akkoyun/B100/[AA]/Design Review/Telit/README.md

# B100<sup>AA</sup> Design Review

B100 is an open source (open hardware) GSM IoT module. B100 use Telit GE910 GSM modem in communication layer. All hardware is reviewed by manufacturer such as Telit. In this folder all review version files and design review reports are published.

## Review Time Line

**Telit**

| Review Date | Review Version | Review Link |
|---|---|---|
| 11.01.2021  | Schematic R1 | [Telit DR33285 R1](https://github.com/akkoyun/B100/blob/01.00.00/%5BAA%5D/Design%20Review/Telit/Review%201/Design%20Review/DR33285%20v1.pdf) |
| 18.01.2021  | Schematic R2 | [Telit DR33285 R2](https://github.com/akkoyun/B100/blob/01.00.00/%5BAA%5D/Design%20Review/Telit/Review%202/Design%20Review/DR33285%20v2.pdf) |
| 21.01.2021  | Schematic R3 | [Telit DR33285 R3](https://github.com/akkoyun/B100/blob/01.00.00/%5BAA%5D/Design%20Review/Telit/Review%203/Design%20Review/DR33285%20v3.pdf) |
| 28.01.2021  | Schematic R4 | [Telit DR33285 R4](https://github.com/akkoyun/B100/blob/01.00.00/%5BAA%5D/Design%20Review/Telit/Review%204/Design%20Review/DR33285%20v4.pdf) |
| 01.02.2021  | PCB R1 | [Telit DR33285 R5](https://github.com/akkoyun/B100/blob/01.00.00/%5BAA%5D/Design%20Review/Telit/Review%205/Design%20Review/DR33285%20v5.pdf) |
| 11.02.2021  | PCB R2 | [Telit DR33285 R6](https://github.com/akkoyun/B100/blob/01.00.00/%5BAA%5D/Design%20Review/Telit/Review%206/Design%20Review/DR33285%20v6.pdf) |
| | PCB R3 | Telit DR33285 R7 |
