akkoyun/B100/[AA]/Documentation/MCU Pin Map/README.md

# B100<sup>AA</sup> Socket Pin Map

## Power

### VCC

Pin number : A1, A60, B1, B60

Pin description : VCC power line is a main feed for B100AA
