akkoyun/B100/[AA]/Production/Mechanical/2D/README.md

# B100<sup>AA</sup>

* Çift yönlü komponent yerleşimi olacaktır.
* Low profile çift satır headerlar ile pin aktarımı yapılacaktır.
* köşelerde delikleri olacaktır.
*
