akkoyun/B100/[AA]/Design Review/Telit/Review 3/Design Review/DR33285 v3.pdf

Application Engineering

Design review report

Code: | AE-33285
Rev: | 3
Date: | 2021-01-21
Page: | 1/ 8

The electronic version of this document is the latest version. It is the responsibility of the individual to ensure that any paper material is the current version. Printed material is uncontrolled documentation

Documentazione riservata. Questo documento non può essere riprodotto, anche

parzialmente, né reso noto a terzi senza preventiva autorizzazione scritta diTelit Communications S.p.A.

Tutti i diritti sono tutelati a norma di legge.

Mod. 0313 08/2015 Rev.4

Approval: | Global Application Engineering Manager Massimiliano Lonzar
Approval: | Design Services Manager Fabio Deperini, Prashanth Reddy
Author: | Technical Support Engineer Alessandro Littarru, Chandra Shekar N, Harinadha Reddy C

DISCLAIMER

The contents are confidential and any disclosure to persons other than the officers, employees, agents or subcontractors of the owner or licensee of this document, without the prior written consent of Telit, is strictly prohibited. Telit makes every effort to ensure the quality of the information it makes available. Notwithstanding the foregoing, Telit does not make any warranty as to the information contained herein, and does not accept any liability for any injury, loss or damage of any kind incurred by use of or reliance upon the information. Telit disclaims any and all responsibility for the application of the devices characterized in this document, and notes that the application of the device must comply with the safety standards of the applicable country, and where applicable, with the relevant wiring rules.

All rights reserved.
© 2006-2021 Telit Communications S.p.A.

Restricted document. No part of this document can be reproduced or copied in any format, in part or totally,

nor its contents revealed in any manner to others without the express written permission of Telit Communications S.p.A.

All rights reserved.

Design review report

Date: | 2021-01-21
Page: | 2/ 8

Documentazione riservata. Questo documento non può essere riprodotto, anche

parzialmente, né reso noto a terzi senza preventiva autorizzazione scritta diTelit Communications S.p.A.

Tutti i diritti sono tutelati a norma di legge.

Contents

Design review report

Date: | 2021-01-21
Page: | 3/ 8

Documentazione riservata. Questo documento non può essere riprodotto, anche

parzialmente, né reso noto a terzi senza preventiva autorizzazione scritta diTelit Communications S.p.A.

Tutti i diritti sono tutelati a norma di legge.

### 1. Scope

Aim of this document is to describe suggestions and corrections that Telit advises to improve Ovoo Electronics B100AA application that integrates Telit GE910-QUAD V3 and BlueMod S50 modules.

### 2. Design review

Design review is based on the following received documentation:
- Schematic files: B151BA-R2.PDF, B100AA-R3.PDF
- Gerber file: none.
- Other: Telit Design Review R03 (Schematic).PDF Summary Tables:
Schematic Review | P F I MI N/A
Power Supply | Ѵ
SIM Pins | Ѵ
Digital Pins | | Ѵ
Audio | | | | Ѵ
RF | | | Ѵ
PCB Layout Review | P F I MI N/A
General Placement | | Ѵ
Antenna Waveguide | | Ѵ
RF Aspects | | Ѵ
Audio Aspects | | Ѵ

P: Pass; F: Fail; I: Improvements possible; MI: Missing Information; N/A: Not Applicable

The following symbols will be used throughout the Design Review to indicate:

✓ OK: No design changes are required.

Tip: information or possible improvement, not mandatory but recommended.

Warning: if you don’t follow the recommendation there’s a risk of malfunctioning or issues during the homologation phase, strongly recommended.

Error: it’s mandatory to follow the recommendation otherwise the module could be damaged or could not work properly or there’s high probability of facing issues during the homologation phase.

? Missing Information: some relevant information is missing therefore the DR cannot be accurate on this item.

Design review report

Date: | 2021-01-21
Page: | 4/ 8

Documentazione riservata. Questo documento non può essere riprodotto, anche

parzialmente, né reso noto a terzi senza preventiva autorizzazione scritta diTelit Communications S.p.A.

Tutti i diritti sono tutelati a norma di legge.

### 2.1. Schematic review

2.1.1. Power supply

Ѵ Ok.

2.1.2. SIM pins

Ѵ Ok.

2.1.3. Digital pins

We strongly suggest replacing Q3 NPN transistor with a PNP transistor and tying its emitter to VMCU. Furthermore, resistors R25, R26, R27 must be properly sized considering current rating for D1 LEDs. Suitable values are 65Ohm for R25-R26 and 22 Ohm for R27. Add proper series resistor (5-10KOhm) on Q4, Q5 and Q6 bases.

Kindly make sure the BlueMod+S50 UART lines are connected to HOST MCU as shown below,

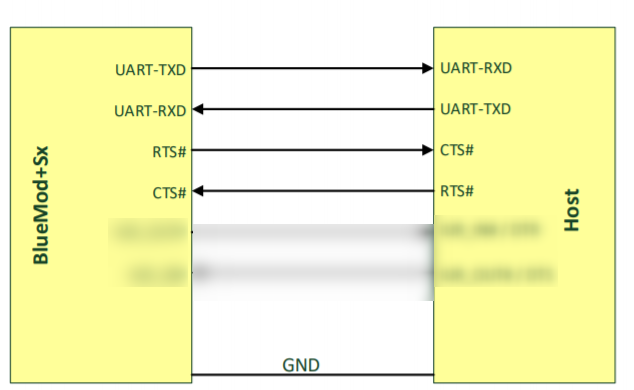
[picture p13: figure]

We recommend placing test points for BOOT0 pin, UART-RXD, UART-TXD, UART-RTS# and UART-CTS#. This will be useful for Regulatory approval purpose.

Test mode# Pin | BOOT0 Pin | Mode
LOW | LOW | Test mode (38400, 8N1)
LOW | HIGH | DTM (19200, 8N1)
HIGH | LOW | Firmware (115200, 8N1)
HIGH | HIGH | Bootloader

For more details on Test Mode, refer BlueMod+S50 HUG section 4.8.

Design review report

Date: | 2021-01-21
Page: | 5/ 8

Documentazione riservata. Questo documento non può essere riprodotto, anche

parzialmente, né reso noto a terzi senza preventiva autorizzazione scritta diTelit Communications S.p.A.

Tutti i diritti sono tutelati a norma di legge.

2.1.4. Audio pins
✓ N.A.
2.1.5. RF aspects

? Looks the current design is using BlueMod+S50_AP variant. Antenna part number is missing in the schematics.

### 2.2. PCB Layout review

We don’t have the PCB gerbers yet, but we will give you anyhow some useful general suggestions.

2.2.1. General placement

As a general rule we suggest predisposing your PCB to optionally mount a metallic shield on top of noisy components (fast digital components, MCU, memories). This is a must in case of switching components, rectifiers and power amplifiers. For this purpose, components must be packet into well-defined areas surrounded with ground pads where you can eventually solder the shield. The shield options can be used, when needed, to suppress EMI fields that may interfere with the cellular reception/emission.

Be aware that all PCBs placed close to GSM antenna must be RF proof and not only the PCB mounting the module; this means that all the PCB placed less than 30cm from the antenna must have shields over the noisiest components (switching, MCU, RAM, Ethernet PHY, etc..) and with the top and bottom layers mostly ground planes.

2.2.2. RF aspects

The position of the external antenna with respect to other boards is of maximum importance, since conductive planes close to antenna modify the impedance sees by the antenna and any board of the system must be RF proof, not only the modem board.

Move components, tracks, vias and connectors away from antenna area to reduce their coupling with RF signal; you can also bury tracks in the inner layers of a multi-layer PCB.

We strongly suggest complying the following build-up and routing general rules for best RF performances (high RF receiver sensitivity, low spurious emissions) and also for best thermal behavior:

o We advise using at least 4 layers PCB.

Design review report

Date: | 2021-01-21
Page: | 6/ 8

Documentazione riservata. Questo documento non può essere riprodotto, anche

parzialmente, né reso noto a terzi senza preventiva autorizzazione scritta diTelit Communications S.p.A.

Tutti i diritti sono tutelati a norma di legge.

o Top and Bottom layers should be mainly a ground plane interrupted just by component’s pads, VIAs and RF antenna waveguide; just the minimum possible portion of tracks should be routed in these layers.
o Inner layers should be used for interconnections and power planes; all empty spaces should be filled with GND.
o All grounds, either planes or areas, in an all layers, must be well connected with each other, using large tracks and many conductive VIAs, in order to guarantee a strong equipotential node.
o PCB borders should be GND in all layers, wherever is possible. We suggest adding a series of conductive VIAs evenly distributed (e.g. every 2mm) all along the board edges, inside the border GND area.
o Noisy components should be shielded into a metallic shield if required.

The Bypass capacitors must be placed close to the Telit modem’s power input pads or at least on the same path. In case of switching power supply another Bypass low ESR capacitor must be placed close to the inductor output to cut the ripple.

It is not advisable to route analog or digital audio lines, memory address and data bus, fast digital signals, clocks, quartz, serial, USB and long signal tracks on an outer layer. It’ll be better to bury it on an inner layer with a ground plane under and above it to shield the signal from RF and crosstalk, see figure below. USB data lines should be Differential Offset Coplanar Waveguide with 90 Ohms characteristic impedance.

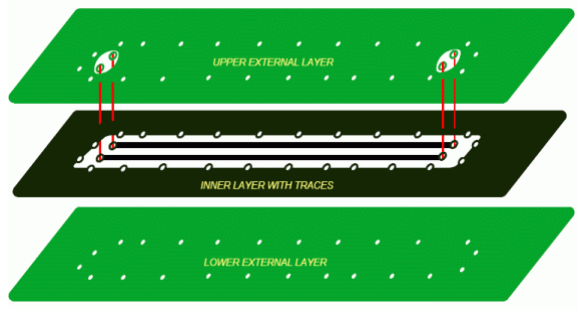
[picture p14: figure]

The RF antenna track, and eventually any via connected to it, must be a homogeneous waveguide with 50 Ohm characteristic impedance; we suggest using the coplanar waveguide with ground model where the RF track has a uniform ground plane underneath and surrounding it as in figure below. Do not place signal lines and signal-VIAs crossing or close to RF lines in no one of waveguide’s layers involved.

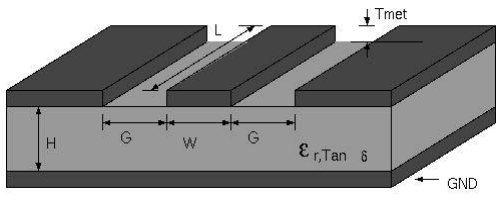
[picture p15: figure]

Design review report

Date: | 2021-01-21
Page: | 7/ 8

Documentazione riservata. Questo documento non può essere riprodotto, anche

parzialmente, né reso noto a terzi senza preventiva autorizzazione scritta diTelit Communications S.p.A.

Tutti i diritti sono tutelati a norma di legge.

When dielectric between 2 consecutive layers has not the desired height then for right impedance realization, you should remove the copper under RF line or pad, in one or more layers, to wider dielectric between antenna track and its reference ground plane, as example in figure below. The clearance in the internal layers must be wider than the W+2G. This is to avoid electric filed to close in internal layers instead of in the desired reference ground layer.

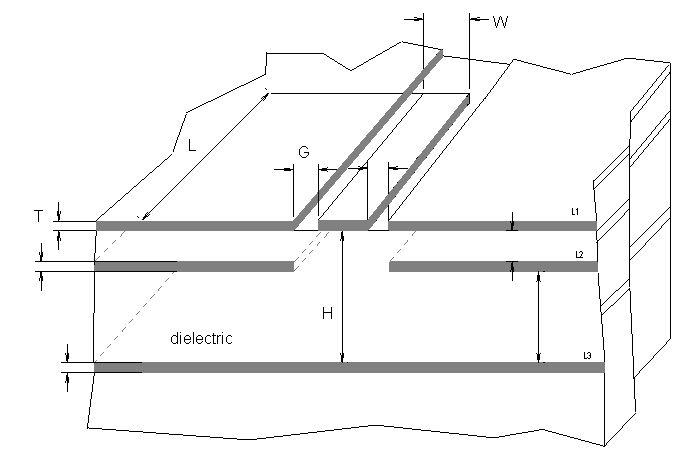
[picture p16: figure]

We suggest shielding the waveguide by adding a series of conductive VIAs evenly distributed (e.g. every 2mm) all along the edges of the GND plane facing the coplanar waveguide (about 1mm from the edge), both sides. (see figure below). This improve line grounding and reduce signal coupling inside the PCB from adjacent tracks.

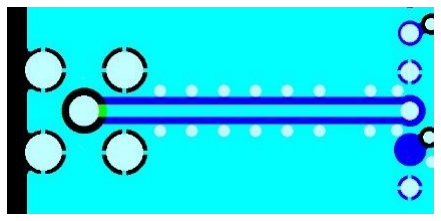
[picture p17: figure]

If applicable, route RF matching network using as short as possible tracks and avoiding stubs, sharp bends and meanders.
Figure below represents a layout example of the RF line matching network circuitry.

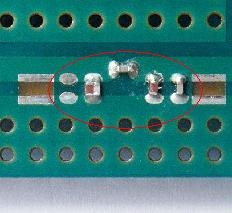
[picture p18: figure]

### 2.3. General comments

Please check and follow Telit Modem Integration Design Guide.
Review is related to received application information and the supposed use of it.

Design review report

Date: | 2021-01-21
Page: | 8/ 8

Documentazione riservata. Questo documento non può essere riprodotto, anche

parzialmente, né reso noto a terzi senza preventiva autorizzazione scritta diTelit Communications S.p.A.

Tutti i diritti sono tutelati a norma di legge.

### 3. Quality record

This design review is registered internally in Bugzilla with ID #33285.
The customer request is registered internally in Salesforce with ID # 00201737.
