akkoyun/B100/[AA]/Documentation/Block Diagram/PDF/FOTA.pdf

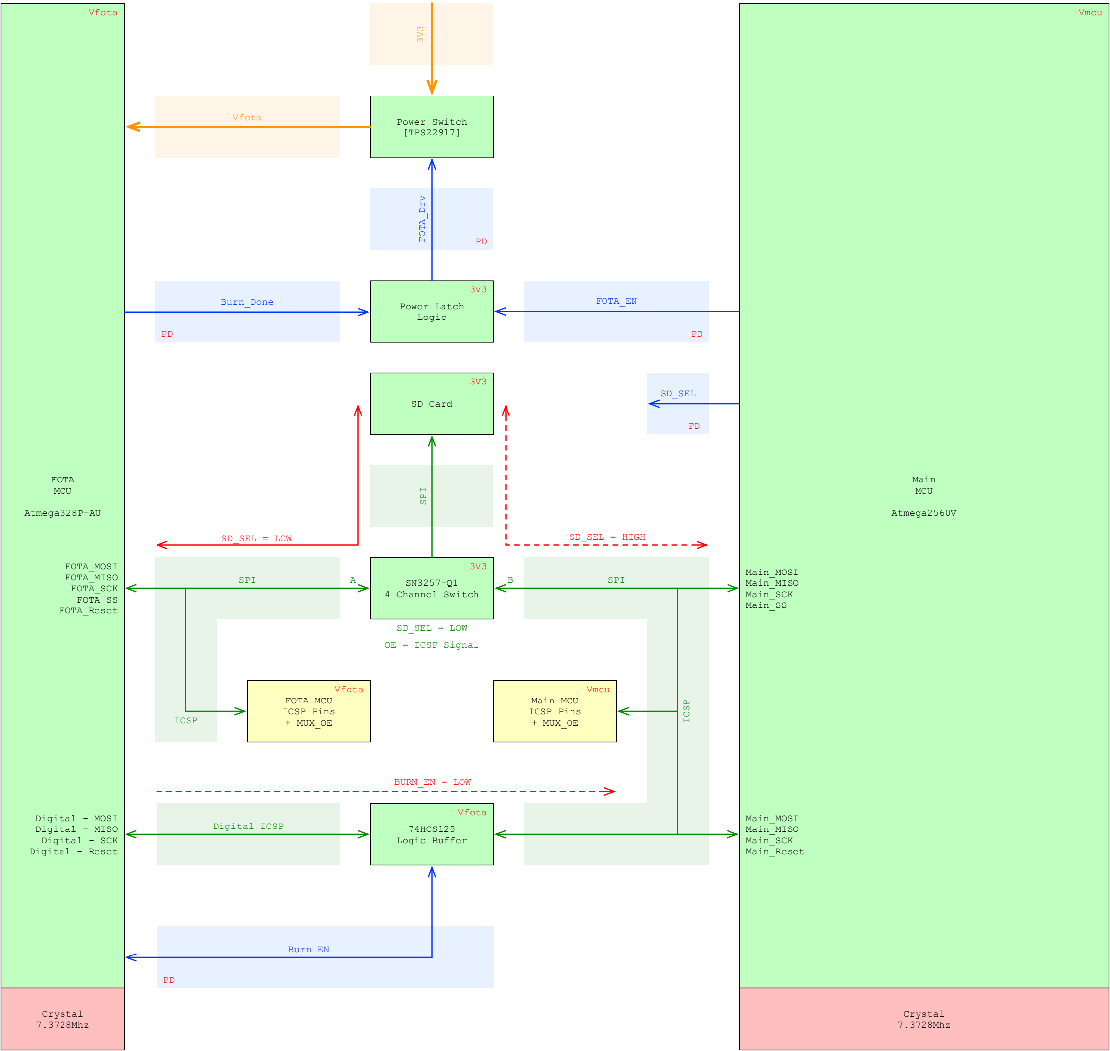
[picture p19: figure]
FOTA MCU; Atmega328P-AU; Crystal 7.3728Mhz; FOTA_EN Power Latch; Logic FOTA_Drv; SD Card; SPI; Main MCU ICSP Pins + MUX_OE; ICSP; FOTA MCU ICSP Pins; + MUX_OE; 74HCS125 Logic Buffer; Digital ICSP; Burn EN; Burn_Done; Power Switch [TPS22917]; Vfota; Main MCU; Atmega2560V; 4 Channel Switch SPI; SD_SEL = LOW; OE = ICSP Signal; SD_SEL; SD_SEL = HIGH; BURN_EN = LOW; Main_MOSI Main_MISO Main_SCK Main_SS; Main_MOSI Main_MISO Main_SCK Main_Reset; Digital - MOSI Digital - MISO Digital - SCK Digital - Reset; FOTA_MOSI FOTA_MISO FOTA_SCK FOTA_SS FOTA_Reset; Vmcu
