akkoyun/B100/[AA]/Documentation/Block Diagram/PDF/GSM.pdf

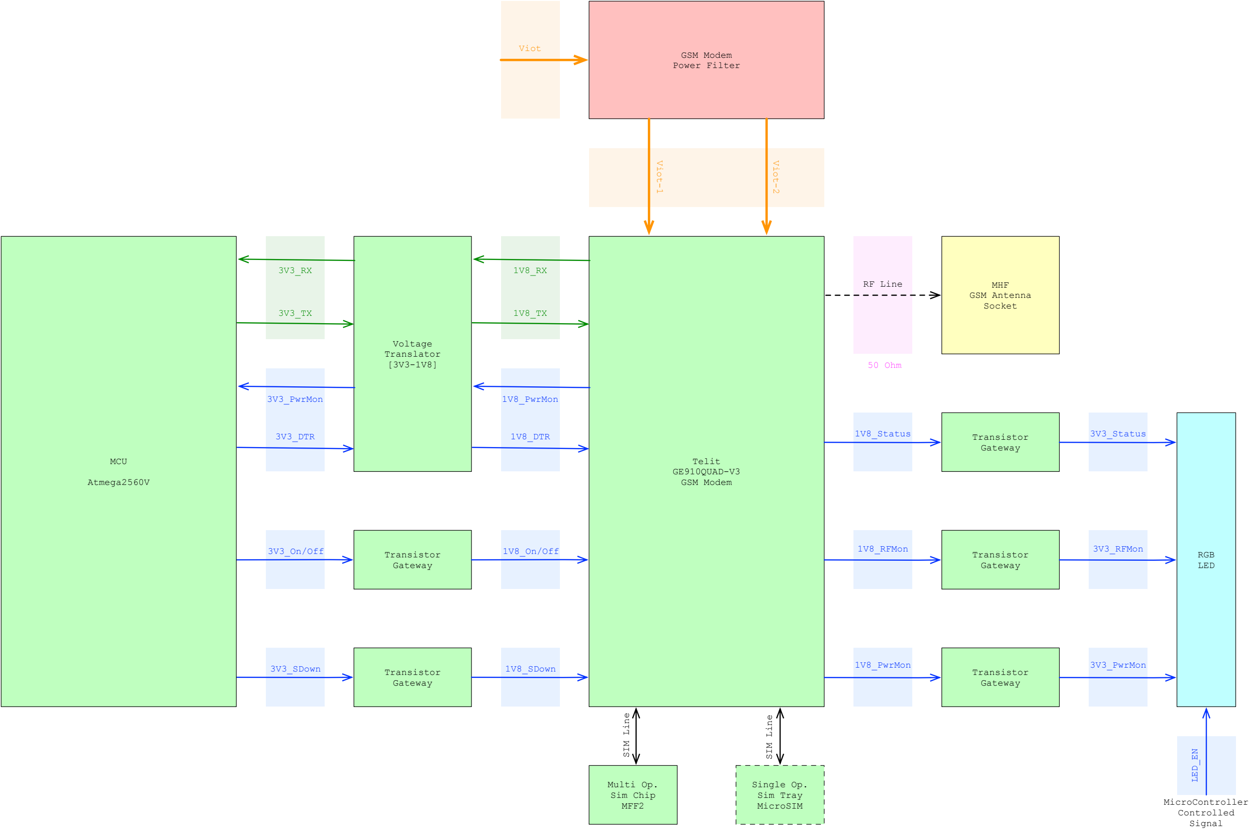
[picture p20: figure]
Telit GE910QUAD-V3 GSM Modem; MHF GSM Antenna Socket; RF Line; 50 Ohm; Multi Op. Sim Chip MFF2; Transistor Gateway; Voltage Translator [3V3-1V8]; Single Op. Sim Tray MicroSIM; SIM Line; 3V3_SDown; 3V3_On/Off; 3V3_DTR; 3V3_PwrMon; 1V8_SDown; 1V8_On/Off; 1V8_DTR; 1V8_PwrMon; GSM Modem Power Filter; Viot-1; Viot-2; MCU; Atmega2560V; 1V8_Status; 1V8_RFMon; RGB; LED; 3V3_Status; 3V3_RFMon; LED_EN; Viot; MicroController Controlled Signal
