akkoyun/B100/[AA]/Documentation/Block Diagram/PDF/I2C.pdf

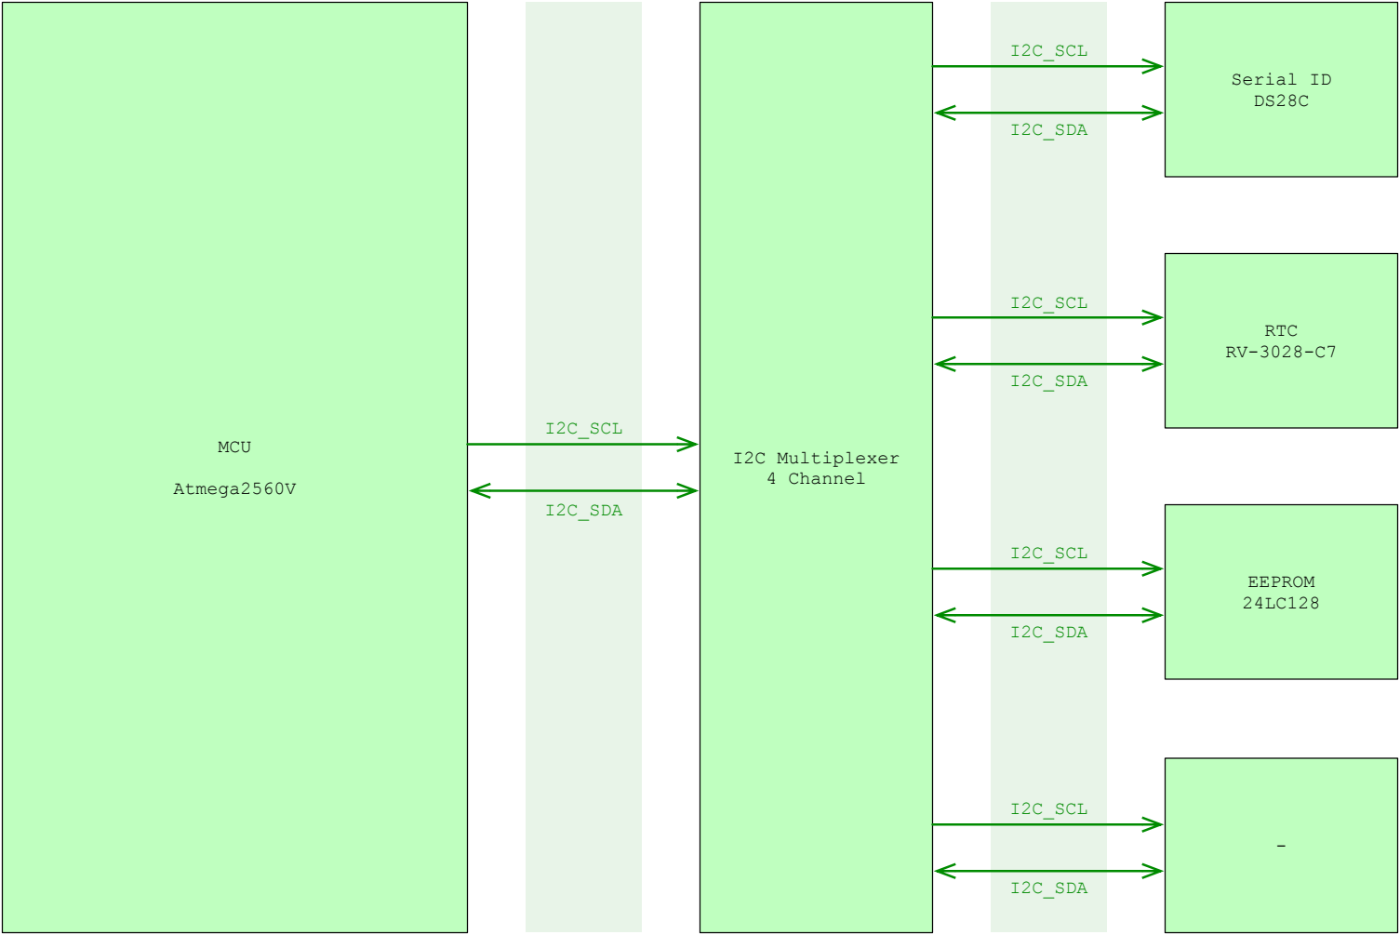
[picture p21: figure]
MCU; Atmega2560V; I2C Multiplexer 4 Channel; I2C_SCL; I2C_SDA; Serial ID DS28C; EEPROM 24LC128; RTC RV-3028-C7
