akkoyun/B100/[AA]/Documentation/Block Diagram/PDF/Power Architechture.pdf

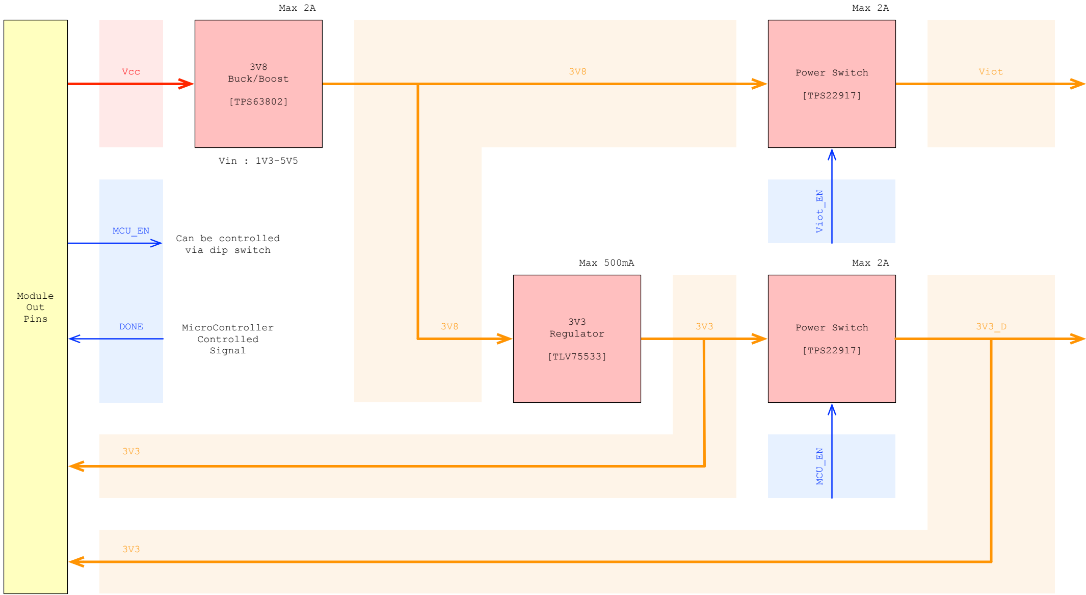
[picture p22: figure]
Viot; Viot_EN; Power Switch; [TPS22917]; Max 2A; MCU_EN; DONE; MicroController; Controlled Signal; Can be controlled; via dip switch; 3V3 Regulator; [TLV75533]; Max 500mA; Vcc; Buck/Boost; [TPS63802]; Vin : 1V3-5V5; Module Out Pins

Main Feed

Non Sleep
3V3

Sleep

Sleep
3V3

Awake
