akkoyun/B100/[AA]/Design Files/B100AA/PDNAnalyzer_Output/B100AA PCB R1/B100AA R4/Results-1/pins.csv

refdes | pin | voltage | current
J2 | 60 | 4.99608 | 1.96035
J2 | 1 | 4.99608 | 1.96035
J2 | 30 | 0.0 | -0.980174
J2 | 58 | 0.0 | -0.980174
J2 | 4 | 0.0 | -0.980174
J2 | 31 | 0.0 | -0.980174
J3 | 60 | 5.00105 | 0.0498376
J3 | 1 | 5.00105 | 0.0498376
J3 | 30 | 0.00114728 | -0.0249188
J3 | 58 | 0.00114728 | -0.0249188
J3 | 4 | 0.00114728 | -0.0249188
J3 | 31 | 0.00114728 | -0.0249188
U3 | 5 | 3.30041 | 0.570263
U3 | 2 | 0.000984424 | 0.018311999999999995
U21 | 6 | 3.80631 | 0.838579
U21 | 8 | 0.00533345 | 1.5902399999999999
U21 | 3 | 0.00533345 | 1.5902399999999999
U22 | 6 | 5.00037 | 0.00118532
U22 | 8 | 0.00093399 | 6.681600000000003e-05
U22 | 3 | 0.00093399 | 6.681600000000003e-05
U4 | M01 | 3.68575 | -0.0625243
U4 | M02 | 3.6856 | -0.0624757
U4 | R02 | 0.00120282 | 0.006576820000000001
U4 | R04 | 0.00120904 | 0.00657371
U4 | R03 | 0.00120689 | 0.00657478
U4 | P03 | 0.00120897 | 0.00657374
U4 | P04 | 0.0012106 | 0.0065729199999999995
U4 | N03 | 0.00120922 | 0.0065736200000000005
U4 | R05 | 0.00120848 | 0.00657398
U4 | R06 | 0.00120578 | 0.006575340000000001
U4 | P05 | 0.00120975 | 0.00657335
U4 | R08 | 0.00119816 | 0.0065791700000000005
U4 | N05 | 0.00120839 | 0.00657403
U4 | P06 | 0.00120632 | 0.006575070000000001
U4 | N04 | 0.00121003 | 0.0065732099999999995
U4 | N06 | 0.00120453 | 0.00657597
U4 | L01 | 0.00119847 | 0.006579
U4 | L02 | 0.00120268 | 0.0065769
U4 | J01 | 0.00119821 | 0.006579140000000001
U4 | K02 | 0.00120285 | 0.006576810000000001
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
R70 | 1 | 0.00105438 | 4.65955e-06
U1 | 1 | 3.72176 | -0.25
U1 | 6 | 3.69676 | 0.25
FB1 | 1 | 3.69548 | -0.125
FB1 | 2 | 3.68986 | 0.125
FB2 | 1 | 3.69559 | -0.125
FB2 | 2 | 3.68997 | 0.125
U2 | 1 | 3.28963 | -0.570163
U2 | 6 | 3.20981 | 0.570163
U10 | 1 | 3.16295 | -0.0790108
U10 | 6 | 3.15188 | 0.0790108
