akkoyun/B100/[AA]/Design Files/B100AA Development Kit/Output/BOM/B100DEV BOM.numbers/Data/Bottom-small-36.png

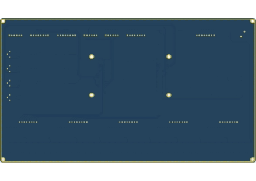
[AA]/Design Files/B100AA Development Kit/Output/BOM/B100DEV BOM.numbers/Data/Bottom-small-36.png
