akkoyun/B100/[AA]/Design Files/B100AA Development Kit/Output/BOM/B100DEV BOM.numbers/Data/Ekran Resmi 2021-02-23 10.48.27-31.png

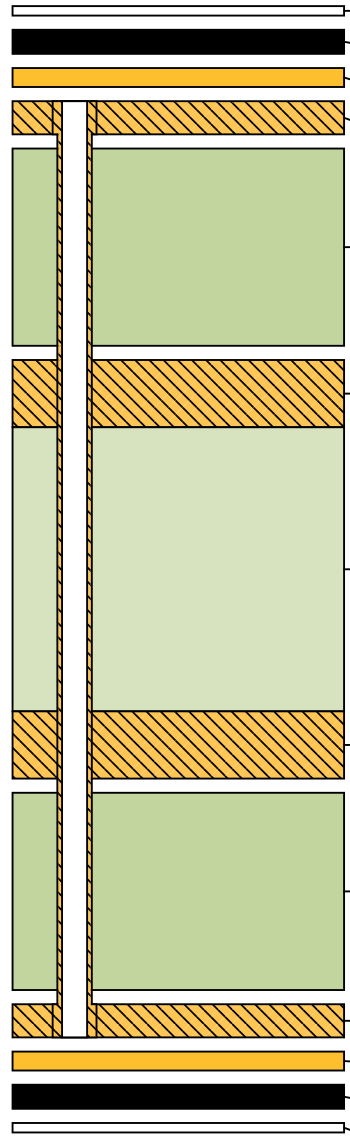
[AA]/Design Files/B100AA Development Kit/Output/BOM/B100DEV BOM.numbers/Data/Ekran Resmi 2021-02-23 10.48.27-31.png
