akkoyun/B100/[AA]/Design Files/B100AA Development Kit/Output/BOM/B100DEV BOM.numbers/Data/Top-small-34.png

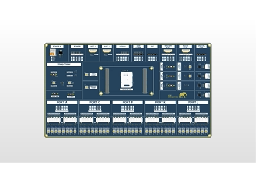
[AA]/Design Files/B100AA Development Kit/Output/BOM/B100DEV BOM.numbers/Data/Top-small-34.png
