akkoyun/B100/[AA]/Design Files/B100AA Development Kit/Output/BOM/B100DEV BOM.numbers/Data/Twitter_Profile-15.jpg

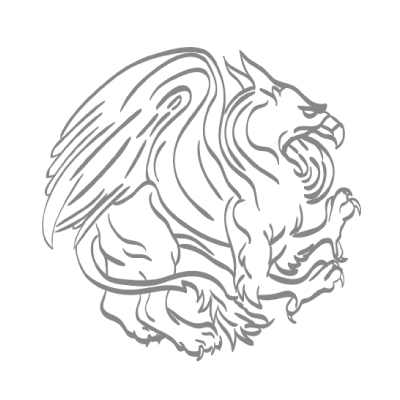
[AA]/Design Files/B100AA Development Kit/Output/BOM/B100DEV BOM.numbers/Data/Twitter_Profile-15.jpg
