akkoyun/B100/[AA]/Design Files/B100AA Development Kit/Output/BOM/B100DEV BOM.numbers/preview-web.jpg

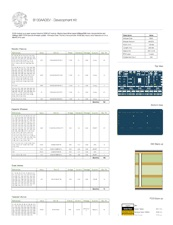
[AA]/Design Files/B100AA Development Kit/Output/BOM/B100DEV BOM.numbers/preview-web.jpg
