akkoyun/B100/[AA]/Production/BOM/B100 BOM.numbers/Data/B100AAR1-2-21.png

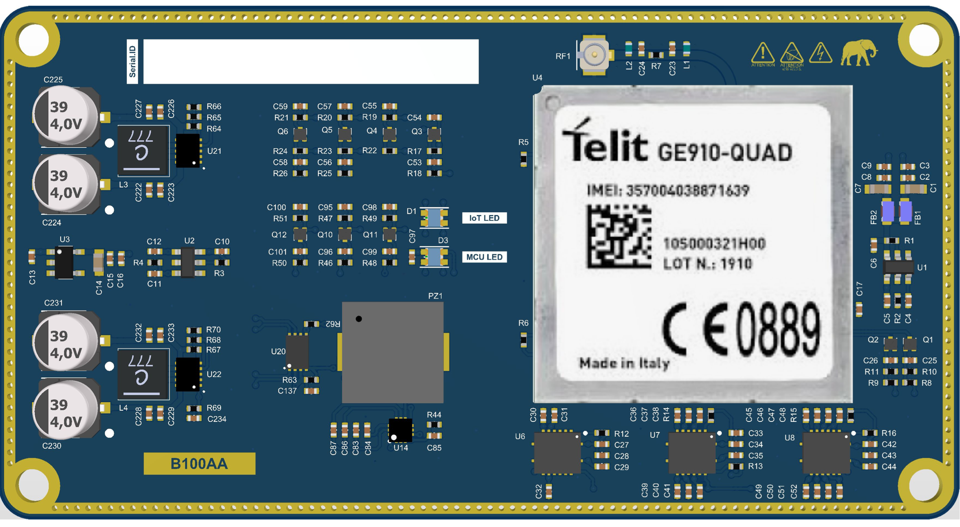
[AA]/Production/BOM/B100 BOM.numbers/Data/B100AAR1-2-21.png
