akkoyun/B100/[AA]/Production/BOM/B100 BOM.numbers/Data/B100AAR1-3-small-24.png

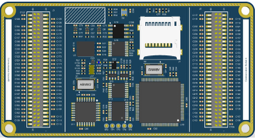
[AA]/Production/BOM/B100 BOM.numbers/Data/B100AAR1-3-small-24.png
