akkoyun/B100/[AA]/Production/BOM/B100 BOM.numbers/Data/Ekran Resmi 2021-02-22 10.55-26.png

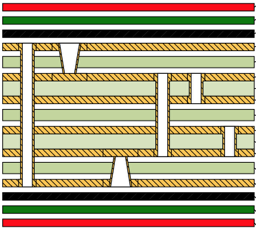
[AA]/Production/BOM/B100 BOM.numbers/Data/Ekran Resmi 2021-02-22 10.55-26.png
