akkoyun/B100/[AA]/Design Files/B100AA/PDNAnalyzer_Output/B100AA PCB R1/B100AA R4/Results-0/vias.csv

x | y | layer1 | layer2 | voltage1 | voltage2 | current
-71.7804 | 71.7804 | TOP_LAYER | MID_LAYER_1 | 9.35697e-05 | 9.35042e-05 | 0.000829525
-71.7804 | 71.7804 | MID_LAYER_1 | MID_LAYER_2 | 9.35042e-05 | 9.29126e-05 | 0.00124602
-71.7804 | 71.7804 | MID_LAYER_2 | MID_LAYER_3 | 9.29126e-05 | 9.27739e-05 | 0.00138319
-71.7804 | 71.7804 | MID_LAYER_3 | MID_LAYER_4 | 9.27739e-05 | 9.20634e-05 | 0.00149662
-71.7804 | 71.7804 | MID_LAYER_4 | BOTTOM_LAYER | 9.20634e-05 | 9.19523e-05 | 0.0014064
-71.7804 | 111.151 | TOP_LAYER | MID_LAYER_1 | 9.36627e-05 | 9.35968e-05 | 0.000833973
-71.7804 | 111.151 | MID_LAYER_1 | MID_LAYER_2 | 9.35968e-05 | 9.30031e-05 | 0.00125071
-71.7804 | 111.151 | MID_LAYER_2 | MID_LAYER_3 | 9.30031e-05 | 9.28624e-05 | 0.00140177
-71.7804 | 111.151 | MID_LAYER_3 | MID_LAYER_4 | 9.28624e-05 | 9.21452e-05 | 0.00151096
-71.7804 | 111.151 | MID_LAYER_4 | BOTTOM_LAYER | 9.21452e-05 | 9.204e-05 | 0.0013308
-71.7804 | 150.521 | TOP_LAYER | MID_LAYER_1 | 9.38054e-05 | 9.37389e-05 | 0.000841629
-71.7804 | 150.521 | MID_LAYER_1 | MID_LAYER_2 | 9.37389e-05 | 9.31395e-05 | 0.00126267
-71.7804 | 150.521 | MID_LAYER_2 | MID_LAYER_3 | 9.31395e-05 | 9.2996e-05 | 0.00143057
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
