akkoyun/B100/[AA]/Design Files/B100AA/PDNAnalyzer_Output/B100AA PCB R1/B100AA R4/Results-0/vpins.csv

refdes | pin | voltage | current | rpin
VCOMP0 | VCOMP0-0 | 4.99955 | 0.223612 | 0
VCOMP0 | VCOMP0-1 | 4.99955 | 0.223612 | 0
VCOMP0 | VCOMP0-2 | 0 | -0.111806 | 0
VCOMP0 | VCOMP0-3 | 0 | -0.111806 | 0
VCOMP0 | VCOMP0-4 | 0 | -0.111806 | 0
VCOMP0 | VCOMP0-5 | 0 | -0.111806 | 0
VCOMP1 | VCOMP1-0 | 5.00024 | 0.00597292 | 0
VCOMP1 | VCOMP1-1 | 5.00024 | 0.00597292 | 0
VCOMP1 | VCOMP1-2 | 0.000247092 | -0.00298646 | 0
VCOMP1 | VCOMP1-3 | 0.000247092 | -0.00298646 | 0
VCOMP1 | VCOMP1-4 | 0.000247092 | -0.00298646 | 0
VCOMP1 | VCOMP1-5 | 0.000247092 | -0.00298646 | 0
VCOMP54 | VCOMP54-0 | 3.29955 | 0.570289 | 0
VCOMP54 | VCOMP54-1 | 0.000117524 | -0.570289 | 0
VCOMP56 | VCOMP56-0 | 3.7997 | 0.835247 | 0
VCOMP56 | VCOMP56-1 | -0.00037459 | -0.417624 | 0
VCOMP56 | VCOMP56-2 | -0.00037459 | -0.417624 | 0
VCOMP59 | VCOMP59-0 | 4.99899 | 0.00118523 | 0
VCOMP59 | VCOMP59-1 | 0.000116946 | -0.000592617 | 0
VCOMP59 | VCOMP59-2 | 0.000116946 | -0.000592617 | 0
VCOMP2 | VCOMP2-0 | 3.67916 | -0.0625225 | 3.04
VCOMP2 | VCOMP2-1 | 3.67902 | -0.0624775 | 3.04
VCOMP2 | VCOMP2-2 | 0.00027662 | 0.00328658 | 3.04
VCOMP2 | VCOMP2-3 | 0.000282598 | 0.00328461 | 3.04
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
