akkoyun/B100/[AA]/Design Review/Telit/Review 5/Request Form/B151BA-R2.PDF

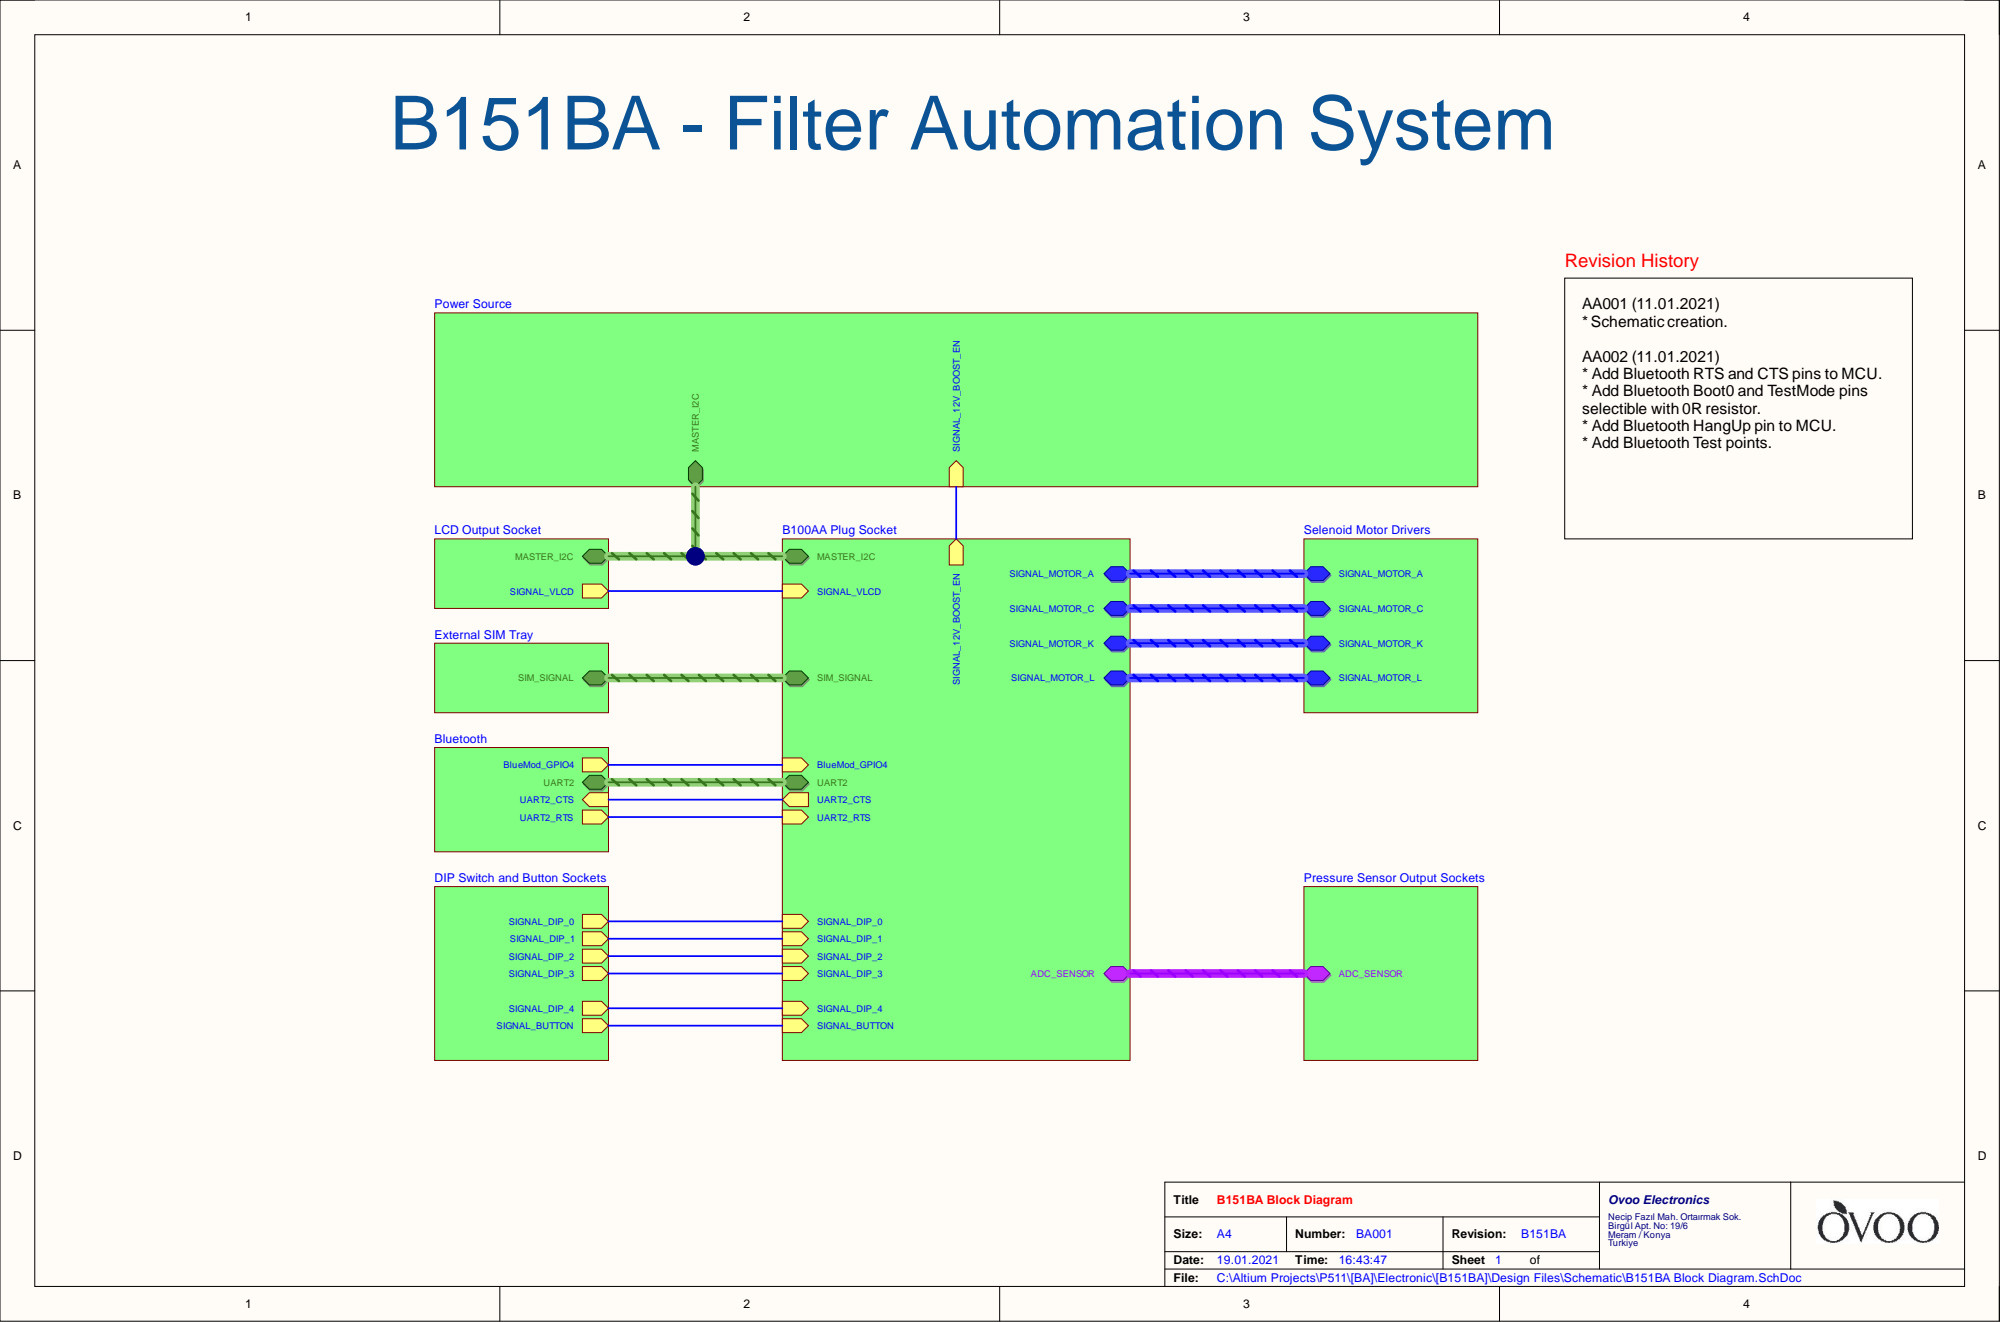
[picture p182: page 1]

* Add Bluetooth RTS and CTS pins to MCU.
* Add Bluetooth Boot0 and TestMode pins
selectible with 0R resistor.
* Add Bluetooth HangUp pin to MCU.
* Add Bluetooth Test points.

DIP Switch and Button Sockets

Pressure Sensor Output Sockets

Necip Fazıl Mah. Ortaırmak Sok. Birgül Apt. No: 19/6 Meram / Konya Turkiye

C:\Altium Projects\P511\[BA]\Electronic\[B151BA]\Design Files\Schematic\B151BA Block Diagram.SchDoc

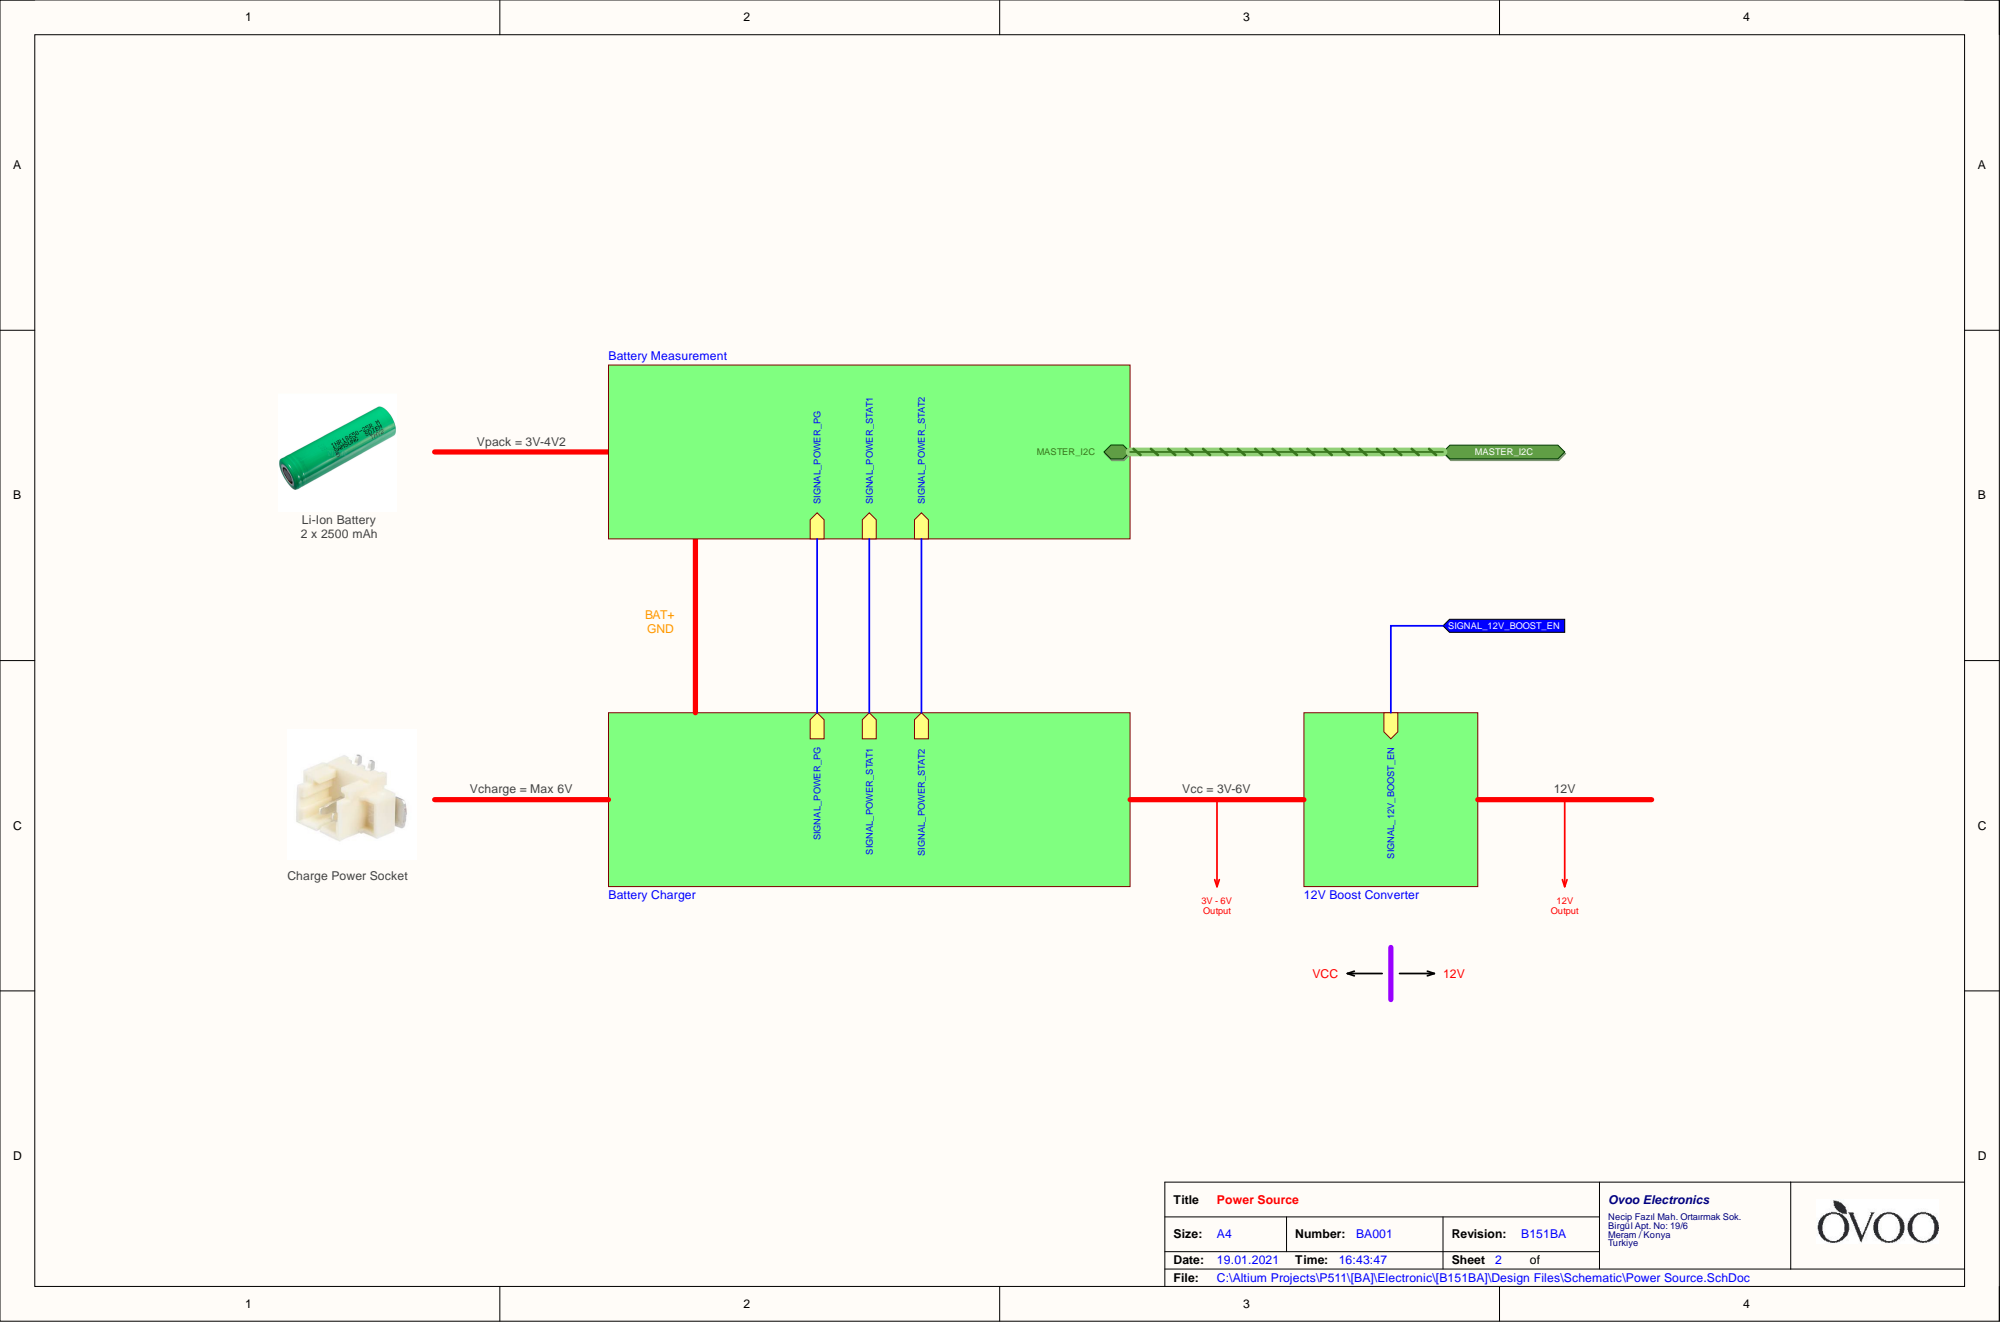
[picture p183: page 2]

C:\Altium Projects\P511\[BA]\Electronic\[B151BA]\Design Files\Schematic\Power Source.SchDoc

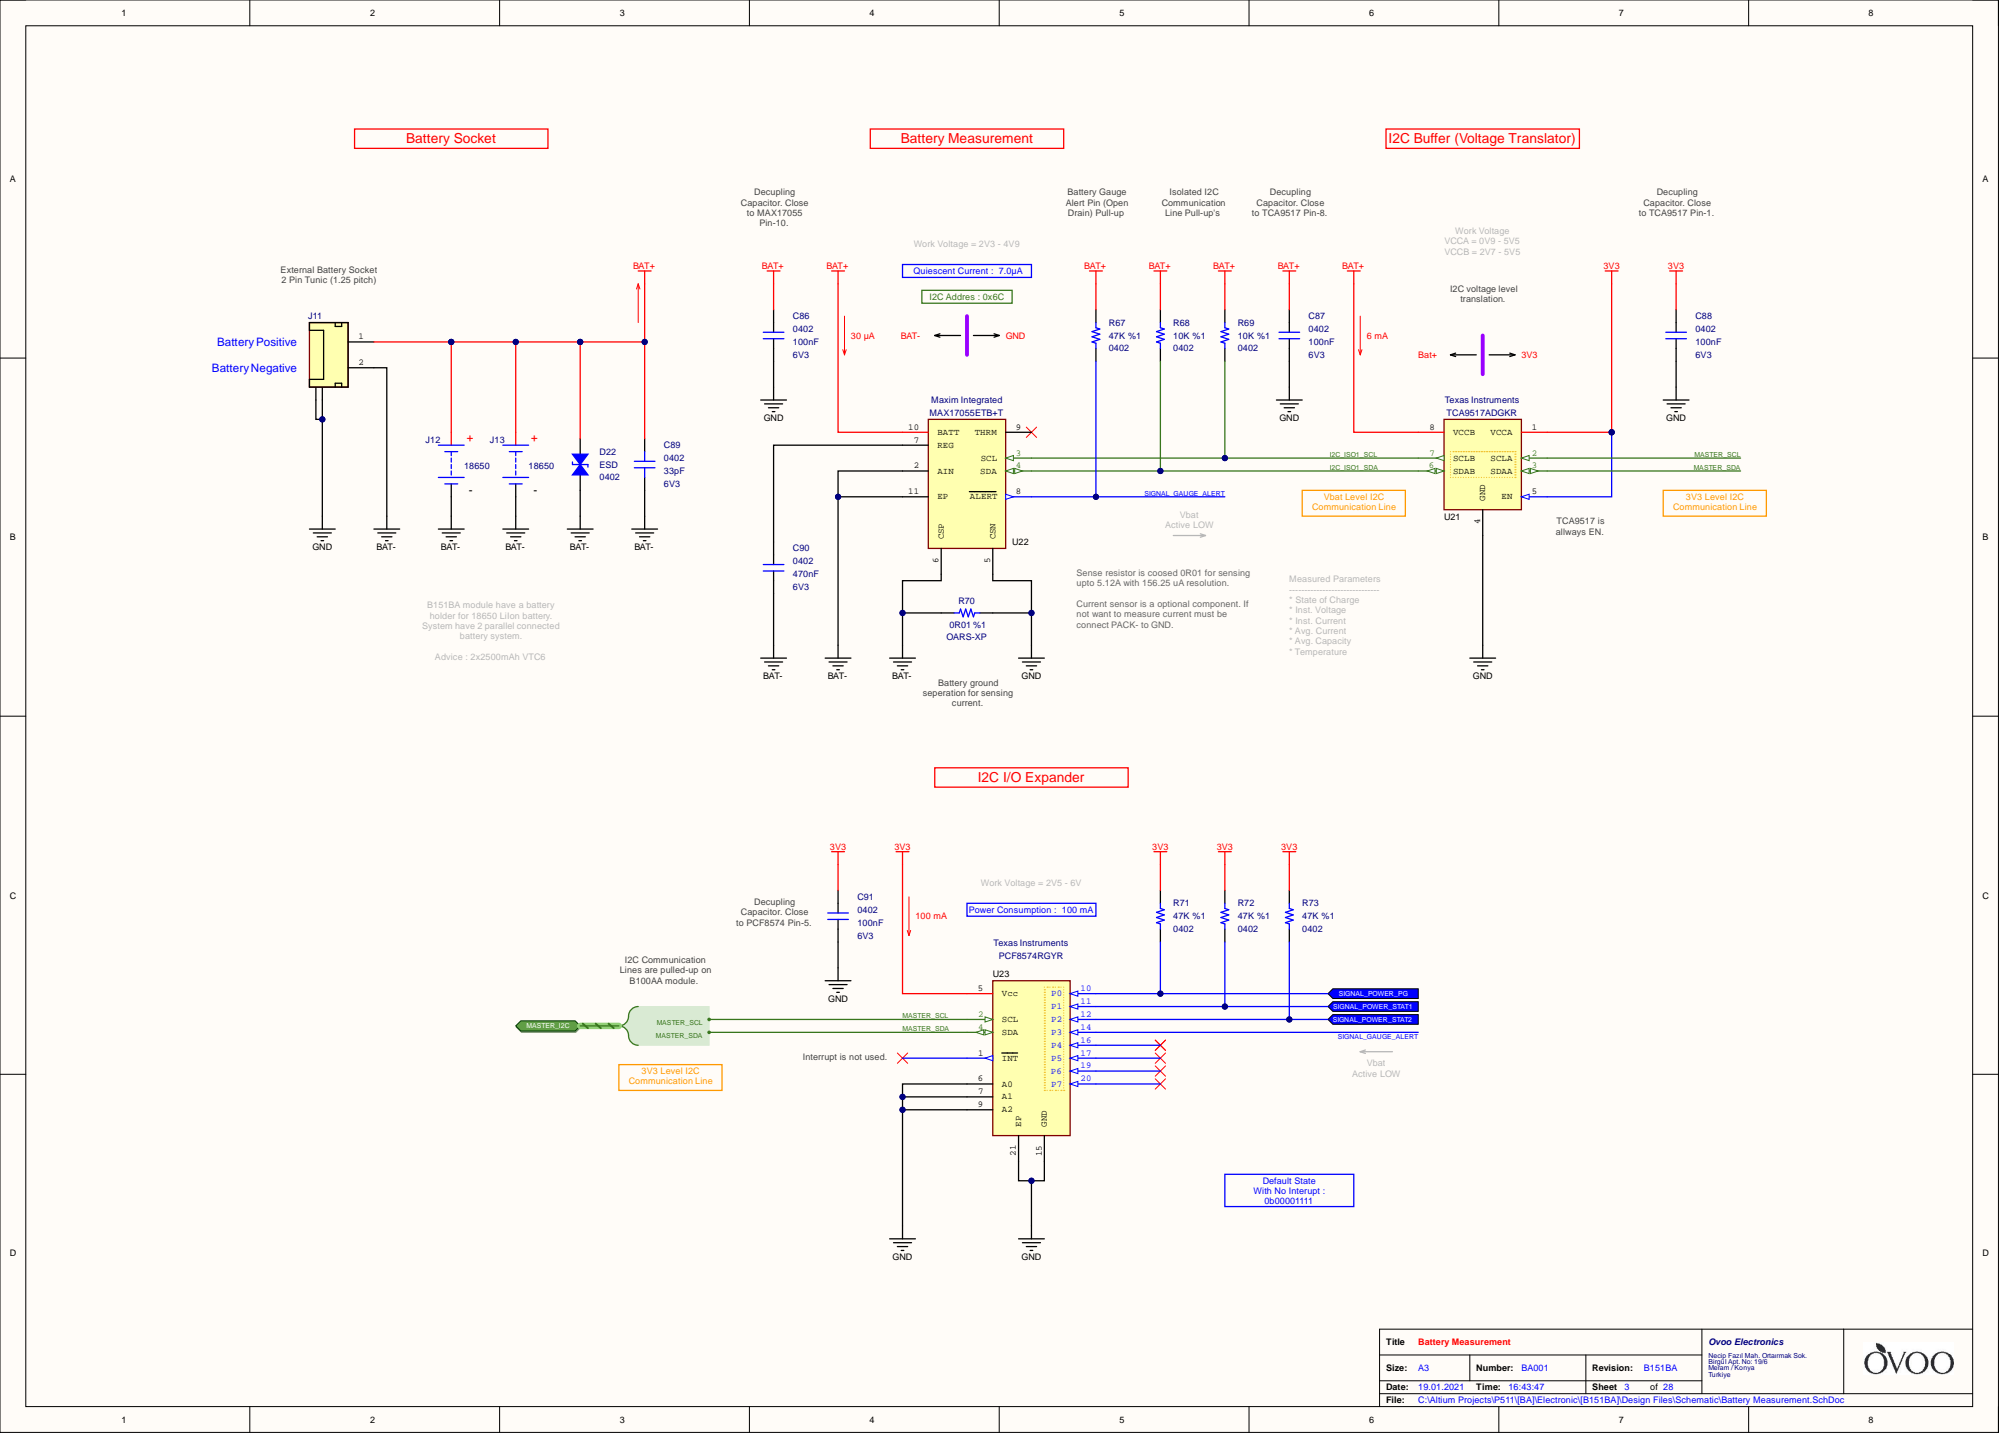
[picture p184: page 3]

Sense resistor is coosed 0R01 for sensing
upto 5.12A with 156.25 uA resolution.

B151BA module have a battery
holder for 18650 LiIon battery.
System have 2 parallel connected

Current sensor is a optional component. If
not want to measure current must be
connect PACK- to GND.

I2C Communication
Lines are pulled-up on
B100AA module.

Interrupt is not used.

C:\Altium Projects\P511\[BA]\Electronic\[B151BA]\Design Files\Schematic\Battery Measurement.SchDoc

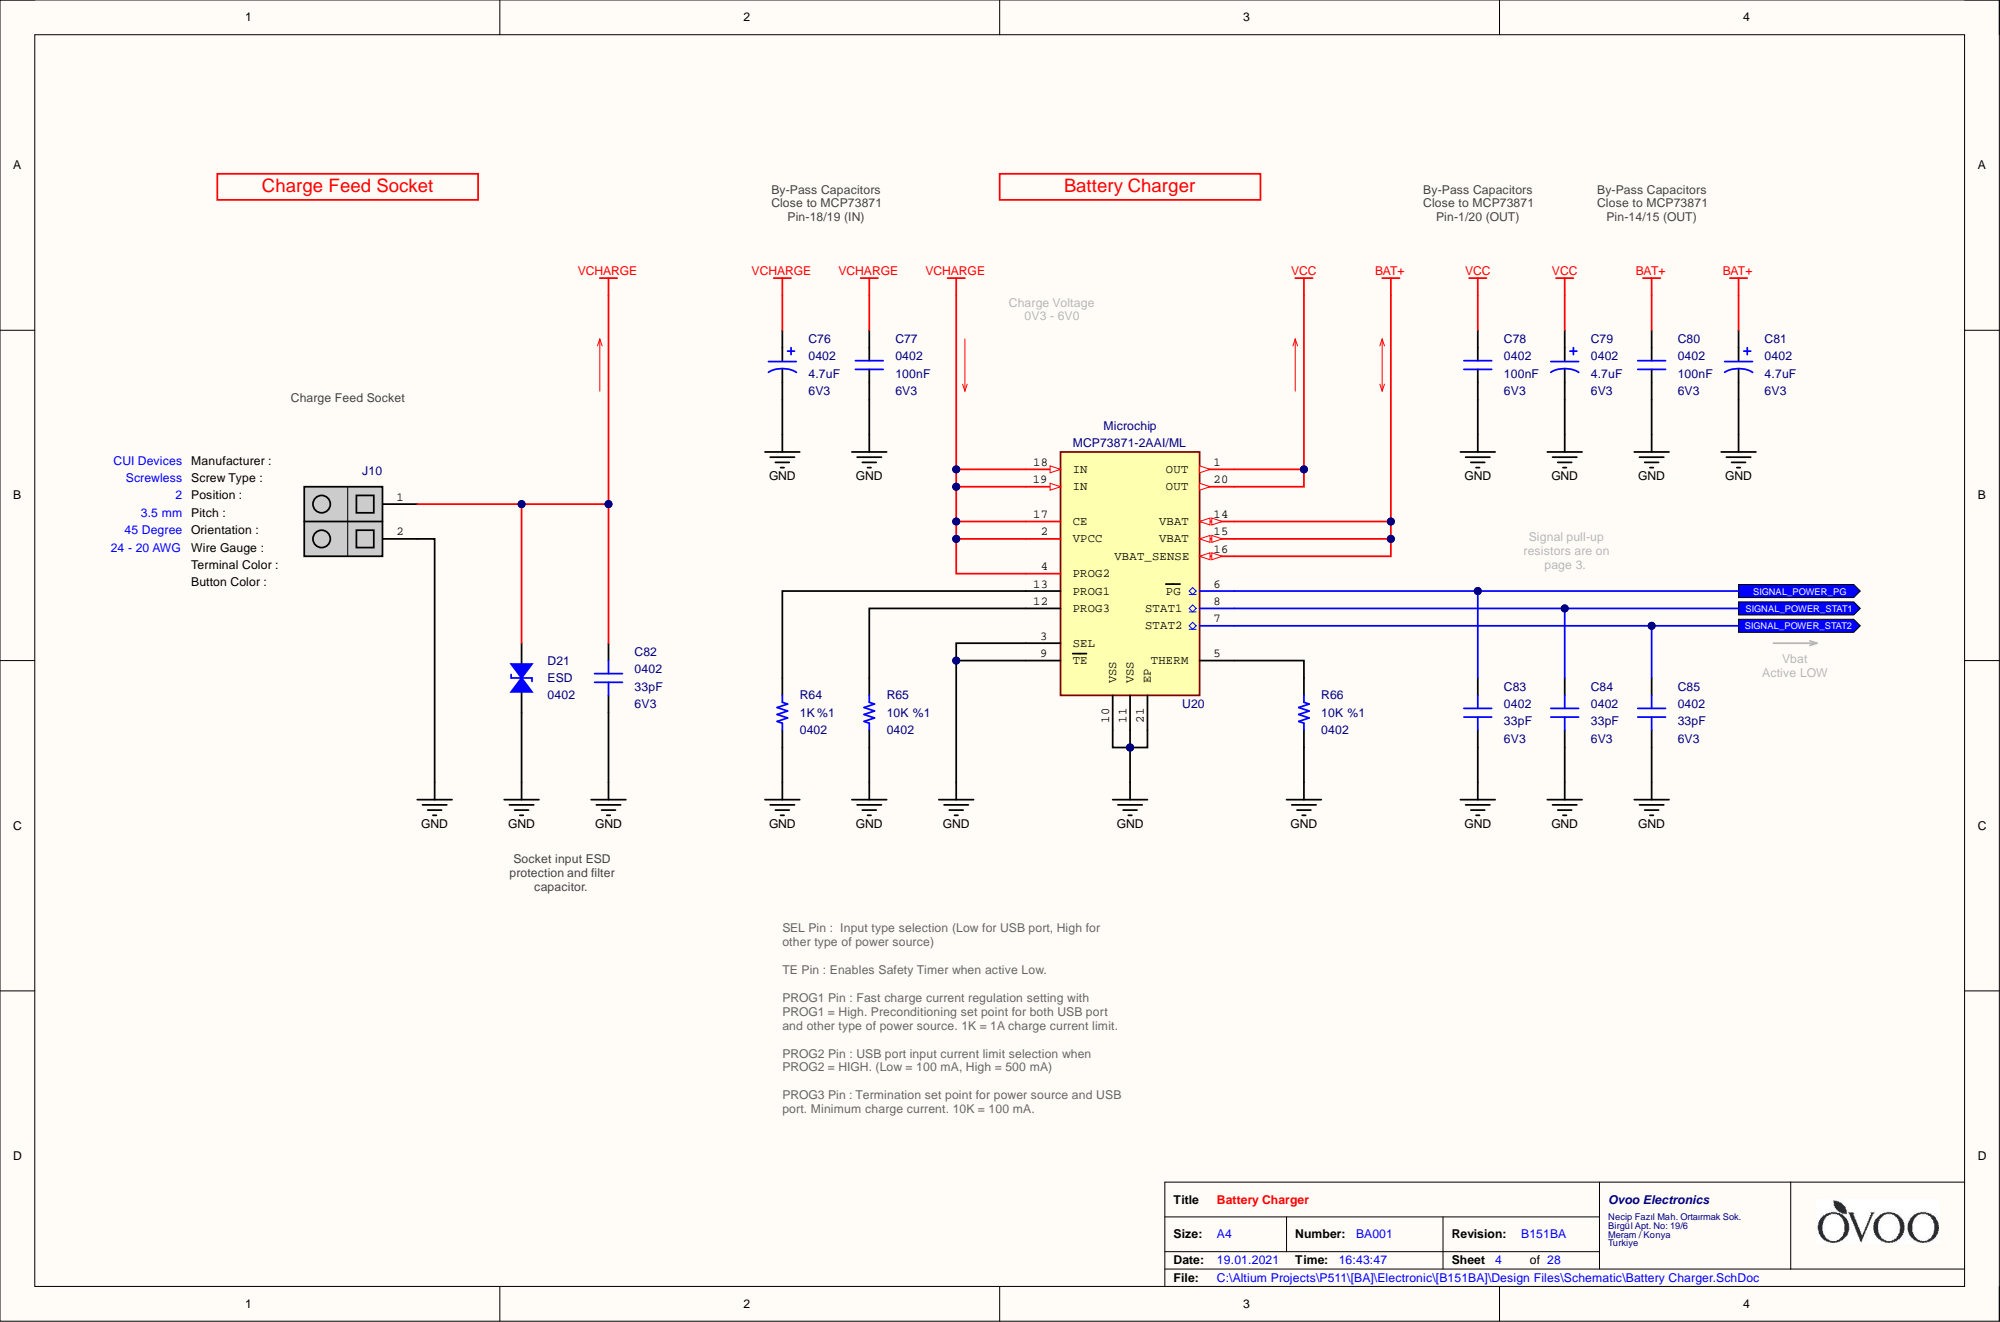
[picture p185: page 4]

1 7 | | 1 4
2 | | 1 5
4 | | 1 6

1 2 | 8

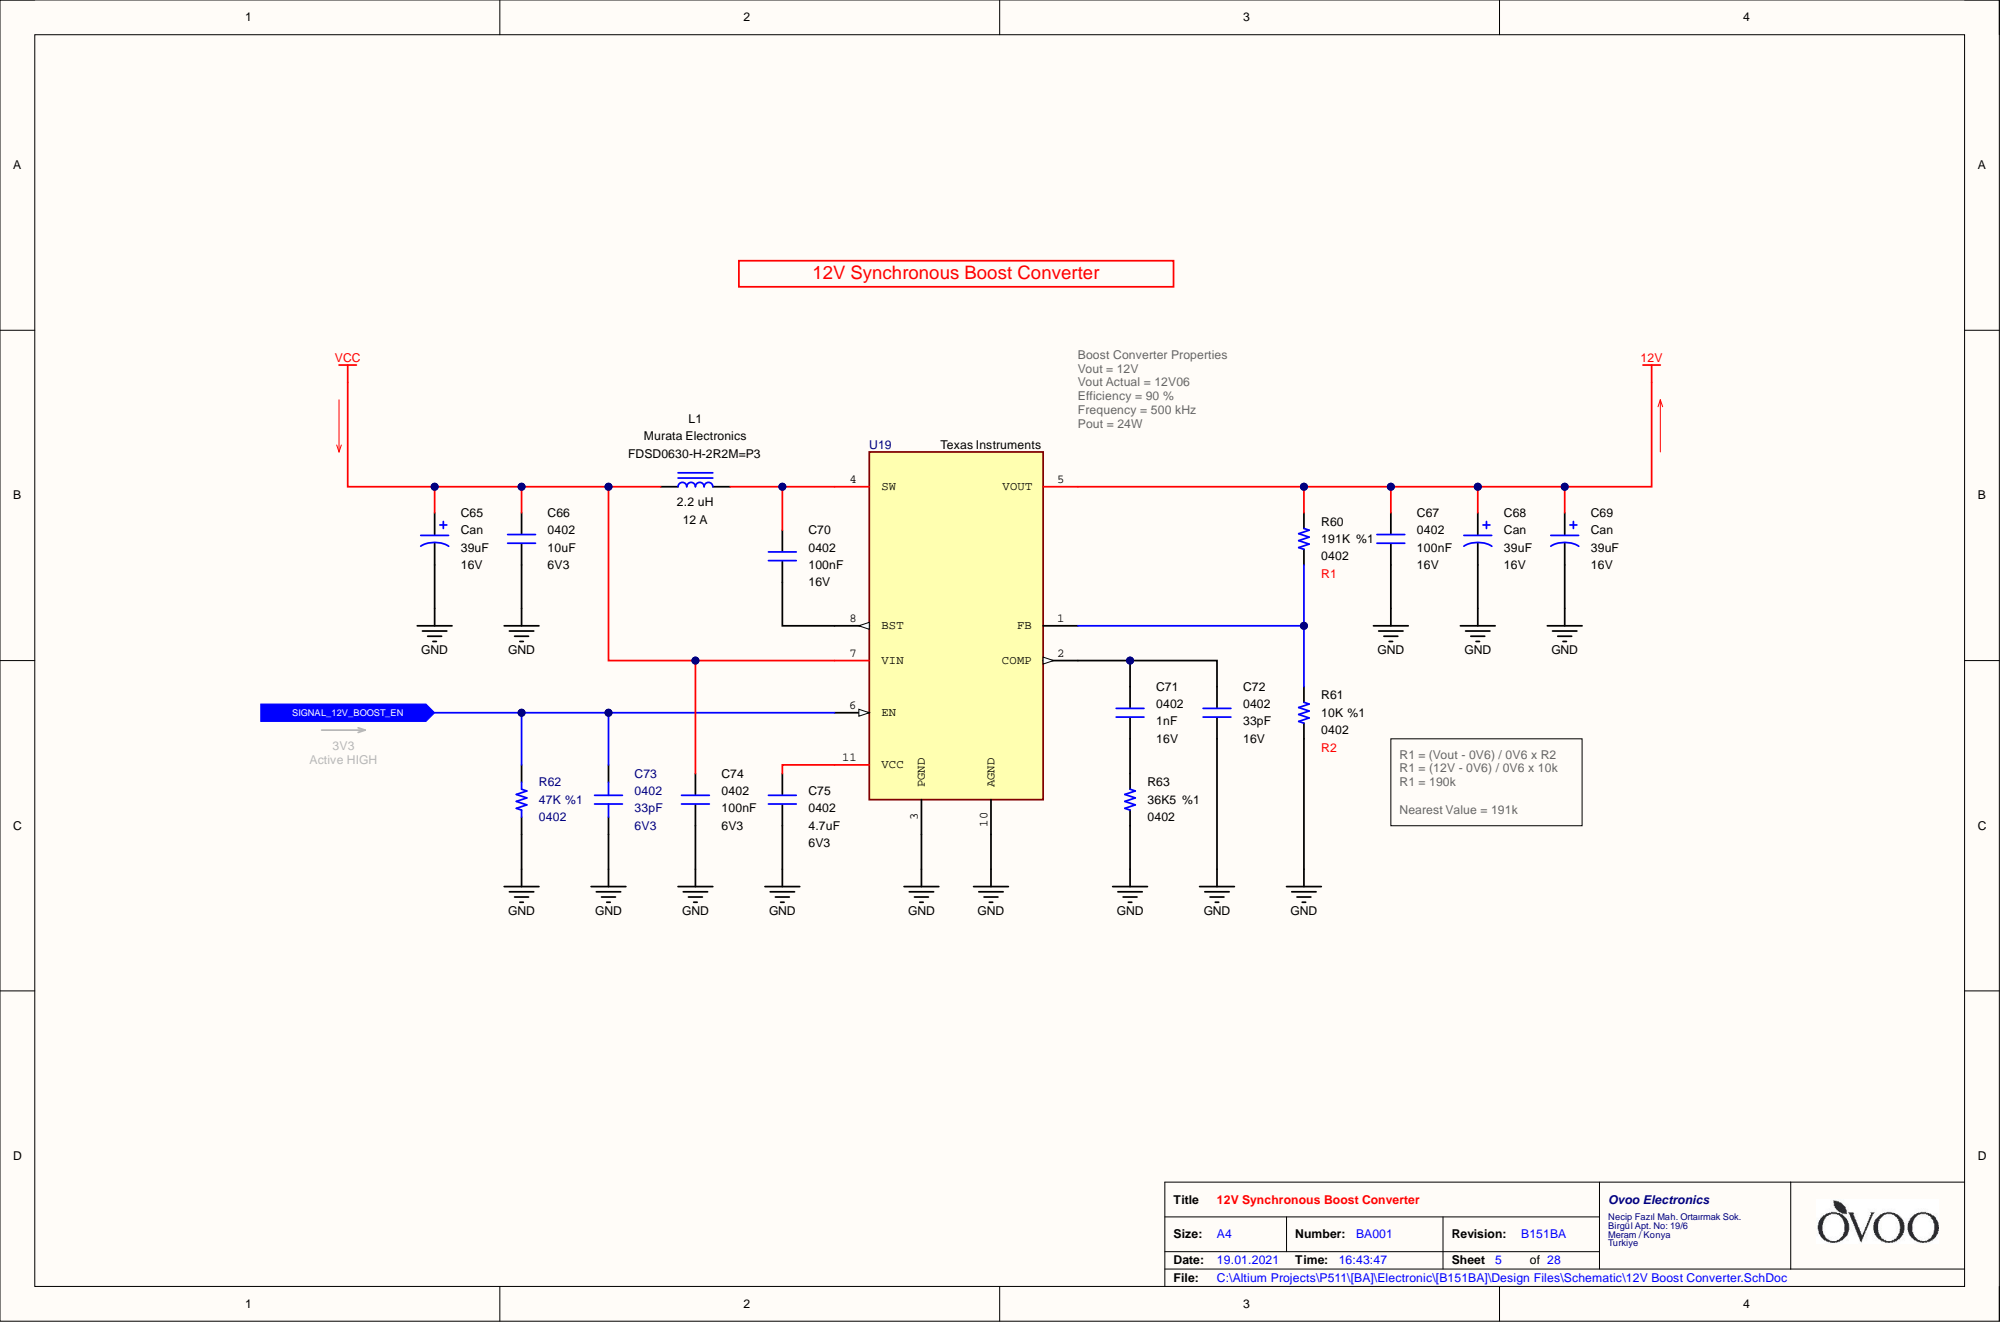
[picture p186: page 5]

C:\Altium Projects\P511\[BA]\Electronic\[B151BA]\Design Files\Schematic\12V Boost Converter.SchDoc

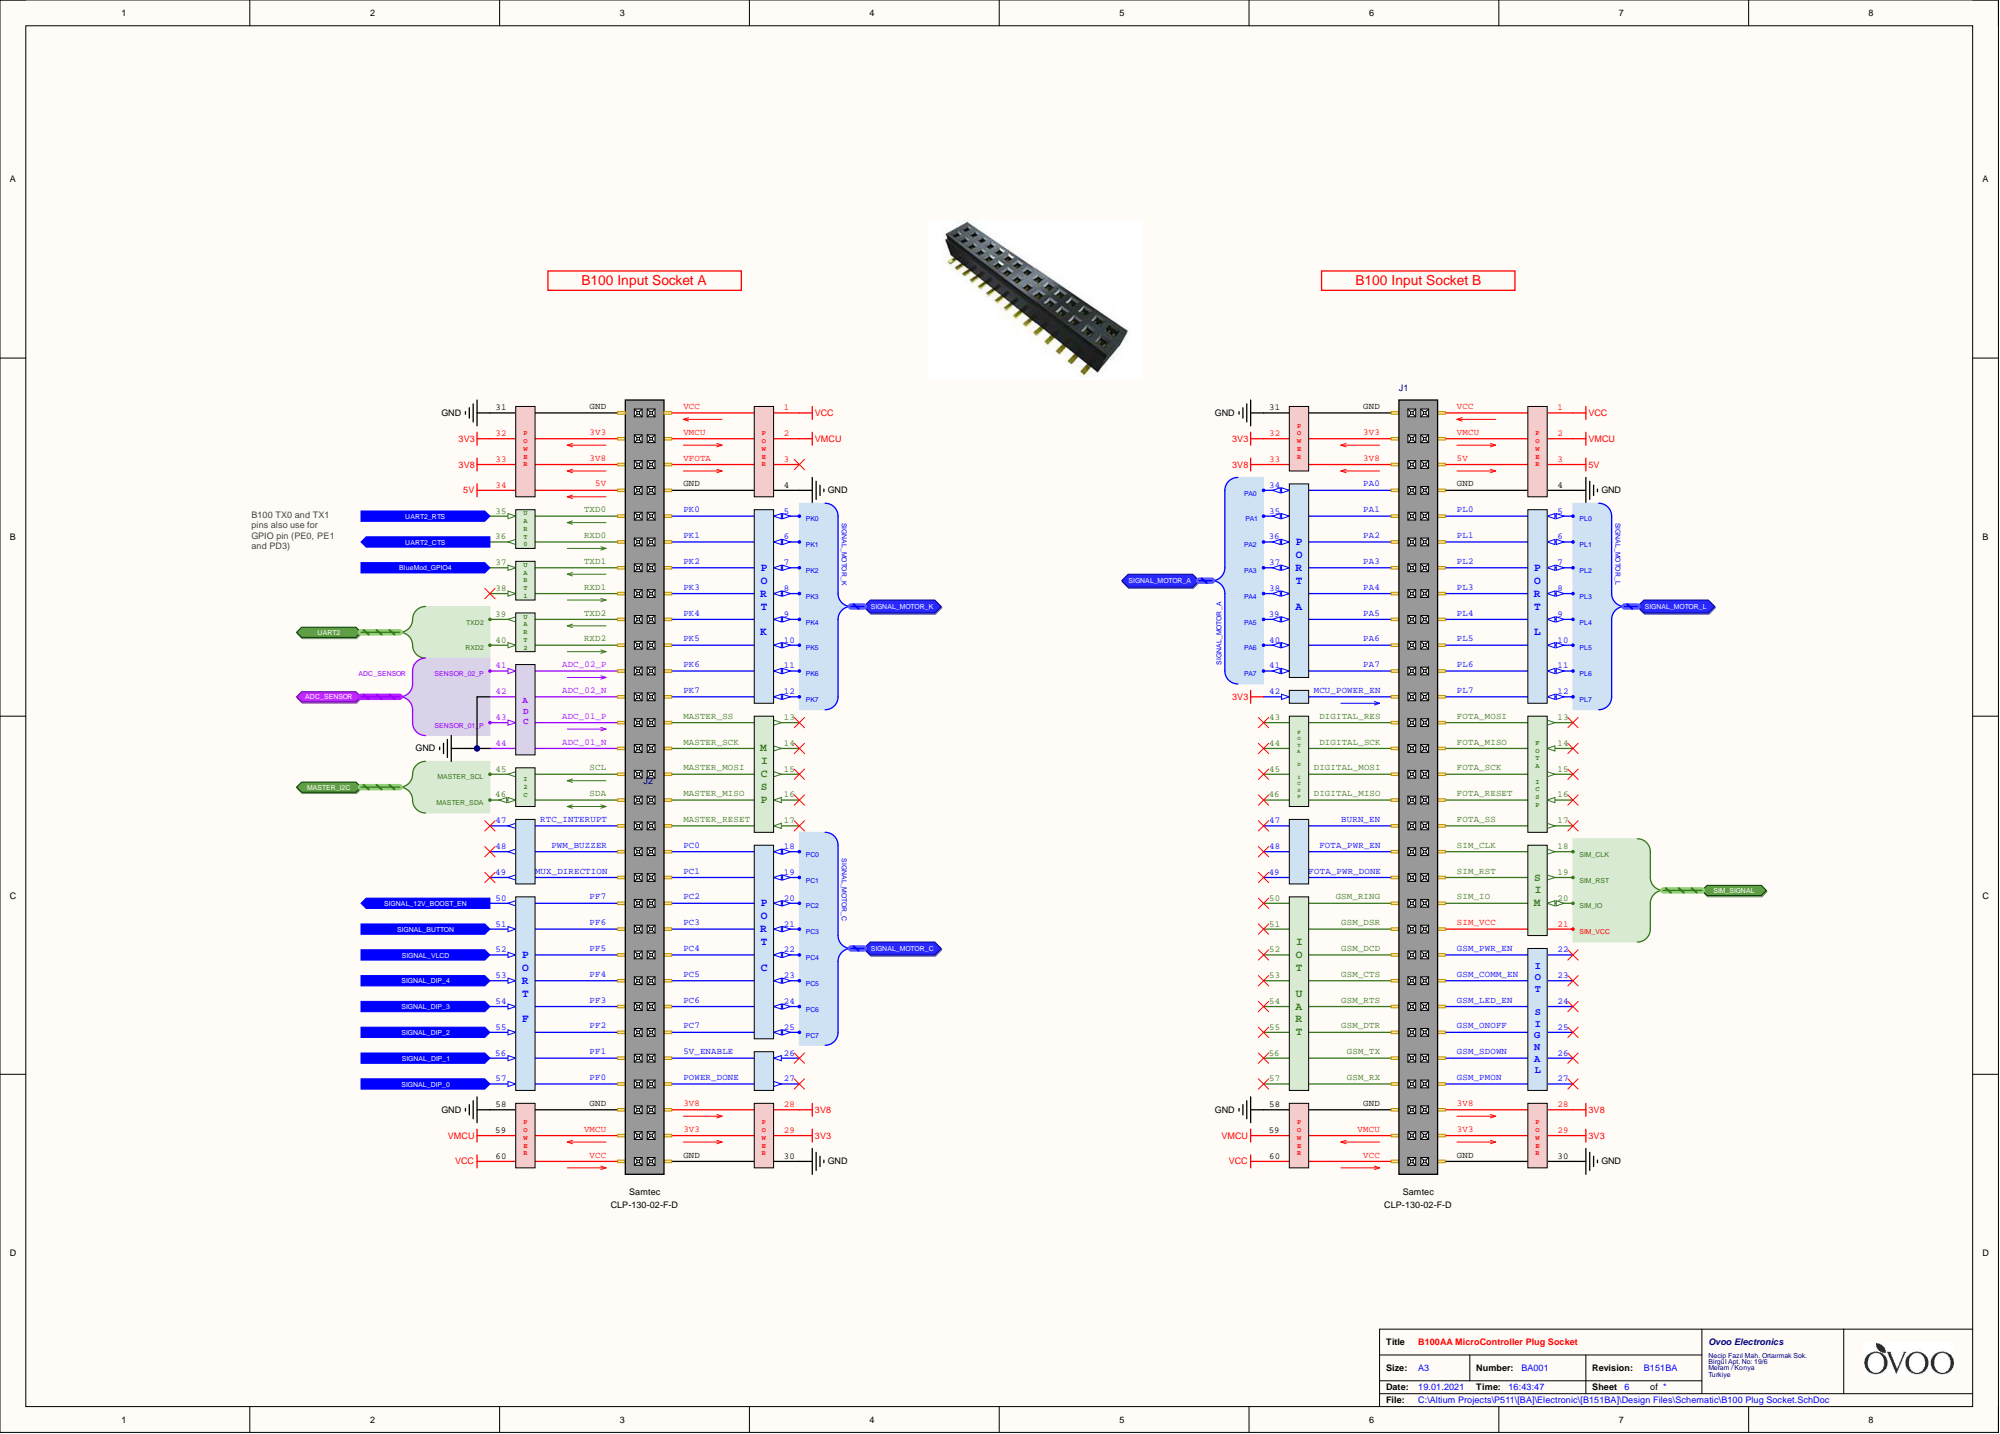
[picture p187: page 6]

B100 TX0 and TX1
pins also use for
GPIO pin (PE0, PE1
and PD3)

A R T | RXD1

C:\Altium Projects\P511\[BA]\Electronic\[B151BA]\Design Files\Schematic\B100 Plug Socket.SchDoc

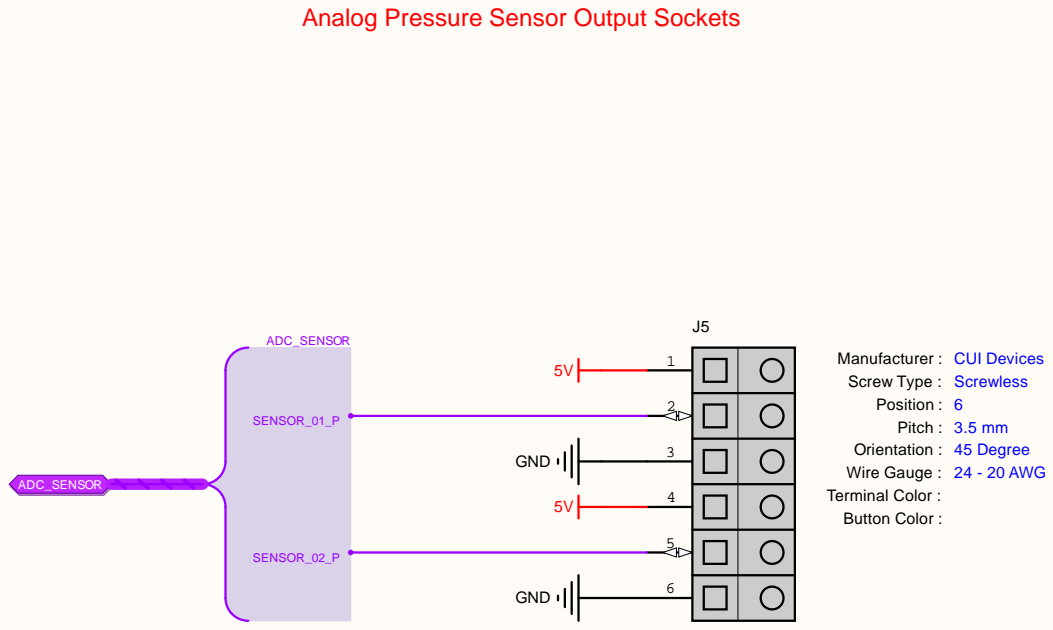
[picture p188: page 7]

Analog Pressure Sensor Output Sockets

Pressure Sensor Output Sockets

C:\Altium Projects\P511\[BA]\Electronic\[B151BA]\Design Files\Schematic\Pressure Sensor Output Sockets.SchDoc

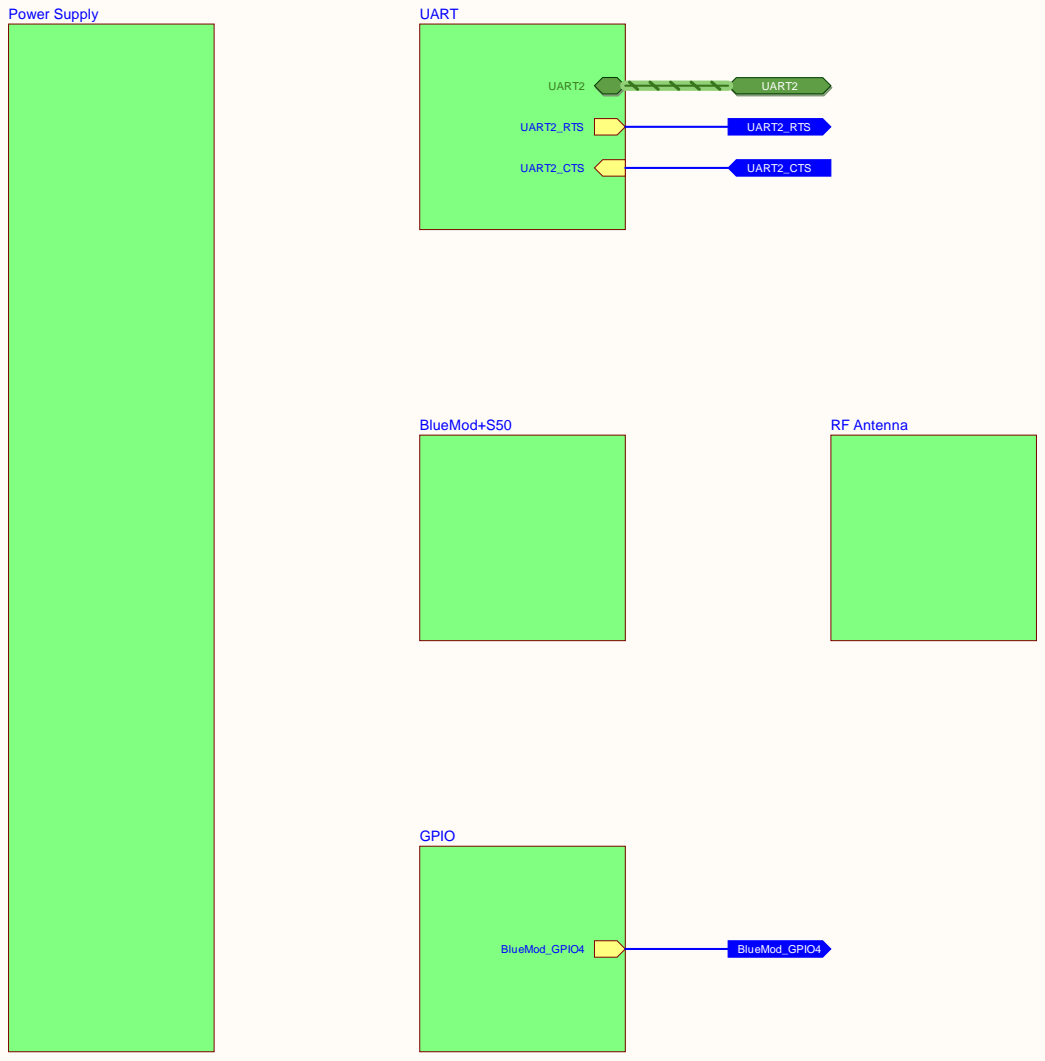
[picture p189: page 8]

C:\Altium Projects\P511\[BA]\Electronic\[B151BA]\Design Files\Schematic\BlueTooth Module.SchDoc

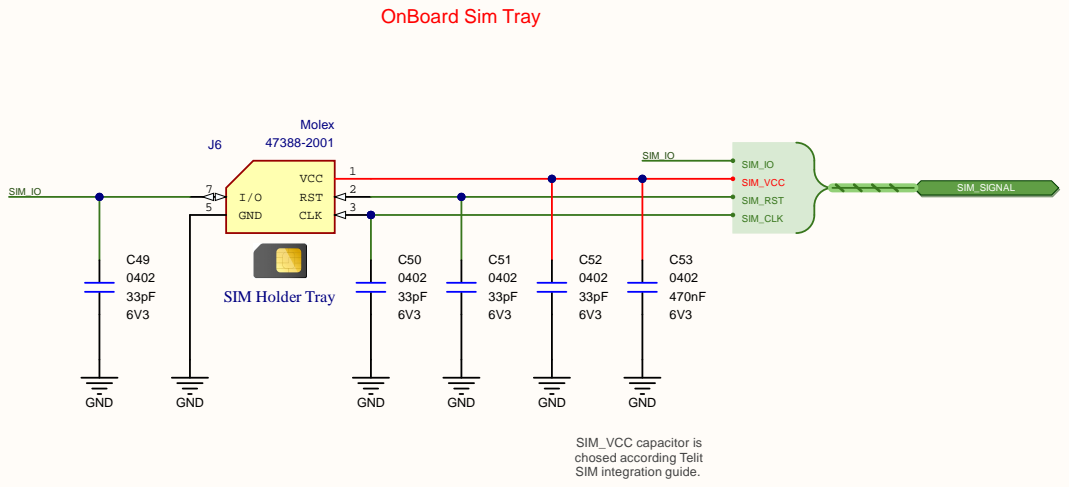
[picture p190: page 9]

C:\Altium Projects\P511\[BA]\Electronic\[B151BA]\Design Files\Schematic\External SIM Tray.SchDoc

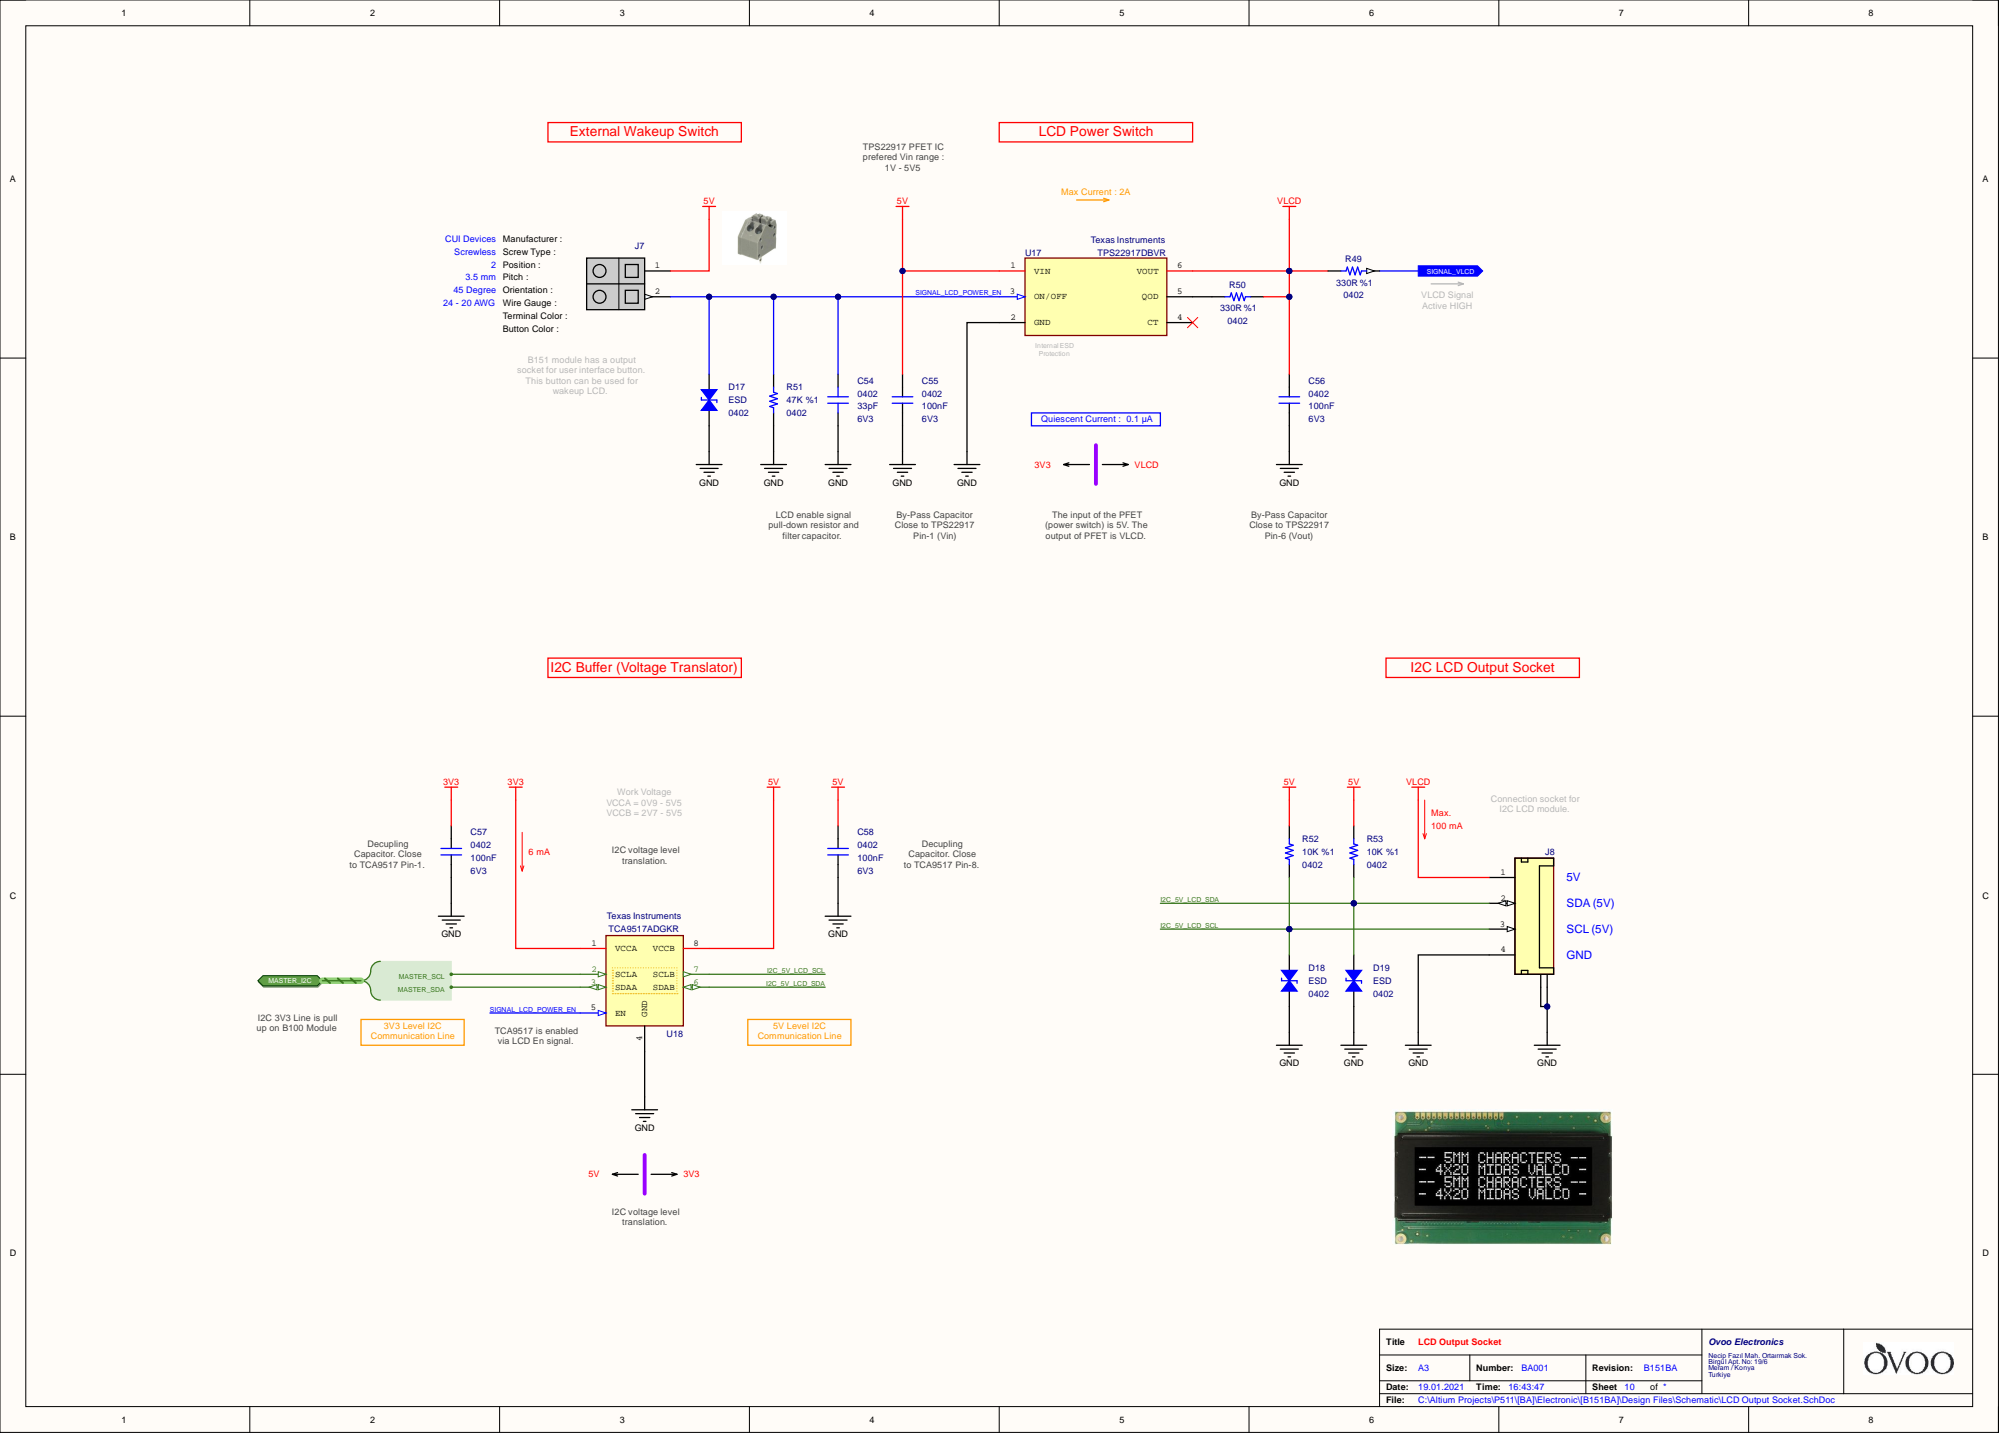
[picture p191: page 10]

B151 module has a output
socket for user interface button.
This button can be used for

LCD enable signal
pull-down resistor and
filter capacitor.

The input of the PFET
(power switch) is 5V. The
output of PFET is VLCD.

TCA9517 is enabled
via LCD En signal.

C:\Altium Projects\P511\[BA]\Electronic\[B151BA]\Design Files\Schematic\LCD Output Socket.SchDoc

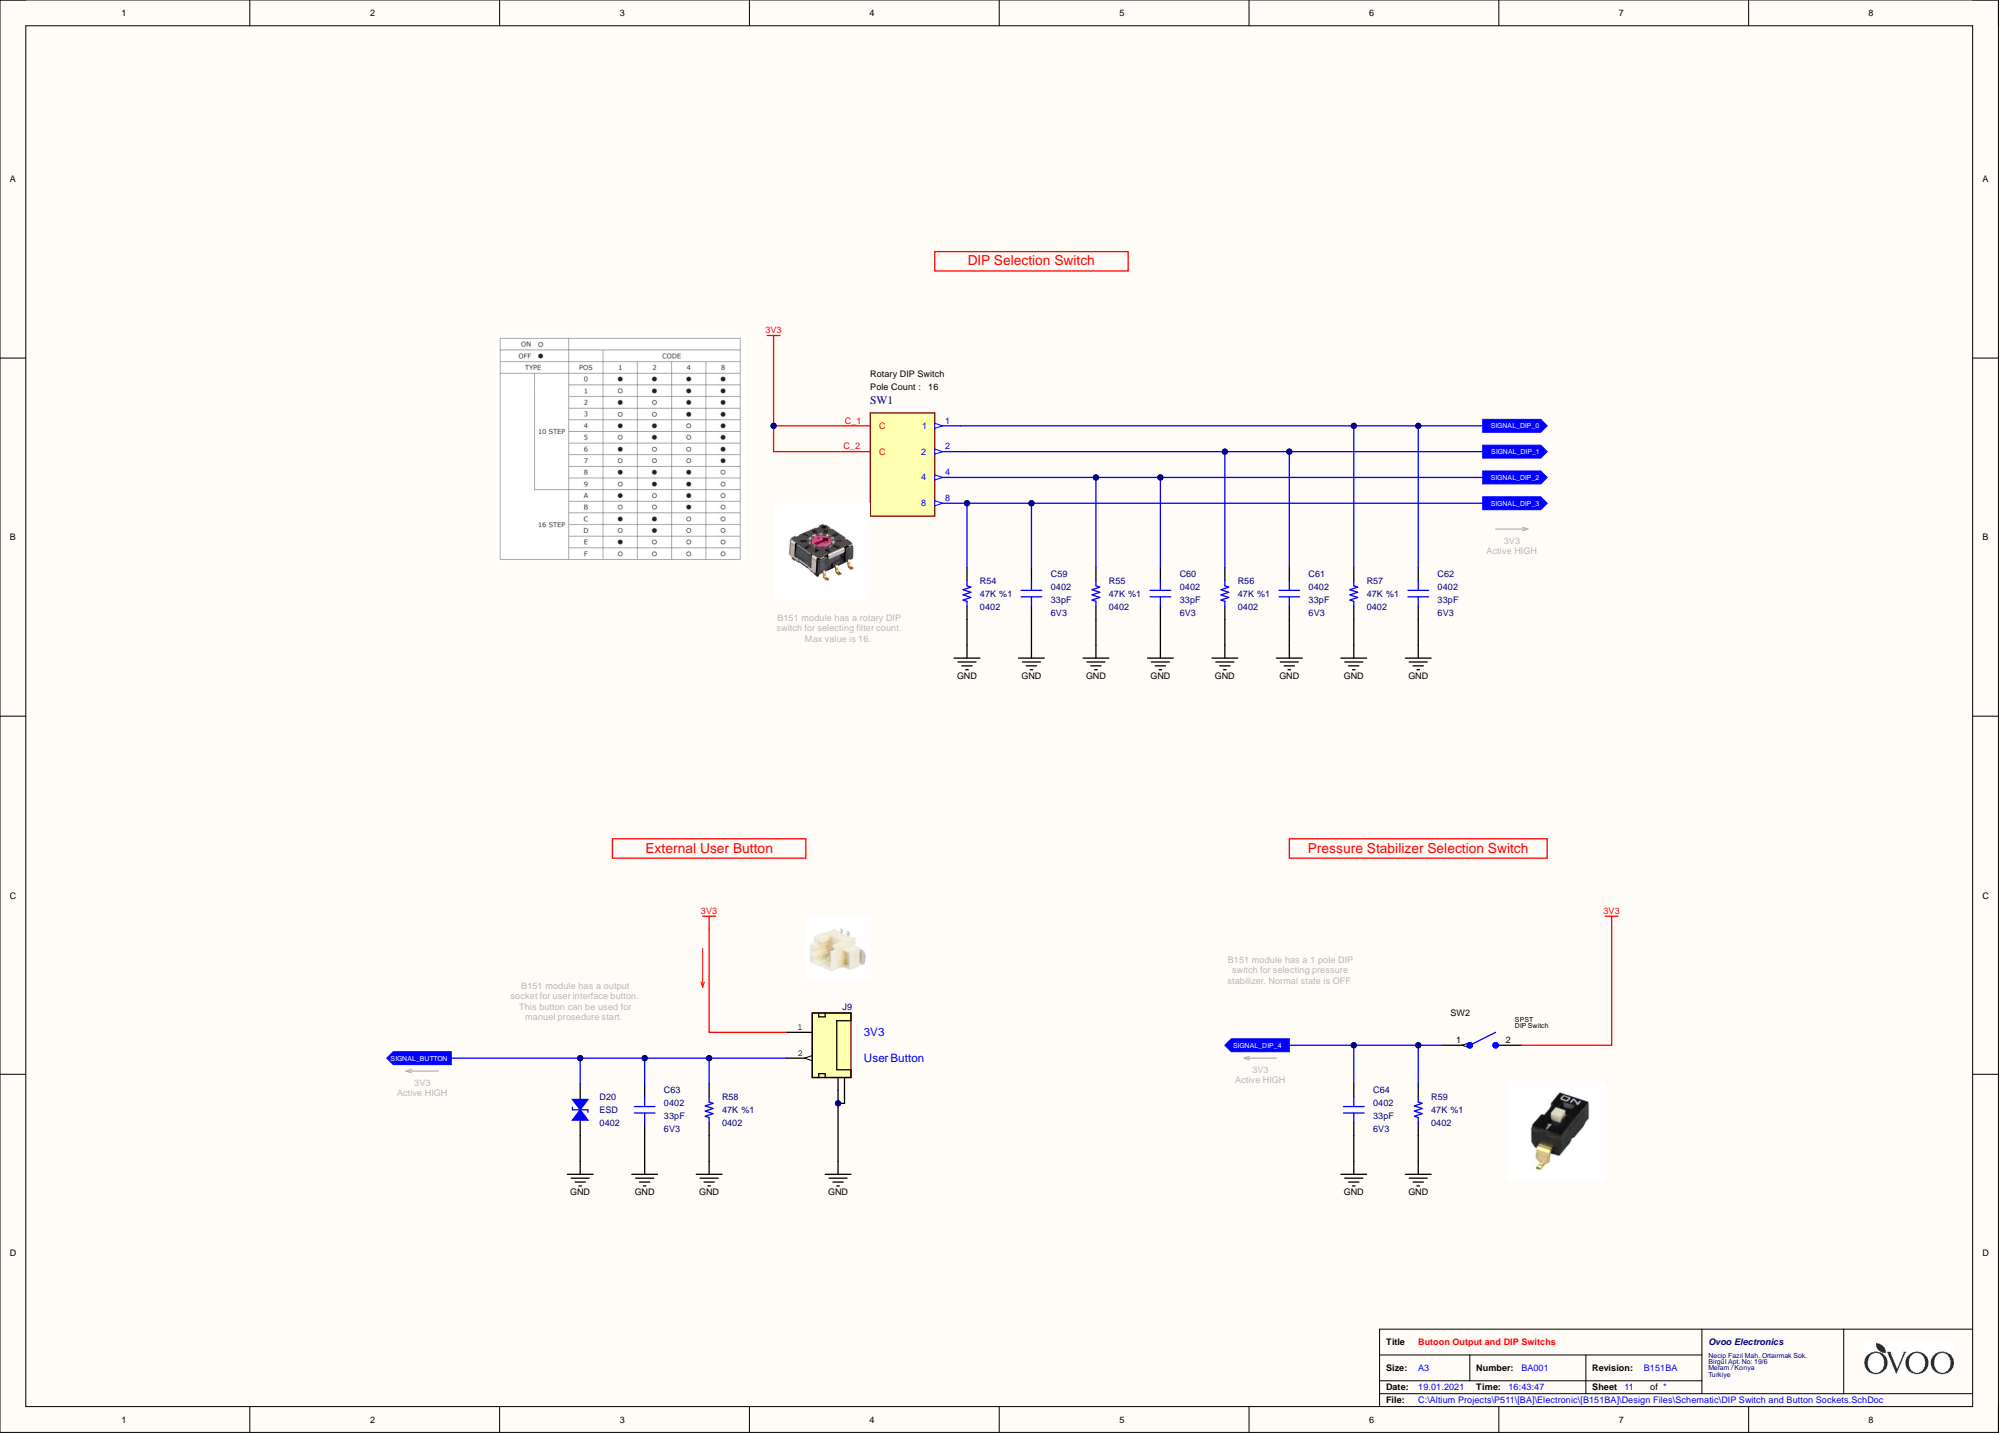
[picture p192: page 11]

B151 module has a rotary DIP
switch for selecting filter count.

B151 module has a 1 pole DIP
switch for selecting pressure
stabilizer. Normal state is OFF

B151 module has a output
socket for user interface button.
This button can be used for
manuel prosedure start.

Butoon Output and DIP Switchs

C:\Altium Projects\P511\[BA]\Electronic\[B151BA]\Design Files\Schematic\DIP Switch and Button Sockets.SchDoc

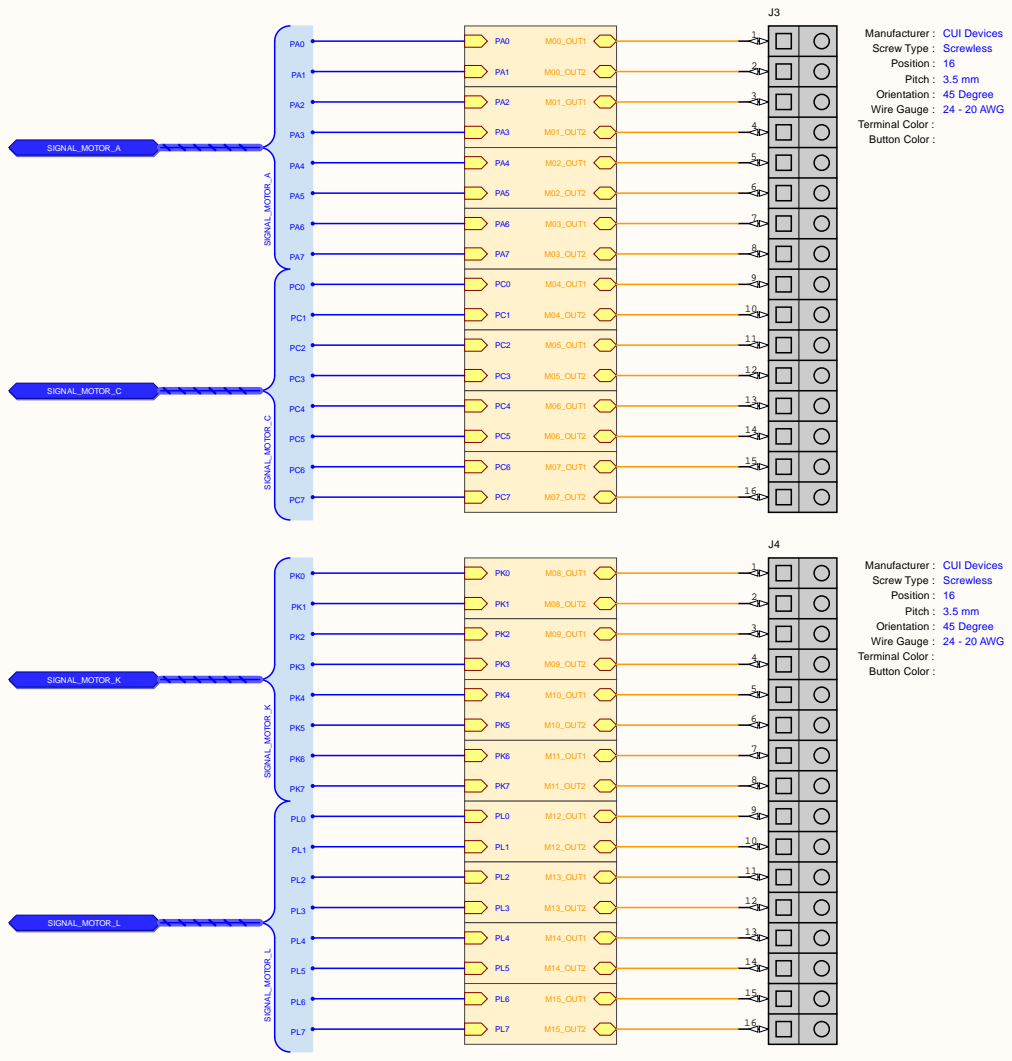
[picture p193: page 12]

C:\Altium Projects\P511\[BA]\Electronic\[B151BA]\Design Files\Schematic\Motor Drivers.SchDoc

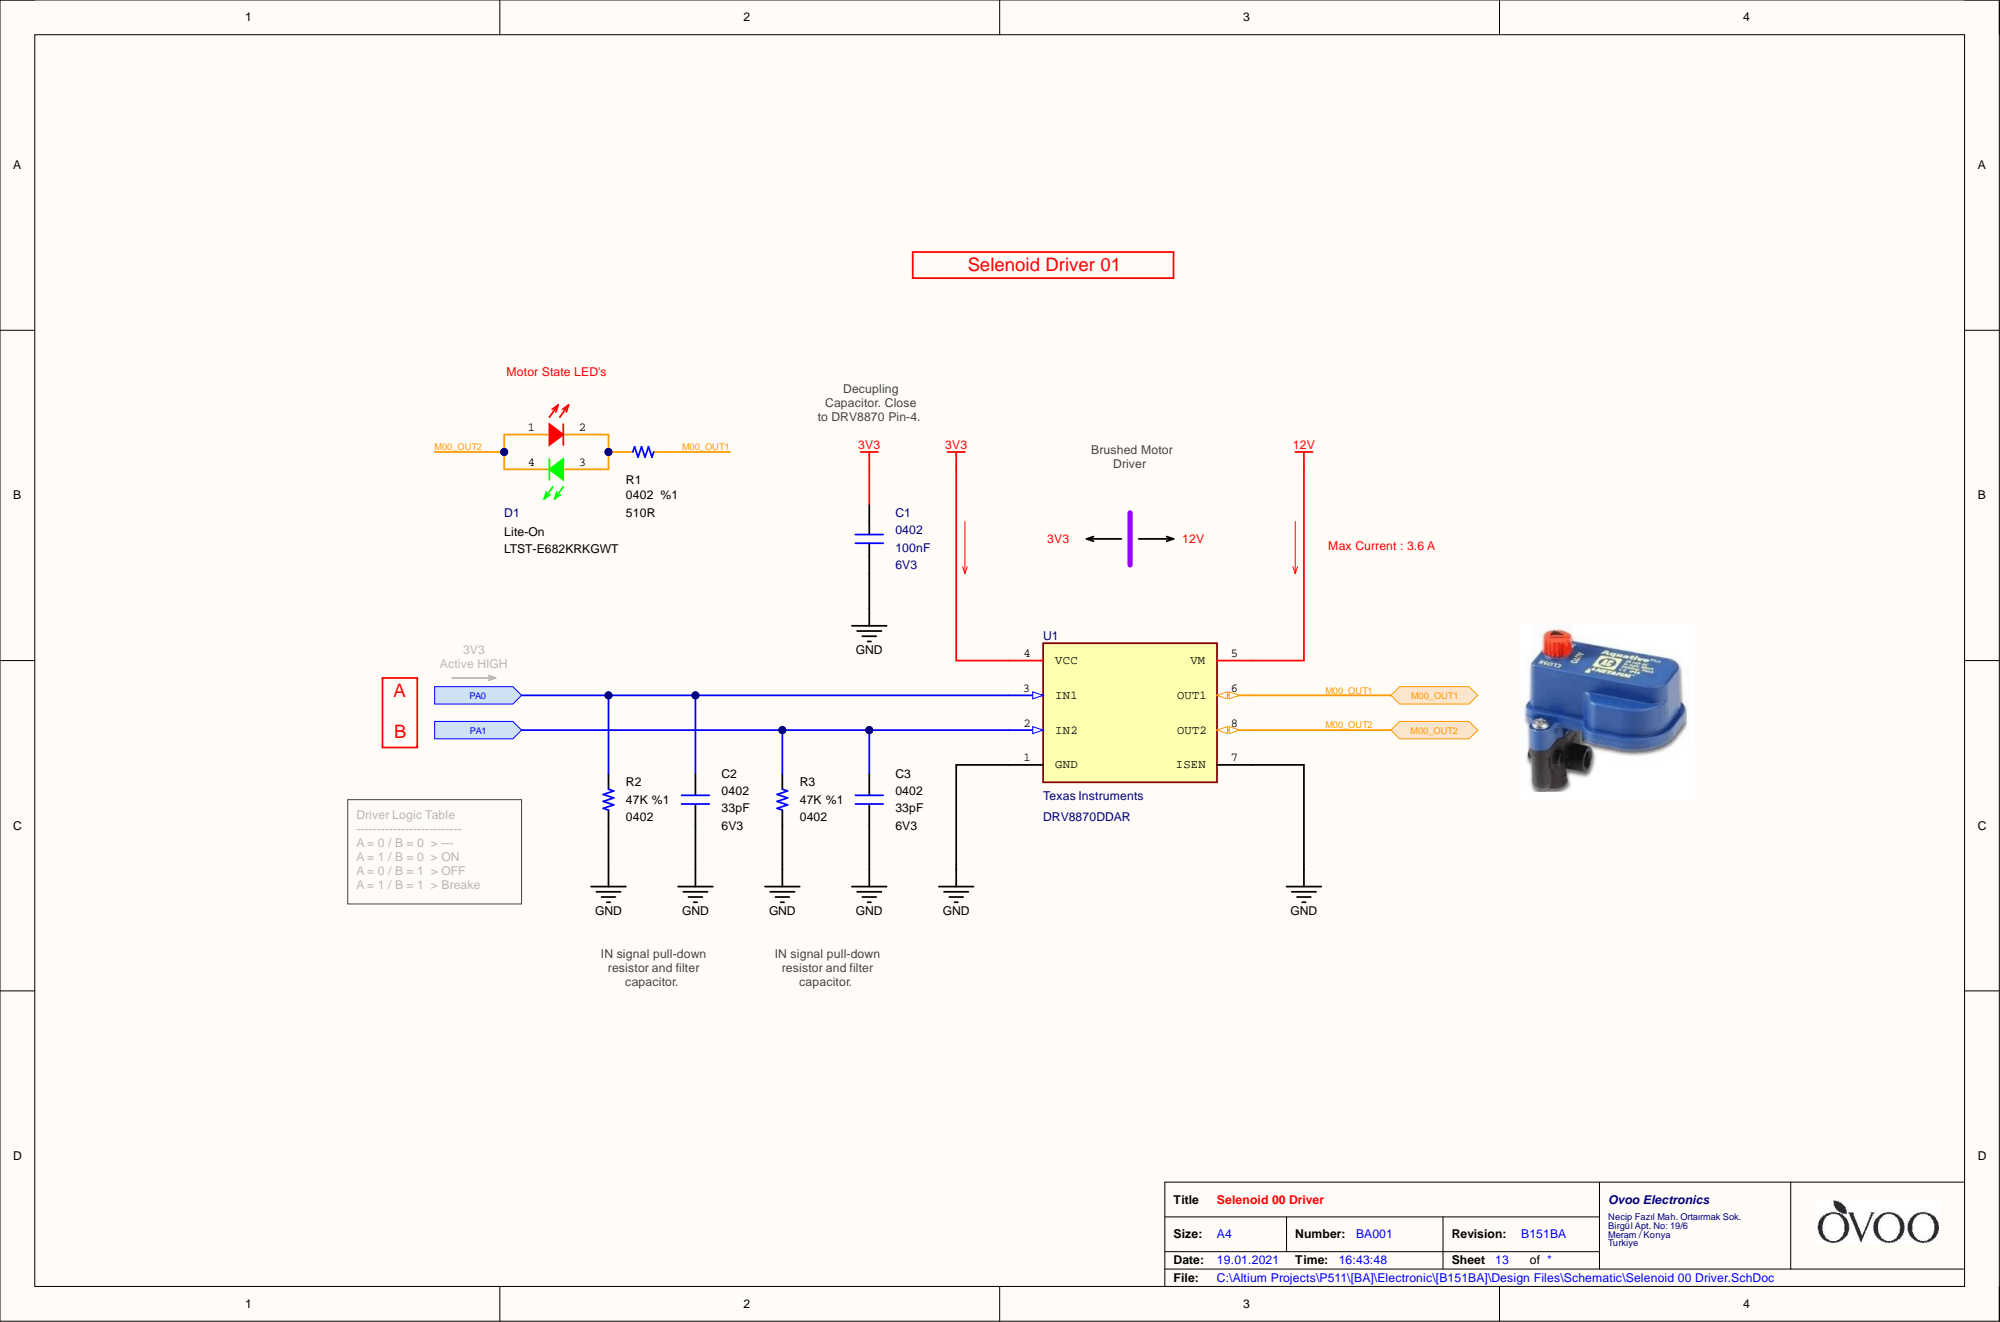
[picture p194: page 13]

IN signal pull-down
resistor and filter
capacitor.

C:\Altium Projects\P511\[BA]\Electronic\[B151BA]\Design Files\Schematic\Selenoid 00 Driver.SchDoc

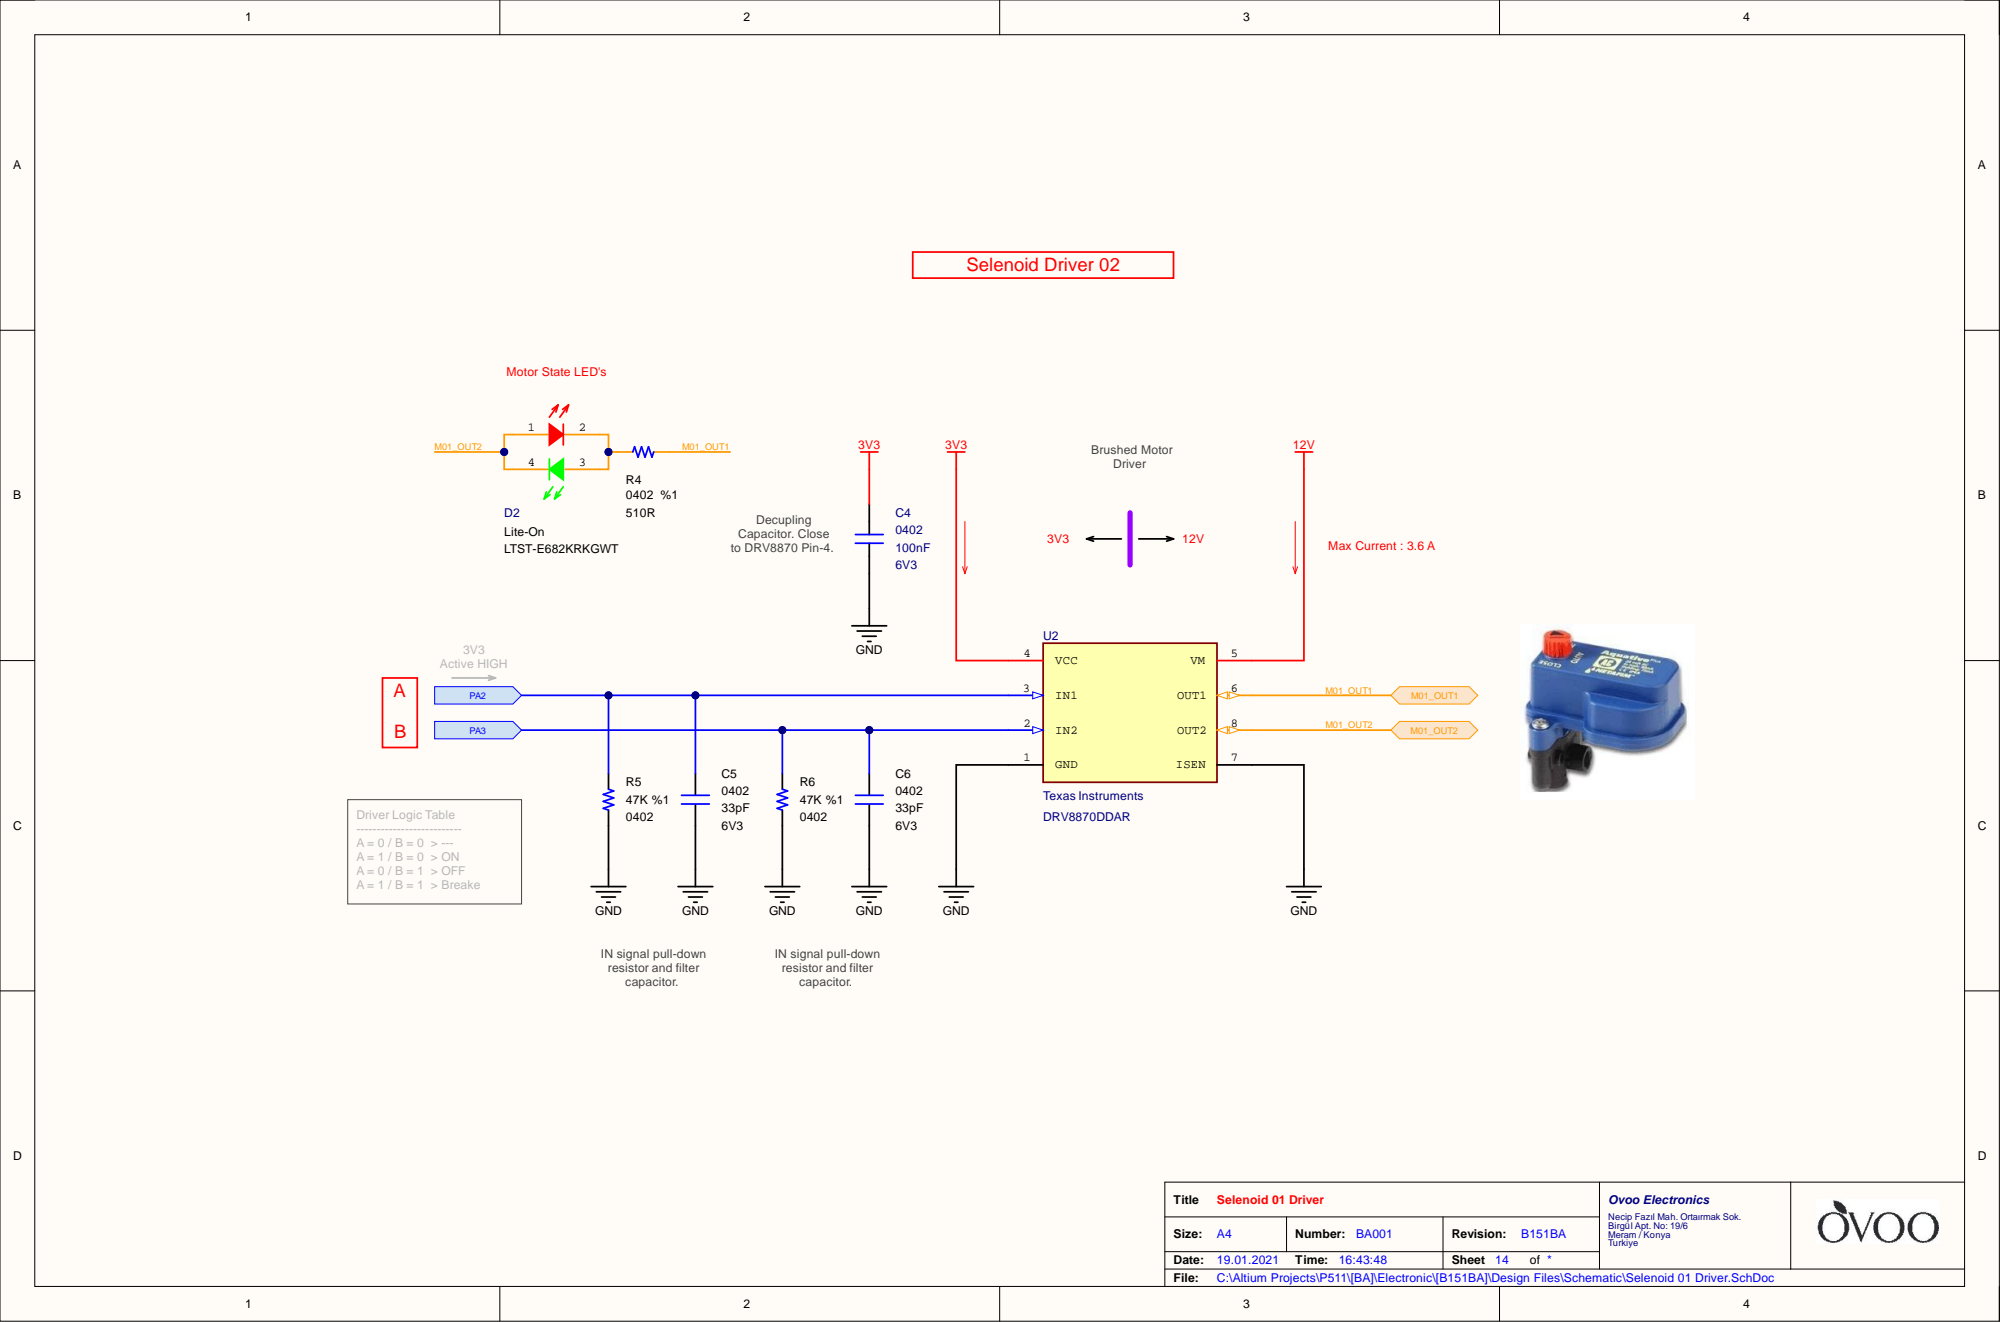
[picture p195: page 14]

IN signal pull-down
resistor and filter
capacitor.

C:\Altium Projects\P511\[BA]\Electronic\[B151BA]\Design Files\Schematic\Selenoid 01 Driver.SchDoc

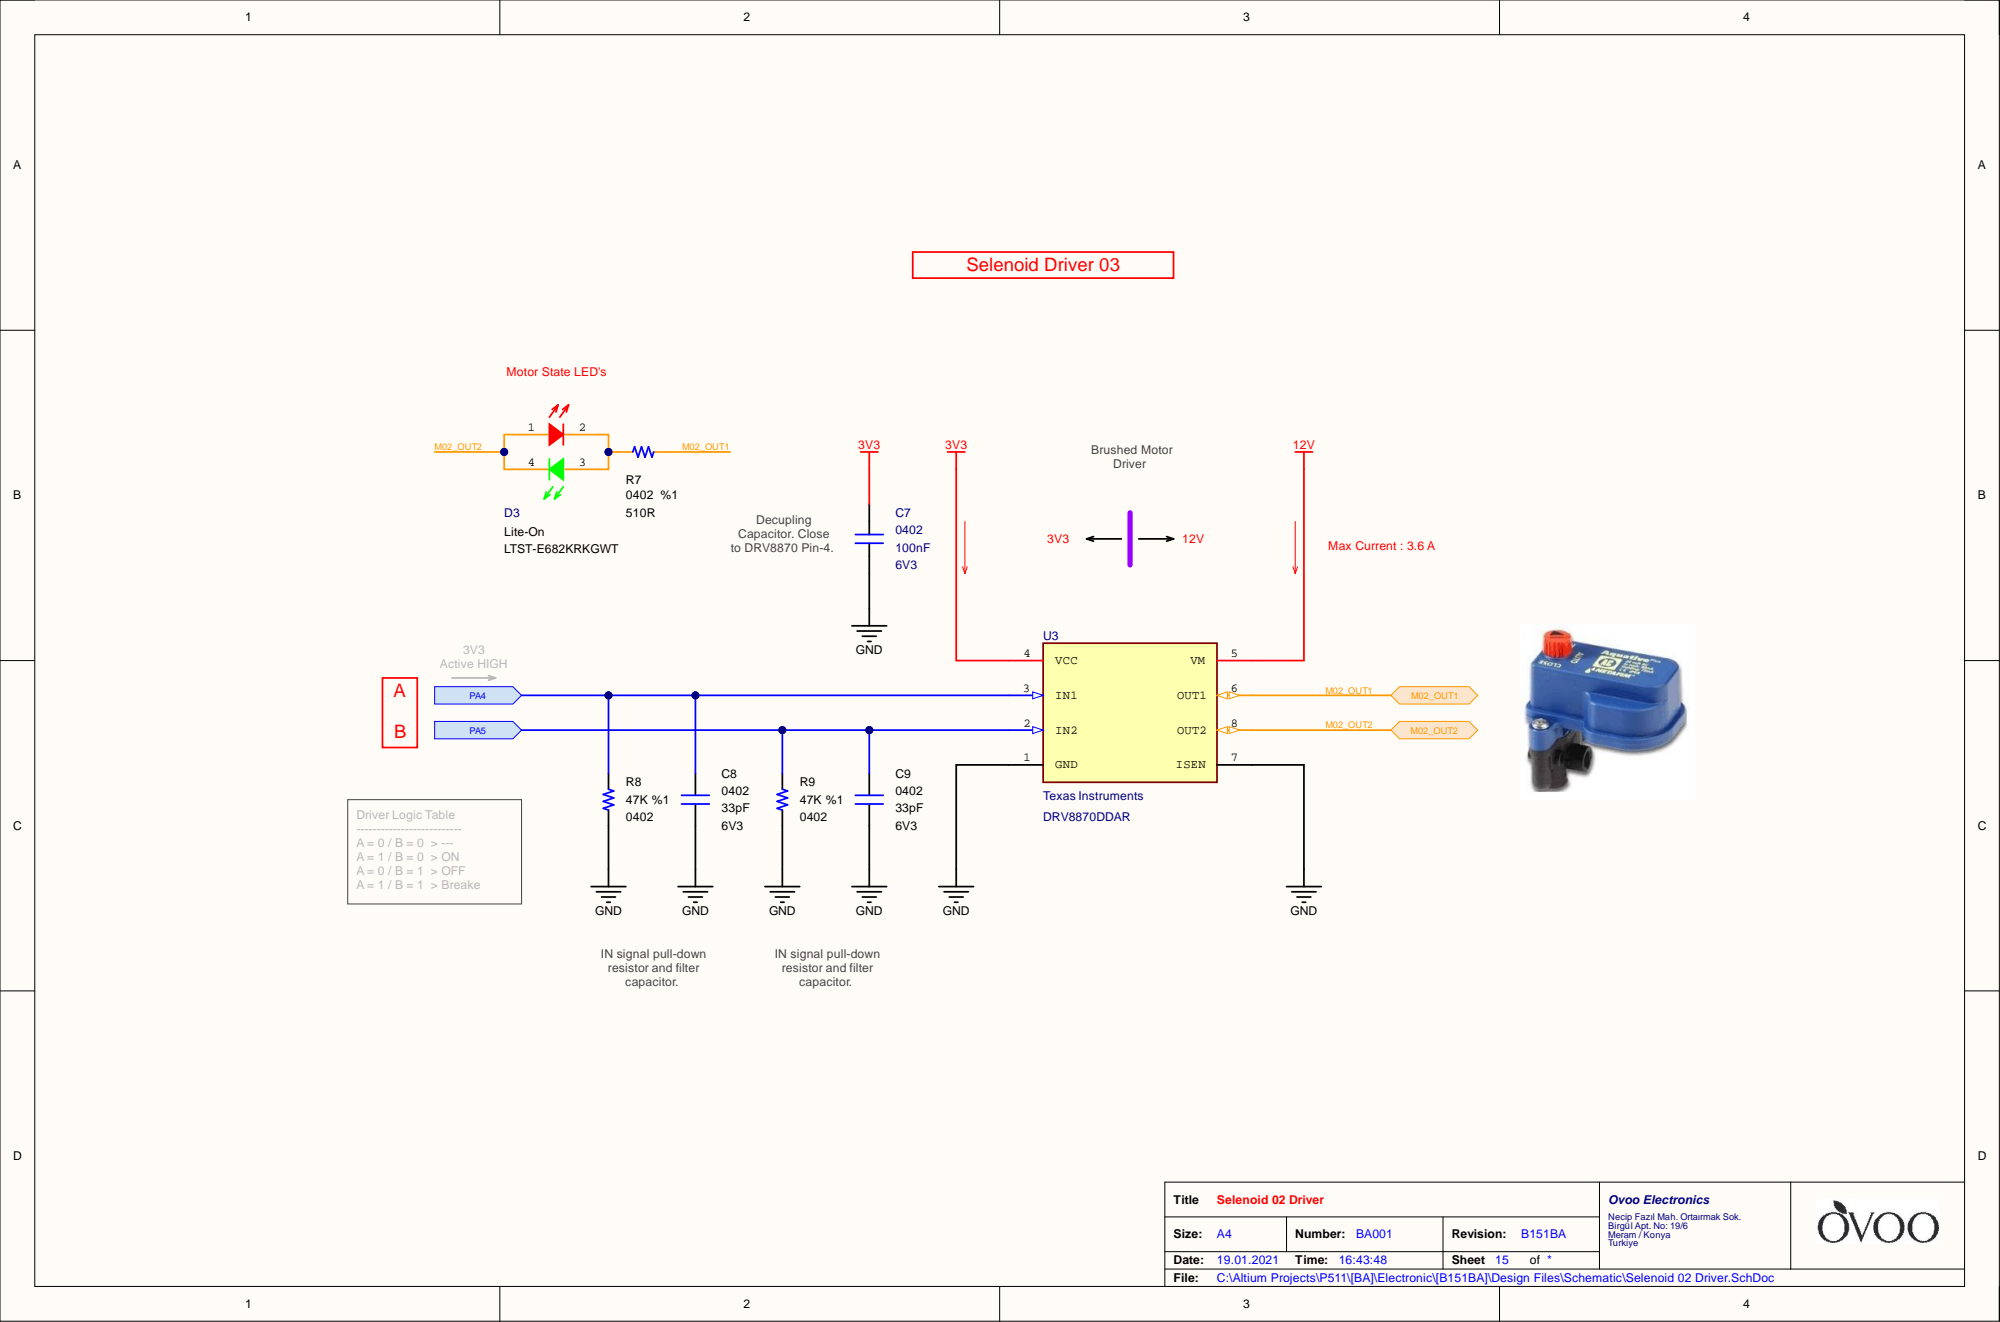
[picture p196: page 15]

IN signal pull-down
resistor and filter
capacitor.

C:\Altium Projects\P511\[BA]\Electronic\[B151BA]\Design Files\Schematic\Selenoid 02 Driver.SchDoc

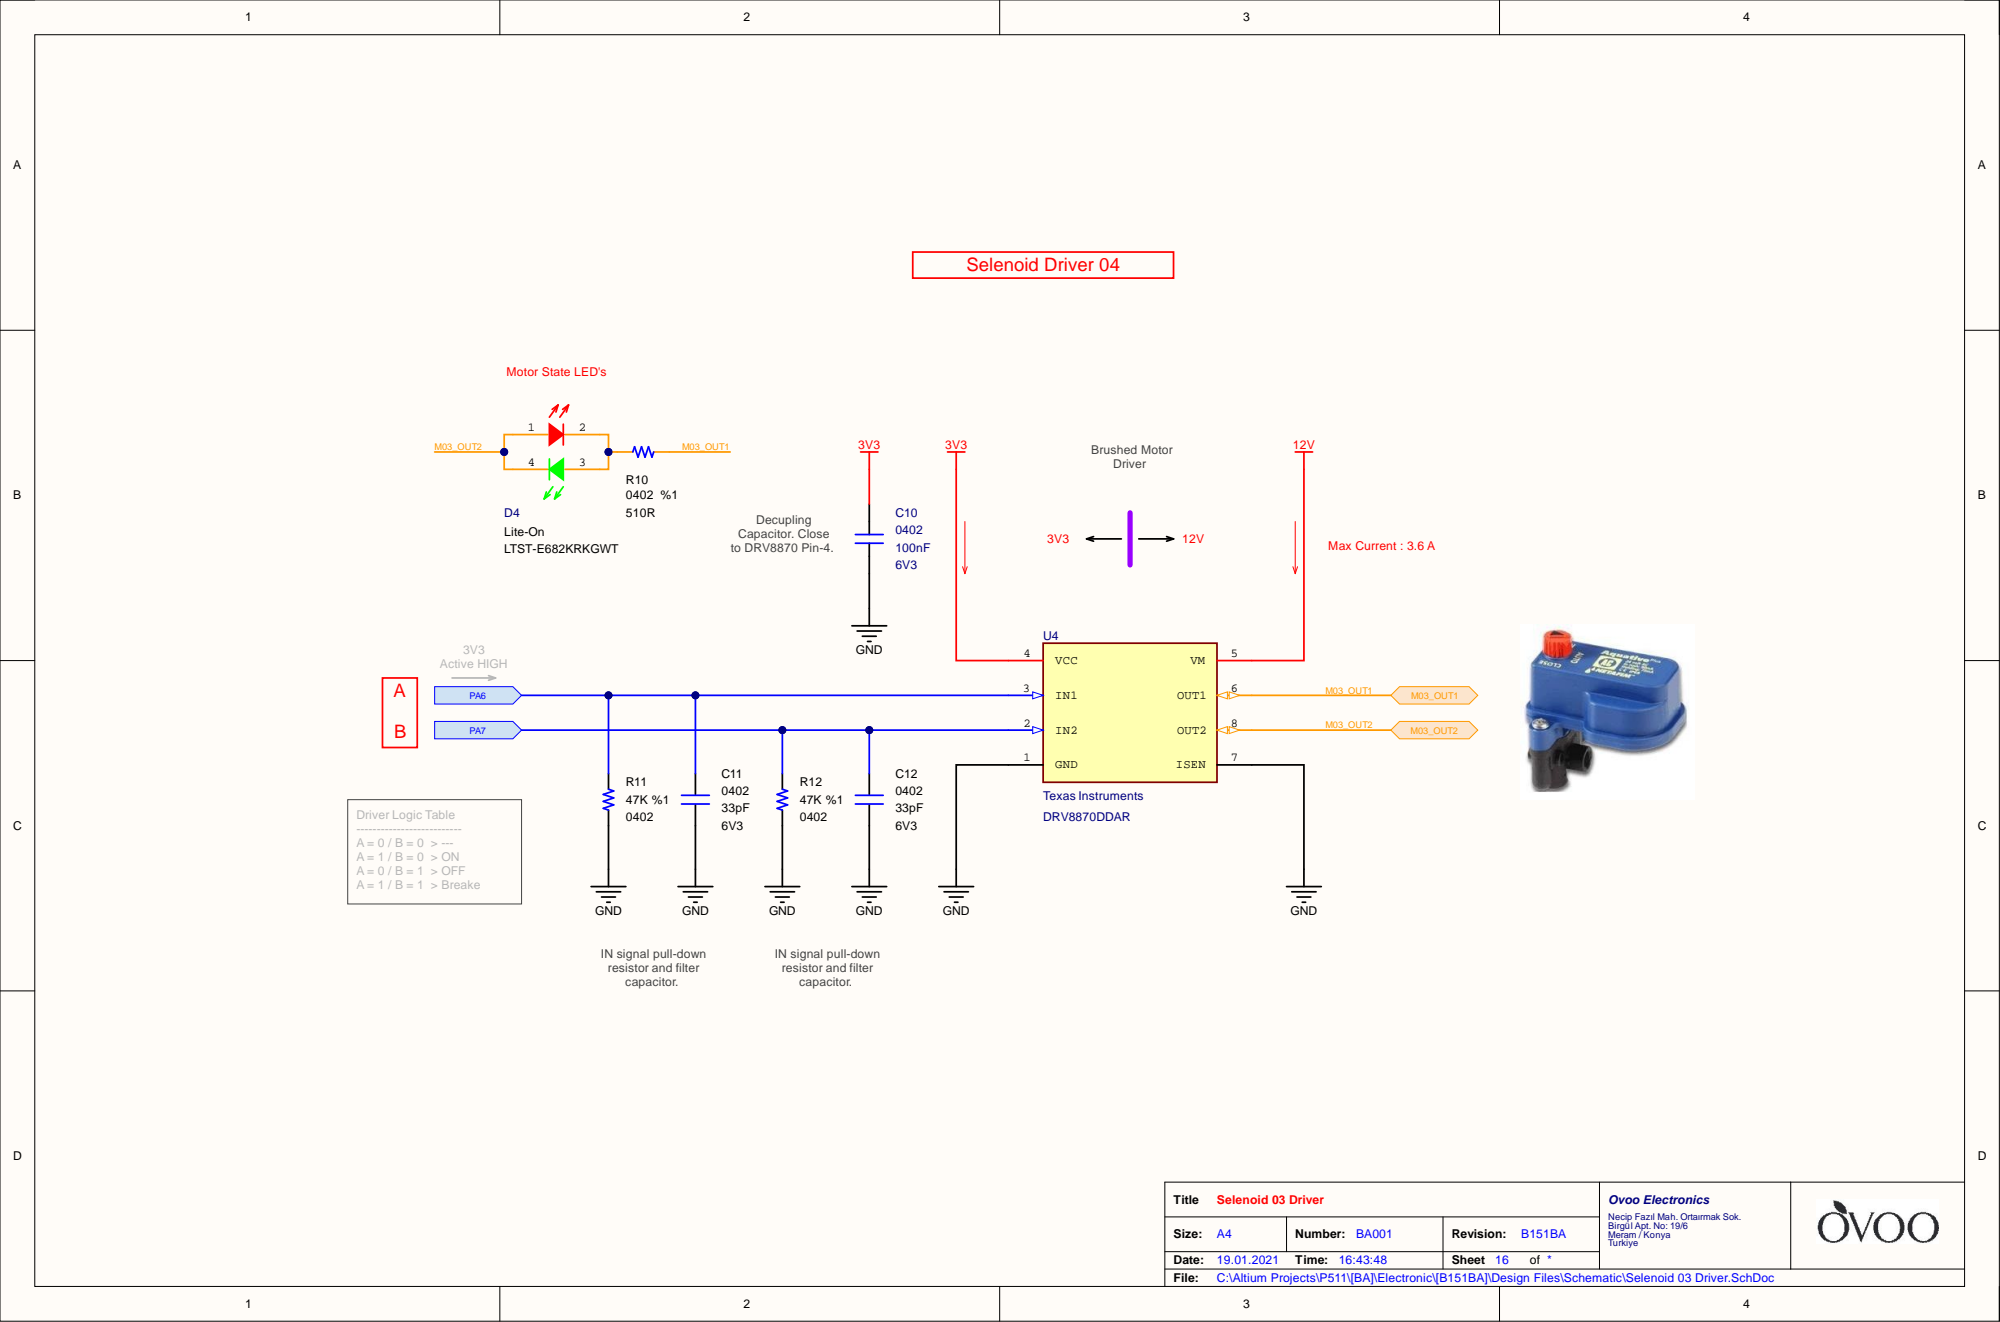
[picture p197: page 16]

IN signal pull-down
resistor and filter
capacitor.

C:\Altium Projects\P511\[BA]\Electronic\[B151BA]\Design Files\Schematic\Selenoid 03 Driver.SchDoc

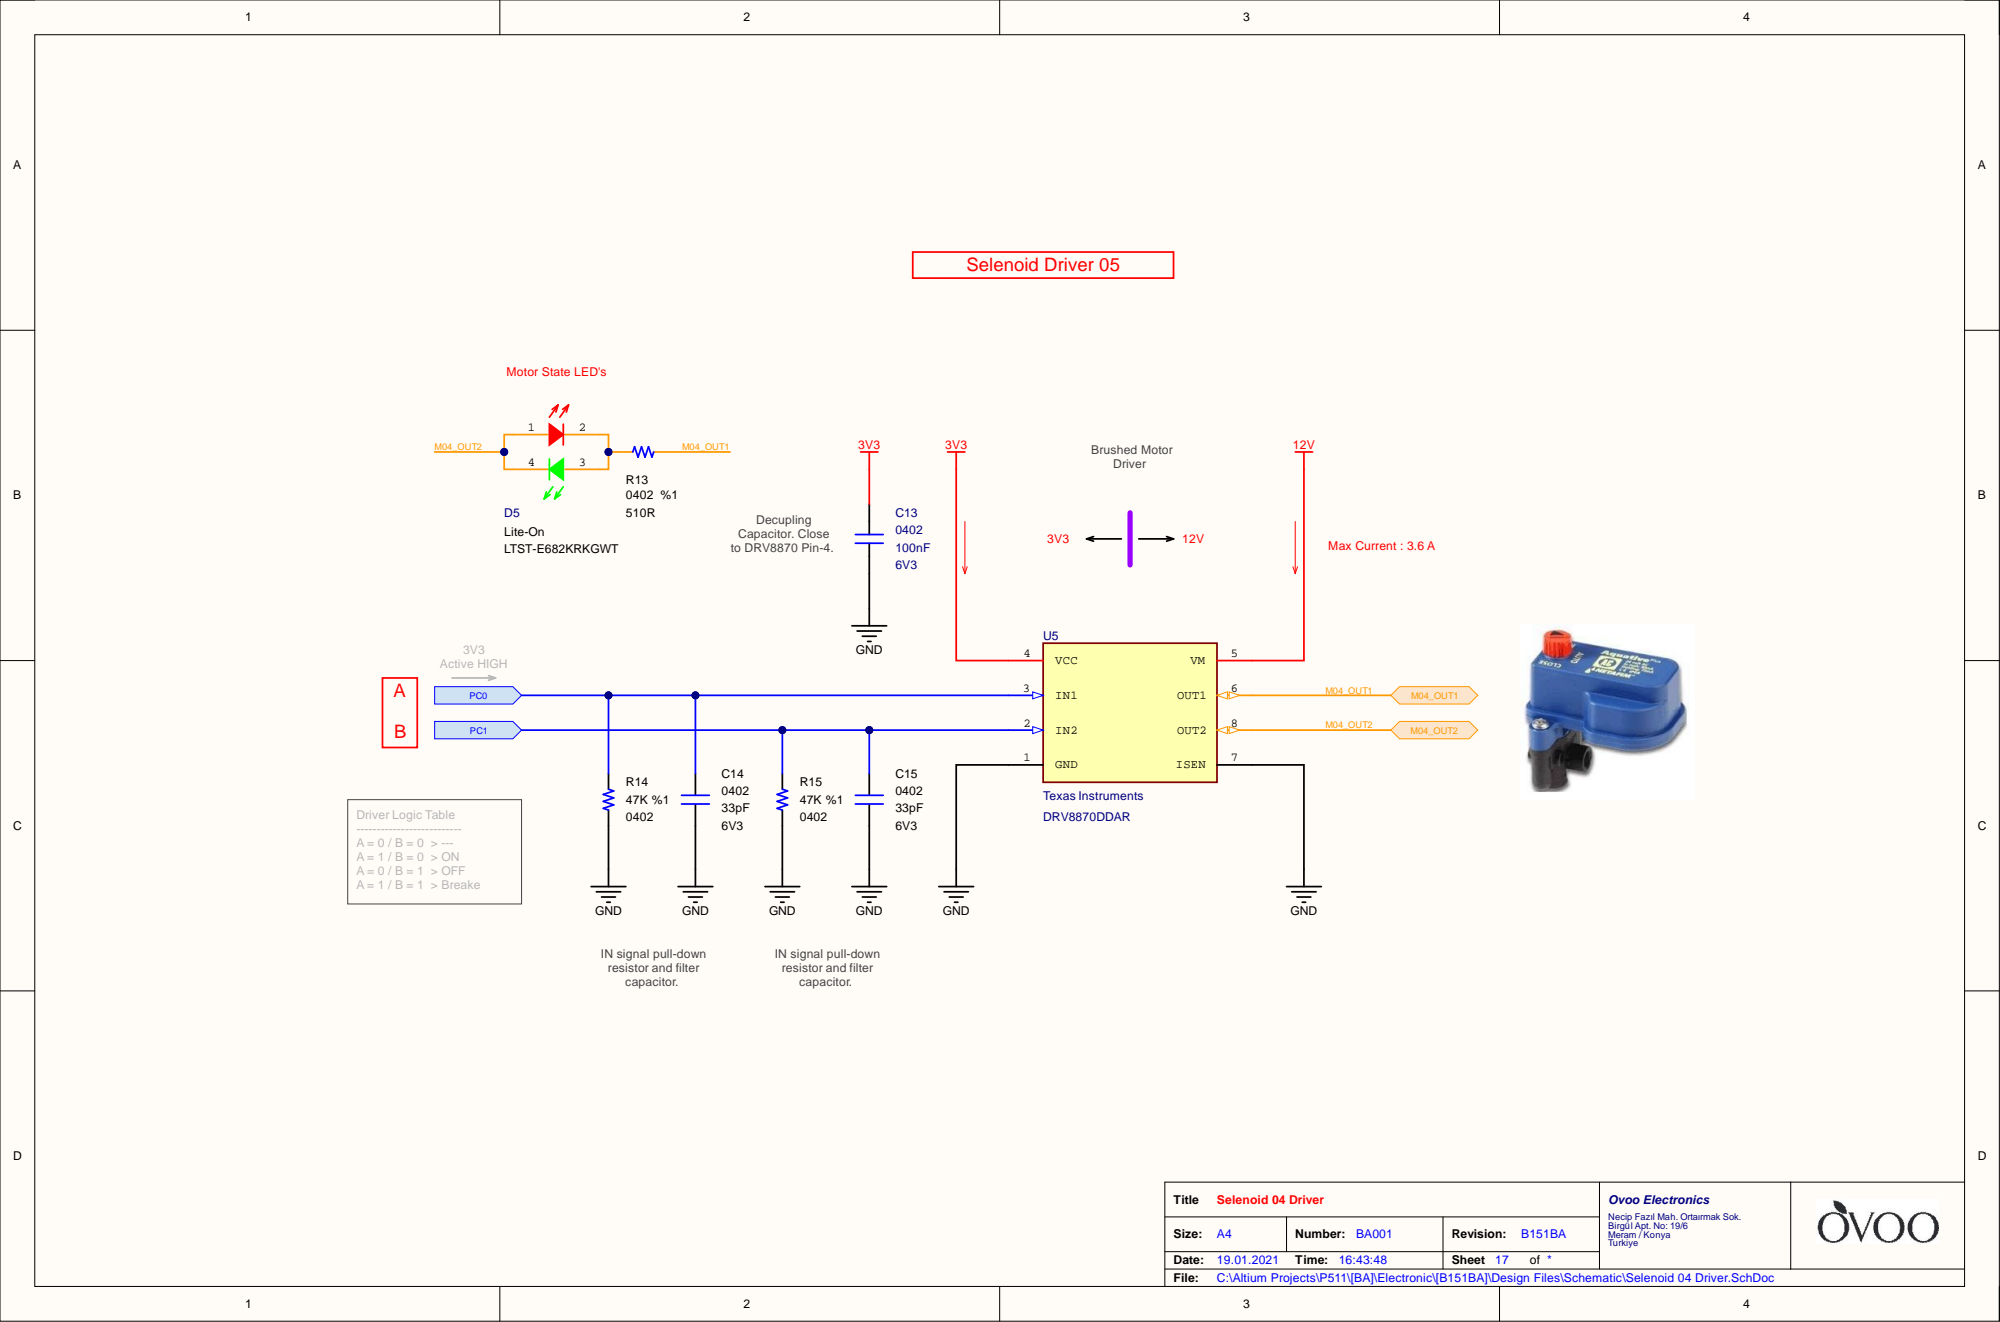
[picture p198: page 17]

IN signal pull-down
resistor and filter
capacitor.

C:\Altium Projects\P511\[BA]\Electronic\[B151BA]\Design Files\Schematic\Selenoid 04 Driver.SchDoc

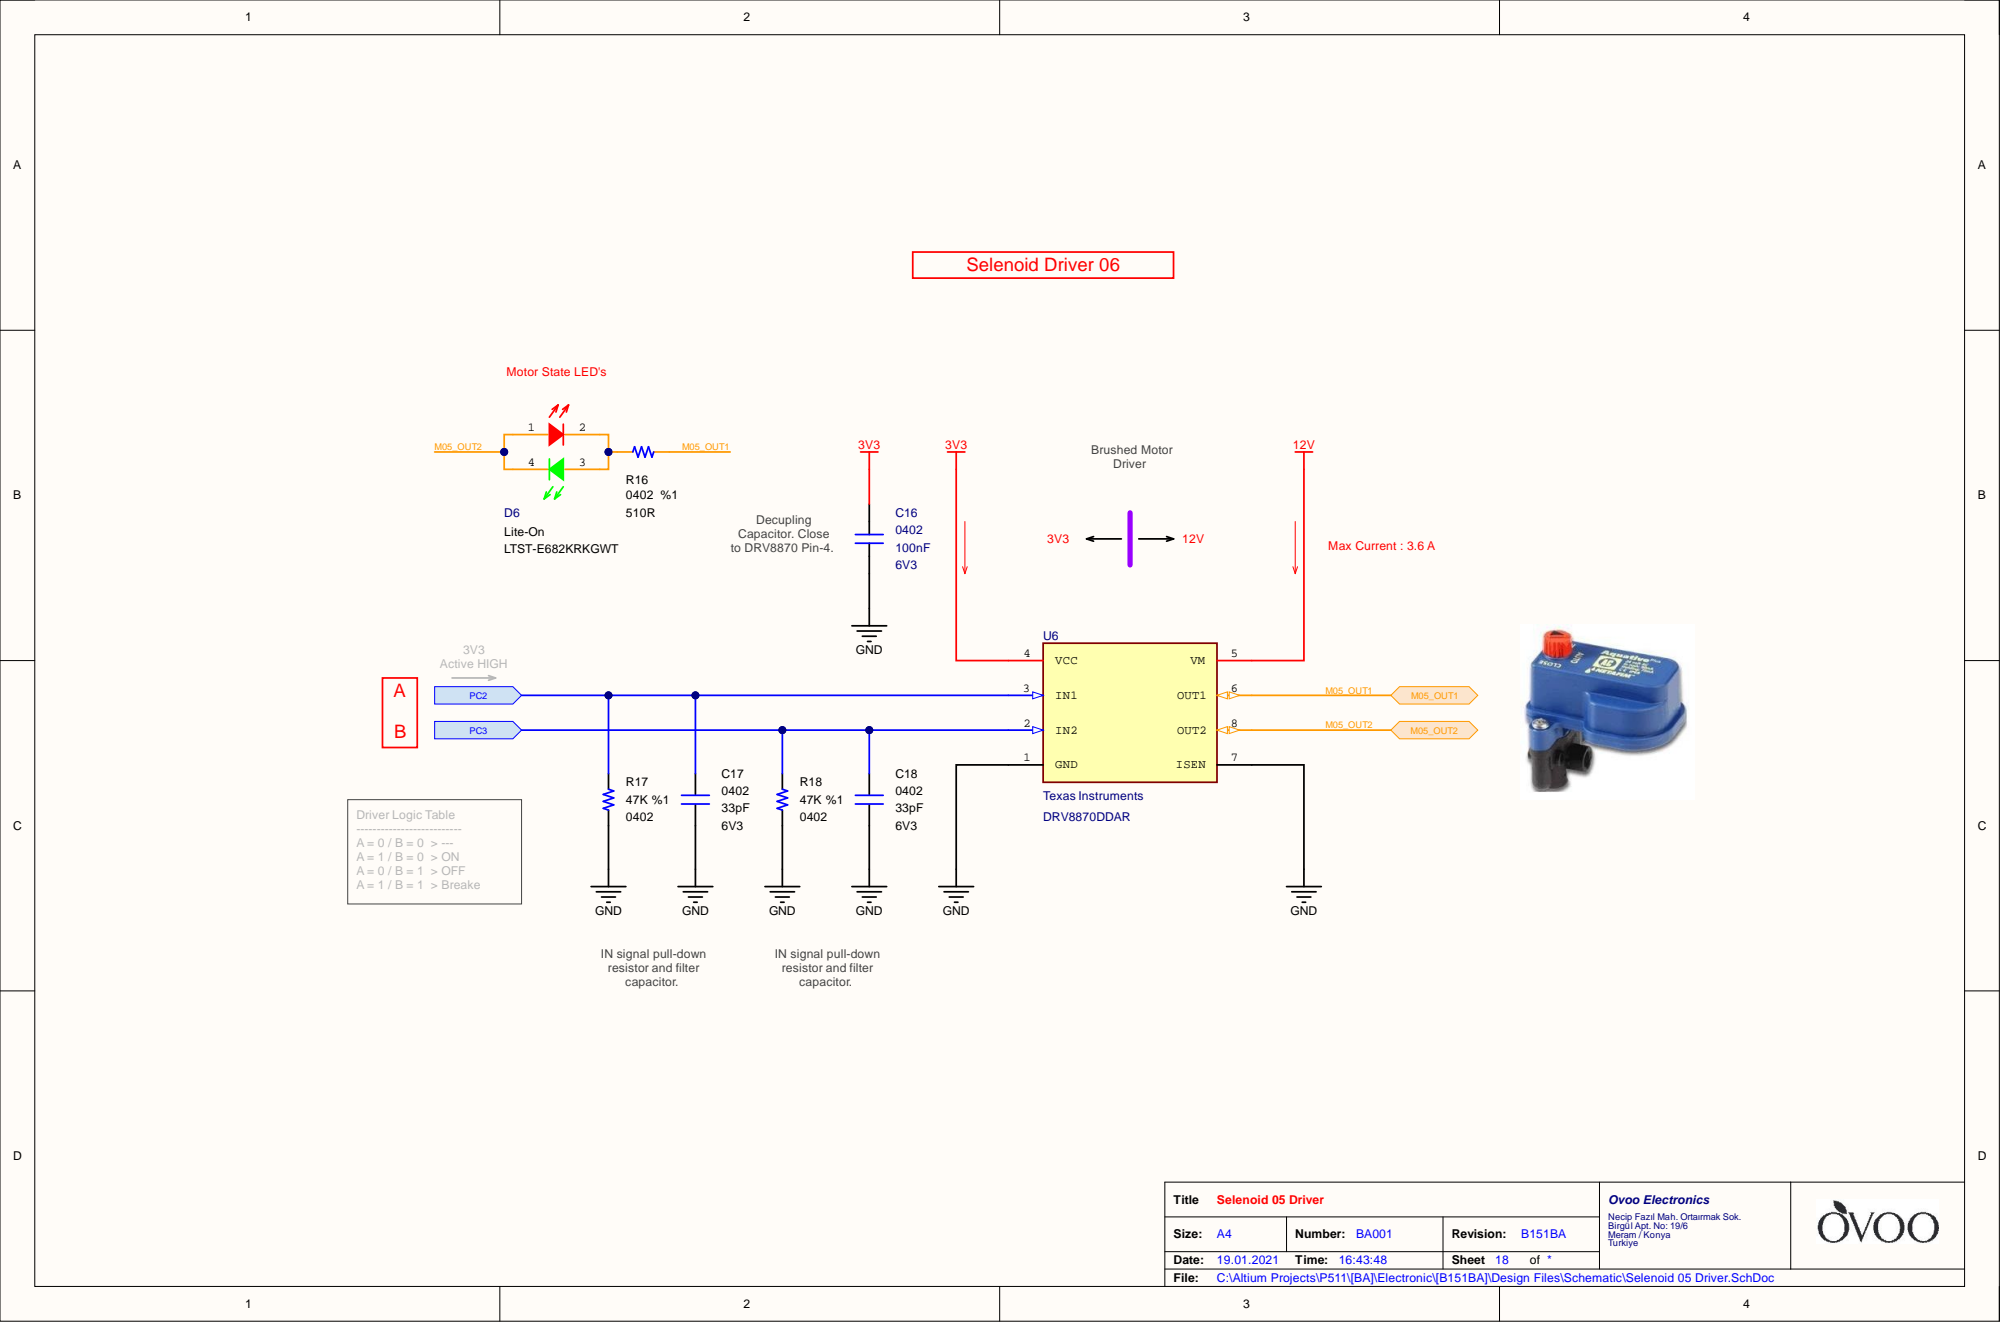
[picture p199: page 18]

IN signal pull-down
resistor and filter
capacitor.

C:\Altium Projects\P511\[BA]\Electronic\[B151BA]\Design Files\Schematic\Selenoid 05 Driver.SchDoc

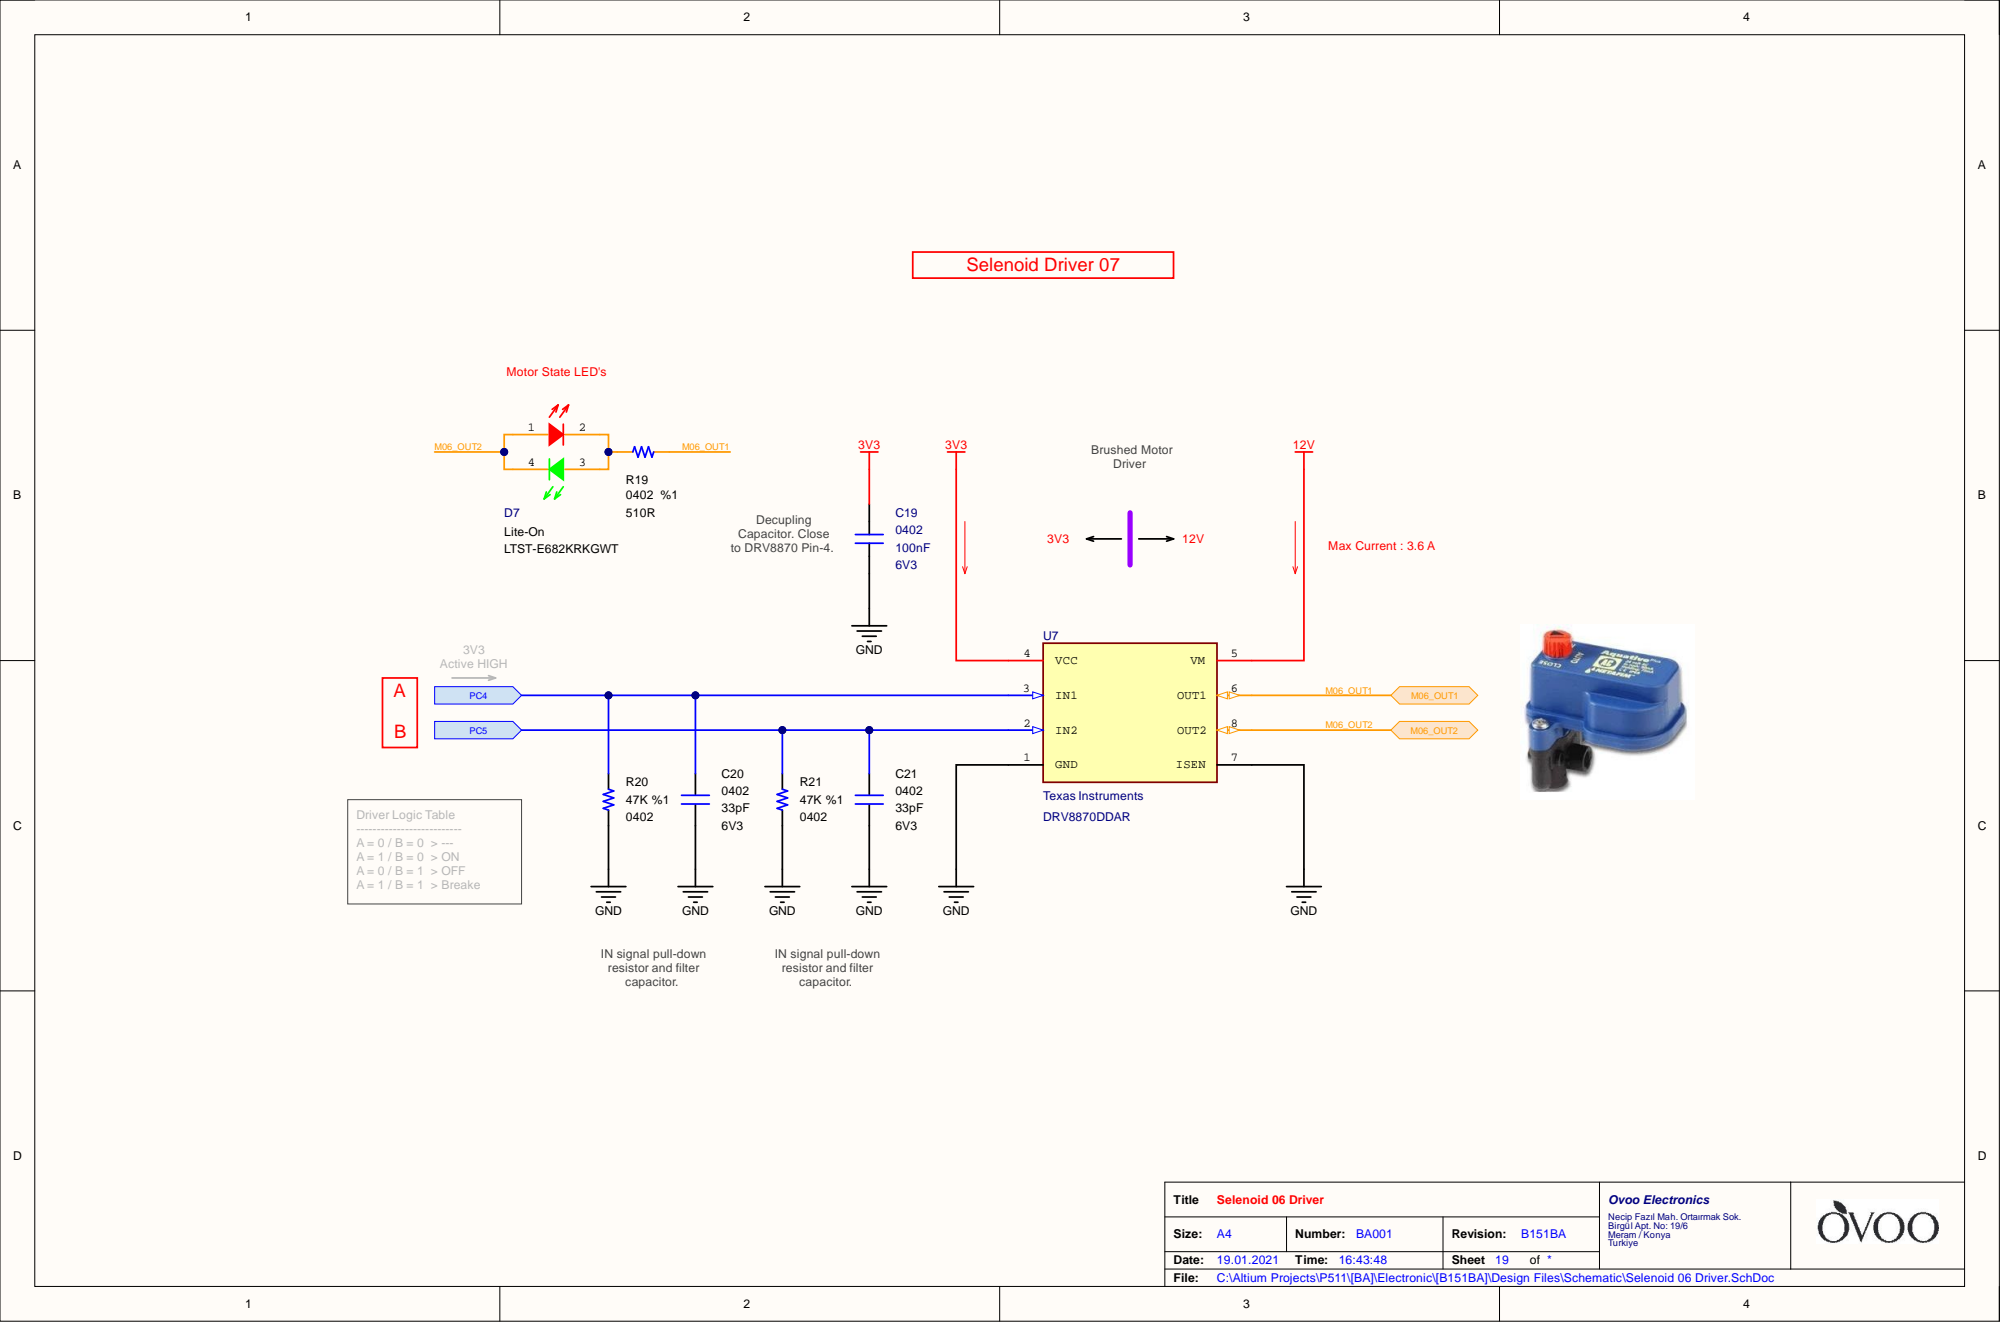
[picture p200: page 19]

IN signal pull-down
resistor and filter
capacitor.

C:\Altium Projects\P511\[BA]\Electronic\[B151BA]\Design Files\Schematic\Selenoid 06 Driver.SchDoc

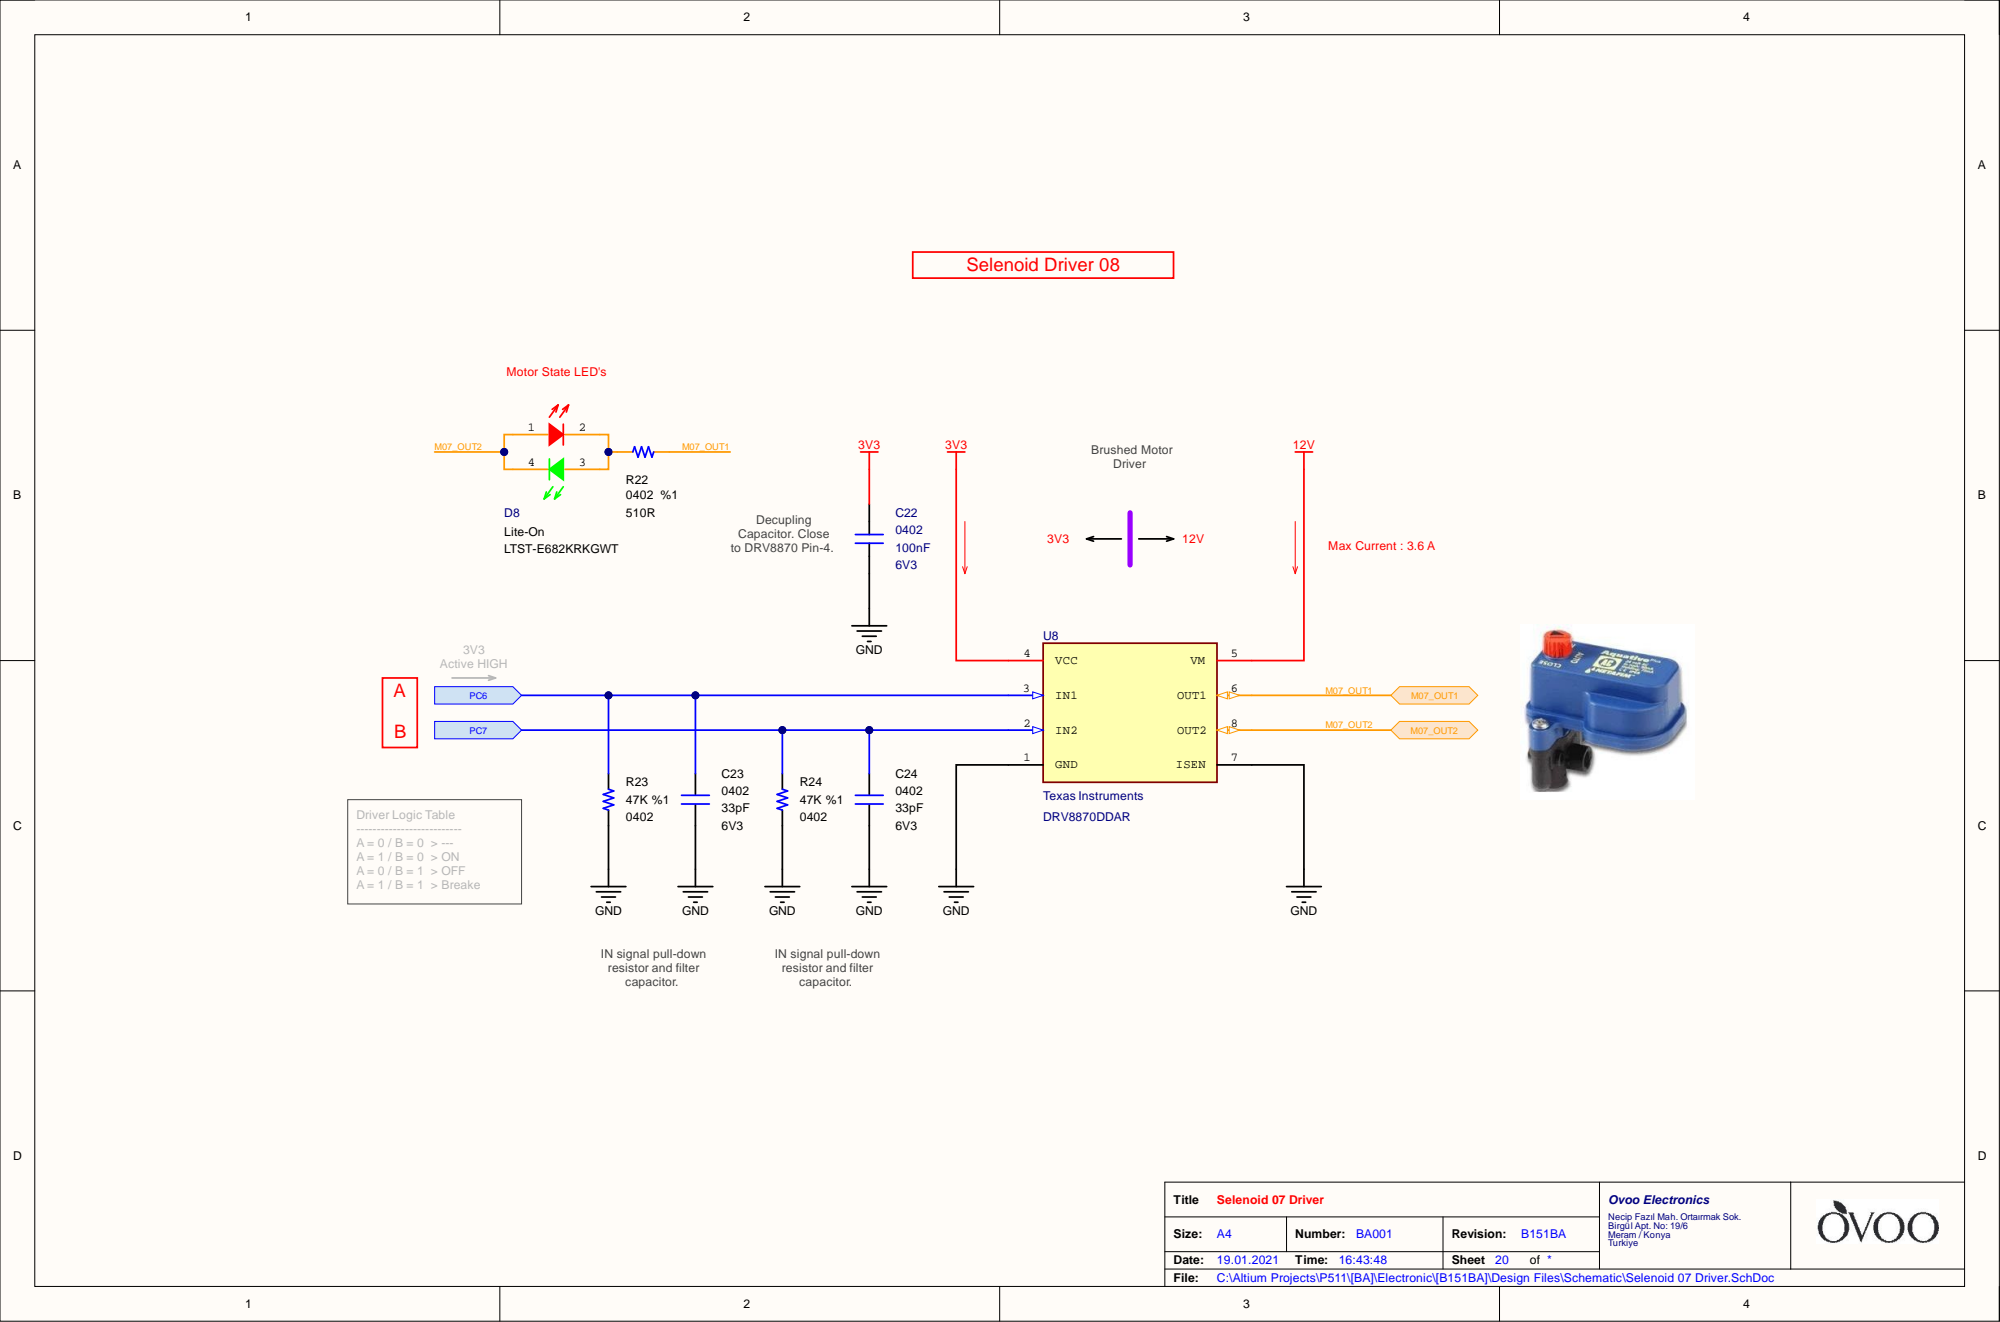
[picture p201: page 20]

IN signal pull-down
resistor and filter
capacitor.

C:\Altium Projects\P511\[BA]\Electronic\[B151BA]\Design Files\Schematic\Selenoid 07 Driver.SchDoc

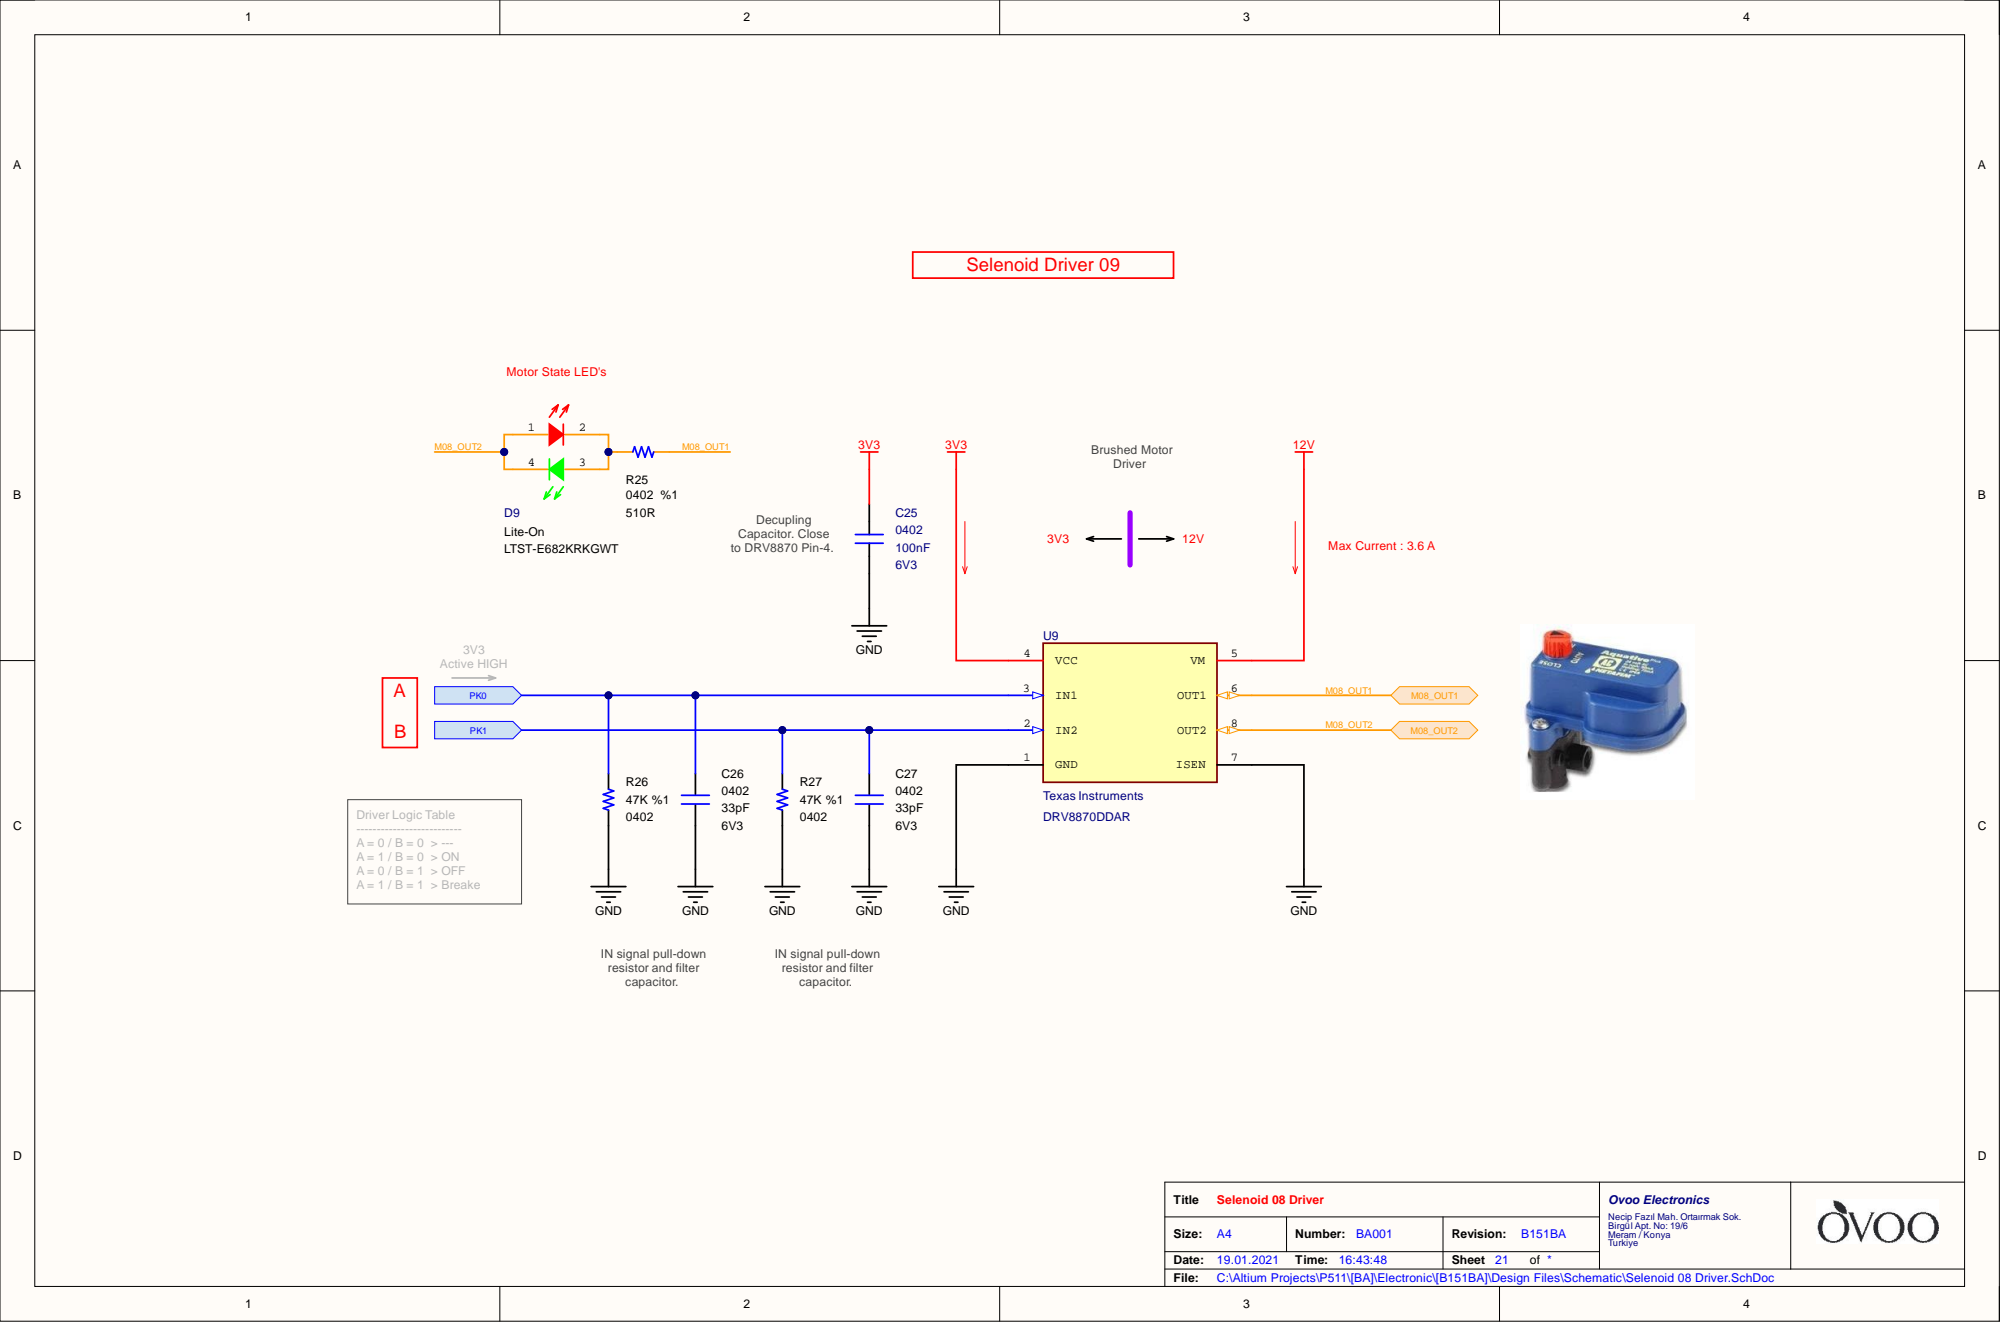
[picture p202: page 21]

IN signal pull-down
resistor and filter
capacitor.

C:\Altium Projects\P511\[BA]\Electronic\[B151BA]\Design Files\Schematic\Selenoid 08 Driver.SchDoc

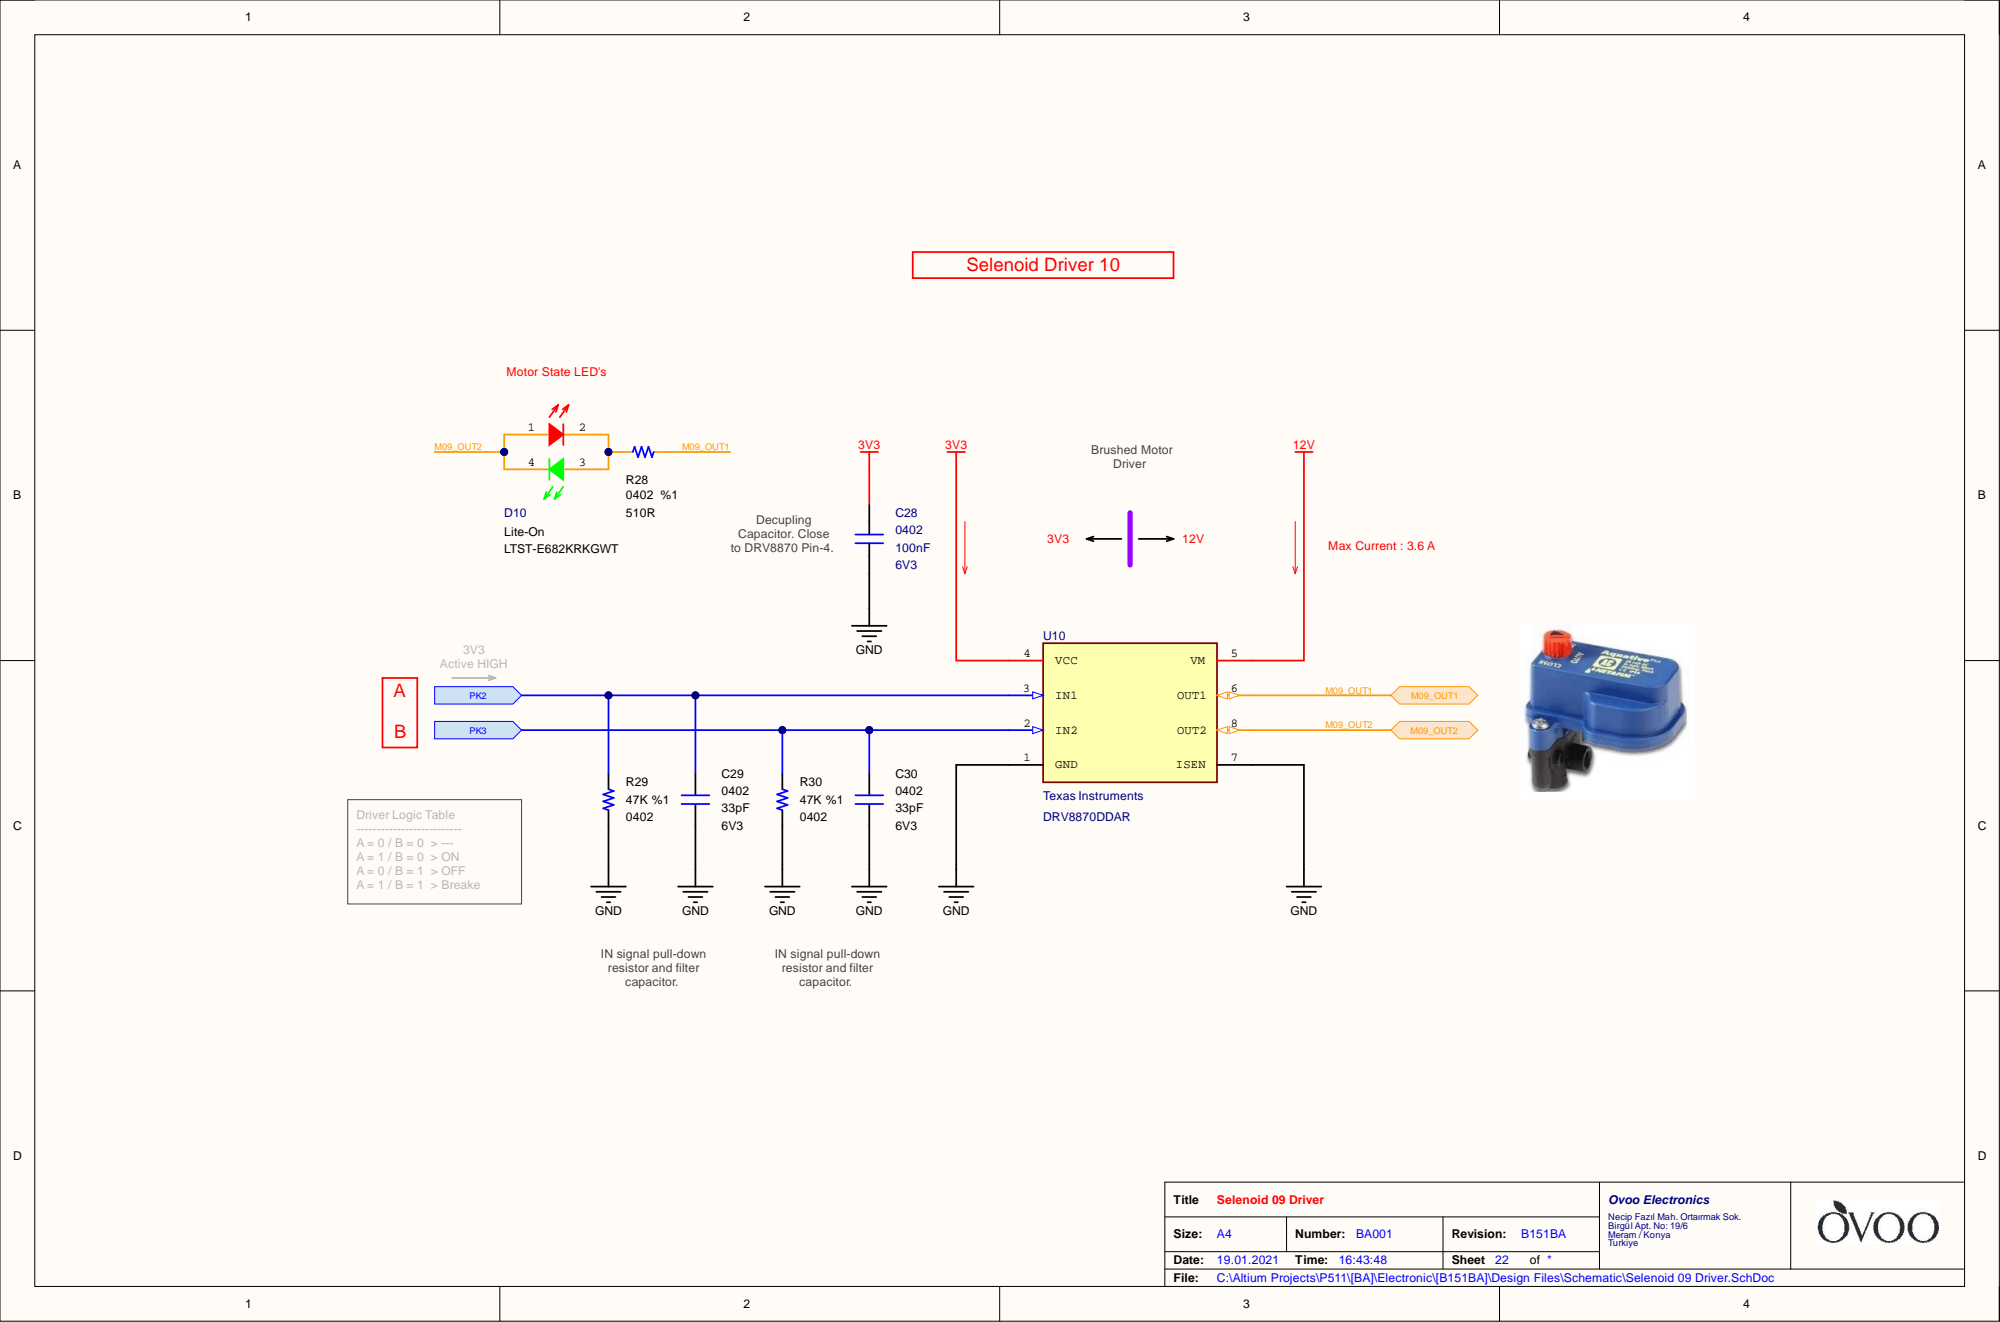
[picture p203: page 22]

IN signal pull-down
resistor and filter
capacitor.

C:\Altium Projects\P511\[BA]\Electronic\[B151BA]\Design Files\Schematic\Selenoid 09 Driver.SchDoc

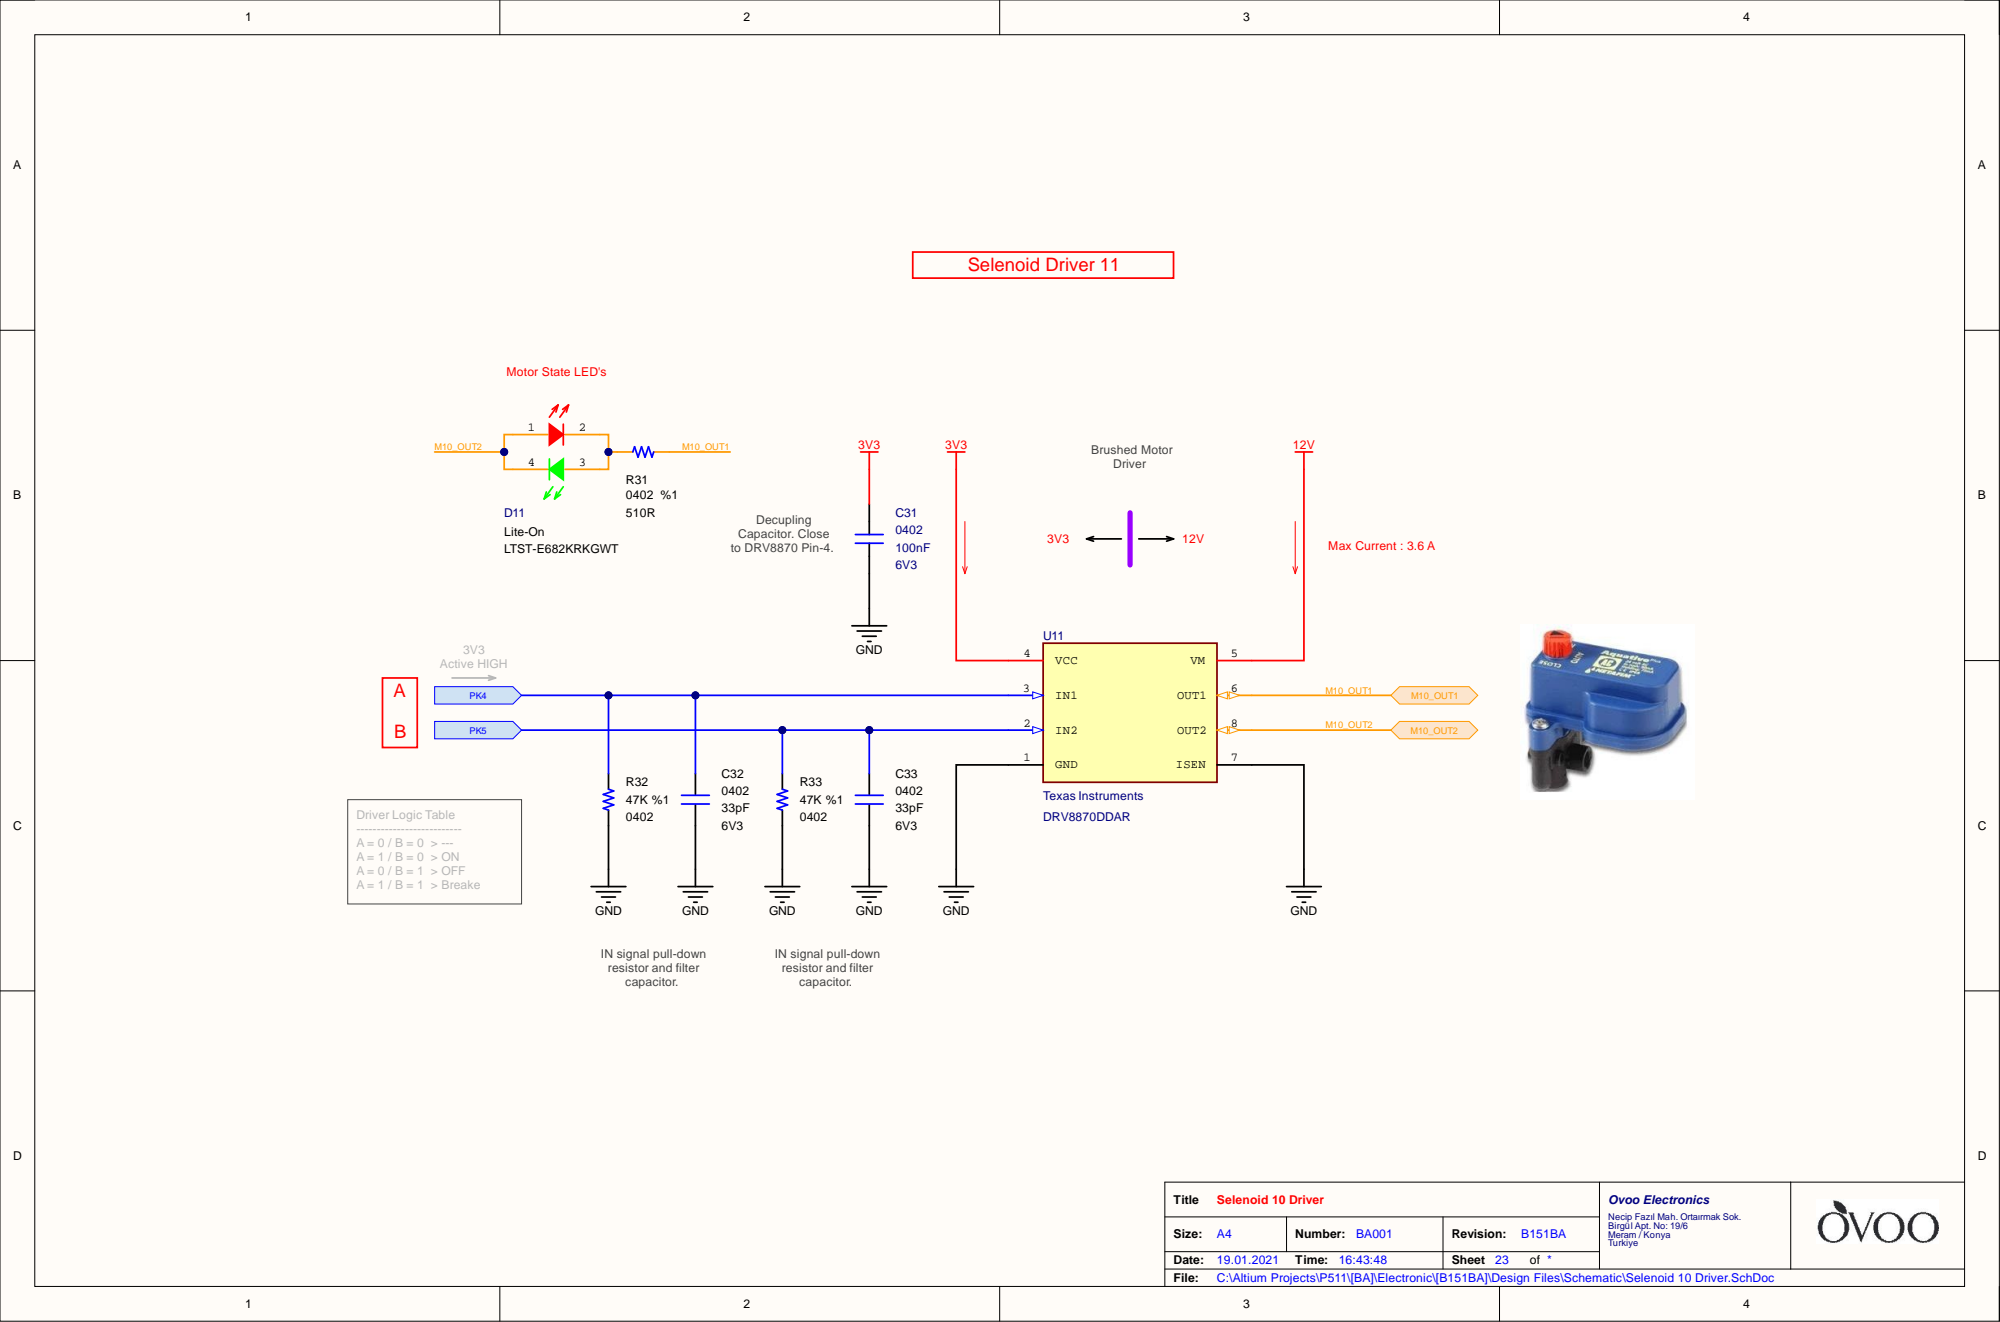
[picture p204: page 23]

IN signal pull-down
resistor and filter
capacitor.

C:\Altium Projects\P511\[BA]\Electronic\[B151BA]\Design Files\Schematic\Selenoid 10 Driver.SchDoc

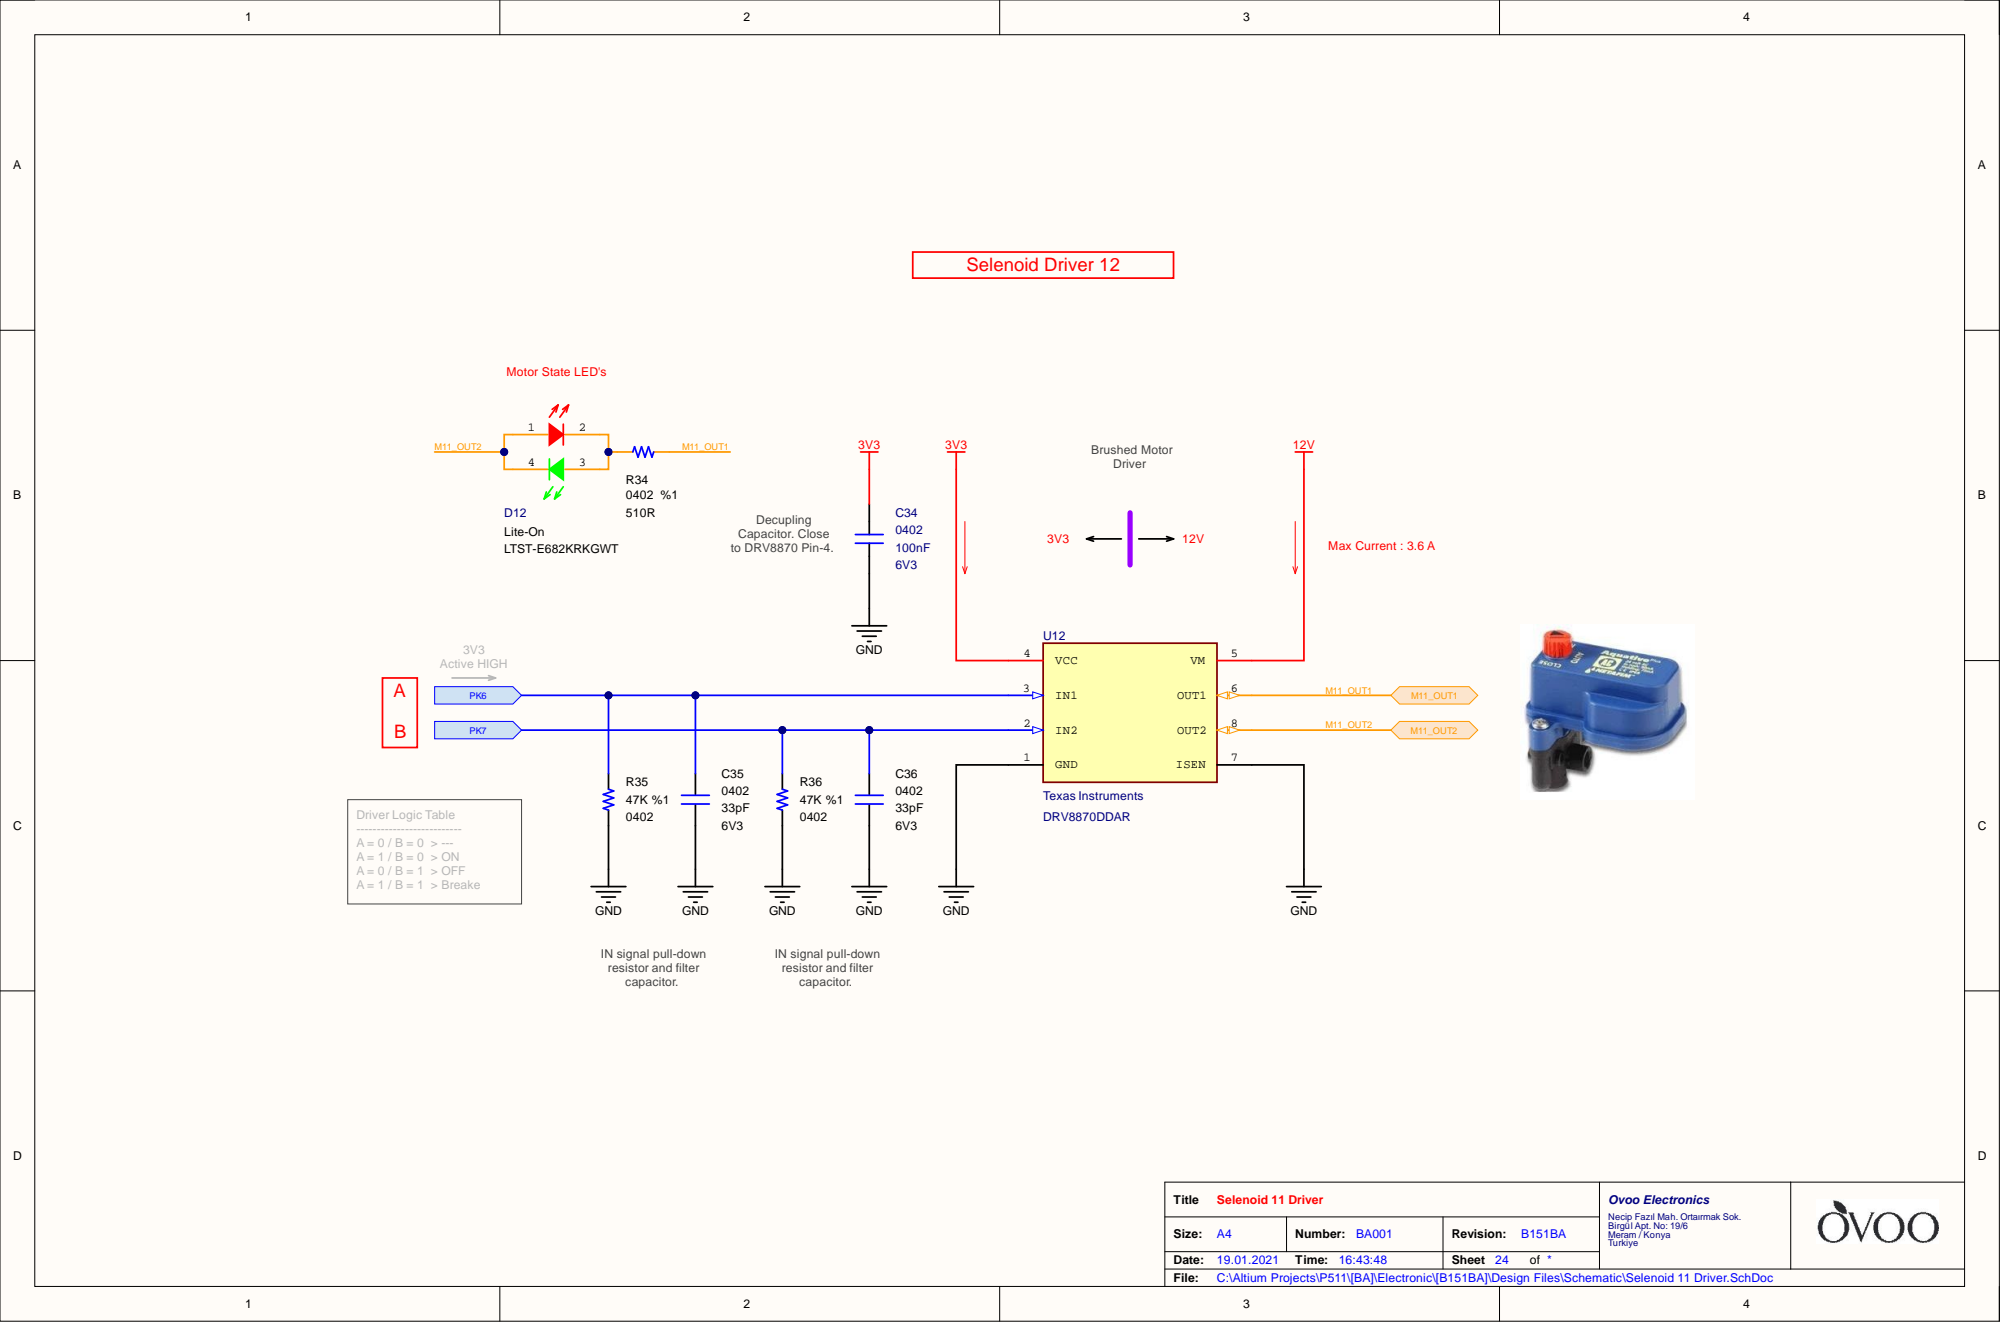
[picture p205: page 24]

IN signal pull-down
resistor and filter
capacitor.

C:\Altium Projects\P511\[BA]\Electronic\[B151BA]\Design Files\Schematic\Selenoid 11 Driver.SchDoc

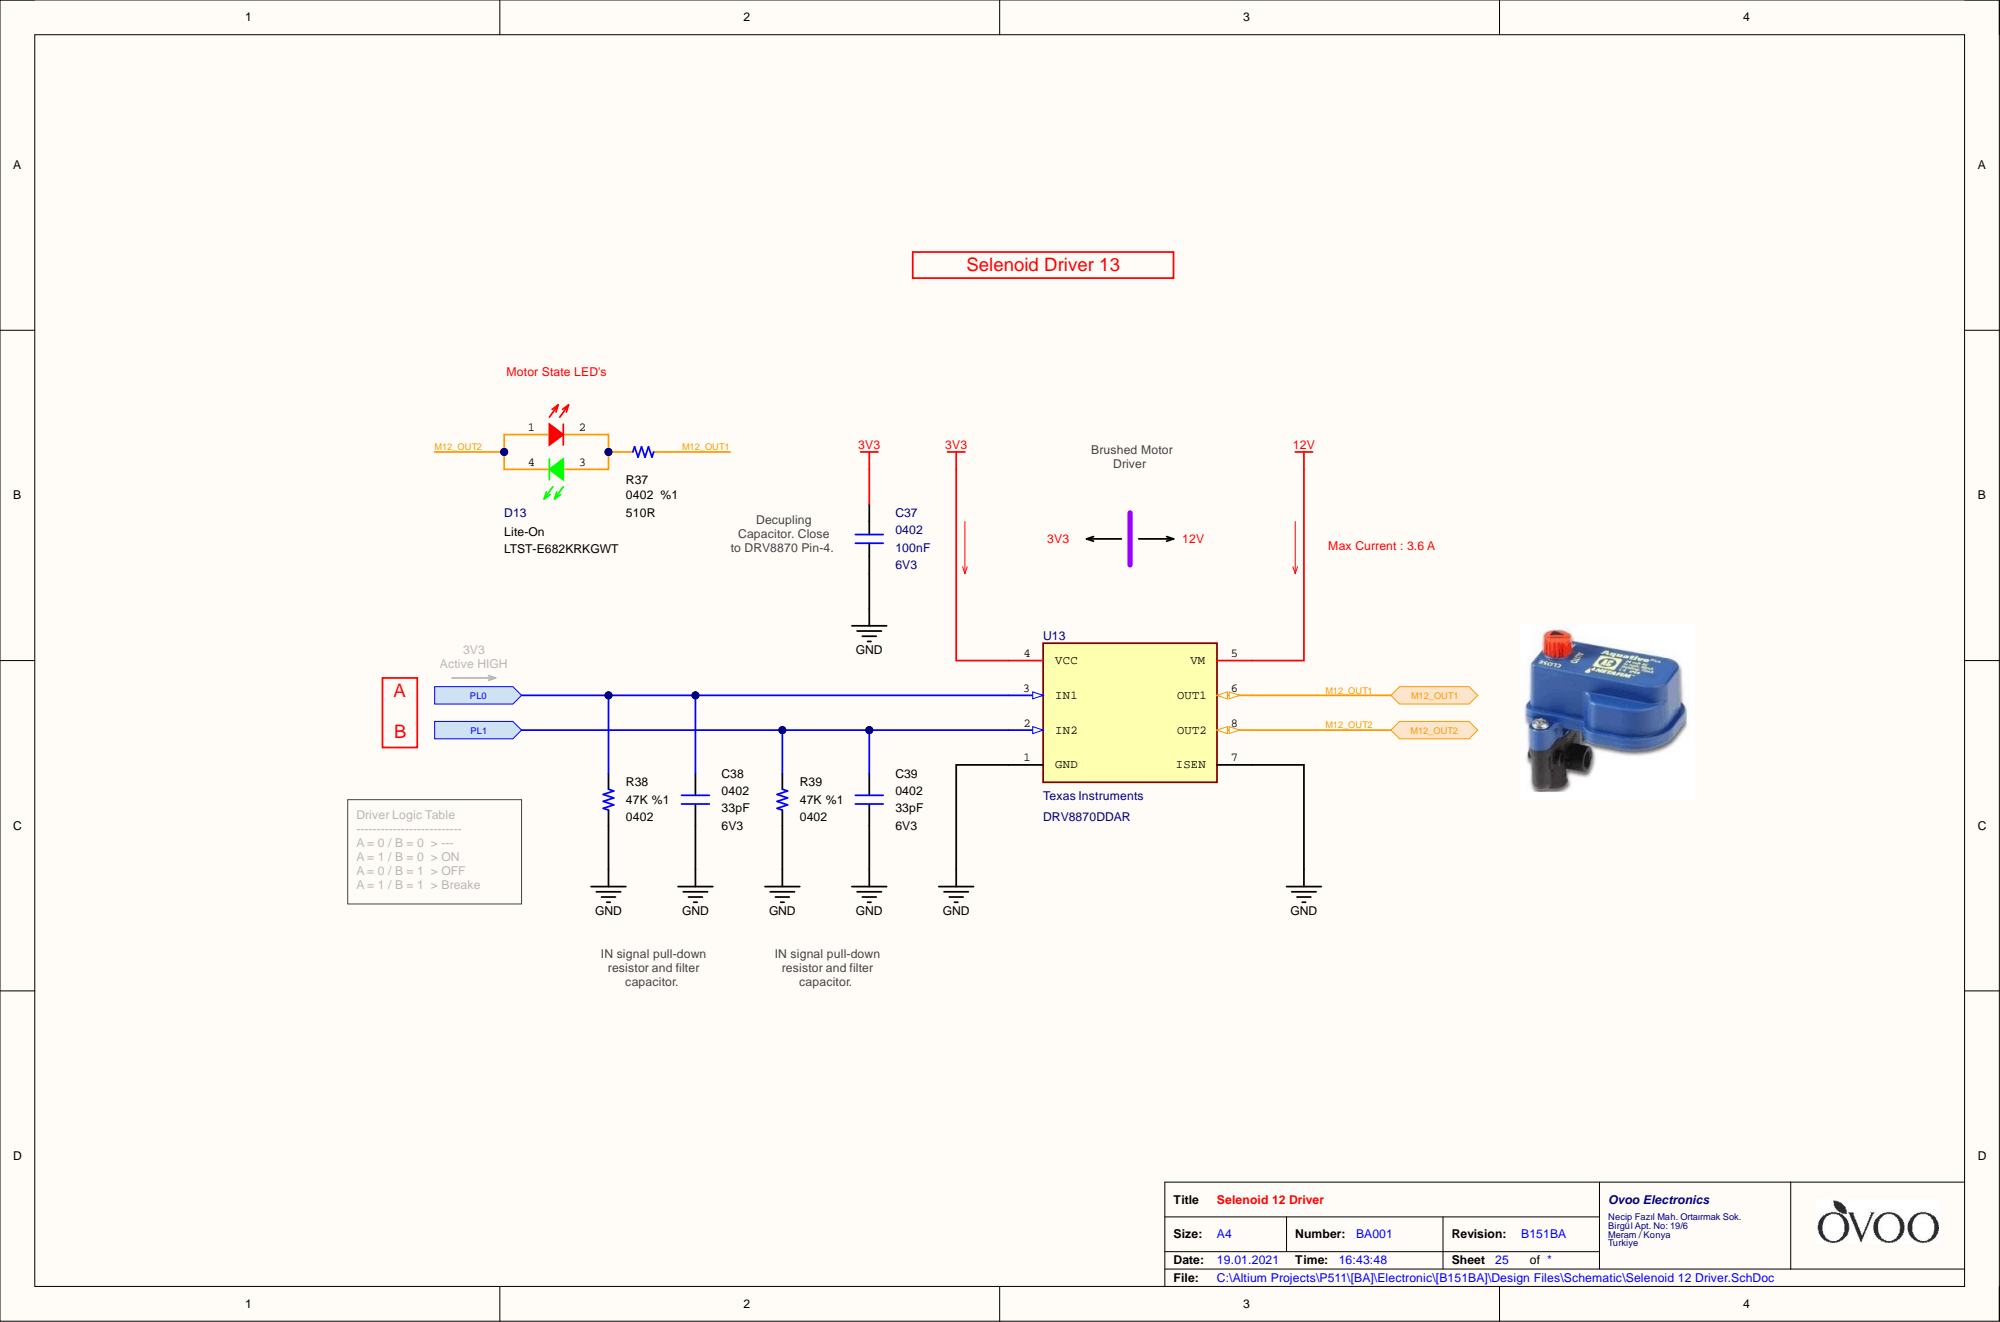
[picture p206: page 25]

IN signal pull-down
resistor and filter
capacitor.

C:\Altium Projects\P511\[BA]\Electronic\[B151BA]\Design Files\Schematic\Selenoid 12 Driver.SchDoc

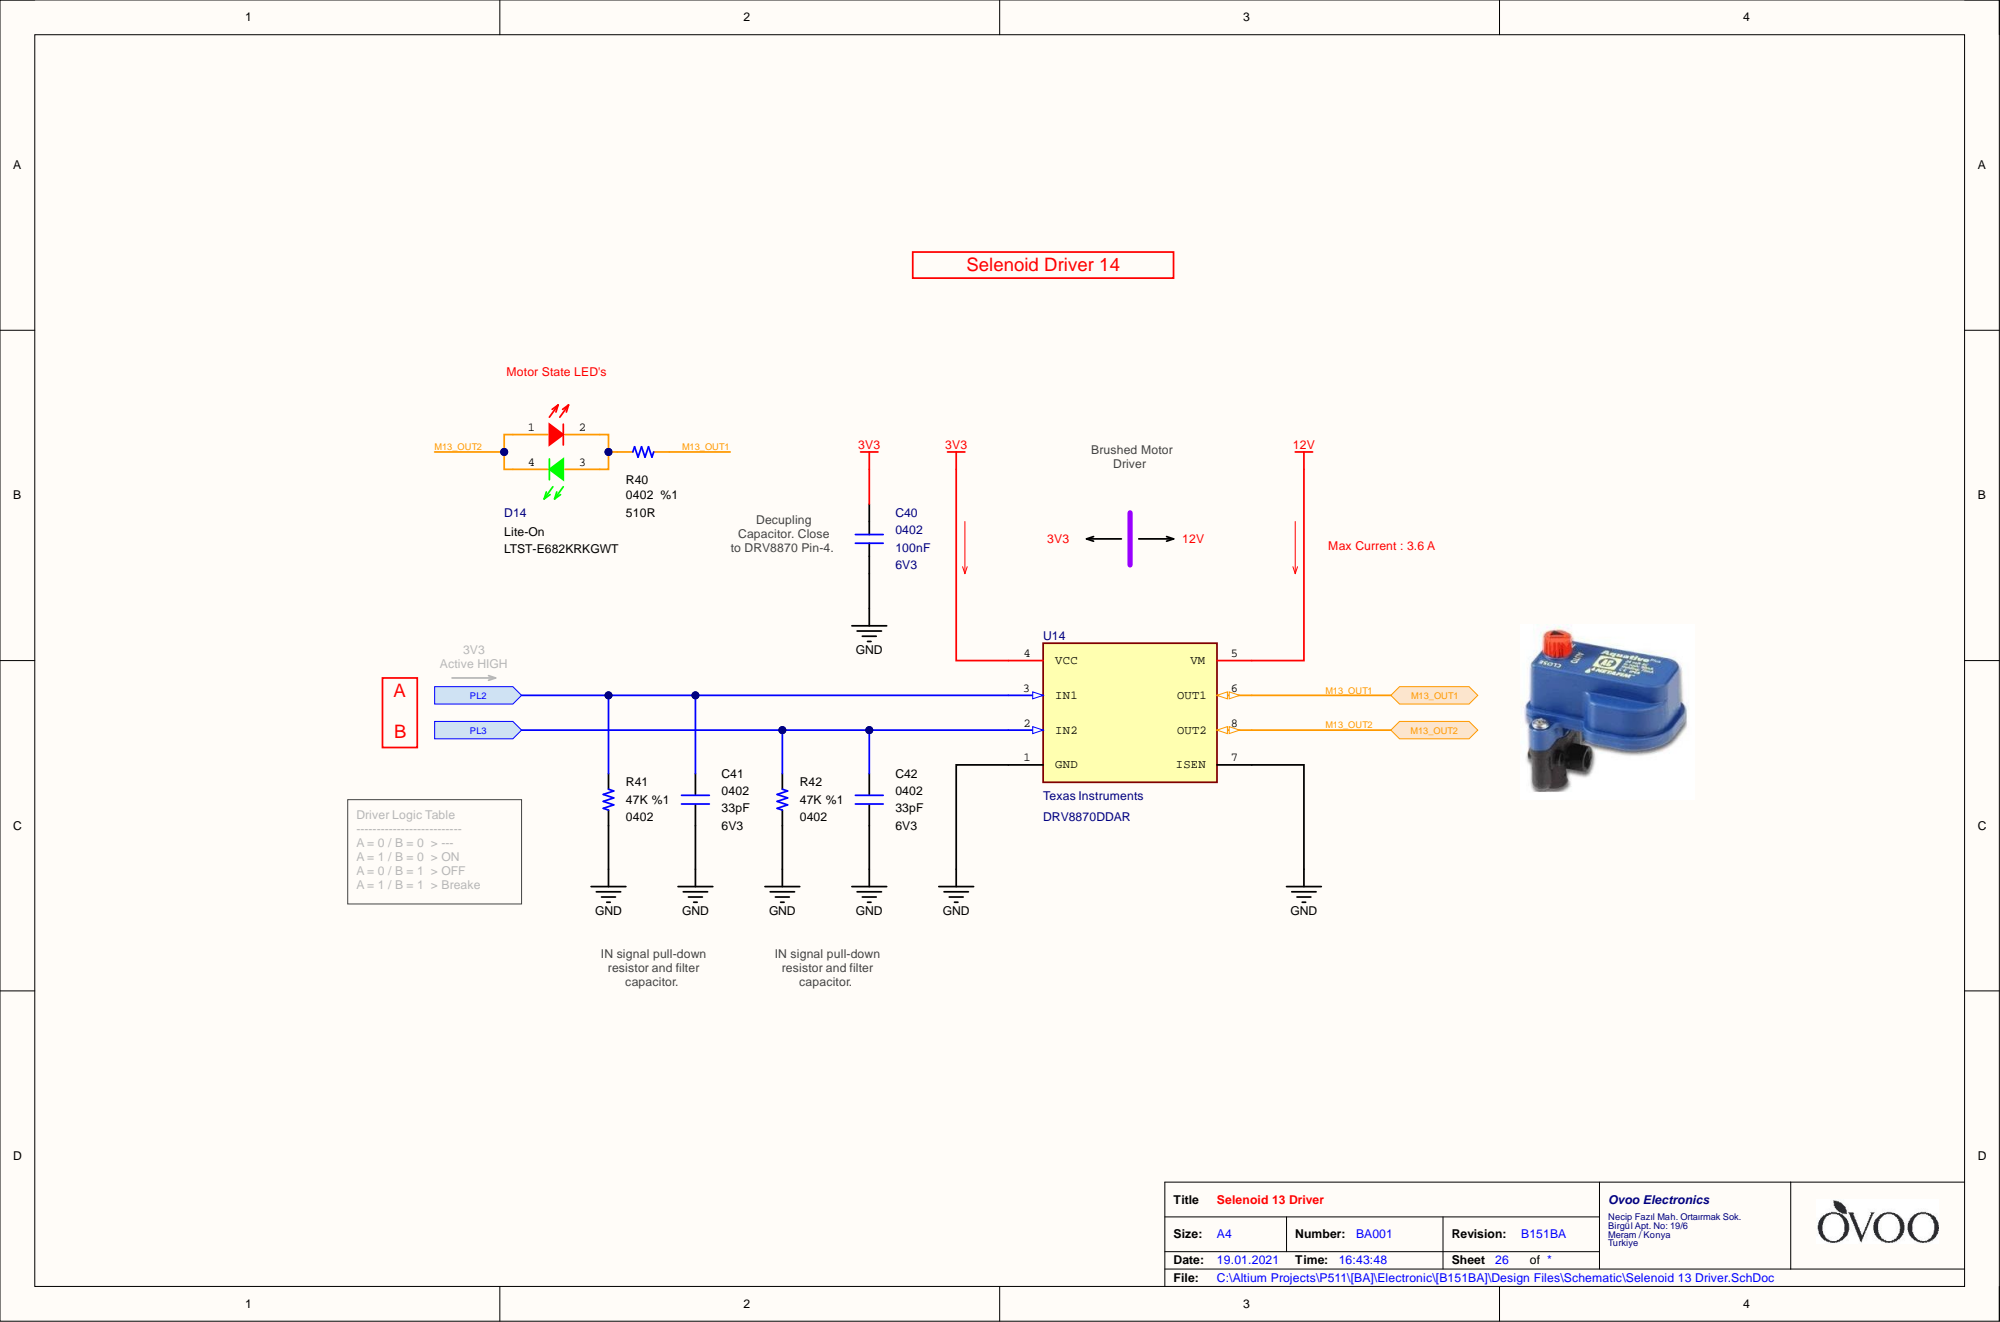
[picture p207: page 26]

IN signal pull-down
resistor and filter
capacitor.

C:\Altium Projects\P511\[BA]\Electronic\[B151BA]\Design Files\Schematic\Selenoid 13 Driver.SchDoc

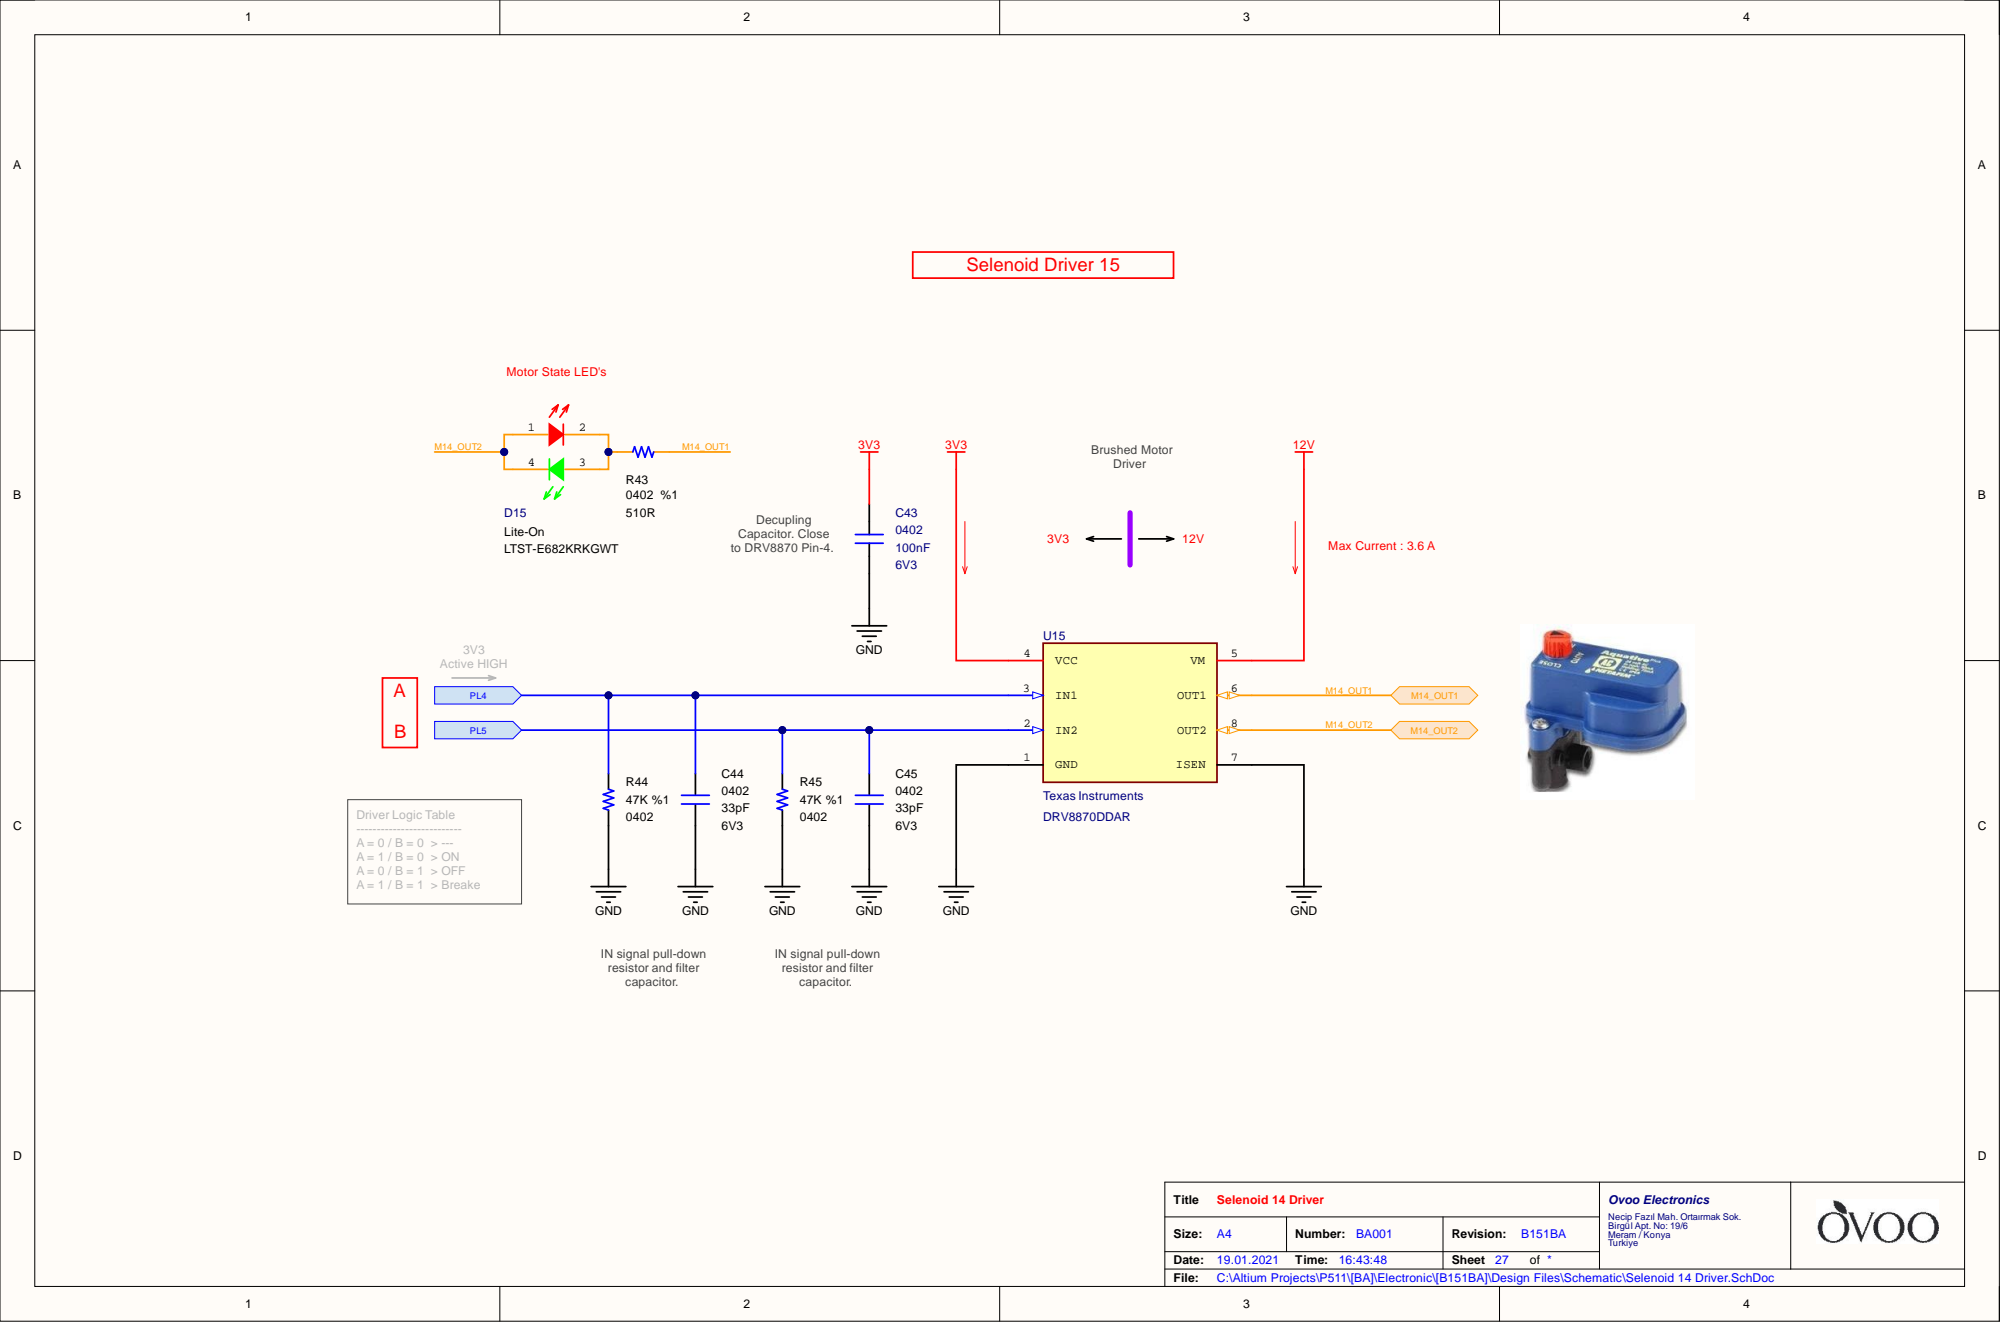
[picture p208: page 27]

IN signal pull-down
resistor and filter
capacitor.

C:\Altium Projects\P511\[BA]\Electronic\[B151BA]\Design Files\Schematic\Selenoid 14 Driver.SchDoc

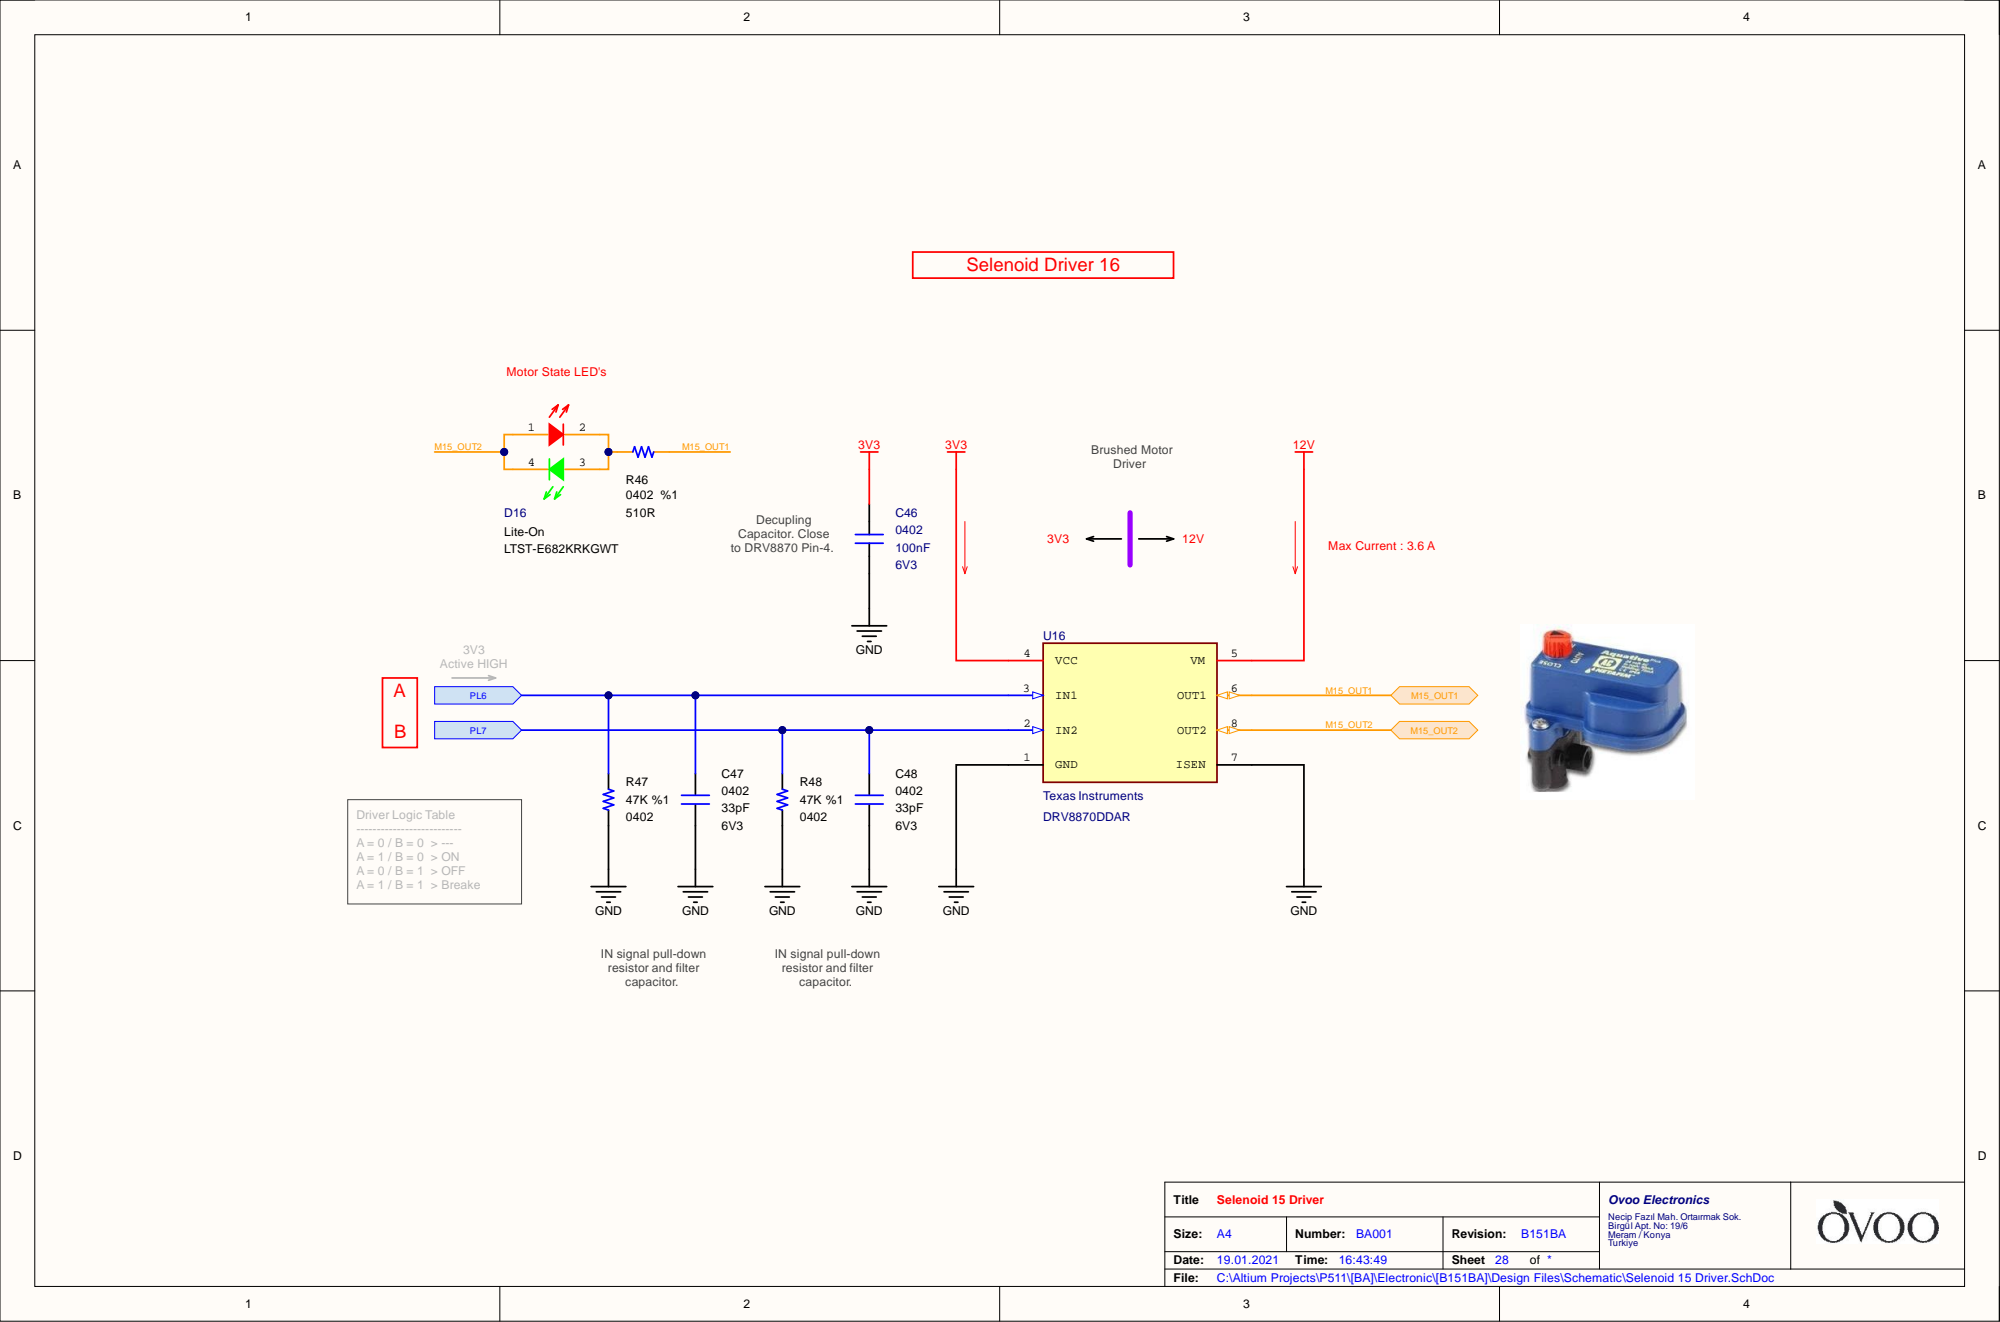
[picture p209: page 28]

IN signal pull-down
resistor and filter
capacitor.

C:\Altium Projects\P511\[BA]\Electronic\[B151BA]\Design Files\Schematic\Selenoid 15 Driver.SchDoc

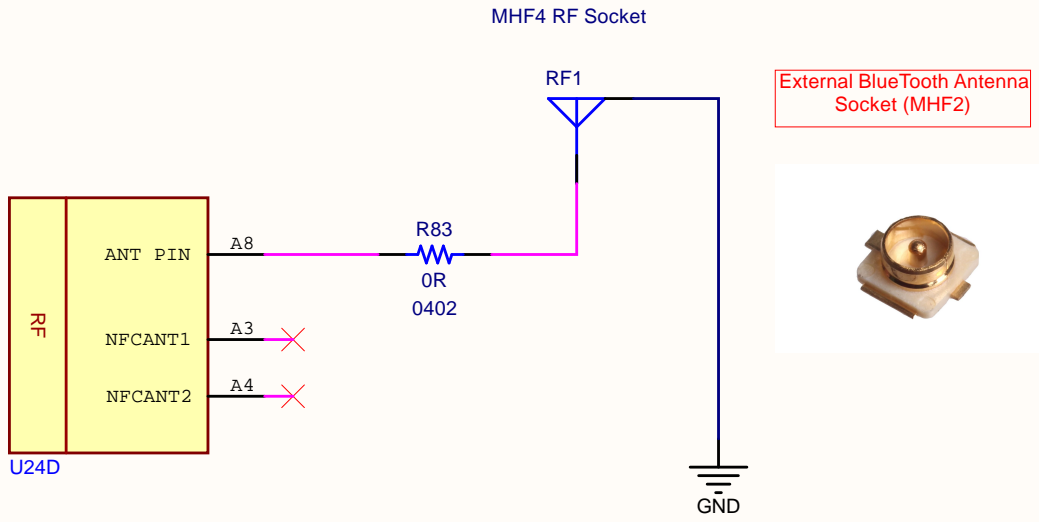
[picture p210: page 29]

C:\Altium Projects\P511\[BA]\Electronic\[B151BA]\Design Files\Schematic\BlueMod+S50 Antenna.SchDoc

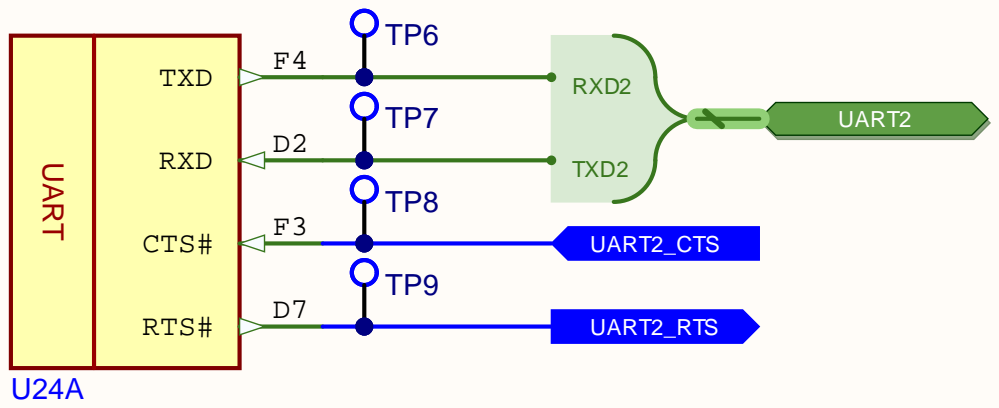
[picture p211: page 30]

C:\Altium Projects\P511\[BA]\Electronic\[B151BA]\Design Files\Schematic\BlueMod+S50 Communicatiın.SchDoc

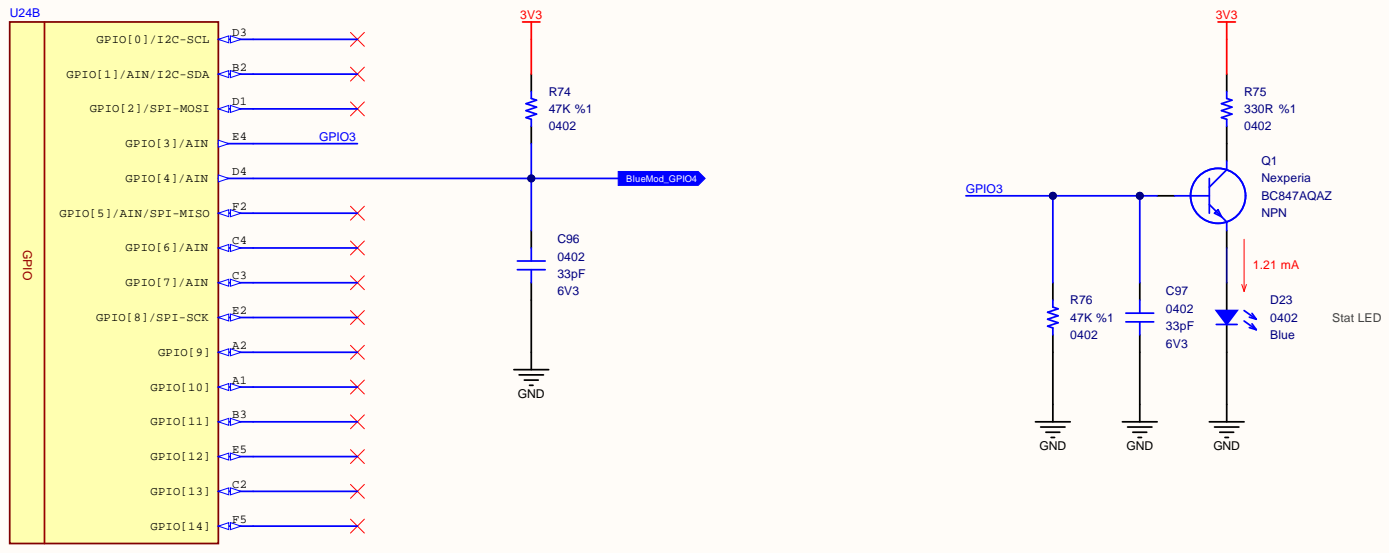
[picture p212: page 31]

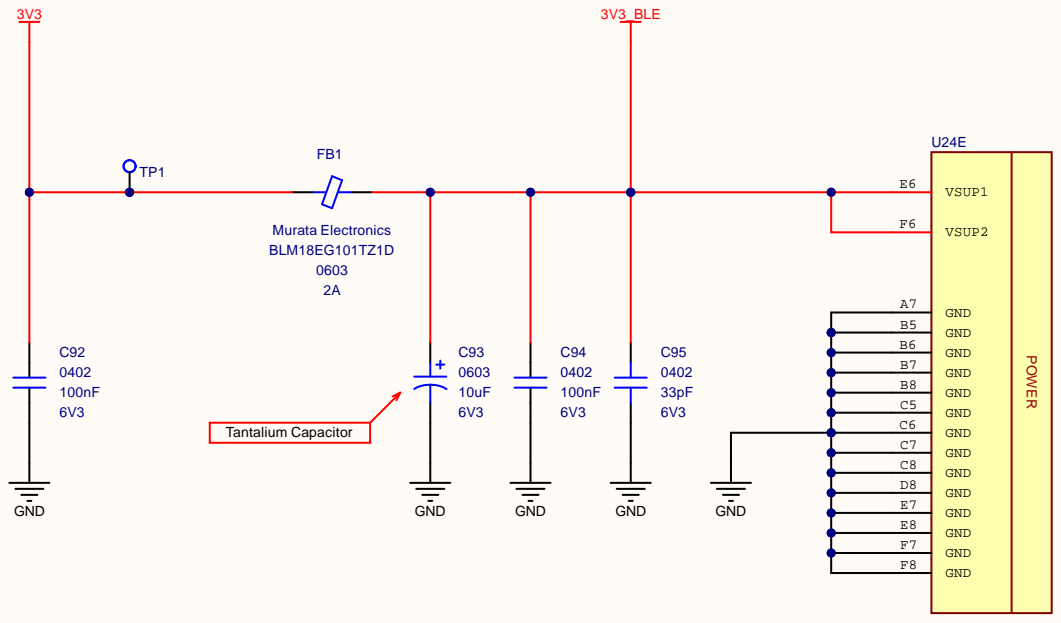
[picture p213: page 32]

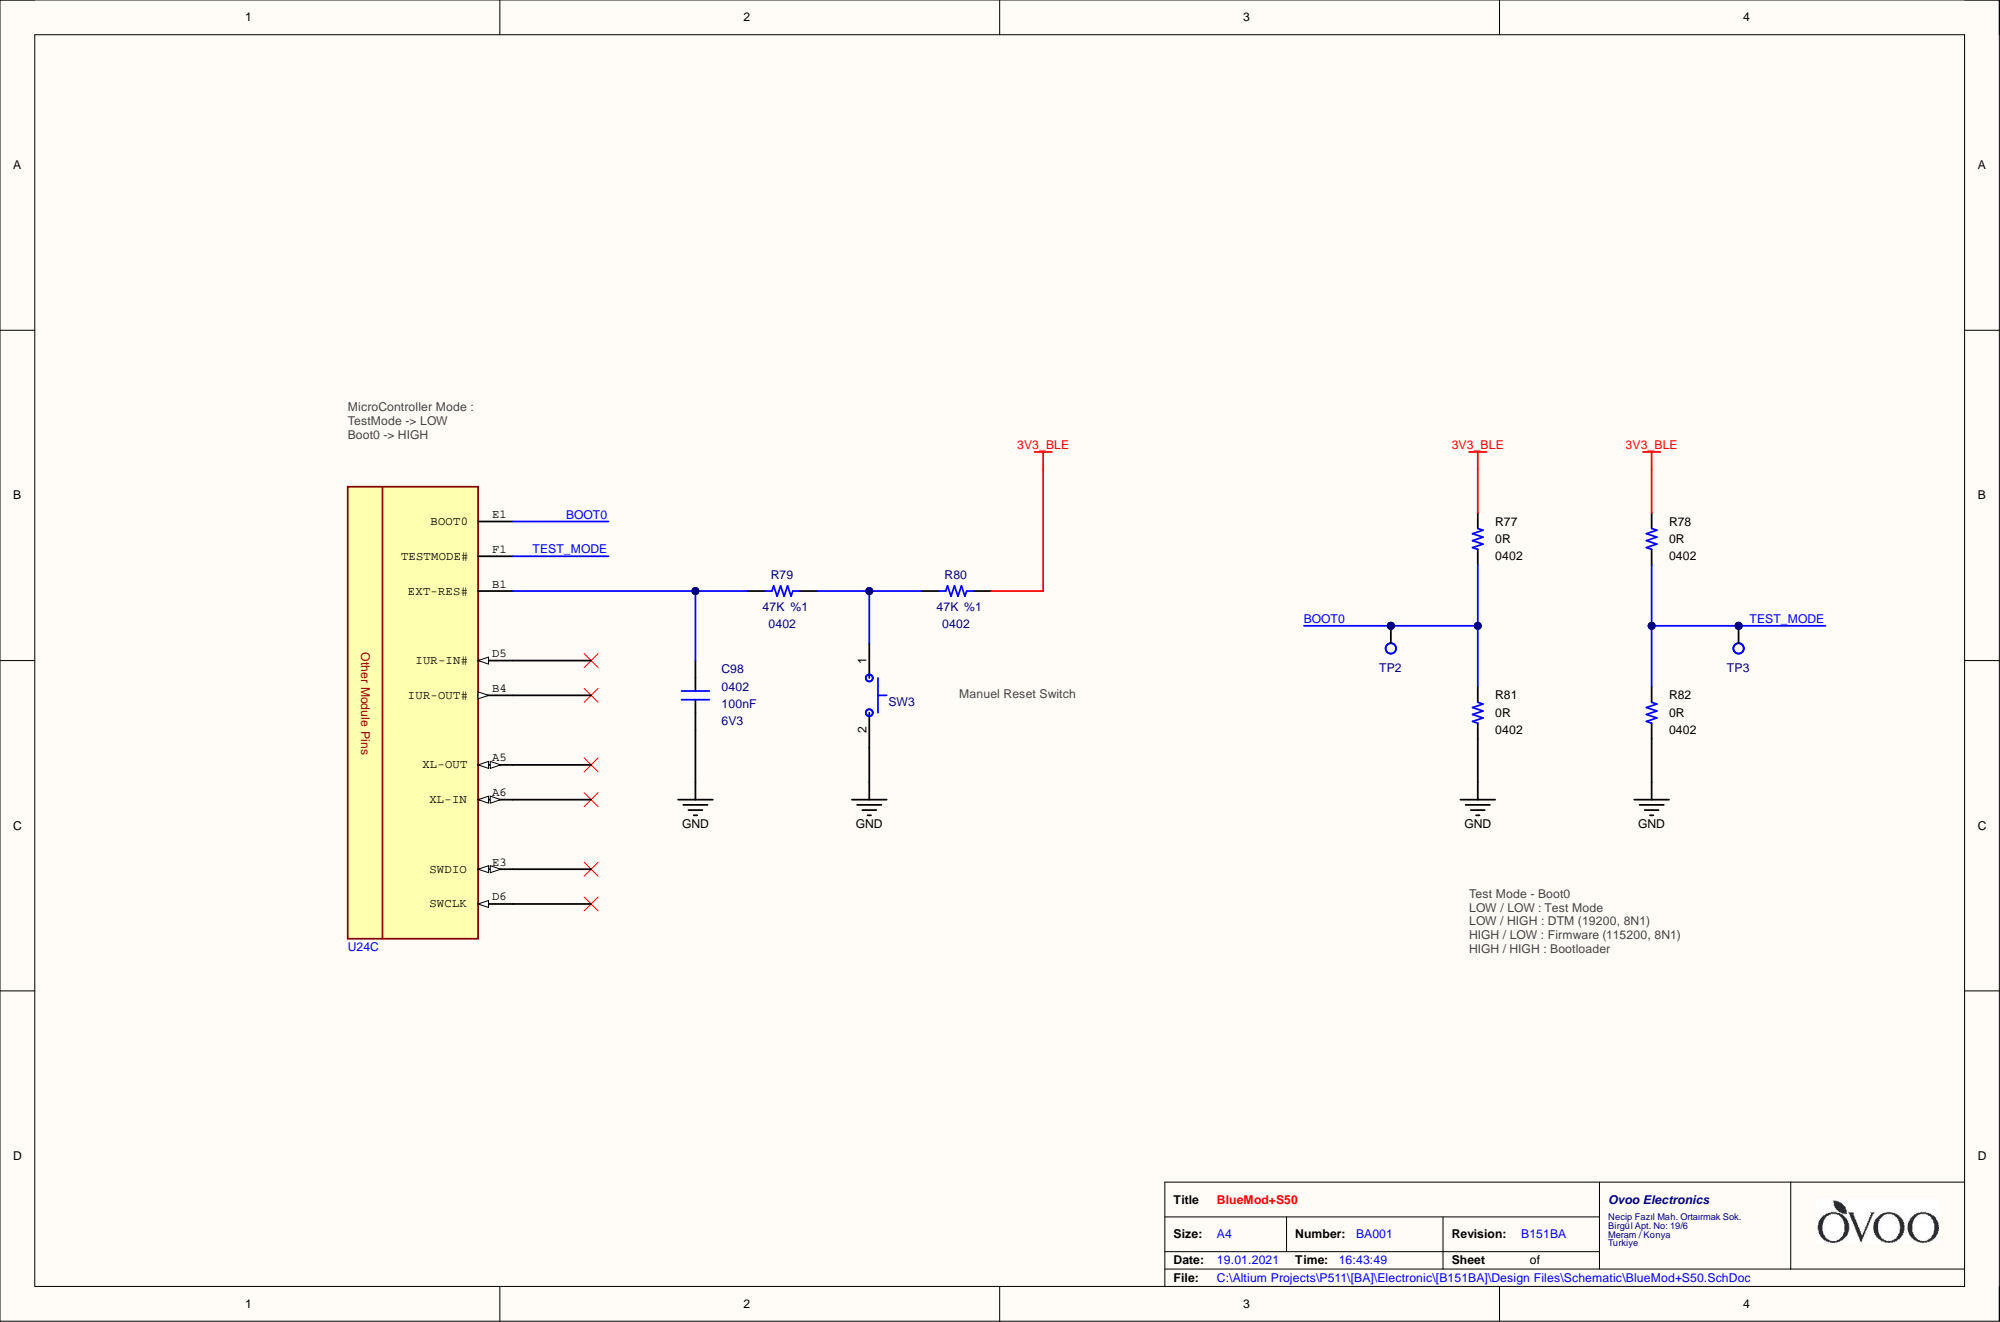
[picture p214: page 33]

Test Mode - Boot0
LOW / LOW : Test Mode
LOW / HIGH : DTM (19200, 8N1)
HIGH / LOW : Firmware (115200, 8N1)
HIGH / HIGH : Bootloader

C:\Altium Projects\P511\[BA]\Electronic\[B151BA]\Design Files\Schematic\BlueMod+S50.SchDoc
