akkoyun/B100/[AA]/Design Review/Telit/Review 3/Request Form/B100AA-R3.PDF

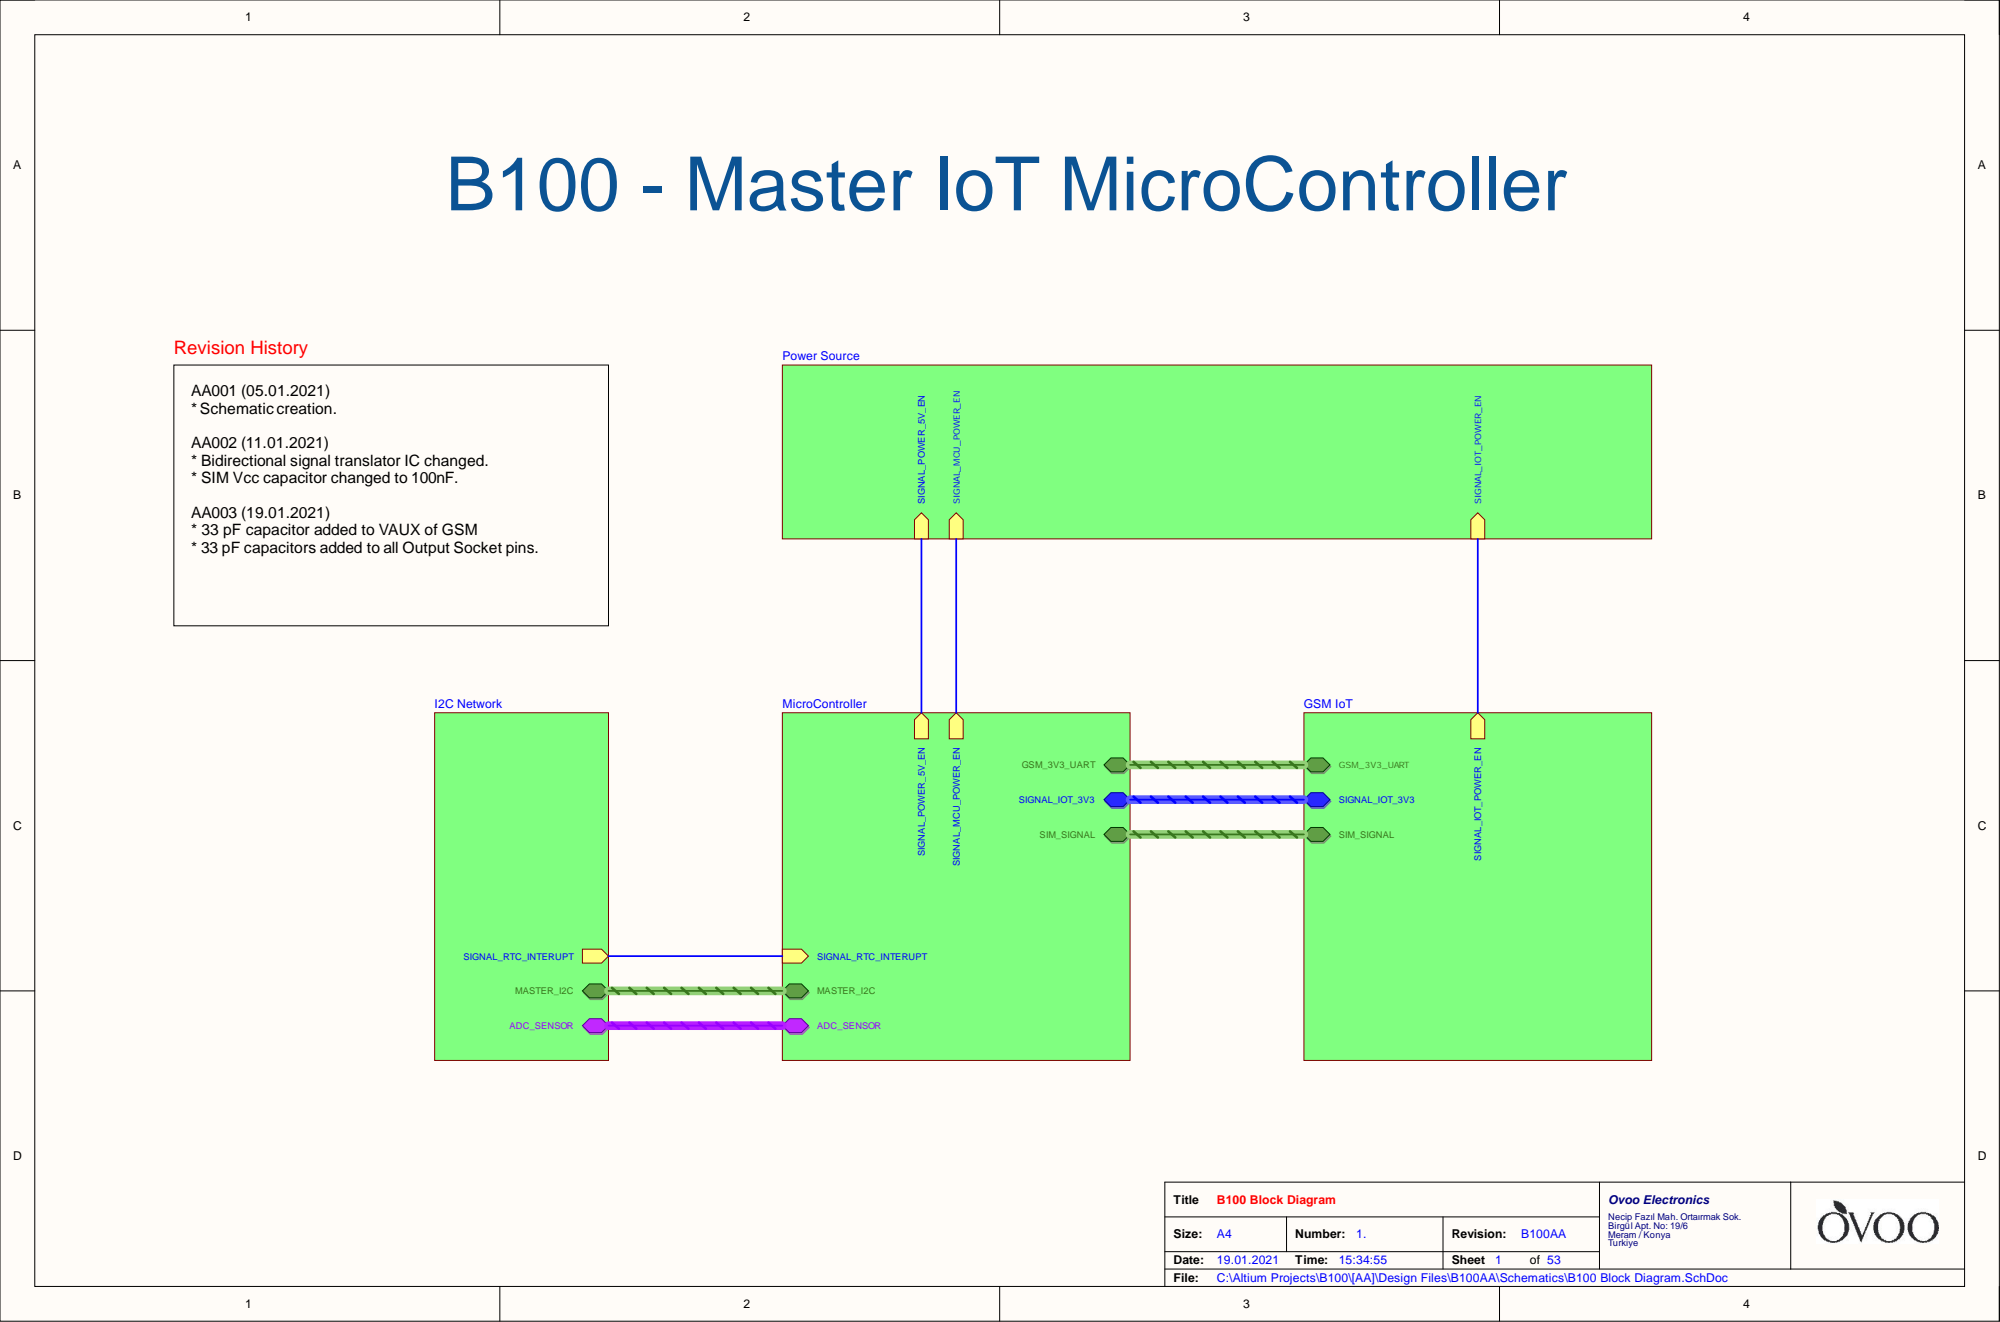
[picture p215: page 1]

* Bidirectional signal translator IC changed.
* SIM Vcc capacitor changed to 100nF.

* 33 pF capacitor added to VAUX of GSM
* 33 pF capacitors added to all Output Socket pins.

Necip Fazıl Mah. Ortaırmak Sok. Birgül Apt. No: 19/6 Meram / Konya Turkiye

C:\Altium Projects\B100\[AA]\Design Files\B100AA\Schematics\B100 Block Diagram.SchDoc

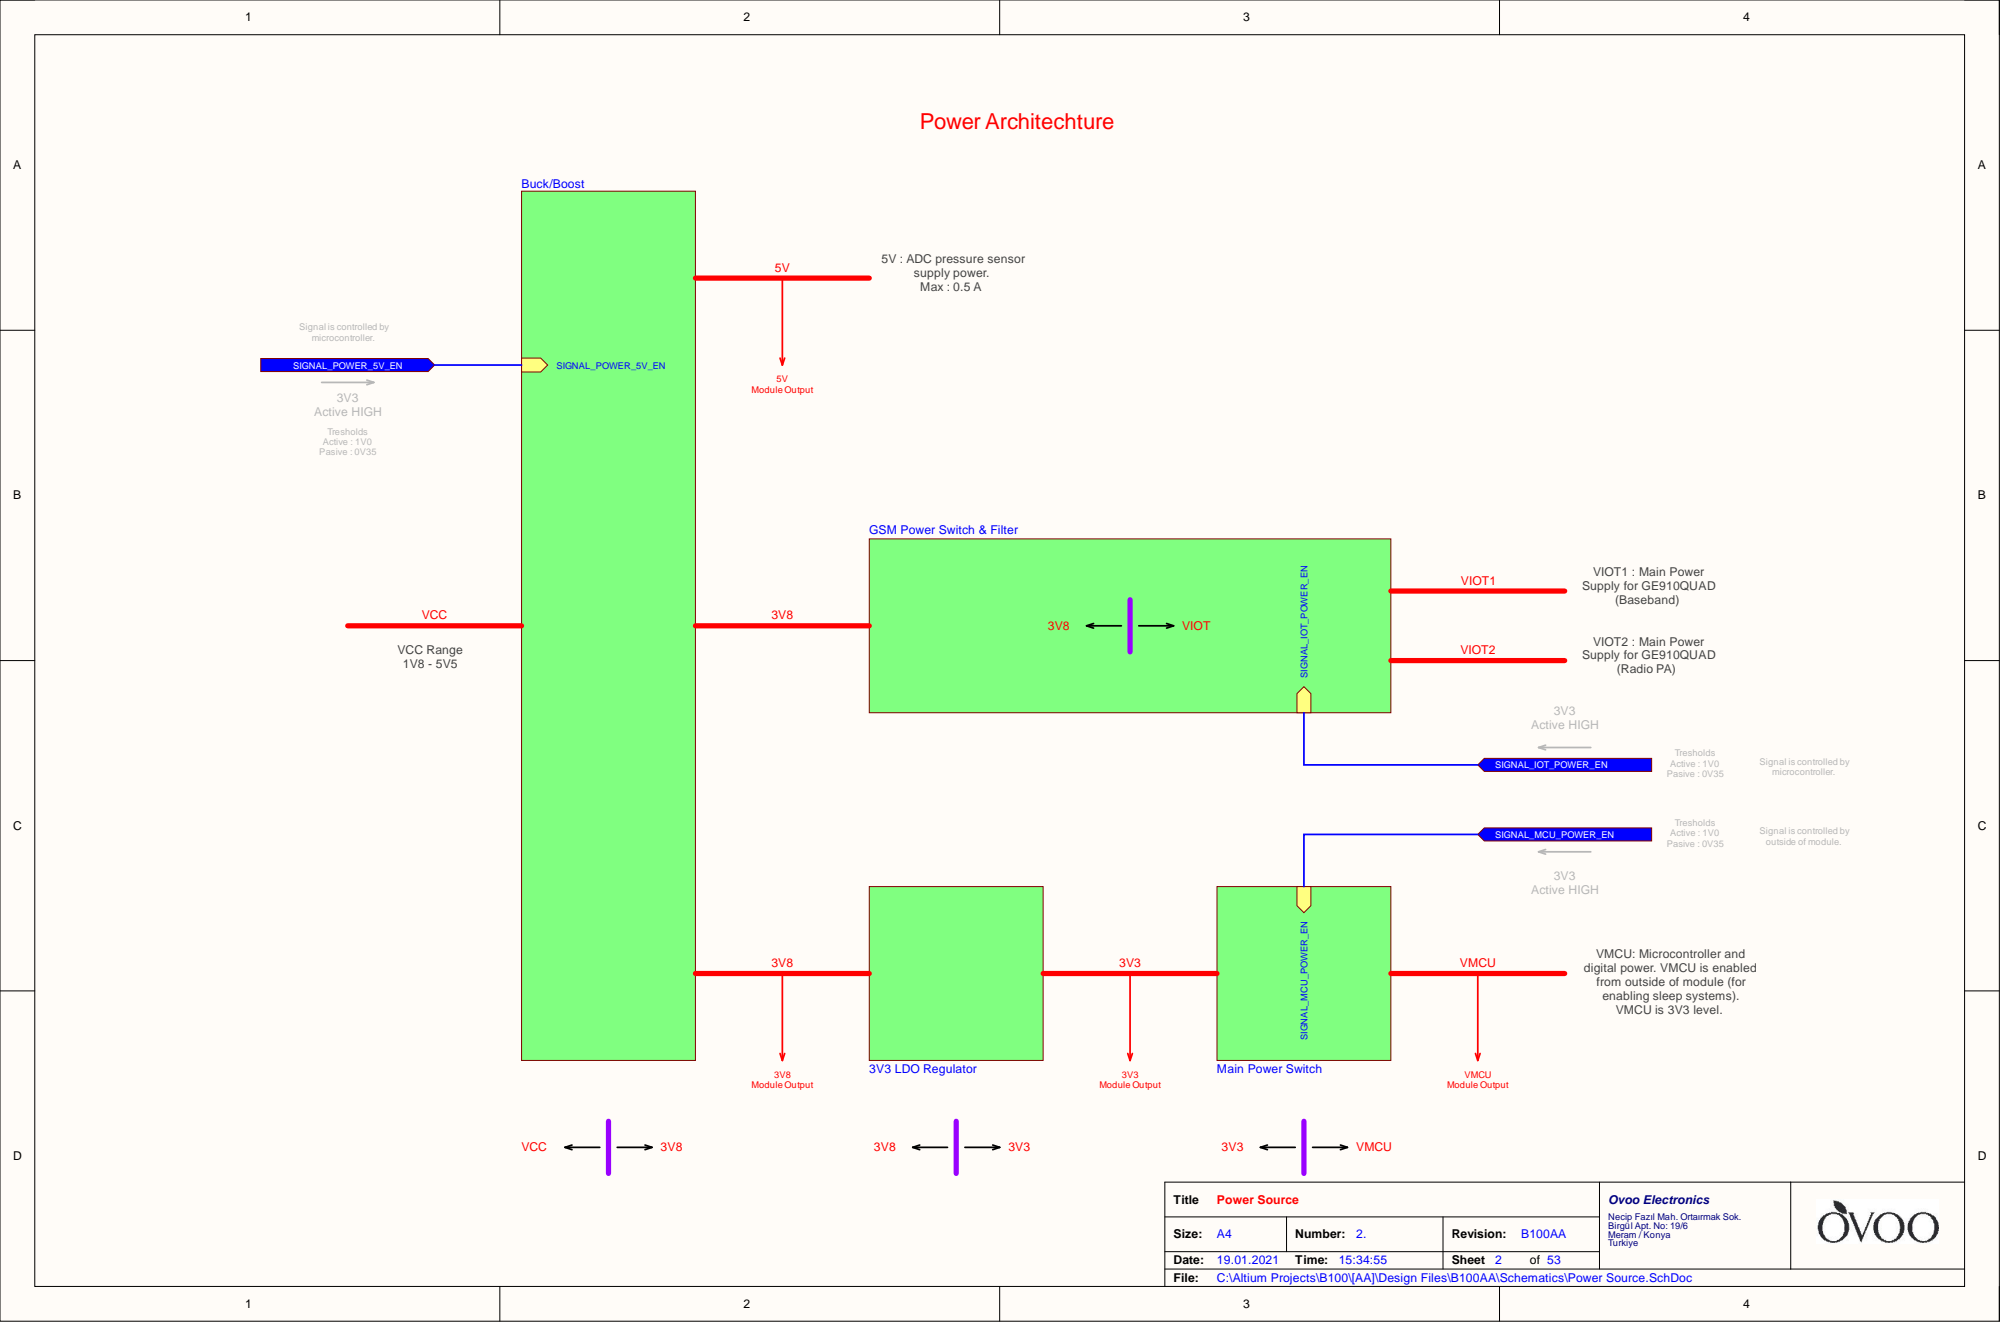
[picture p216: page 2]

Signal is controlled by
microcontroller.

GSM Power Switch & Filter

outside of module.

VMCU: Microcontroller and
digital power. VMCU is enabled
from outside of module (for
enabling sleep systems).
VMCU is 3V3 level.

C:\Altium Projects\B100\[AA]\Design Files\B100AA\Schematics\Power Source.SchDoc

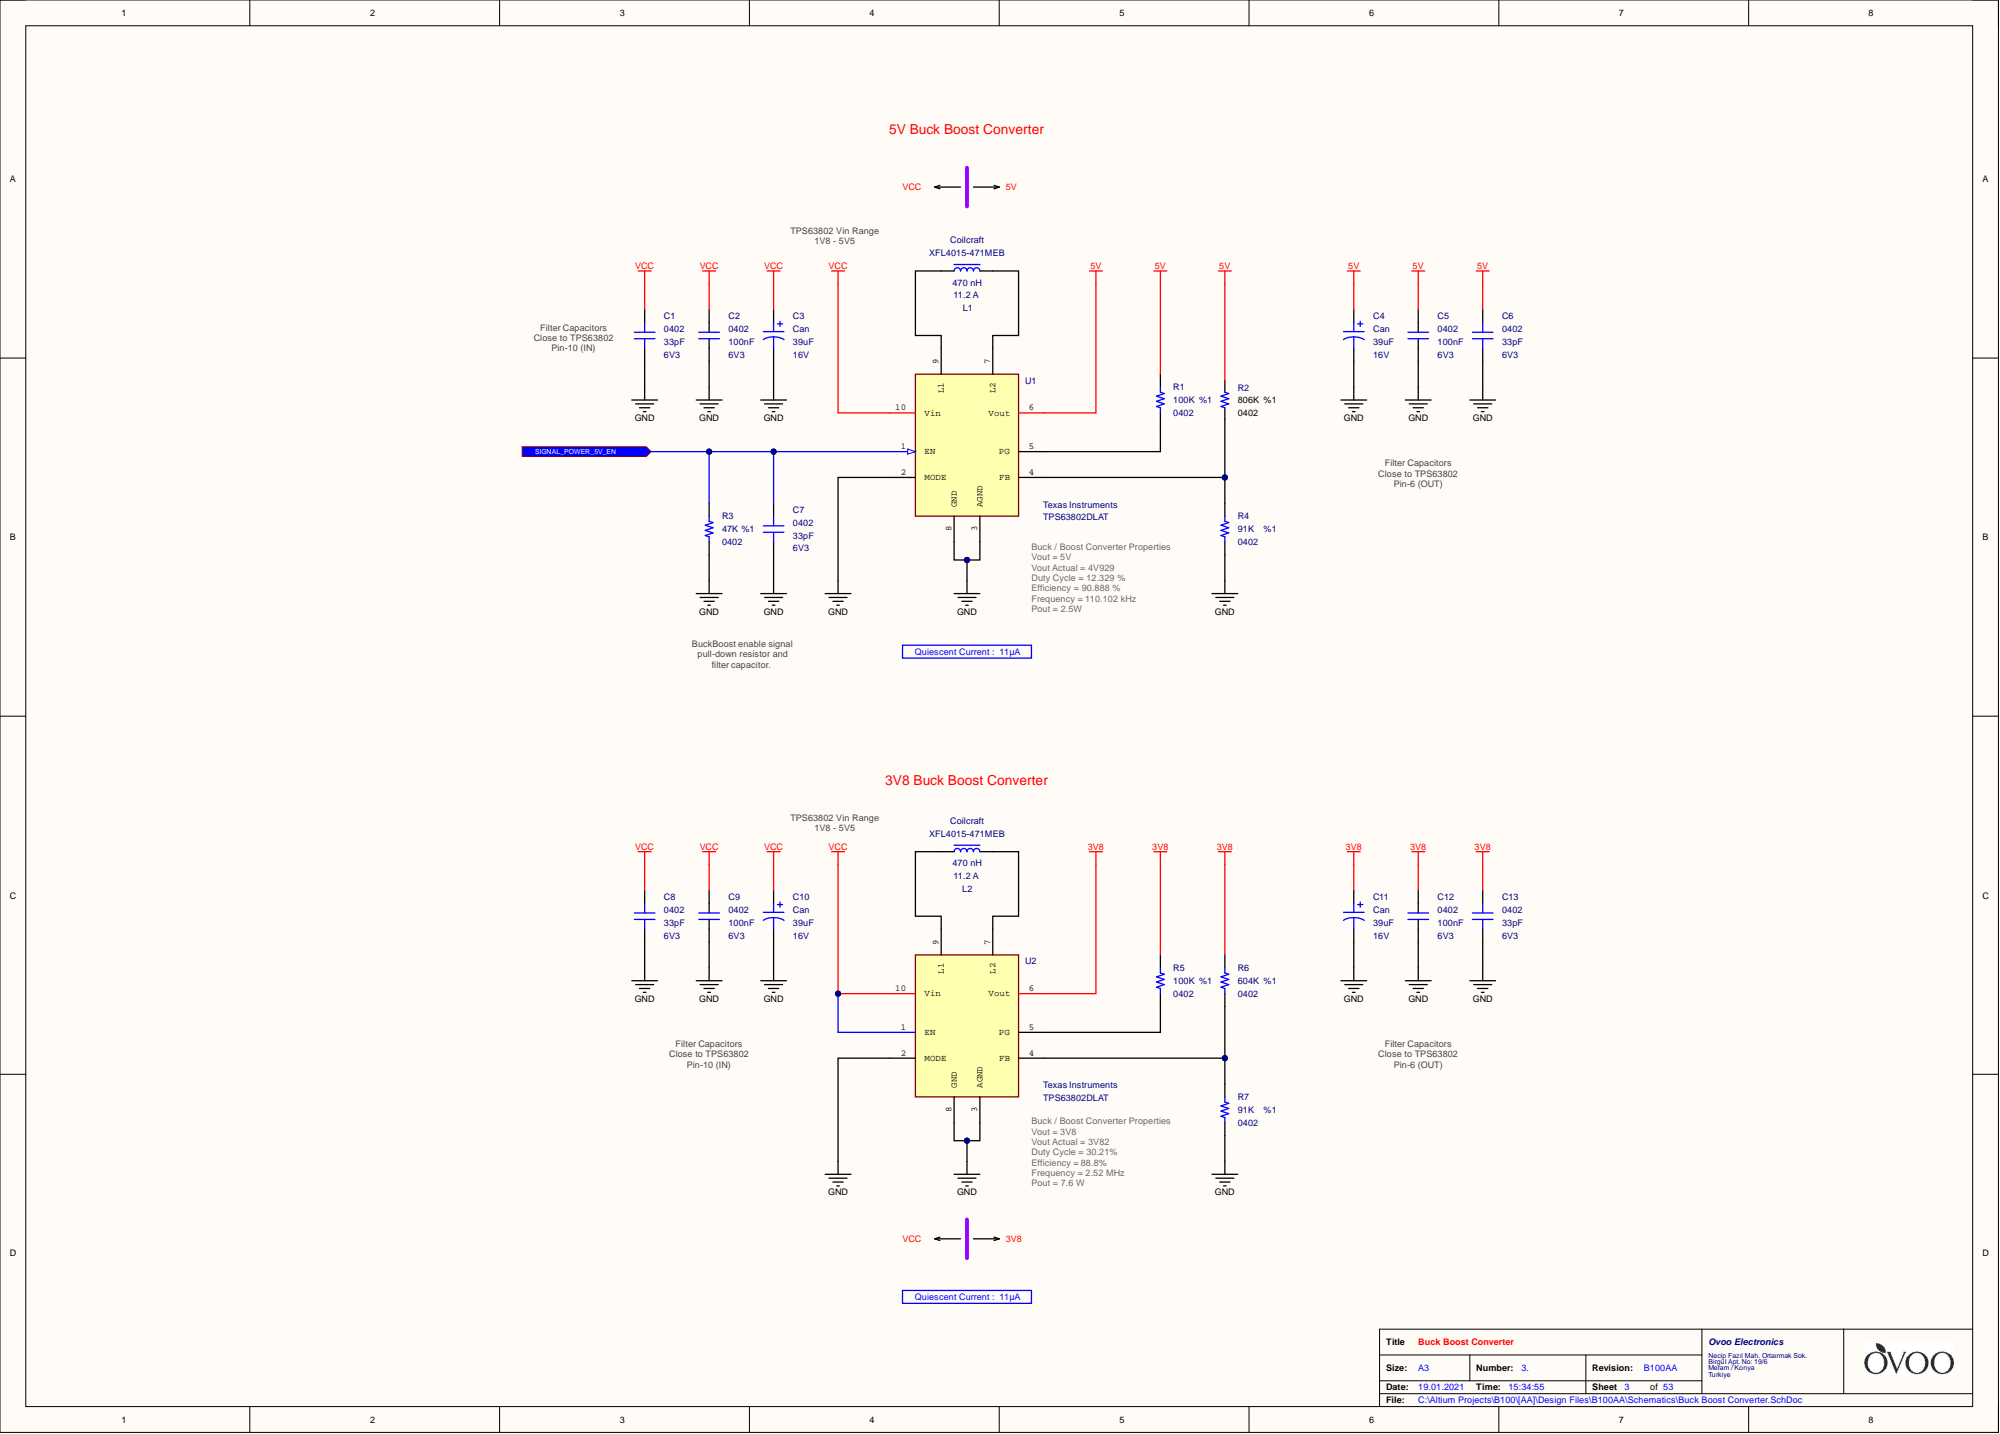
[picture p217: page 3]

BuckBoost enable signal
pull-down resistor and
filter capacitor.

C:\Altium Projects\B100\[AA]\Design Files\B100AA\Schematics\Buck Boost Converter.SchDoc

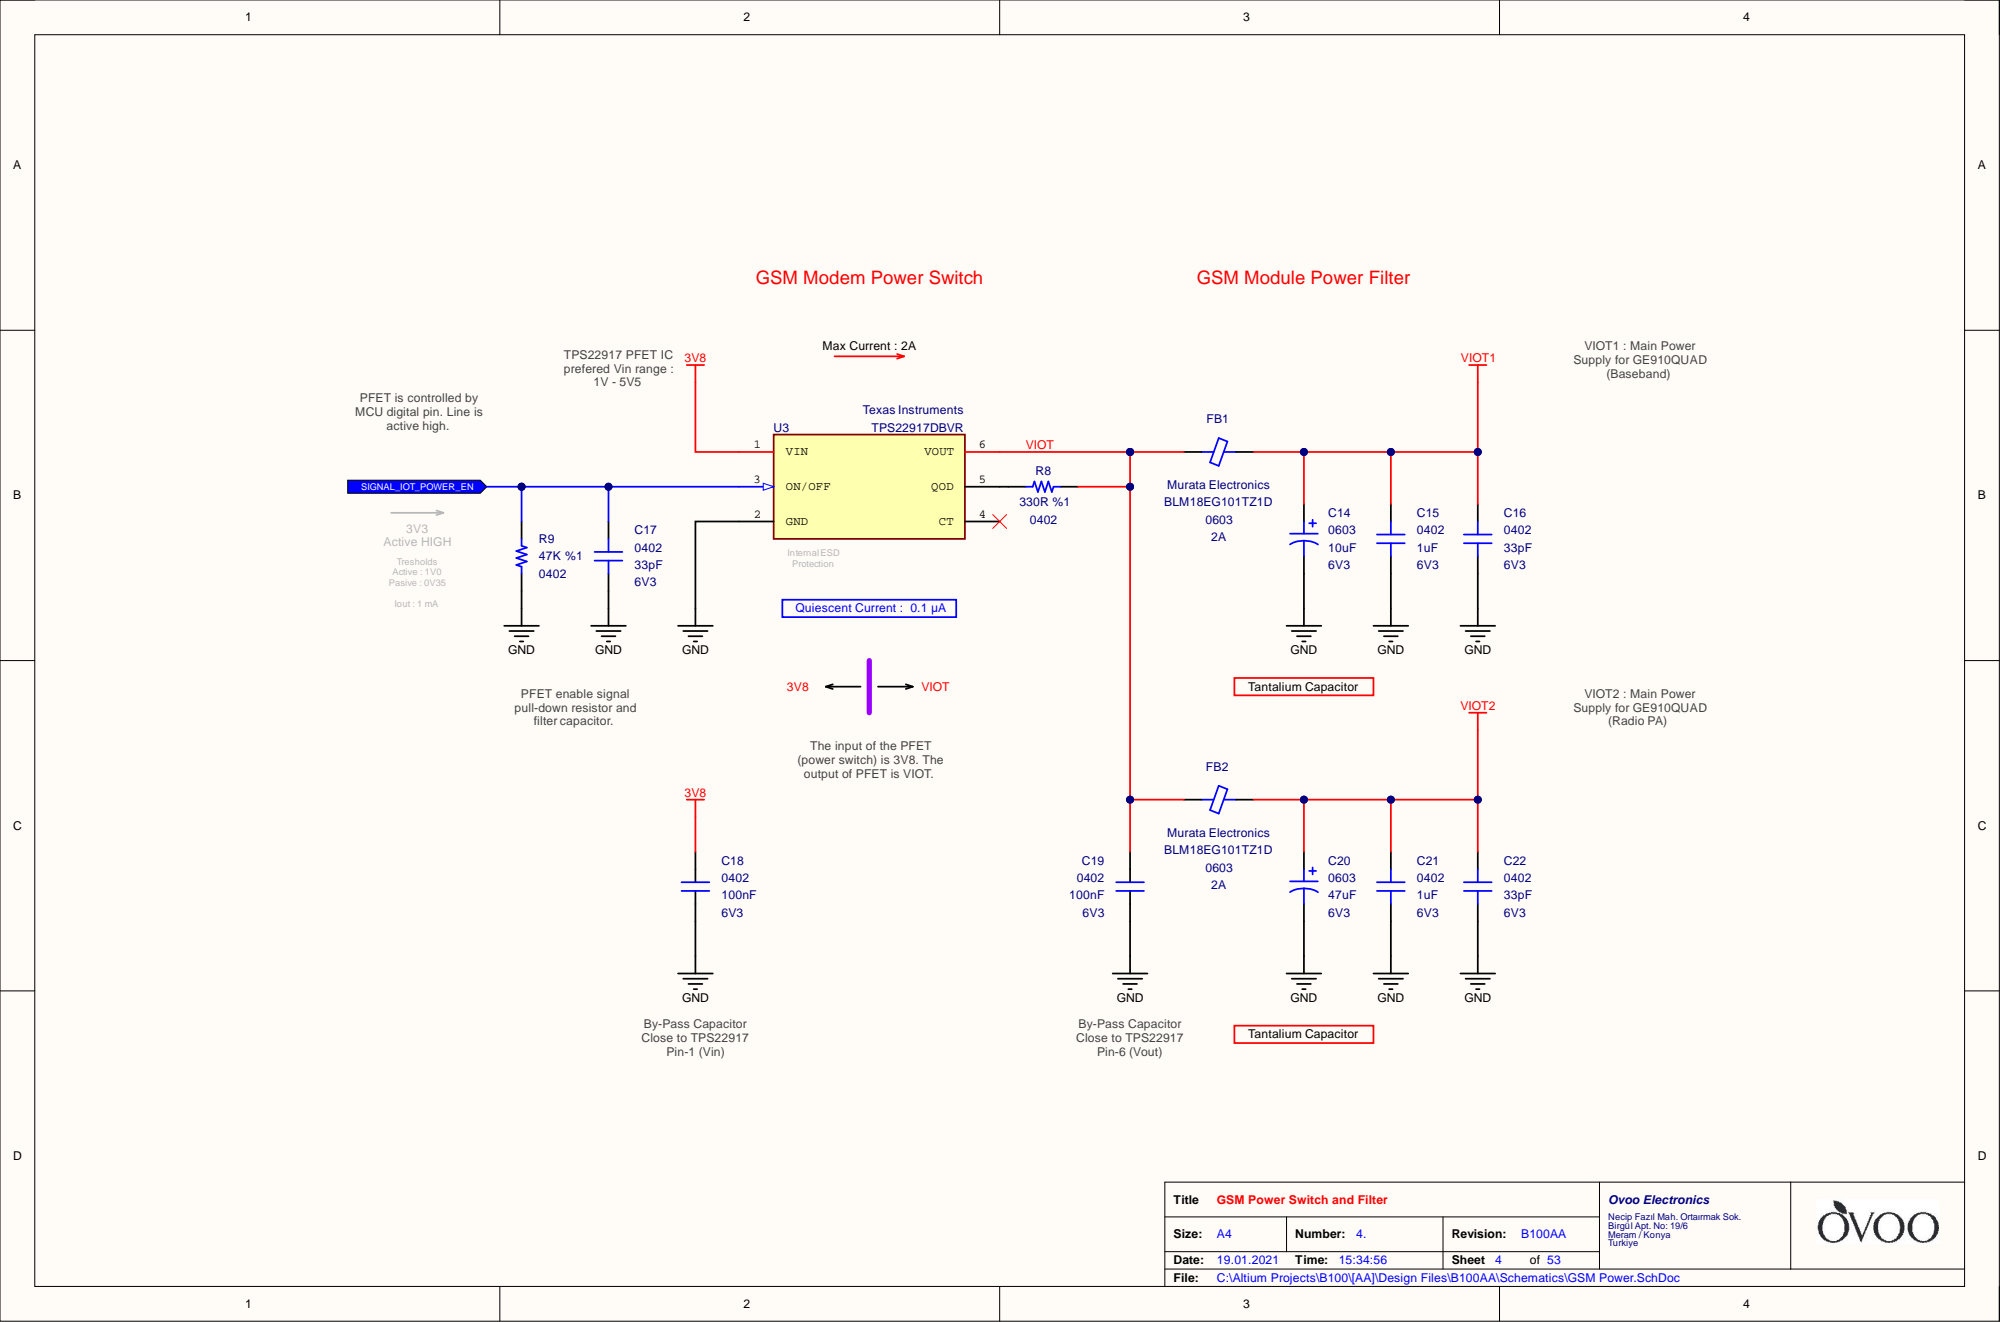
[picture p218: page 4]

GSM Modem Power Switch

GSM Module Power Filter

PFET is controlled by
MCU digital pin. Line is
active high.

PFET enable signal
pull-down resistor and
filter capacitor.

The input of the PFET
(power switch) is 3V8. The
output of PFET is VIOT.

GSM Power Switch and Filter

C:\Altium Projects\B100\[AA]\Design Files\B100AA\Schematics\GSM Power.SchDoc

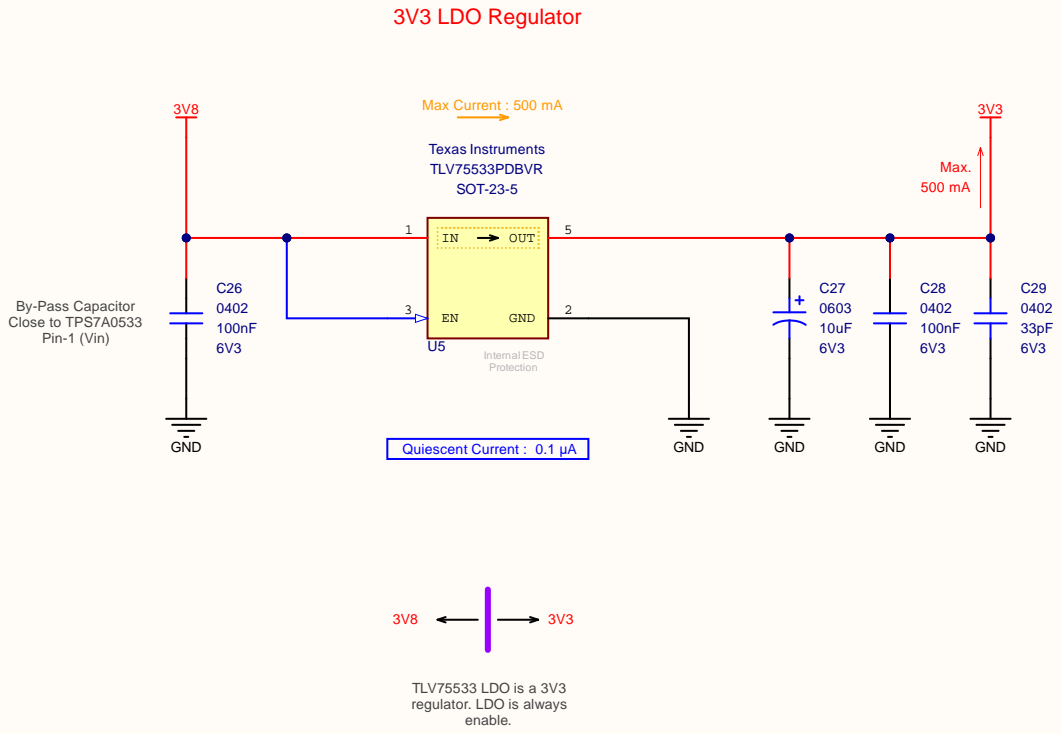
[picture p219: page 5]

TLV75533 LDO is a 3V3
regulator. LDO is always

C:\Altium Projects\B100\[AA]\Design Files\B100AA\Schematics\3V3 LDO Regulator.SchDoc

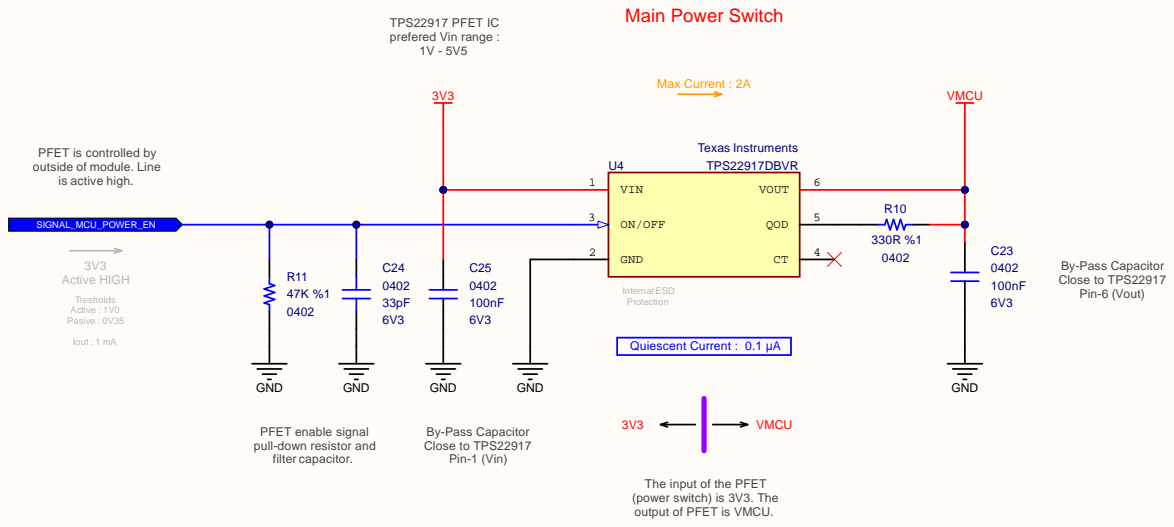
[picture p220: page 6]

PFET is controlled by
outside of module. Line
is active high.

PFET enable signal
pull-down resistor and
filter capacitor.

The input of the PFET
(power switch) is 3V3. The
output of PFET is VMCU.

C:\Altium Projects\B100\[AA]\Design Files\B100AA\Schematics\Main Power Switch.SchDoc

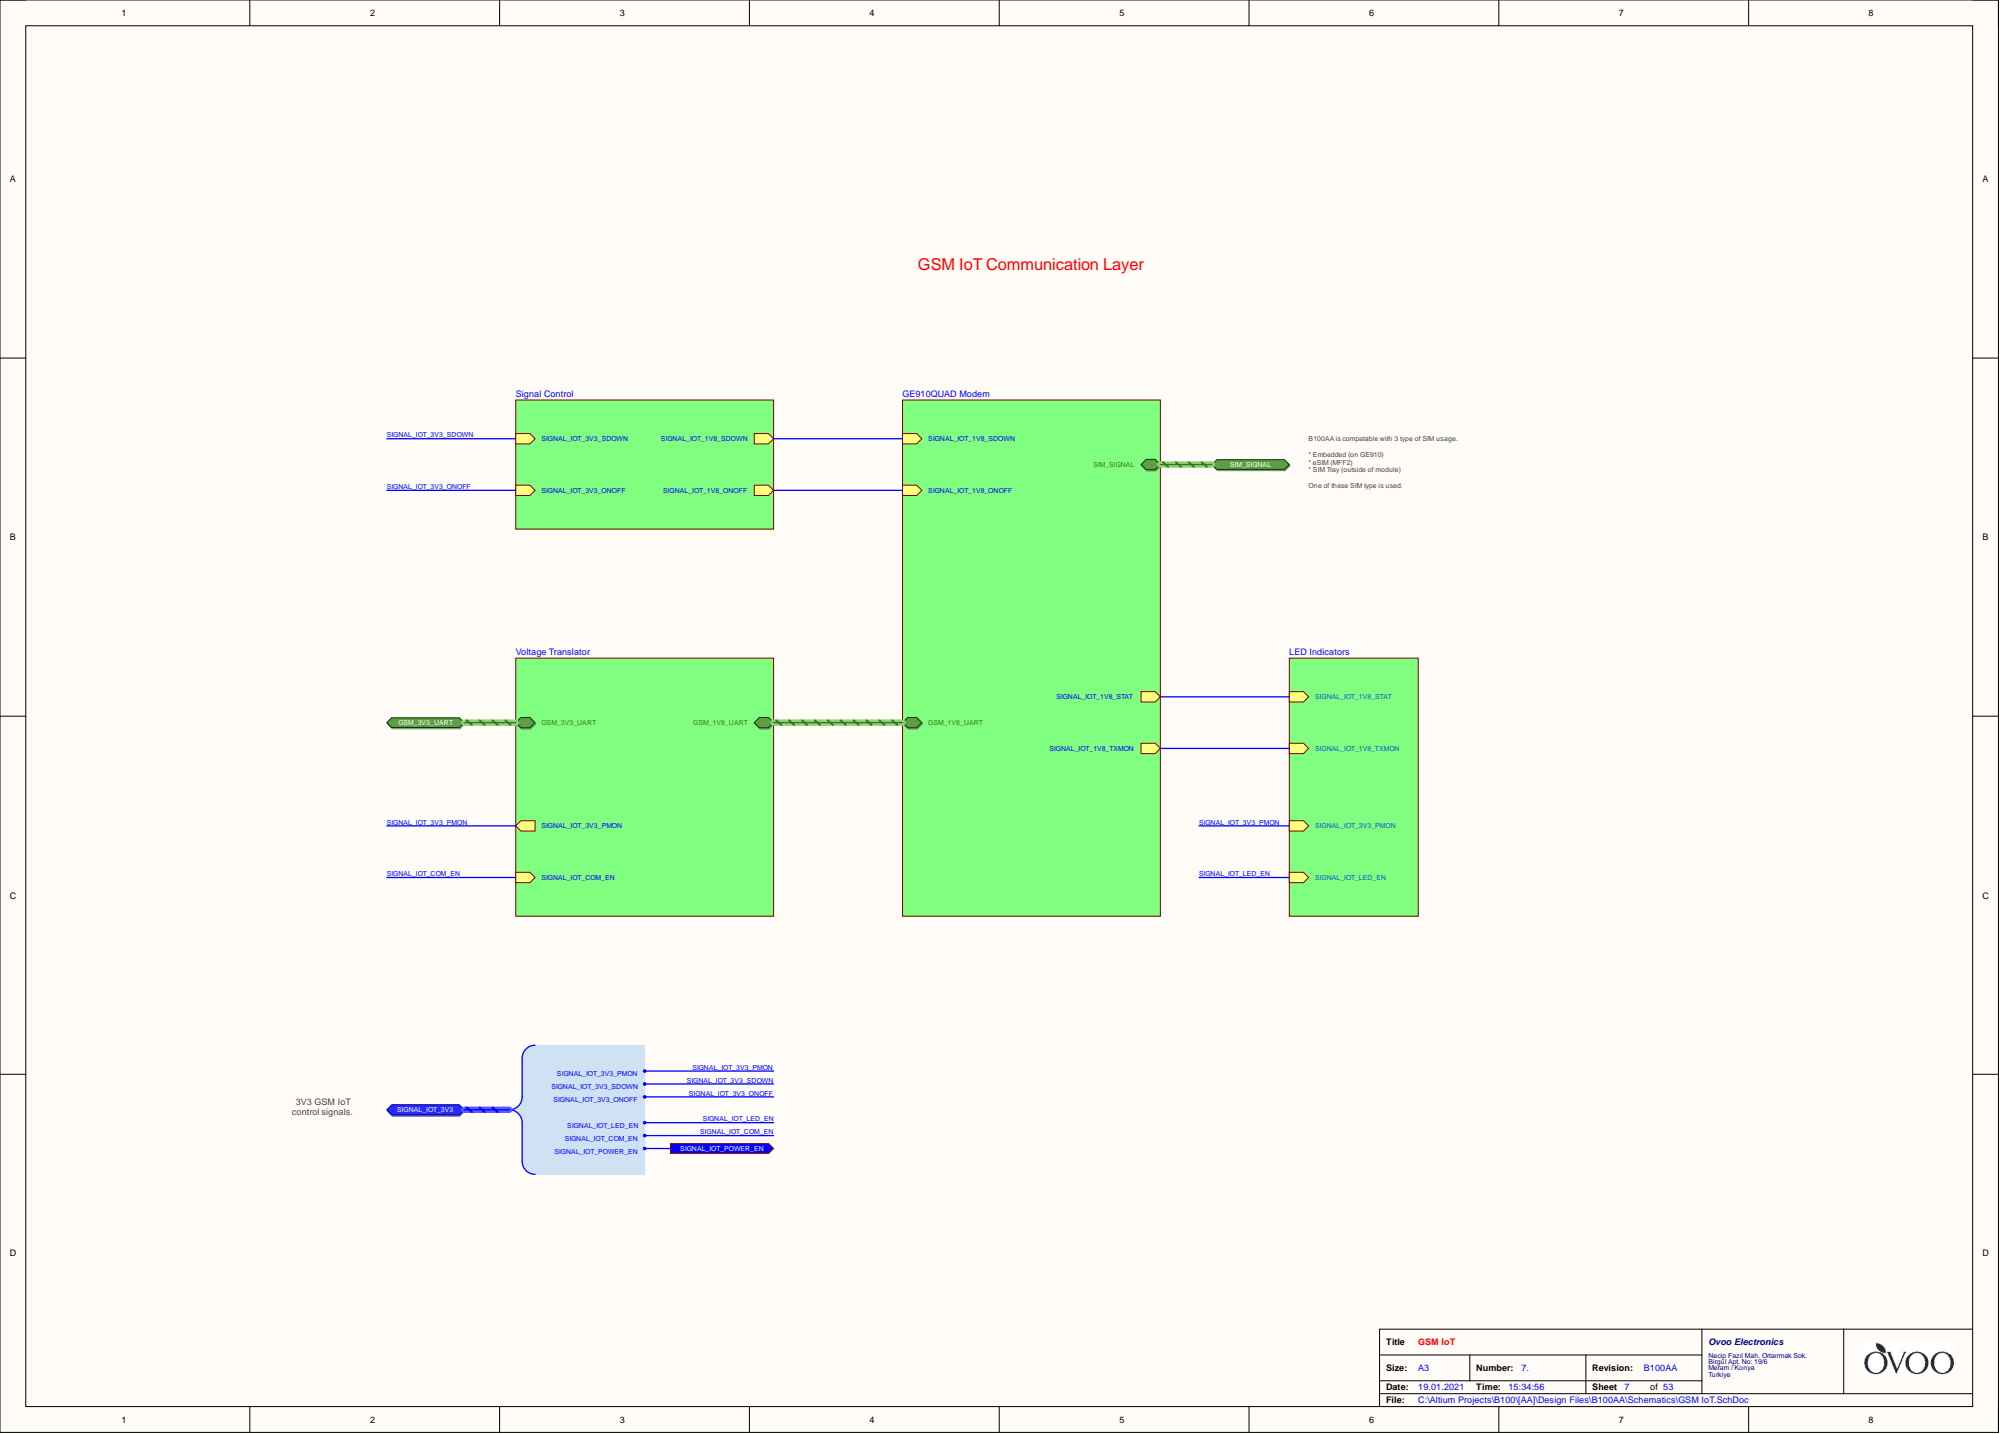
[picture p221: page 7]

GSM IoT Communication Layer

B100AA is compatable with 3 type of SIM usage.

* Embedded (on GE910)
* eSIM (MFF2)
* SIM Tray (outside of module)

One of these SIM type is used.

C:\Altium Projects\B100\[AA]\Design Files\B100AA\Schematics\GSM IoT.SchDoc

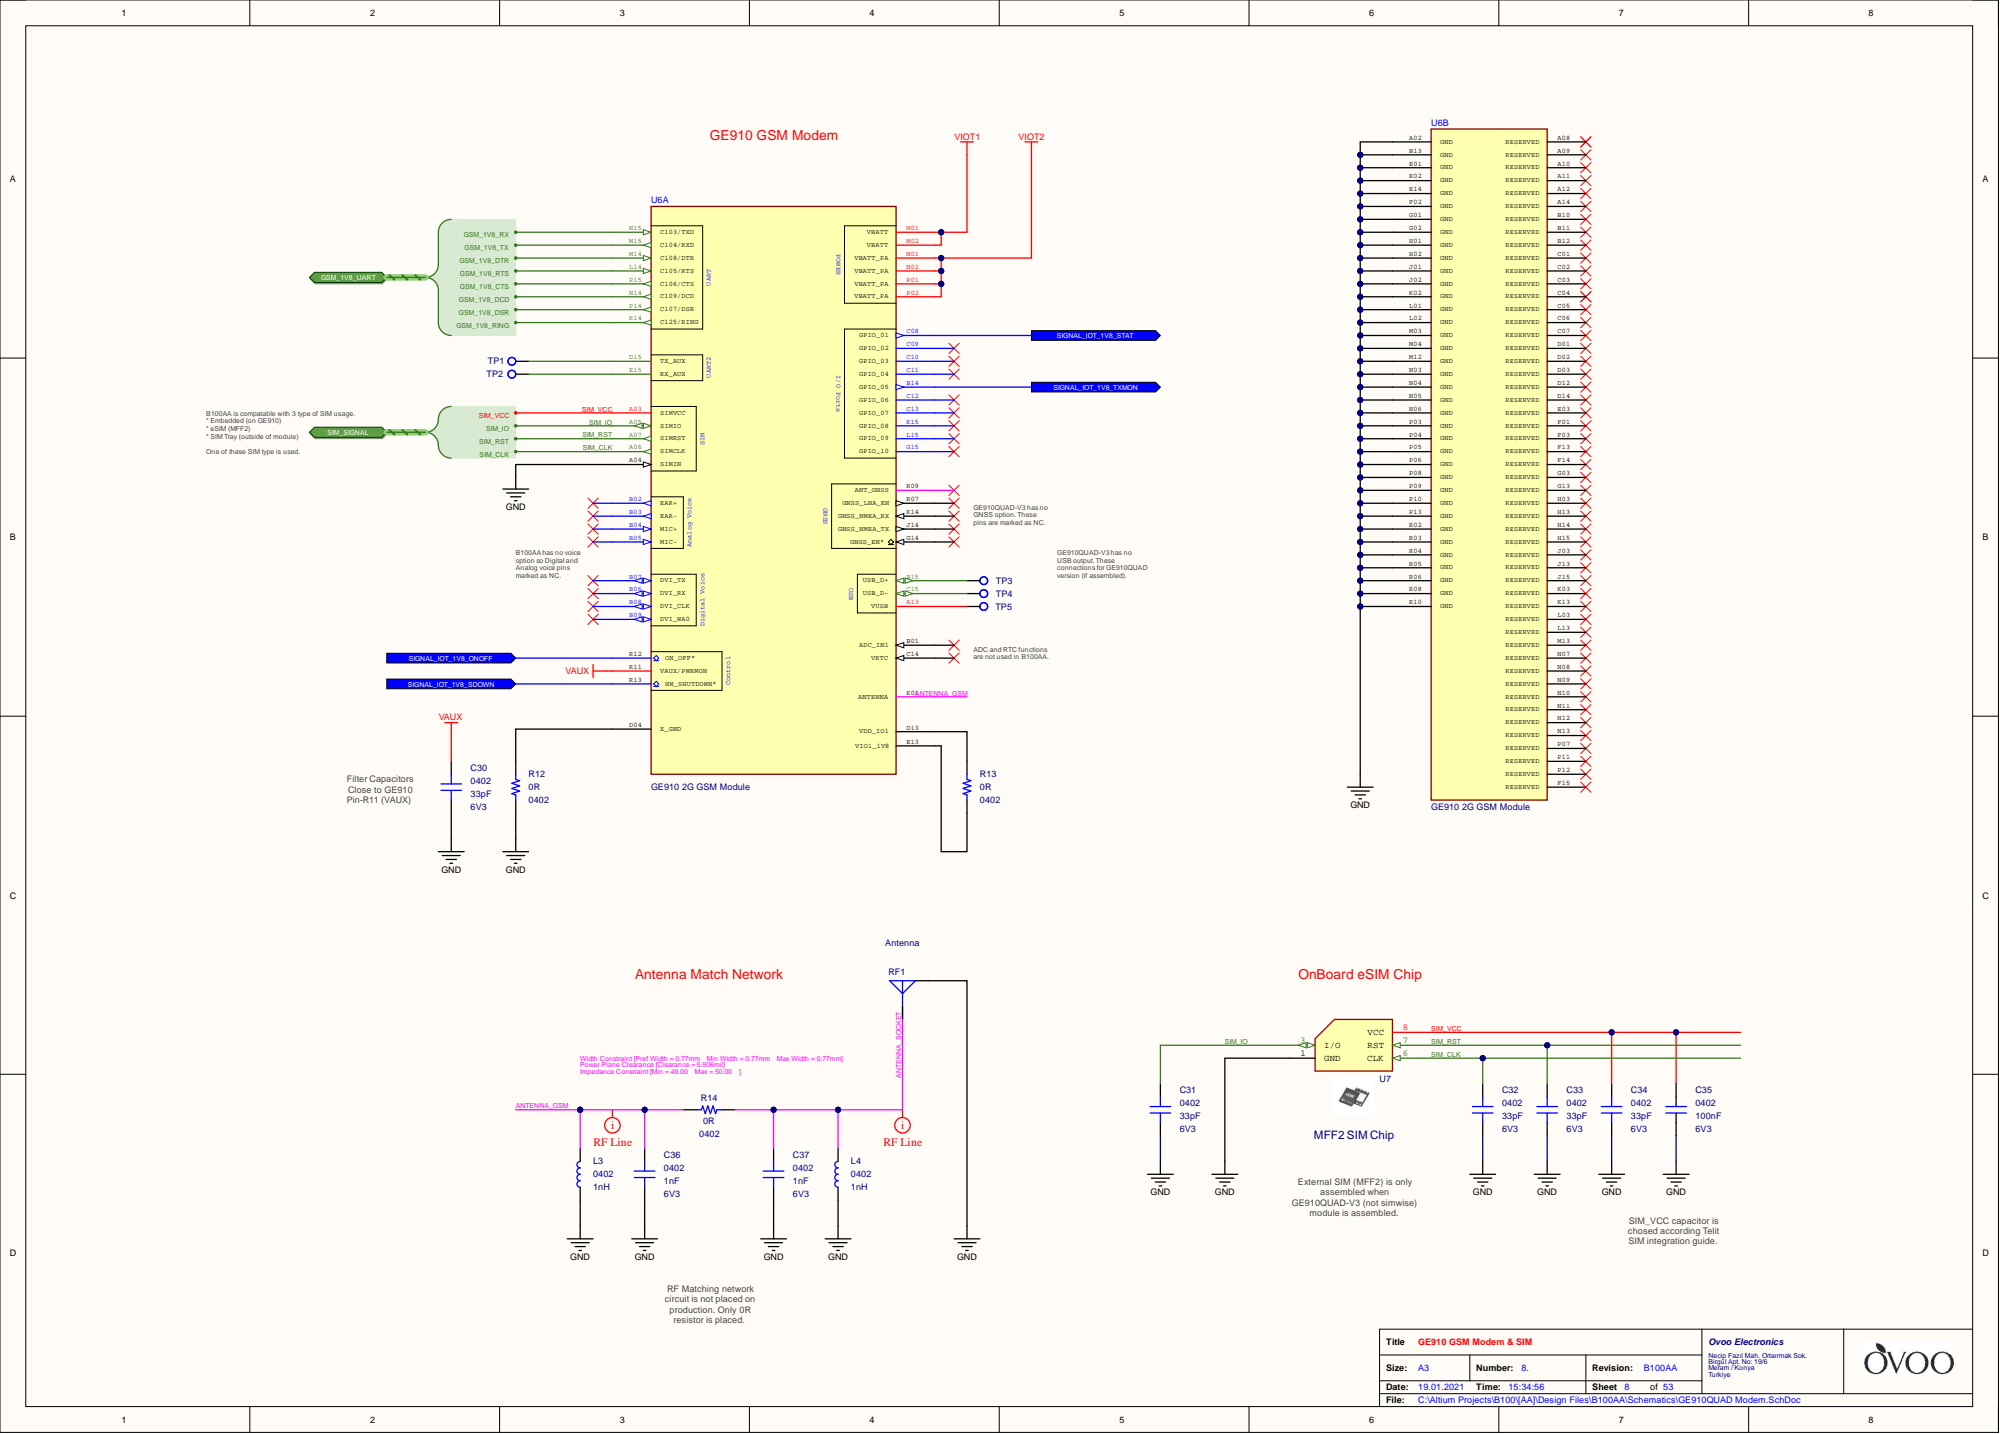
[picture p222: page 8]

B100AA is compatable with 3 type of SIM usage.
* Embedded (on GE910)
* eSIM (MFF2)
* SIM Tray (outside of module)

One of these SIM type is used.

GE910QUAD-V3 has no
GNSS option. These
pins are marked as NC.

B100AAhas no voice
option so Digital and
Analog voice pins
marked as NC.

ADC and RTC functions
are not used in B100AA.

Impedance Constraint [Min = 49.00 Max = 50.00 ] Power Plane Clearance [Clearance = 5.906mil] Width Constraint [Pref Width = 0.77mm Min Width = 0.77mm Max Width = 0.77mm]

External SIM (MFF2) is only
assembled when

RF Matching network
circuit is not placed on
production. Only 0R
resistor is placed.

C:\Altium Projects\B100\[AA]\Design Files\B100AA\Schematics\GE910QUAD Modem.SchDoc

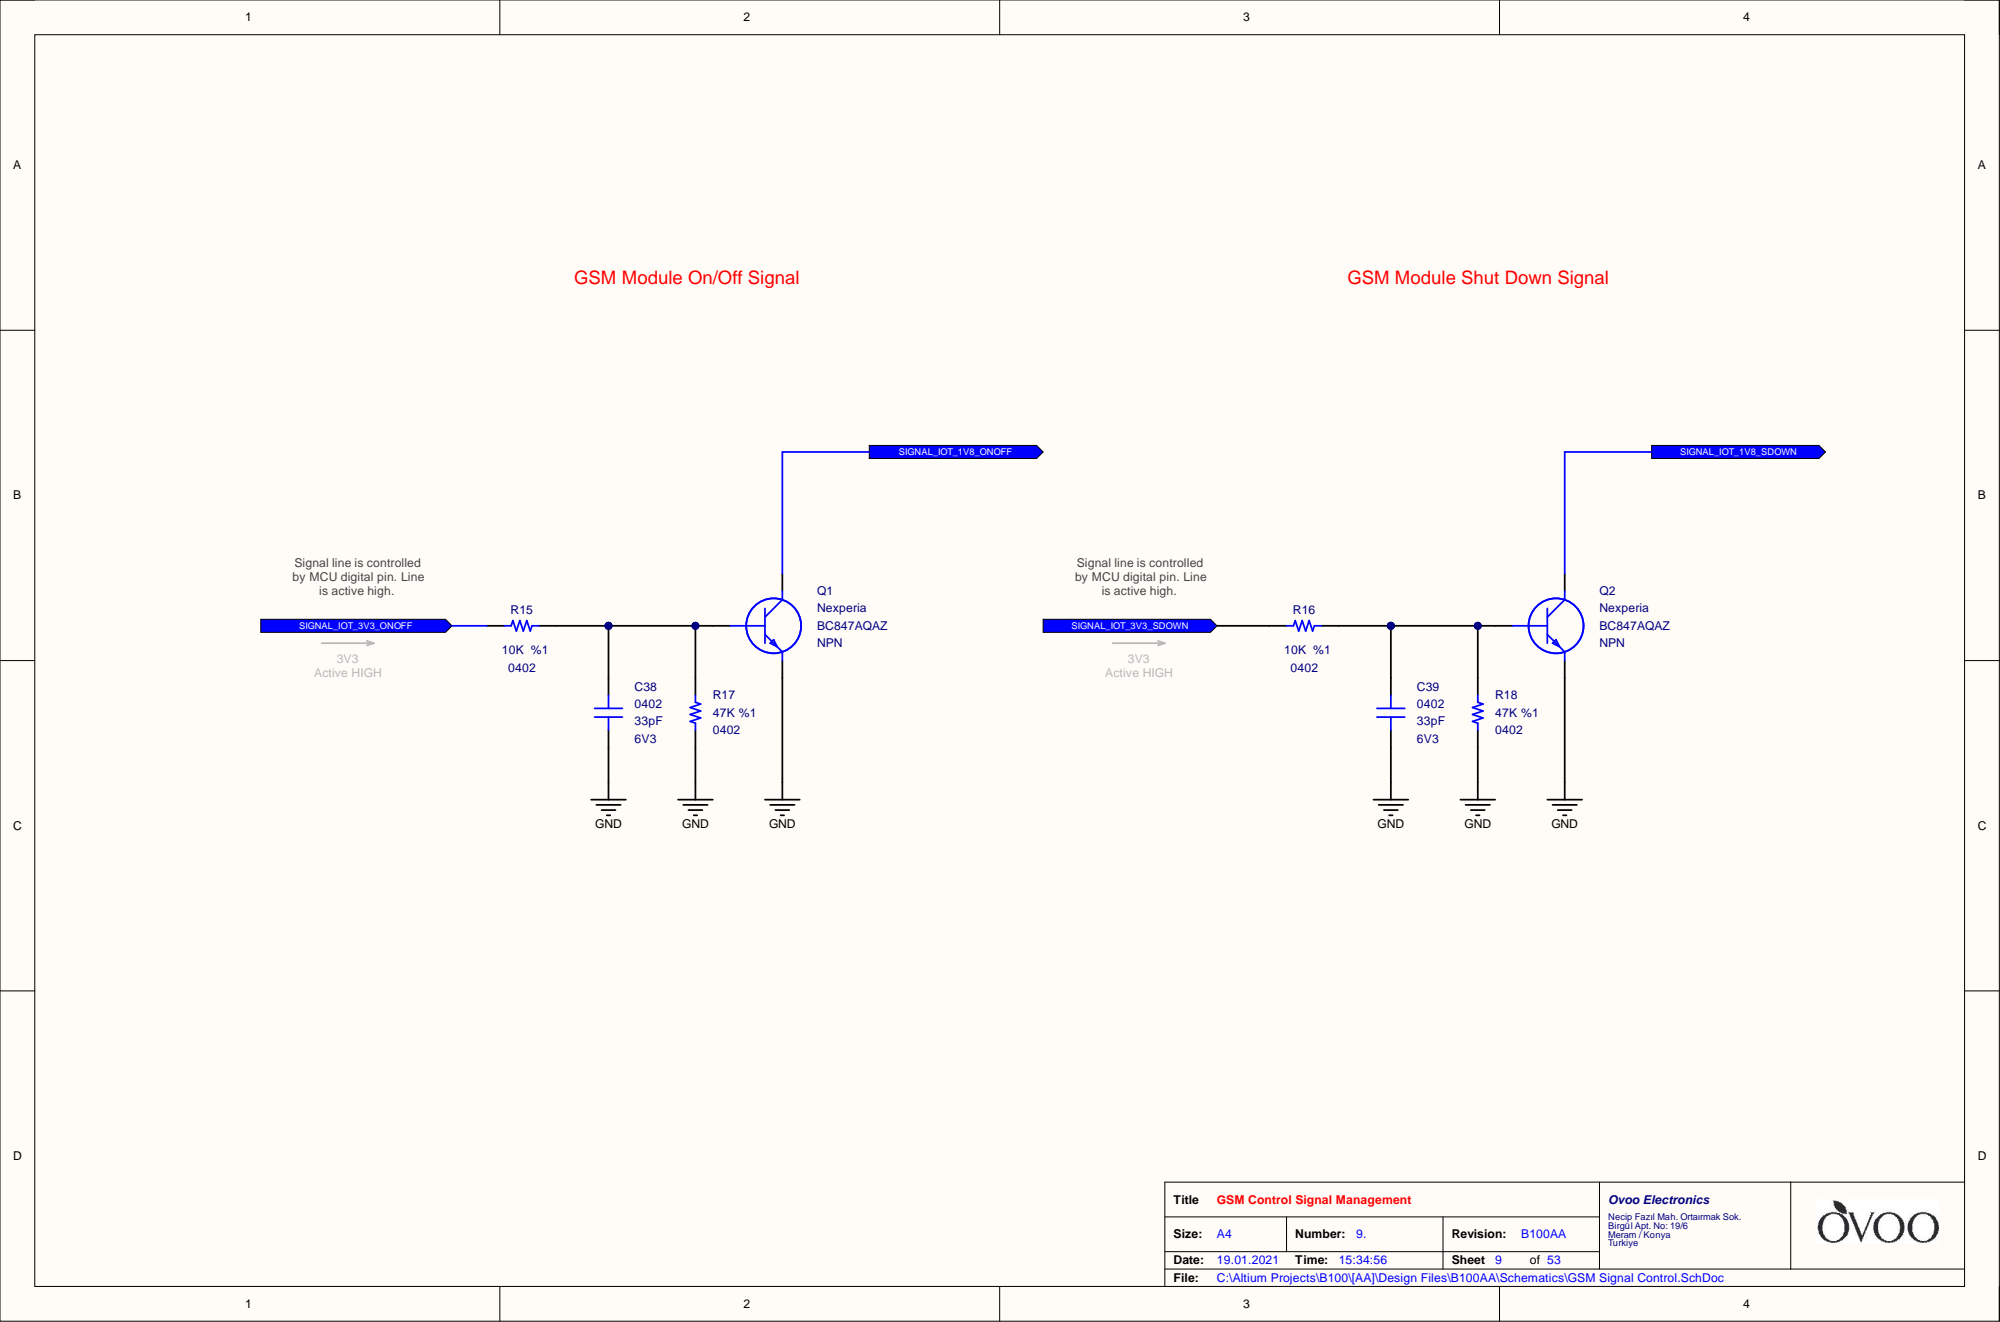
[picture p223: page 9]

GSM Module On/Off Signal

GSM Module Shut Down Signal

Signal line is controlled
by MCU digital pin. Line
is active high.

GSM Control Signal Management

C:\Altium Projects\B100\[AA]\Design Files\B100AA\Schematics\GSM Signal Control.SchDoc

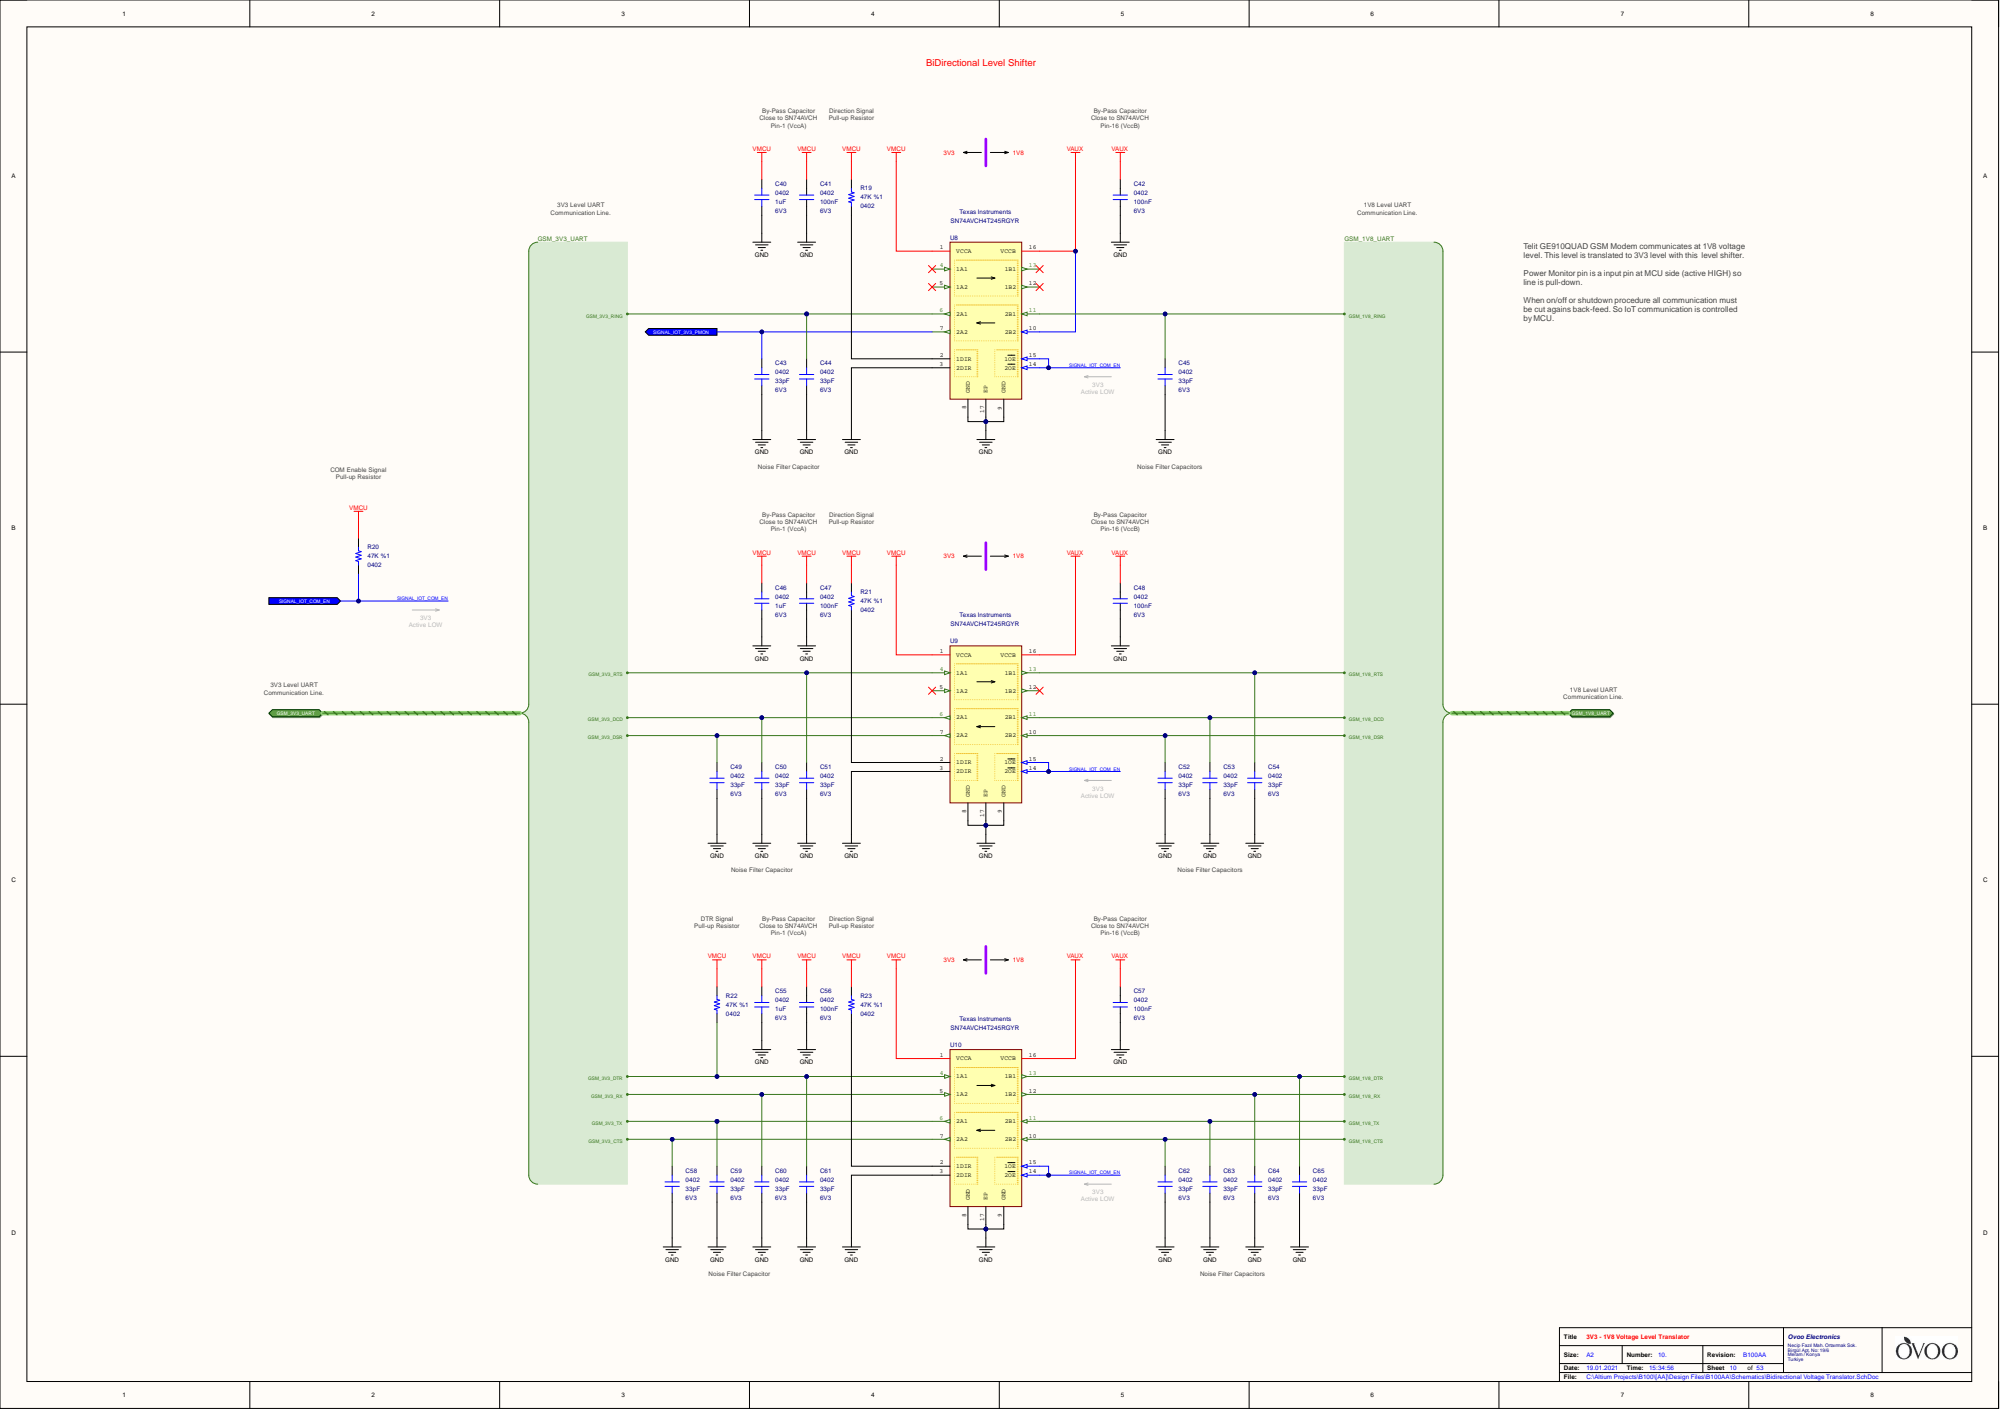
[picture p224: page 10]

Telit GE910QUAD GSM Modem communicates at 1V8 voltage
level. This level is translated to 3V3 level with this level shifter.

Power Monitor pin is a input pin at MCU side (active HIGH) so
line is pull-down.

When on/off or shutdown procedure all communication must
be cut agains back-feed. So IoT communication is controlled
by MCU.

1DIR 2
2DIR 3

C:\Altium Projects\B100\[AA]\Design Files\B100AA\Schematics\Bidirectional Voltage Translator.SchDoc

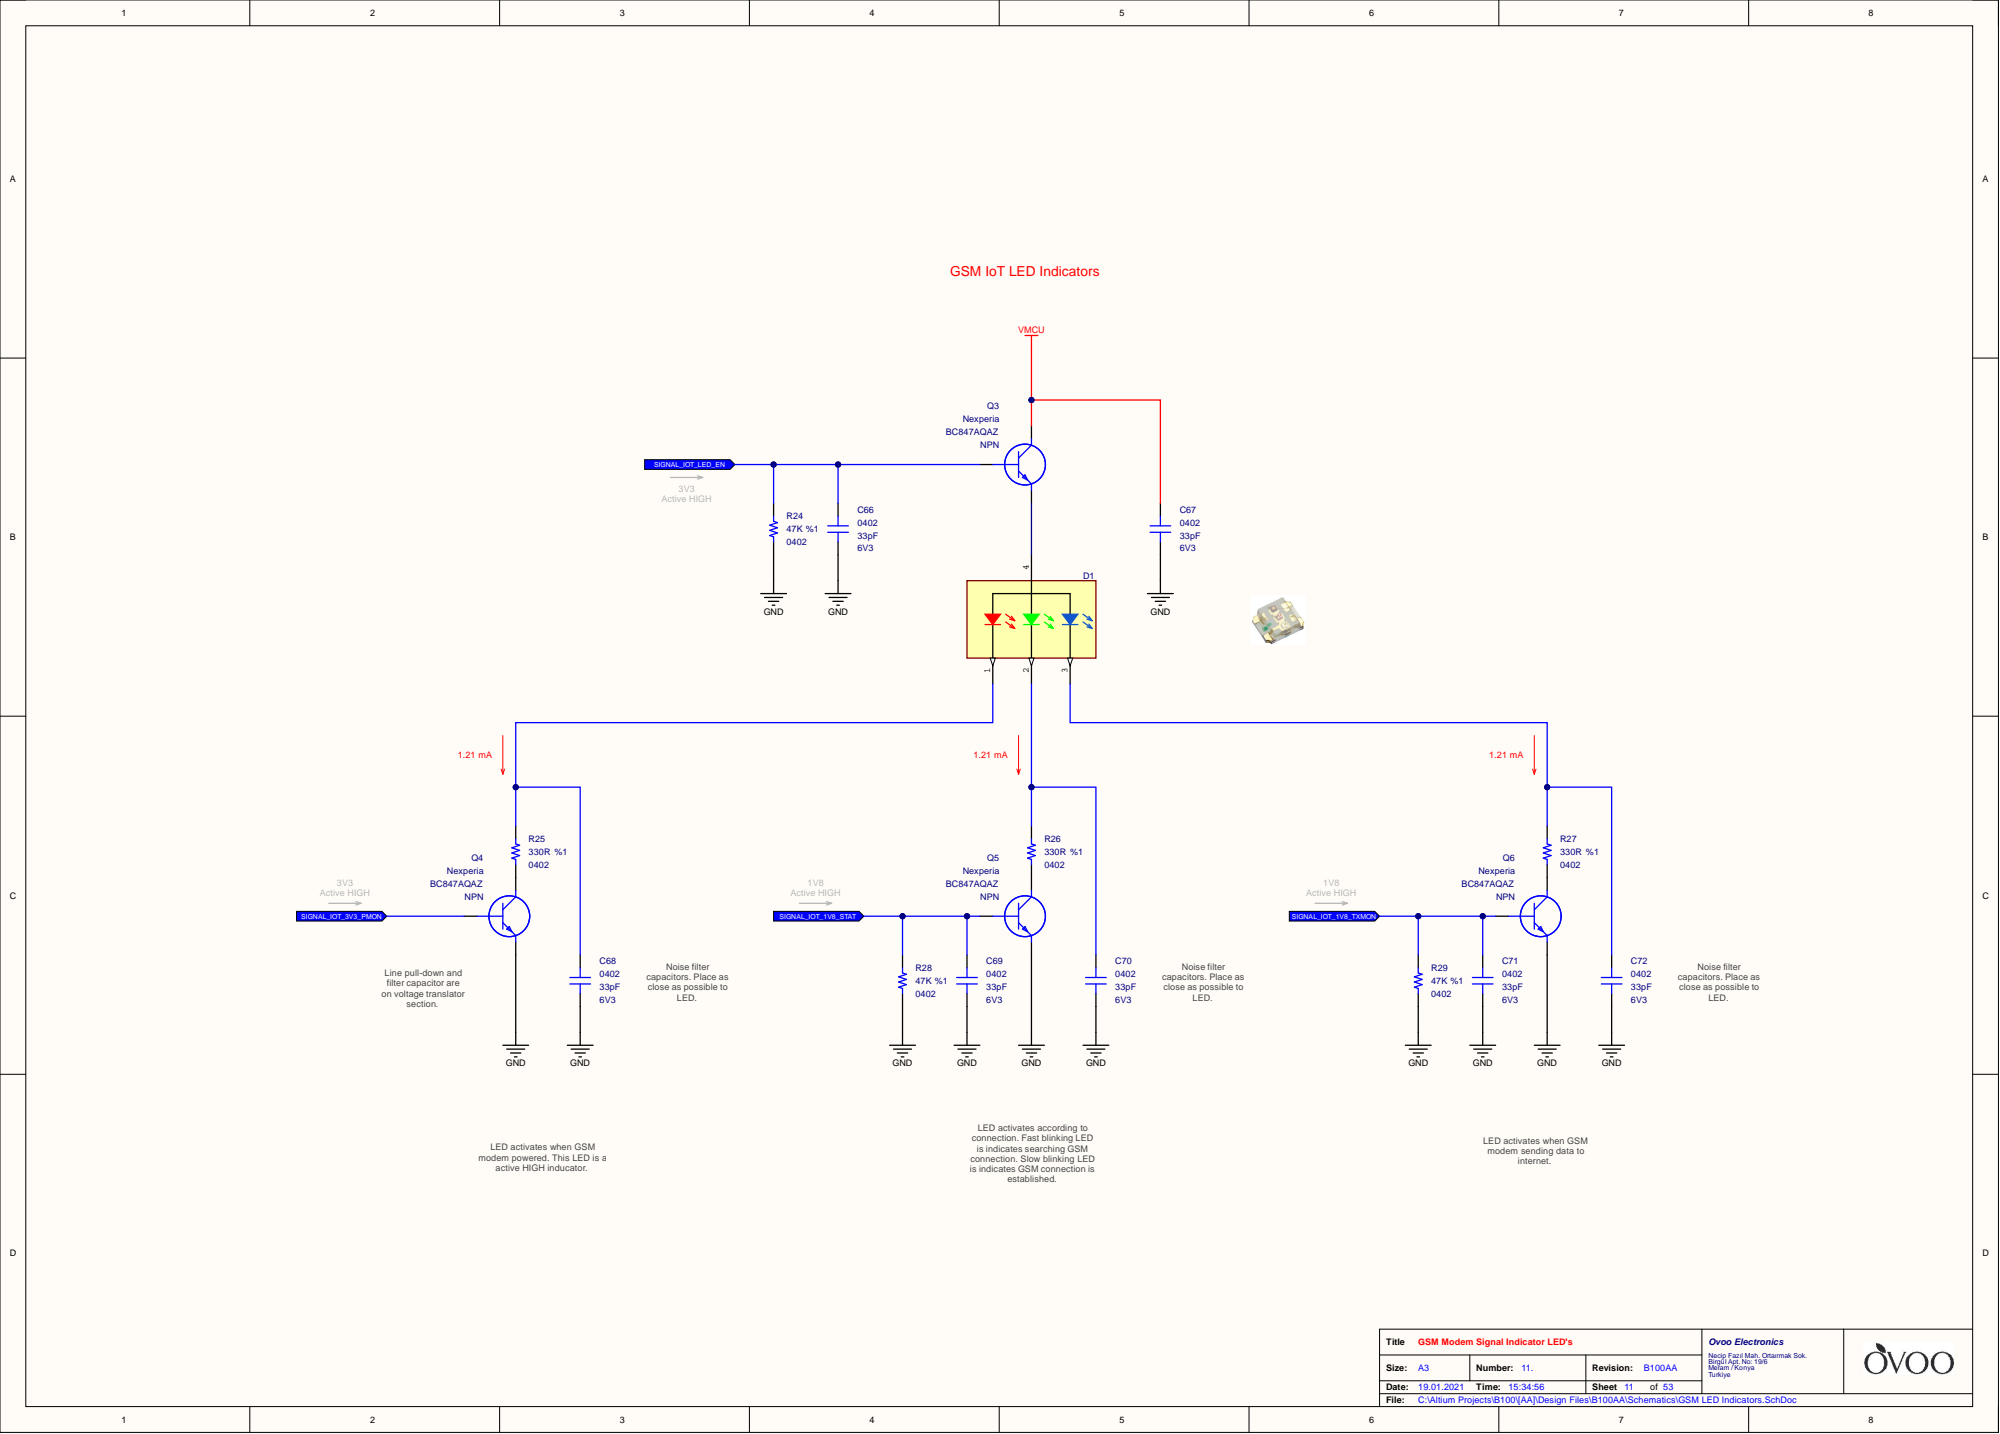
[picture p225: page 11]

GSM IoT LED Indicators

Noise filter
capacitors. Place as
close as possible to

Line pull-down and
filter capacitor are
on voltage translator

LED activates according to
connection. Fast blinking LED
is indicates searching GSM
connection. Slow blinking LED
is indicates GSM connection is

LED activates when GSM
modem sending data to

modem powered. This LED is a
active HIGH inducator.

GSM Modem Signal Indicator LED's

C:\Altium Projects\B100\[AA]\Design Files\B100AA\Schematics\GSM LED Indicators.SchDoc

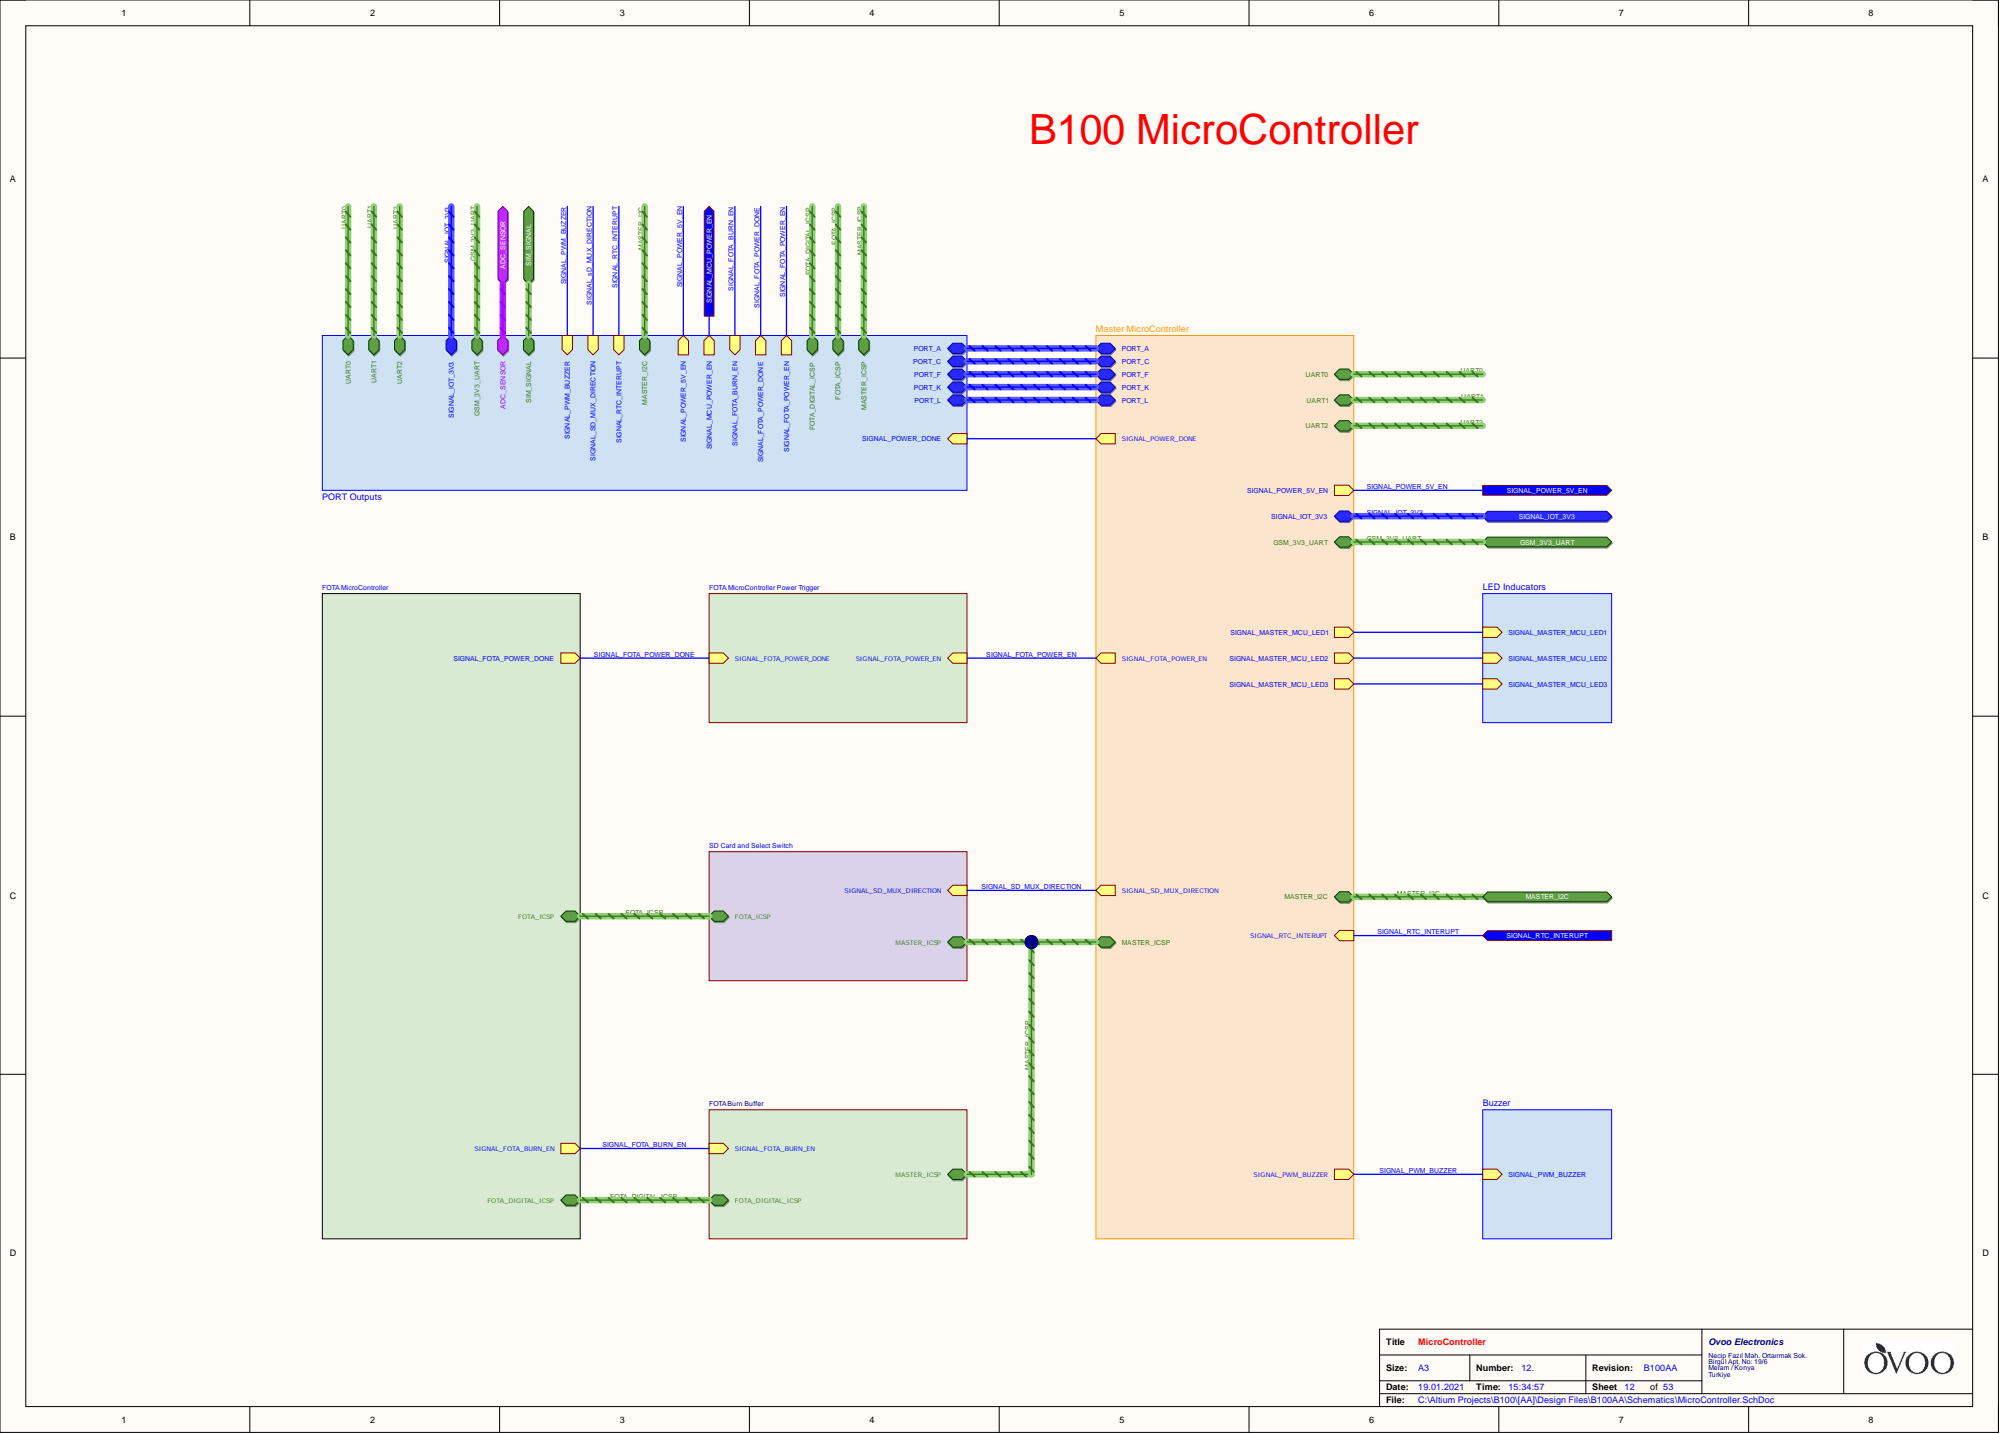
[picture p226: page 12]

FOTA MicroController Power Trigger

SD Card and Select Switch

C:\Altium Projects\B100\[AA]\Design Files\B100AA\Schematics\MicroController.SchDoc

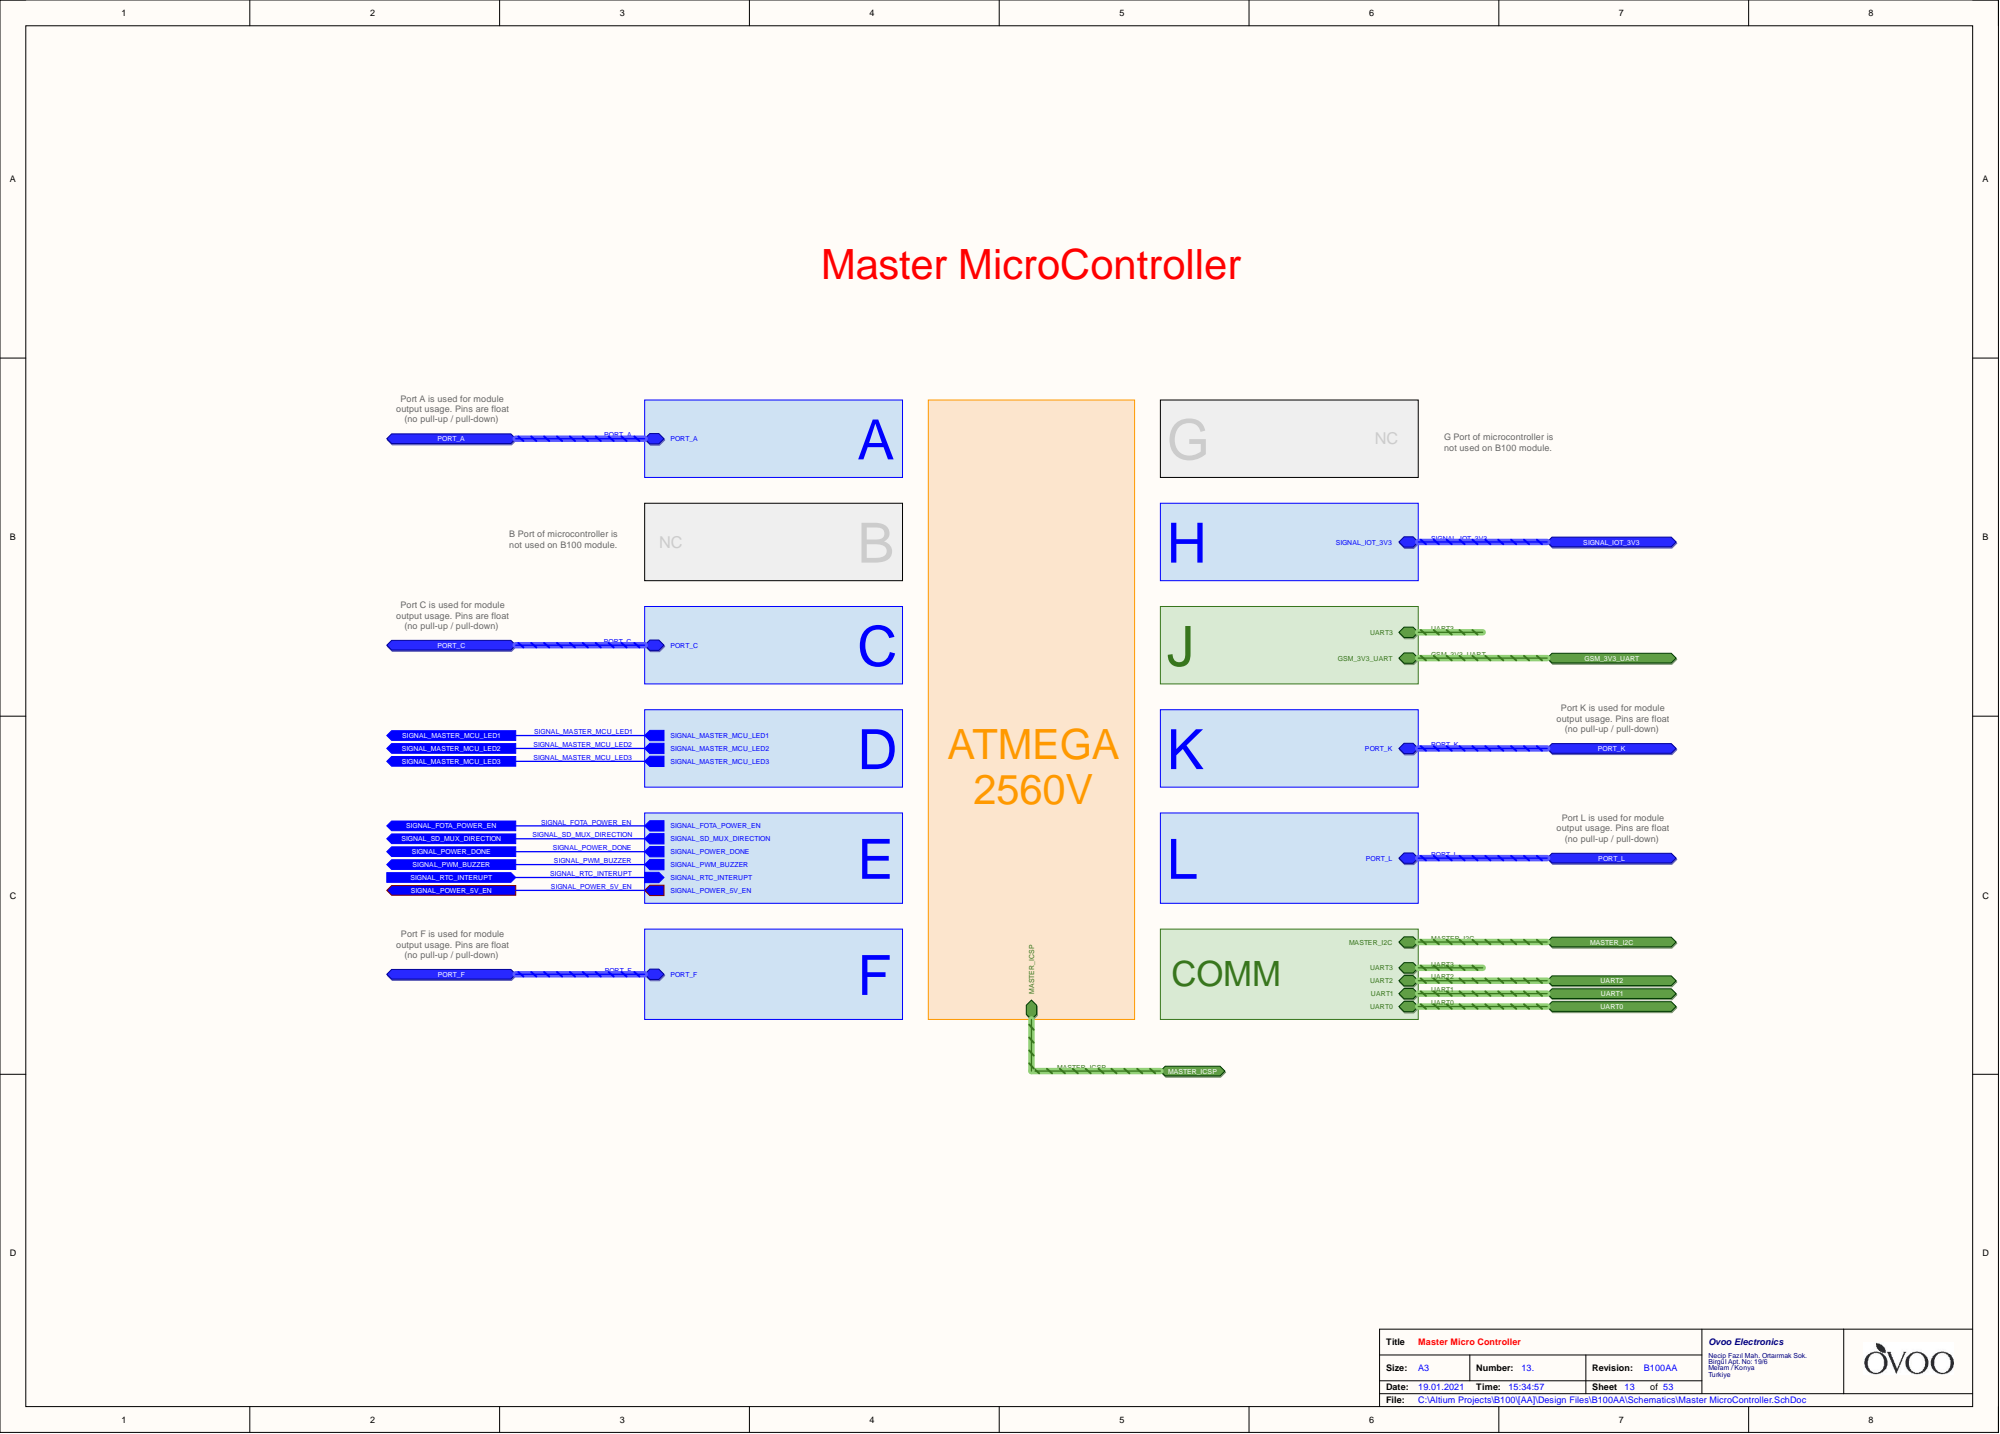
[picture p227: page 13]

Port A is used for module
output usage. Pins are float
(no pull-up / pull-down)

G Port of microcontroller is
not used on B100 module.

B Port of microcontroller is

Port C is used for module

Port K is used for module

Port L is used for module

Port F is used for module

C:\Altium Projects\B100\[AA]\Design Files\B100AA\Schematics\Master MicroController.SchDoc

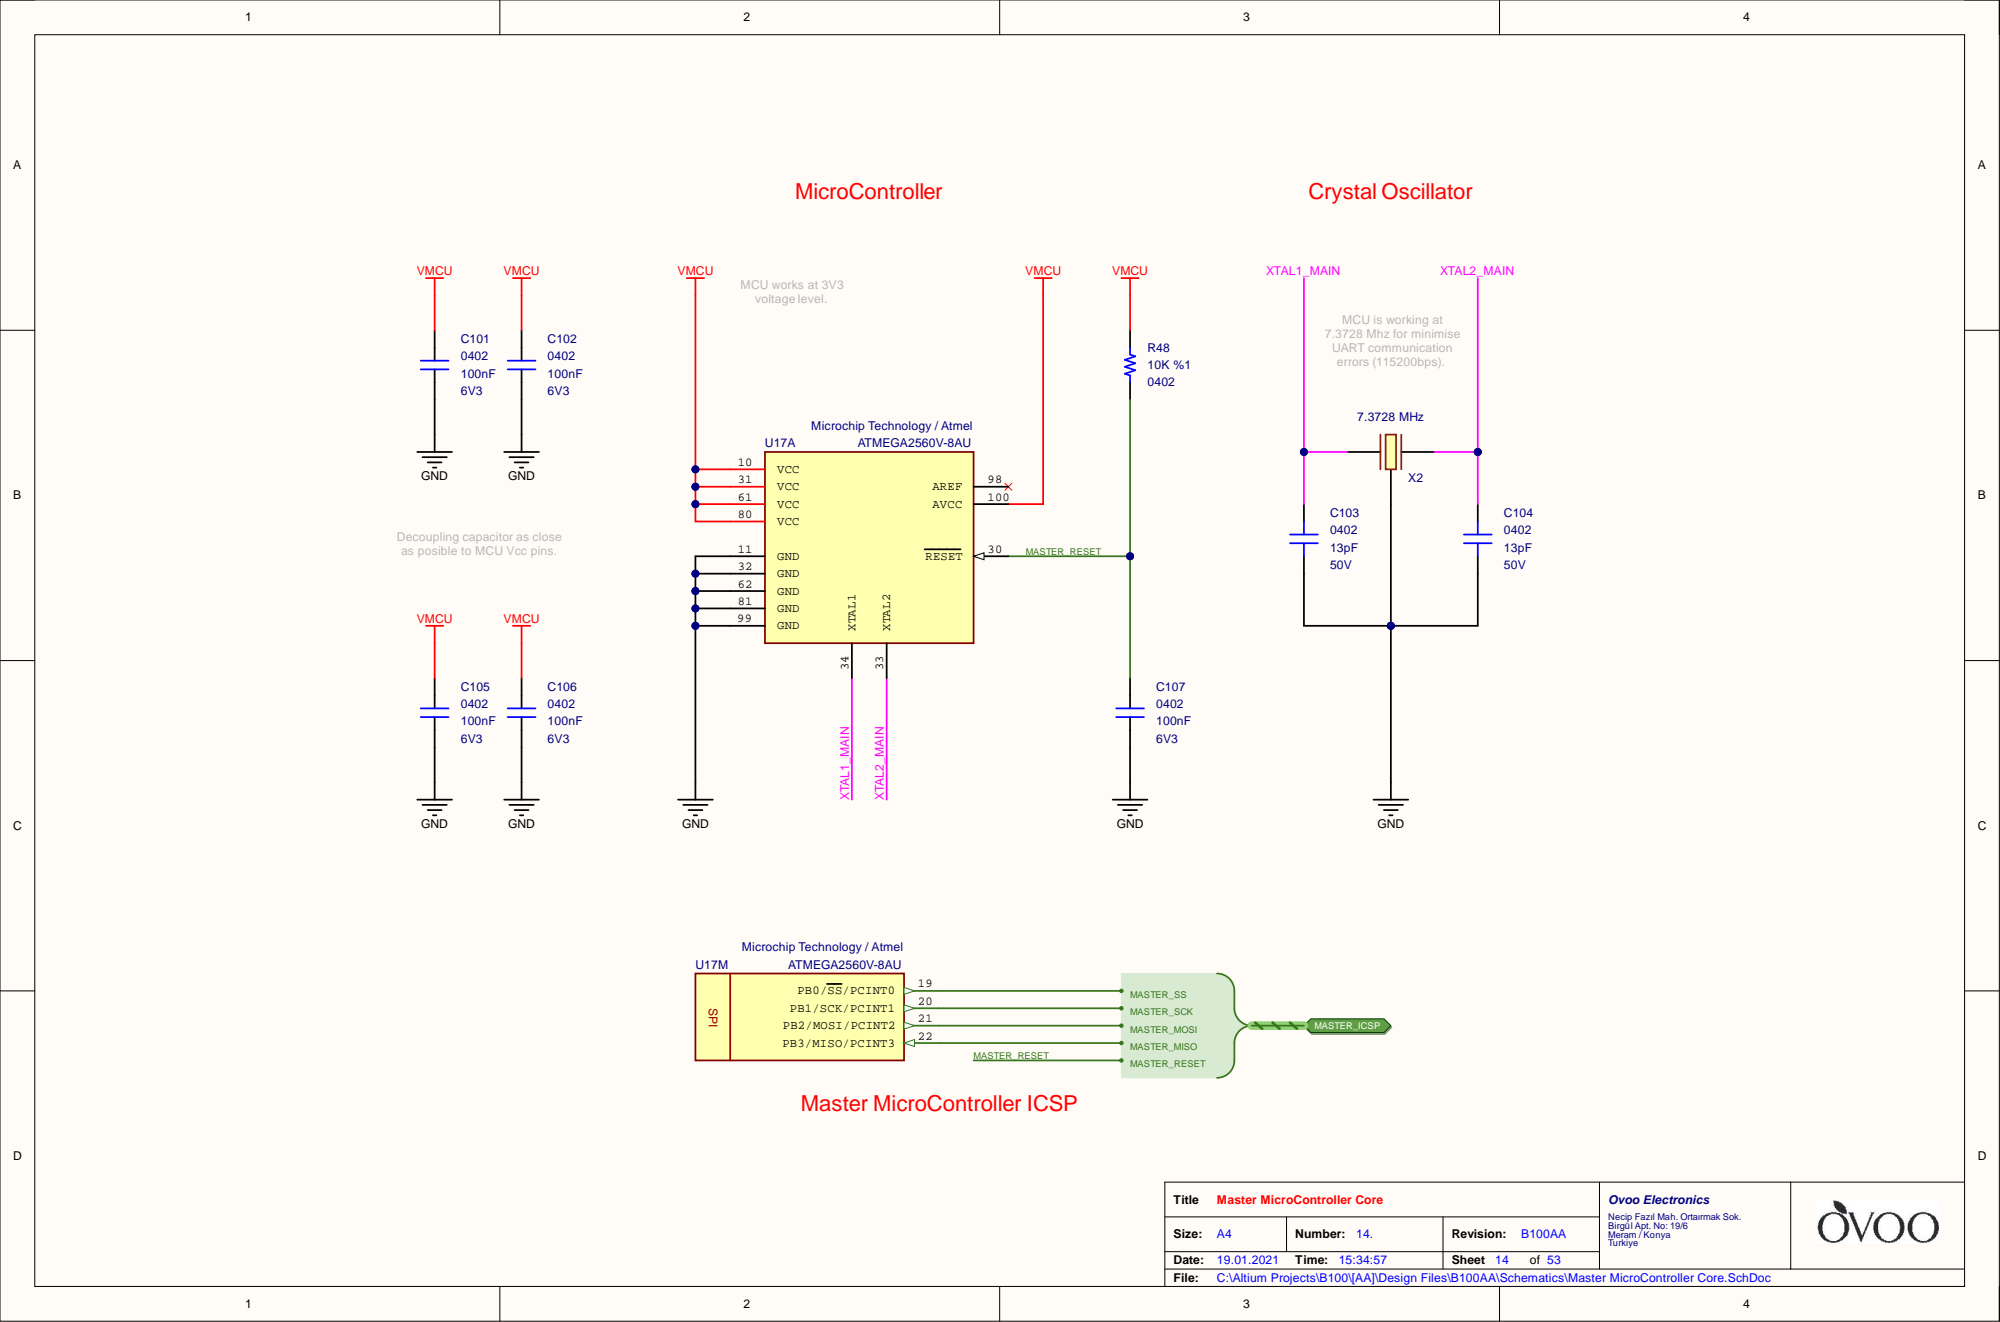
[picture p228: page 14]

MCU is working at
7.3728 Mhz for minimise
UART communication
errors (115200bps).

Decoupling capacitor as close
as posible to MCU Vcc pins.

C:\Altium Projects\B100\[AA]\Design Files\B100AA\Schematics\Master MicroController Core.SchDoc

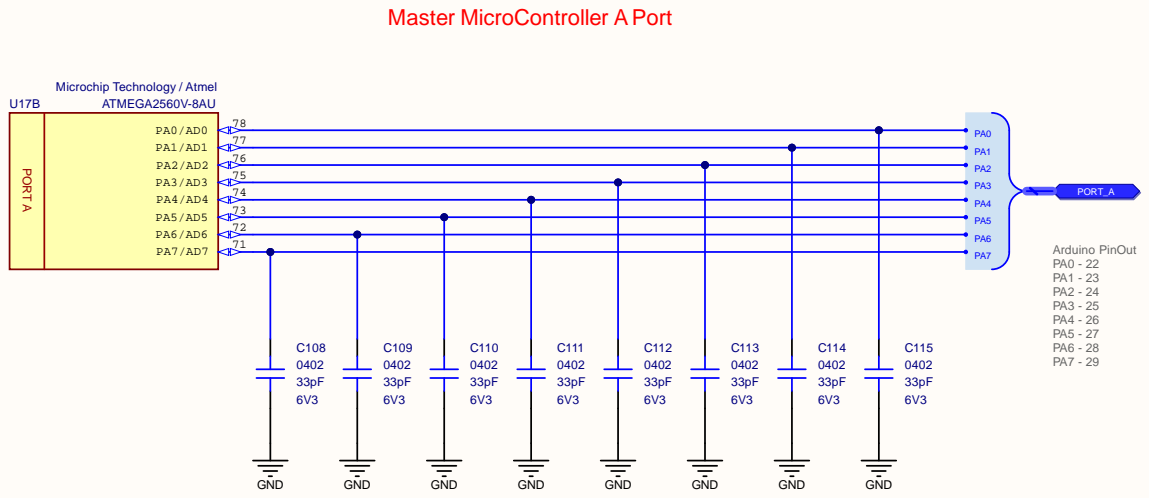
[picture p229: page 15]

Master Micro Controller Port A Pin Out

C:\Altium Projects\B100\[AA]\Design Files\B100AA\Schematics\Master MicroController Port A.SchDoc

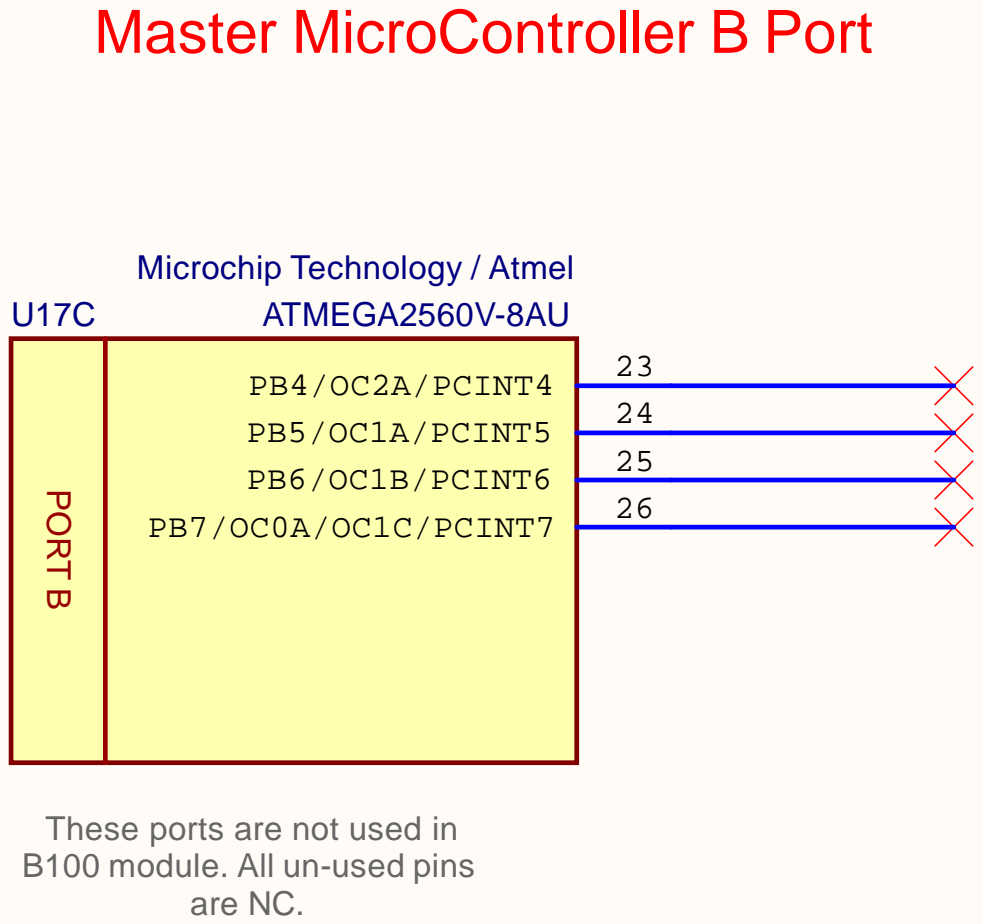
[picture p230: page 16]

These ports are not used in
B100 module. All un-used pins

Master Micro Controller Port B Pin Out

C:\Altium Projects\B100\[AA]\Design Files\B100AA\Schematics\Master MicroController Port B.SchDoc

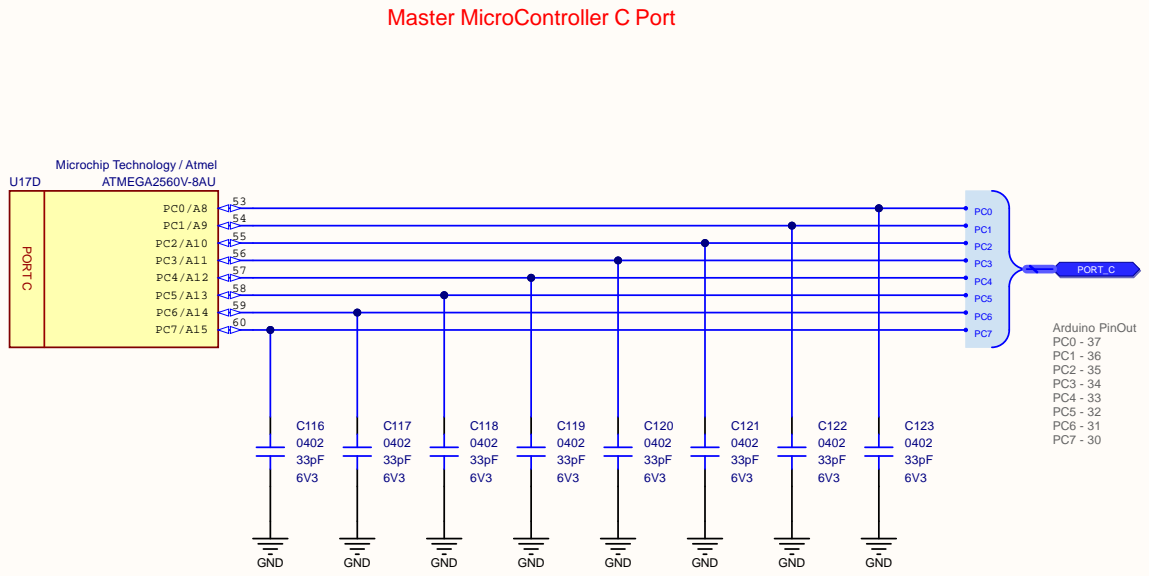
[picture p231: page 17]

Master Micro Controller Port C Pin Out

C:\Altium Projects\B100\[AA]\Design Files\B100AA\Schematics\Master MicroController Port C.SchDoc

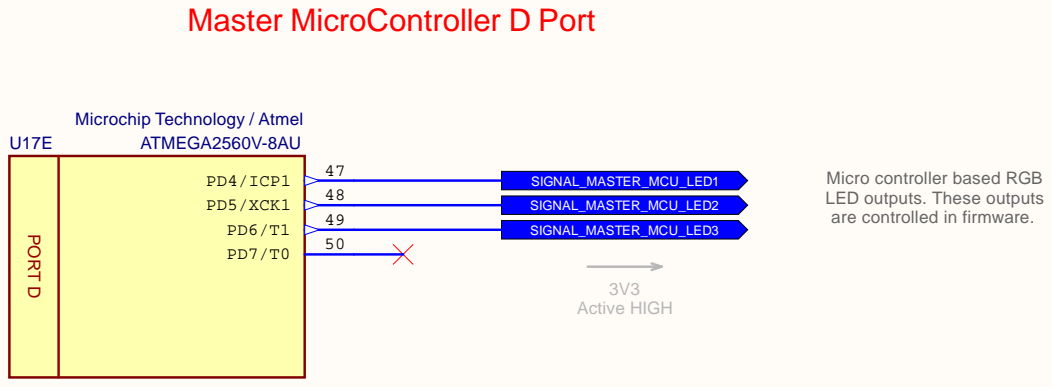
[picture p232: page 18]

Micro controller based RGB
LED outputs. These outputs
are controlled in firmware.

Master Micro Controller Port D Pin Out

C:\Altium Projects\B100\[AA]\Design Files\B100AA\Schematics\Master MicroController Port D.SchDoc

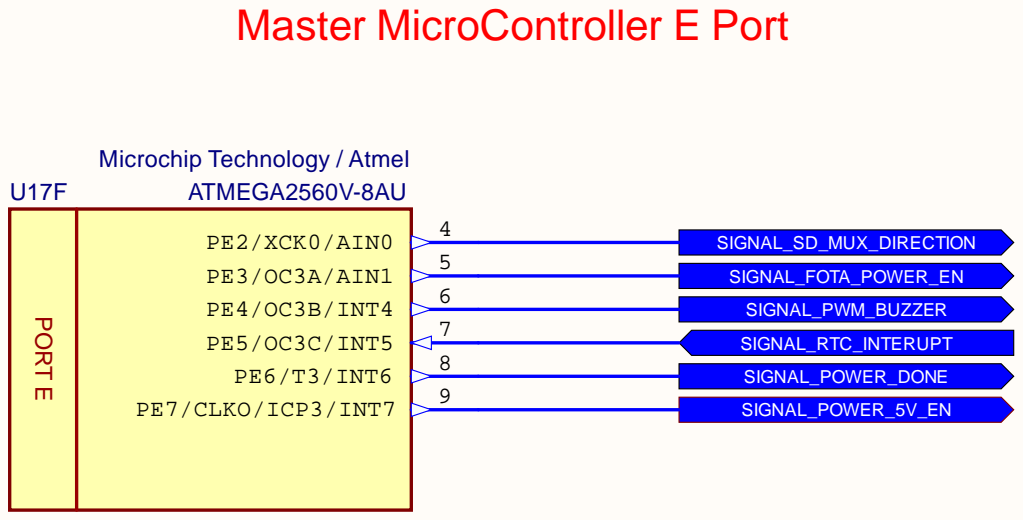
[picture p233: page 19]

Master Micro Controller Port E Pin Out

C:\Altium Projects\B100\[AA]\Design Files\B100AA\Schematics\Master MicroController Port E.SchDoc

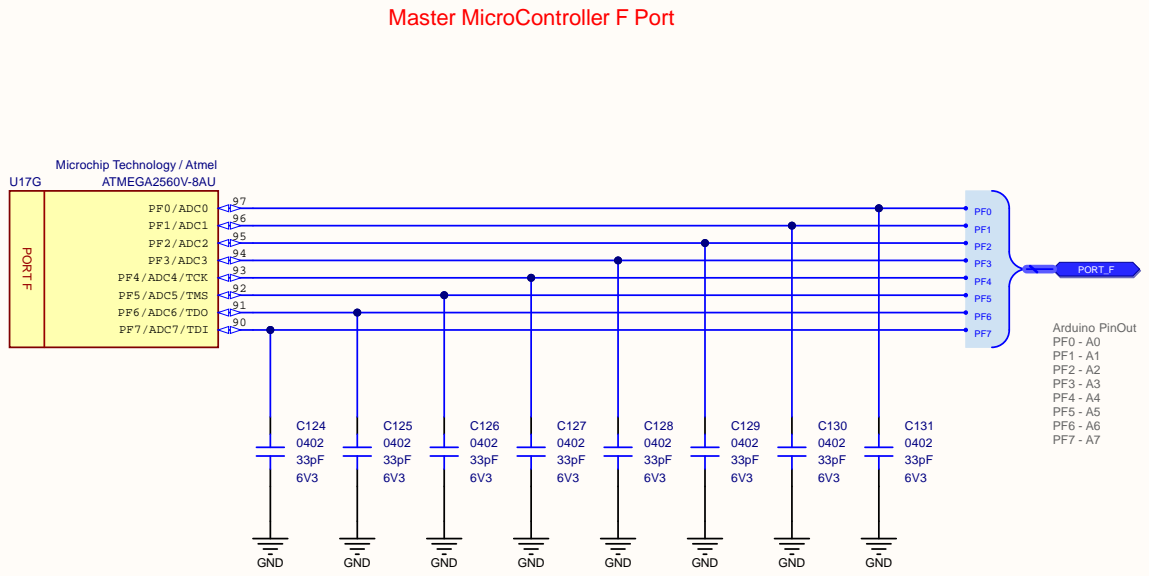
[picture p234: page 20]

Master Micro Controller Port F Pin Out

C:\Altium Projects\B100\[AA]\Design Files\B100AA\Schematics\Master MicroController Port F.SchDoc


These ports are not used in
B100 module. All un-used pins

Master Micro Controller Port G Pin Out

C:\Altium Projects\B100\[AA]\Design Files\B100AA\Schematics\Master MicroController Port G.SchDoc

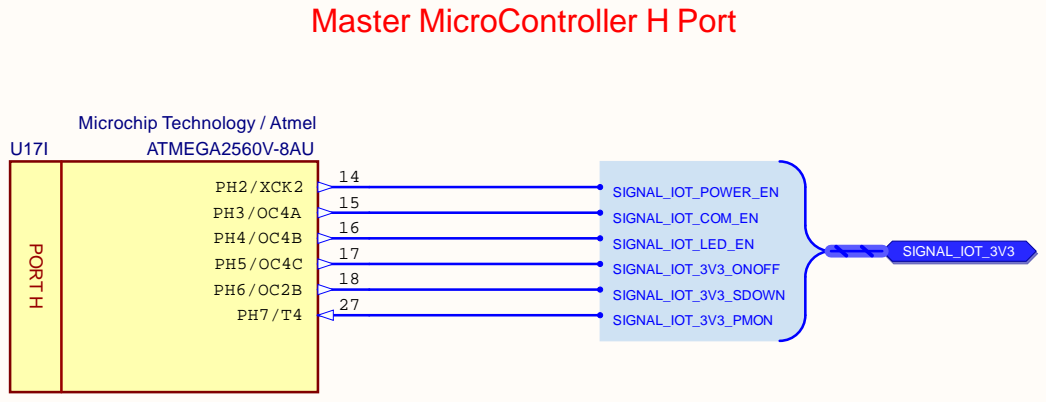
[picture p235: page 22]

Master Micro Controller Port H Pin Out

C:\Altium Projects\B100\[AA]\Design Files\B100AA\Schematics\Master MicroController Port H.SchDoc

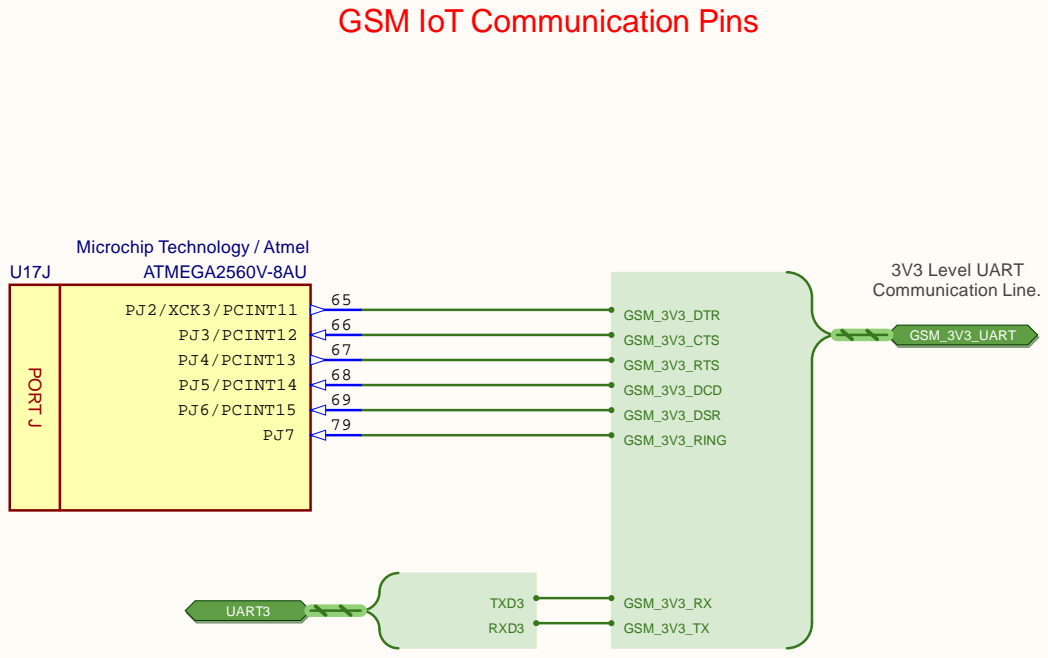
[picture p236: page 23]

GSM IoT Communication Pins

Master Micro Controller Port J Pin Out

C:\Altium Projects\B100\[AA]\Design Files\B100AA\Schematics\Master MicroController Port J.SchDoc

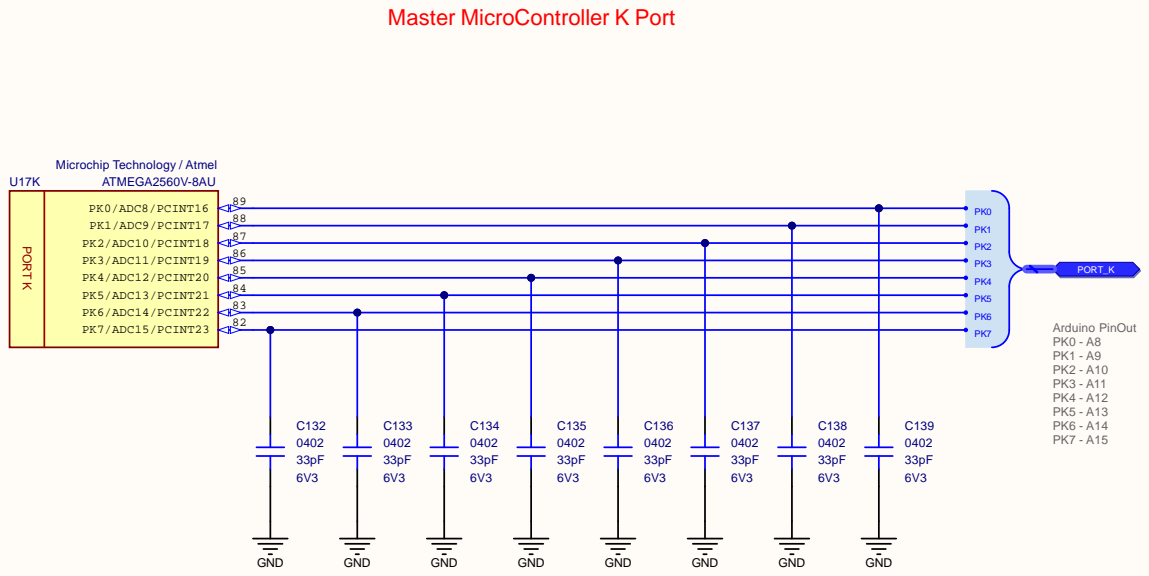
[picture p237: page 24]

Master Micro Controller Port K Pin Out

C:\Altium Projects\B100\[AA]\Design Files\B100AA\Schematics\Master MicroController Port K.SchDoc

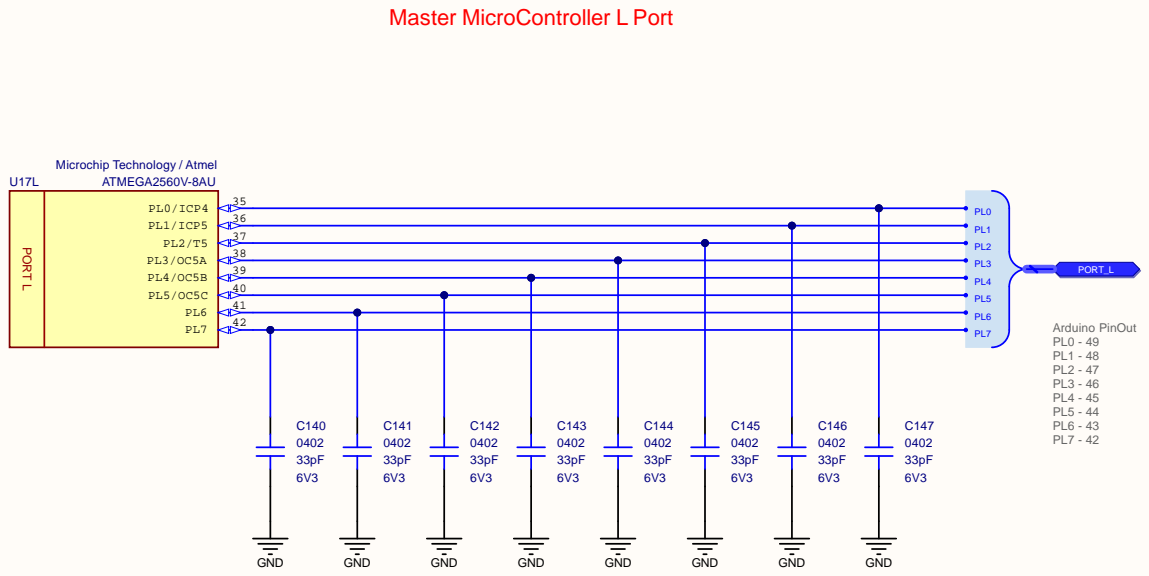
[picture p238: page 25]

Master Micro Controller Port L Pin Out

C:\Altium Projects\B100\[AA]\Design Files\B100AA\Schematics\Master MicroController Port L.SchDoc

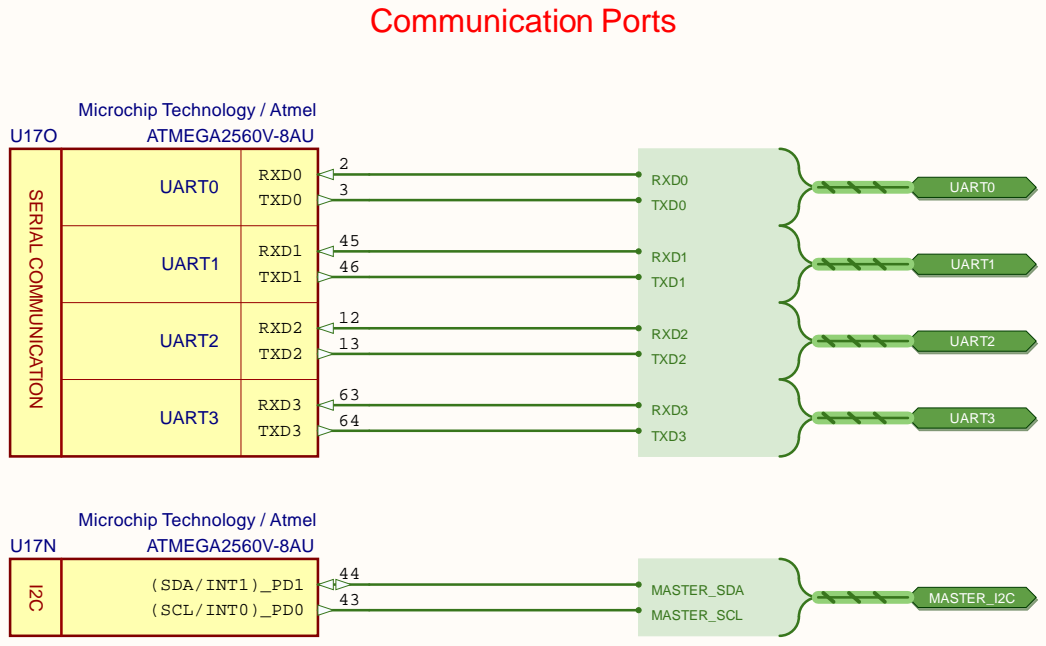
[picture p239: page 26]

UART0

UART1

UART2

UART3

Master MicroController Serial Communication Port

C:\Altium Projects\B100\[AA]\Design Files\B100AA\Schematics\Master MicroController Serial Communication Port.SchDoc

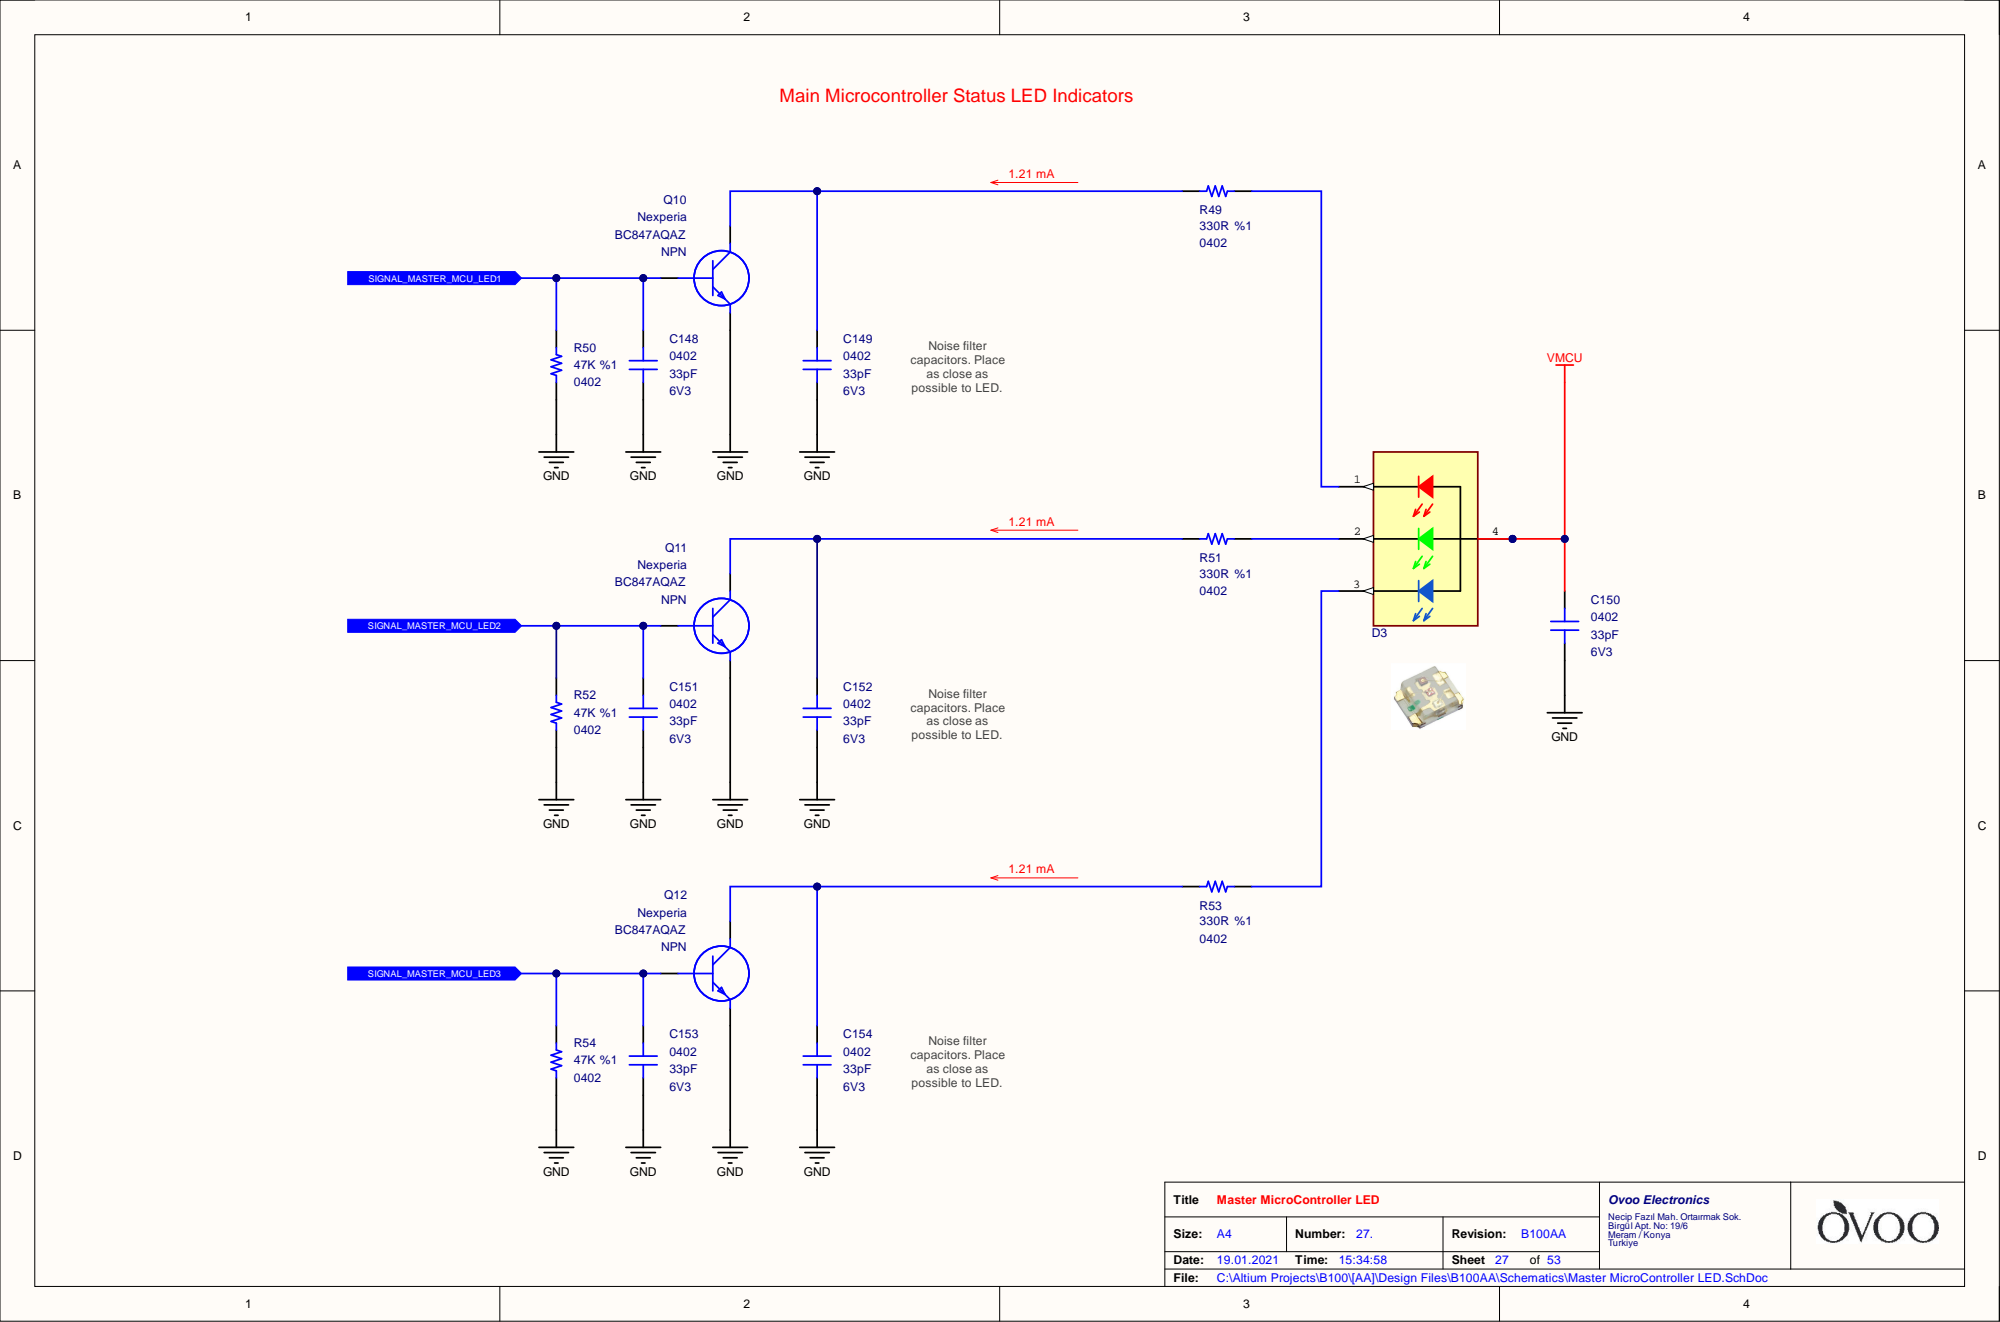
[picture p240: page 27]

Main Microcontroller Status LED Indicators

C:\Altium Projects\B100\[AA]\Design Files\B100AA\Schematics\Master MicroController LED.SchDoc

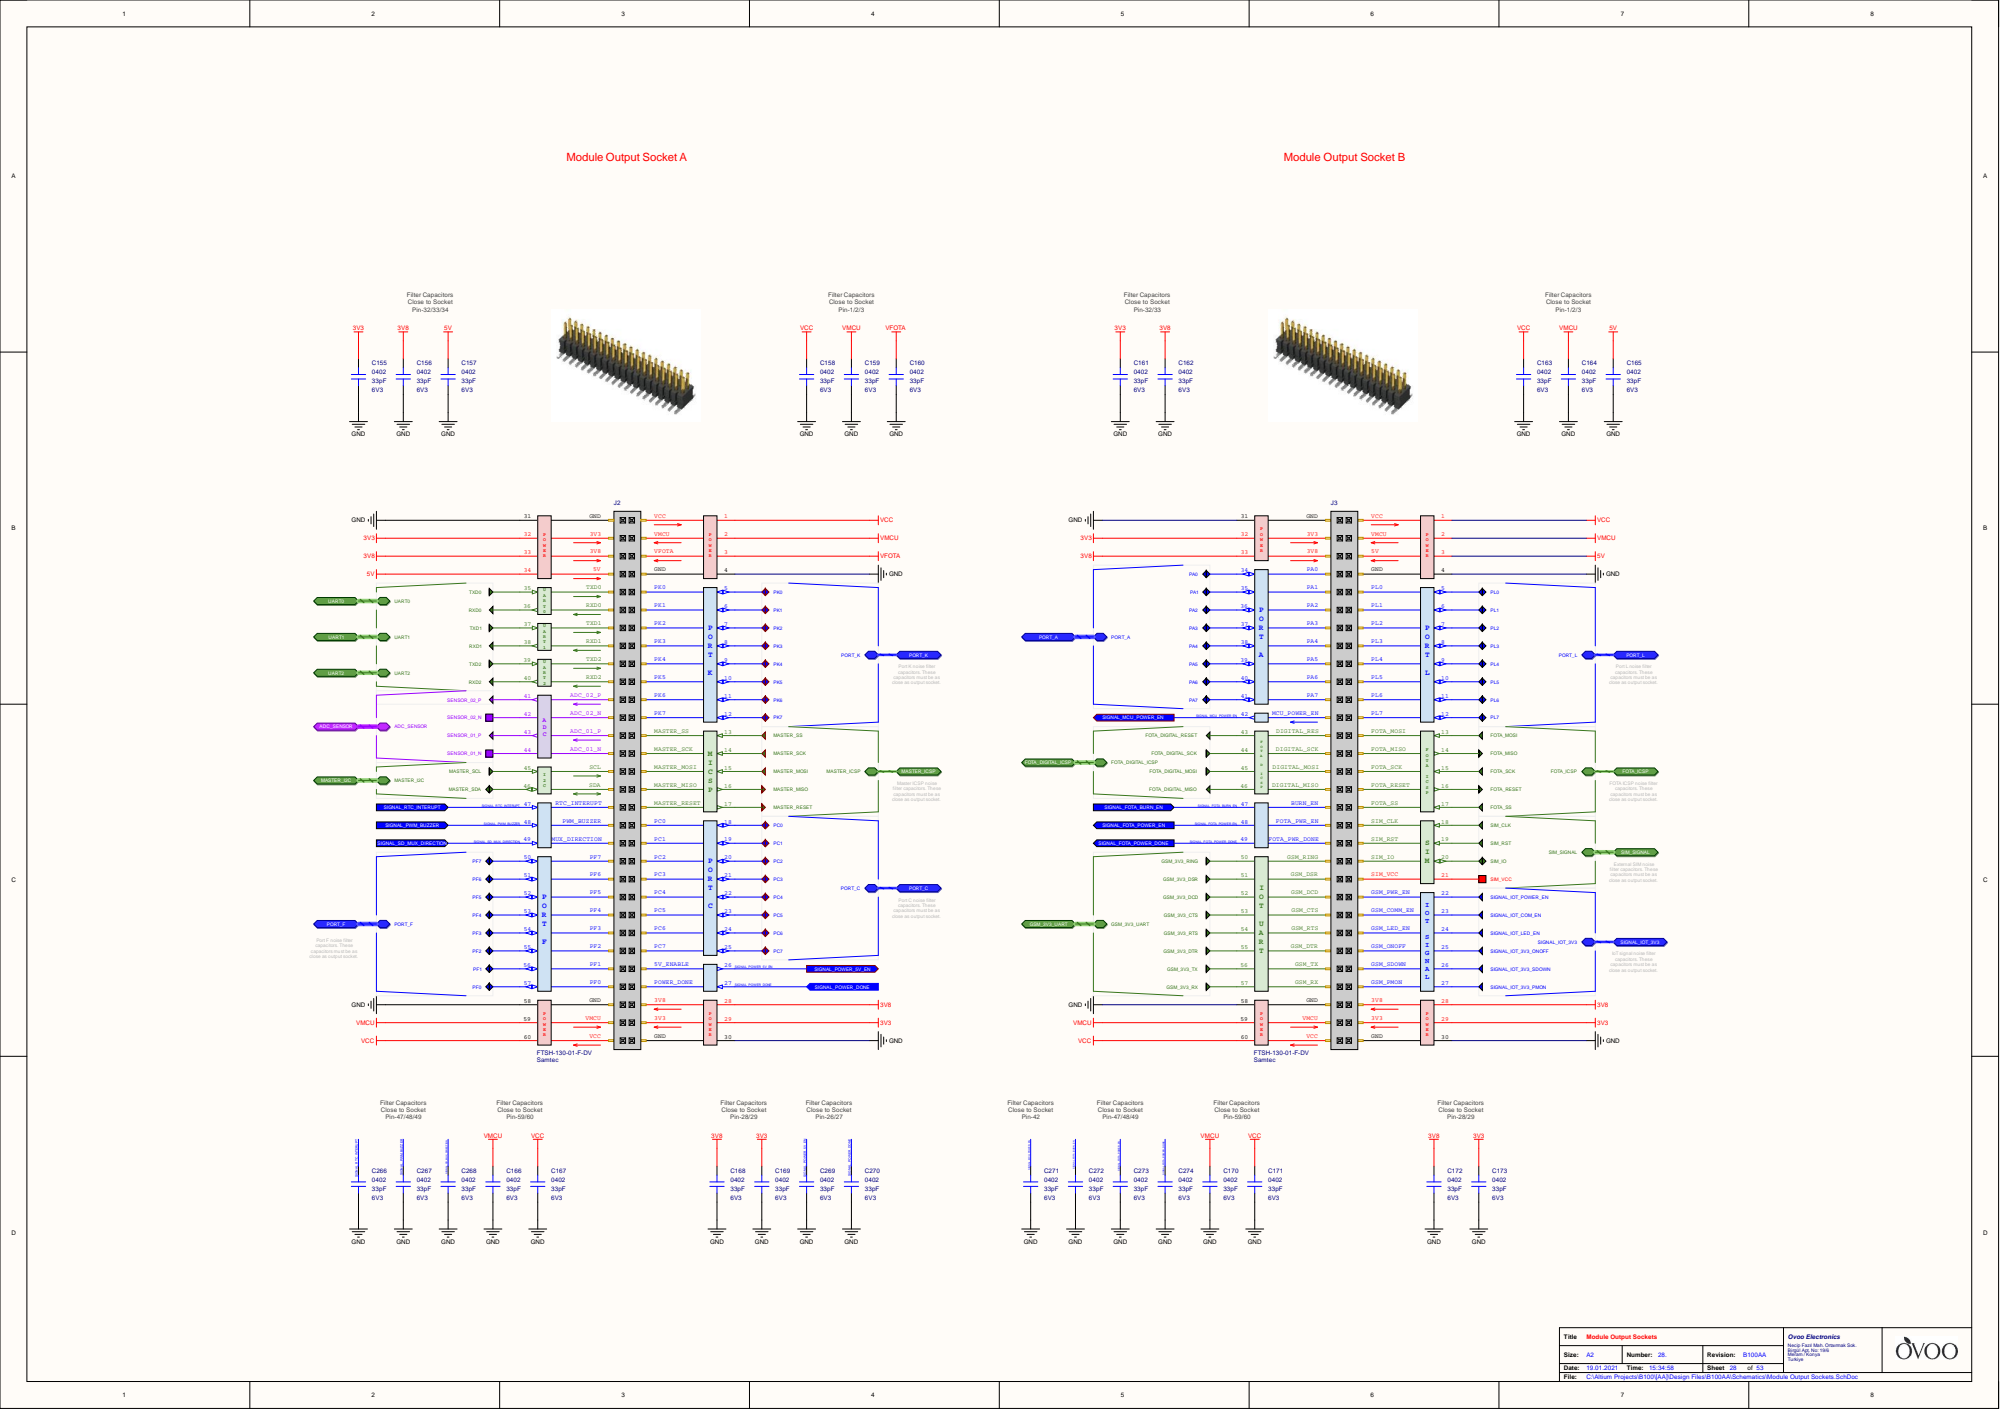
[picture p241: page 28]

Port K noise filter
capacitors. These
capacitors must be as
close as output socket.

Port L noise filter

42 | | ADC_02_N | PK7 | 12 | PL7 | 12
43 44 | A D C | ADC_01_P ADC_01_N

Master ICSP noise
filter capacitors. These

FOTA ICSP noise filter

External SIM noise

Port C noise filter

Port F noise filter

IoT signal noise filter

C:\Altium Projects\B100\[AA]\Design Files\B100AA\Schematics\Module Output Sockets.SchDoc

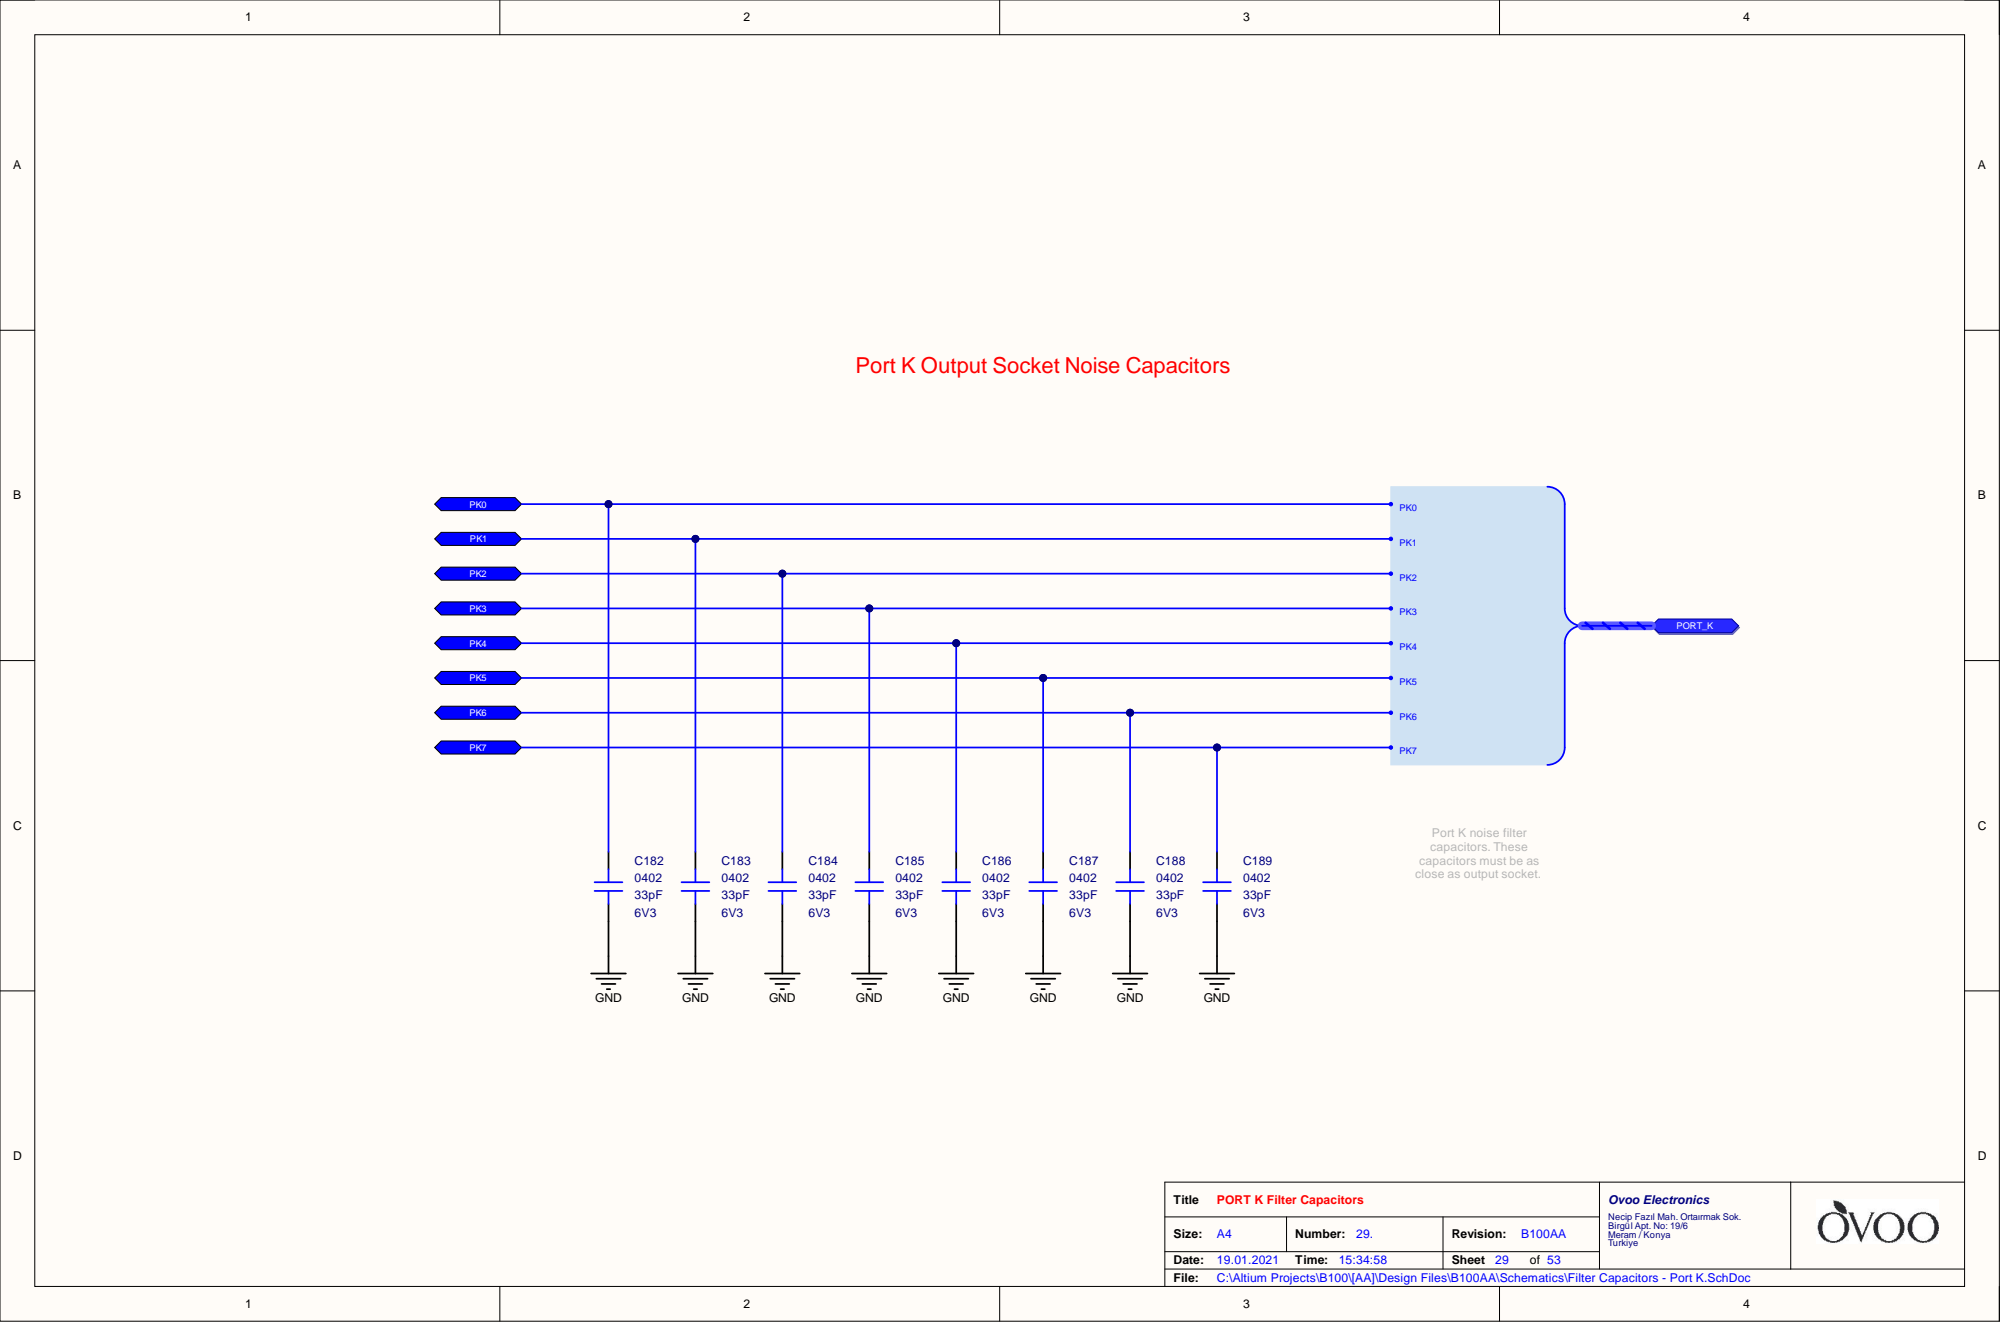
[picture p242: page 29]

Port K Output Socket Noise Capacitors

Port K noise filter
capacitors. These
capacitors must be as
close as output socket.

C:\Altium Projects\B100\[AA]\Design Files\B100AA\Schematics\Filter Capacitors - Port K.SchDoc

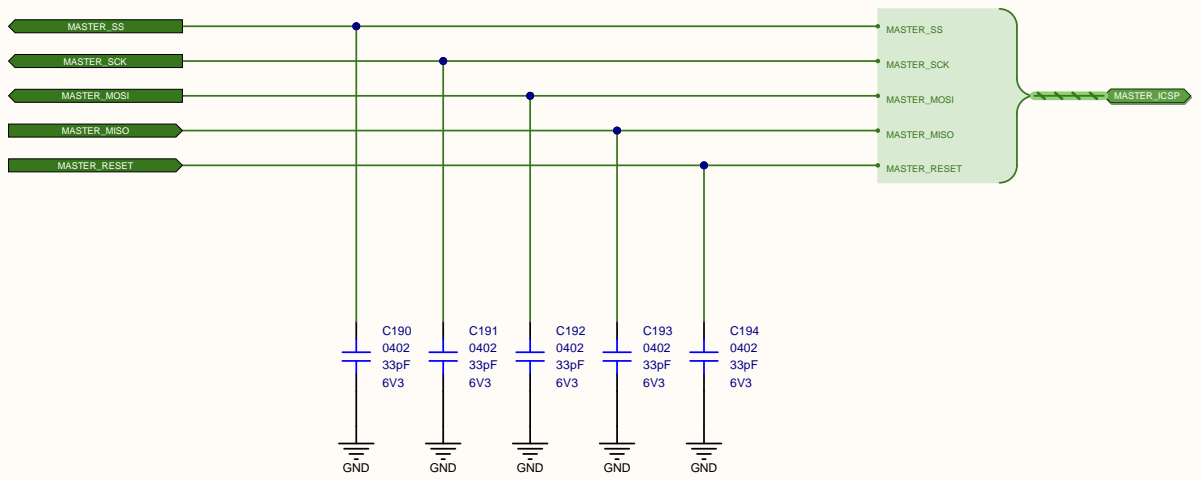
[picture p243: page 30]

Master ICSP Filter Capacitors

C:\Altium Projects\B100\[AA]\Design Files\B100AA\Schematics\Filter Capacitors - Master ICSP.SchDoc

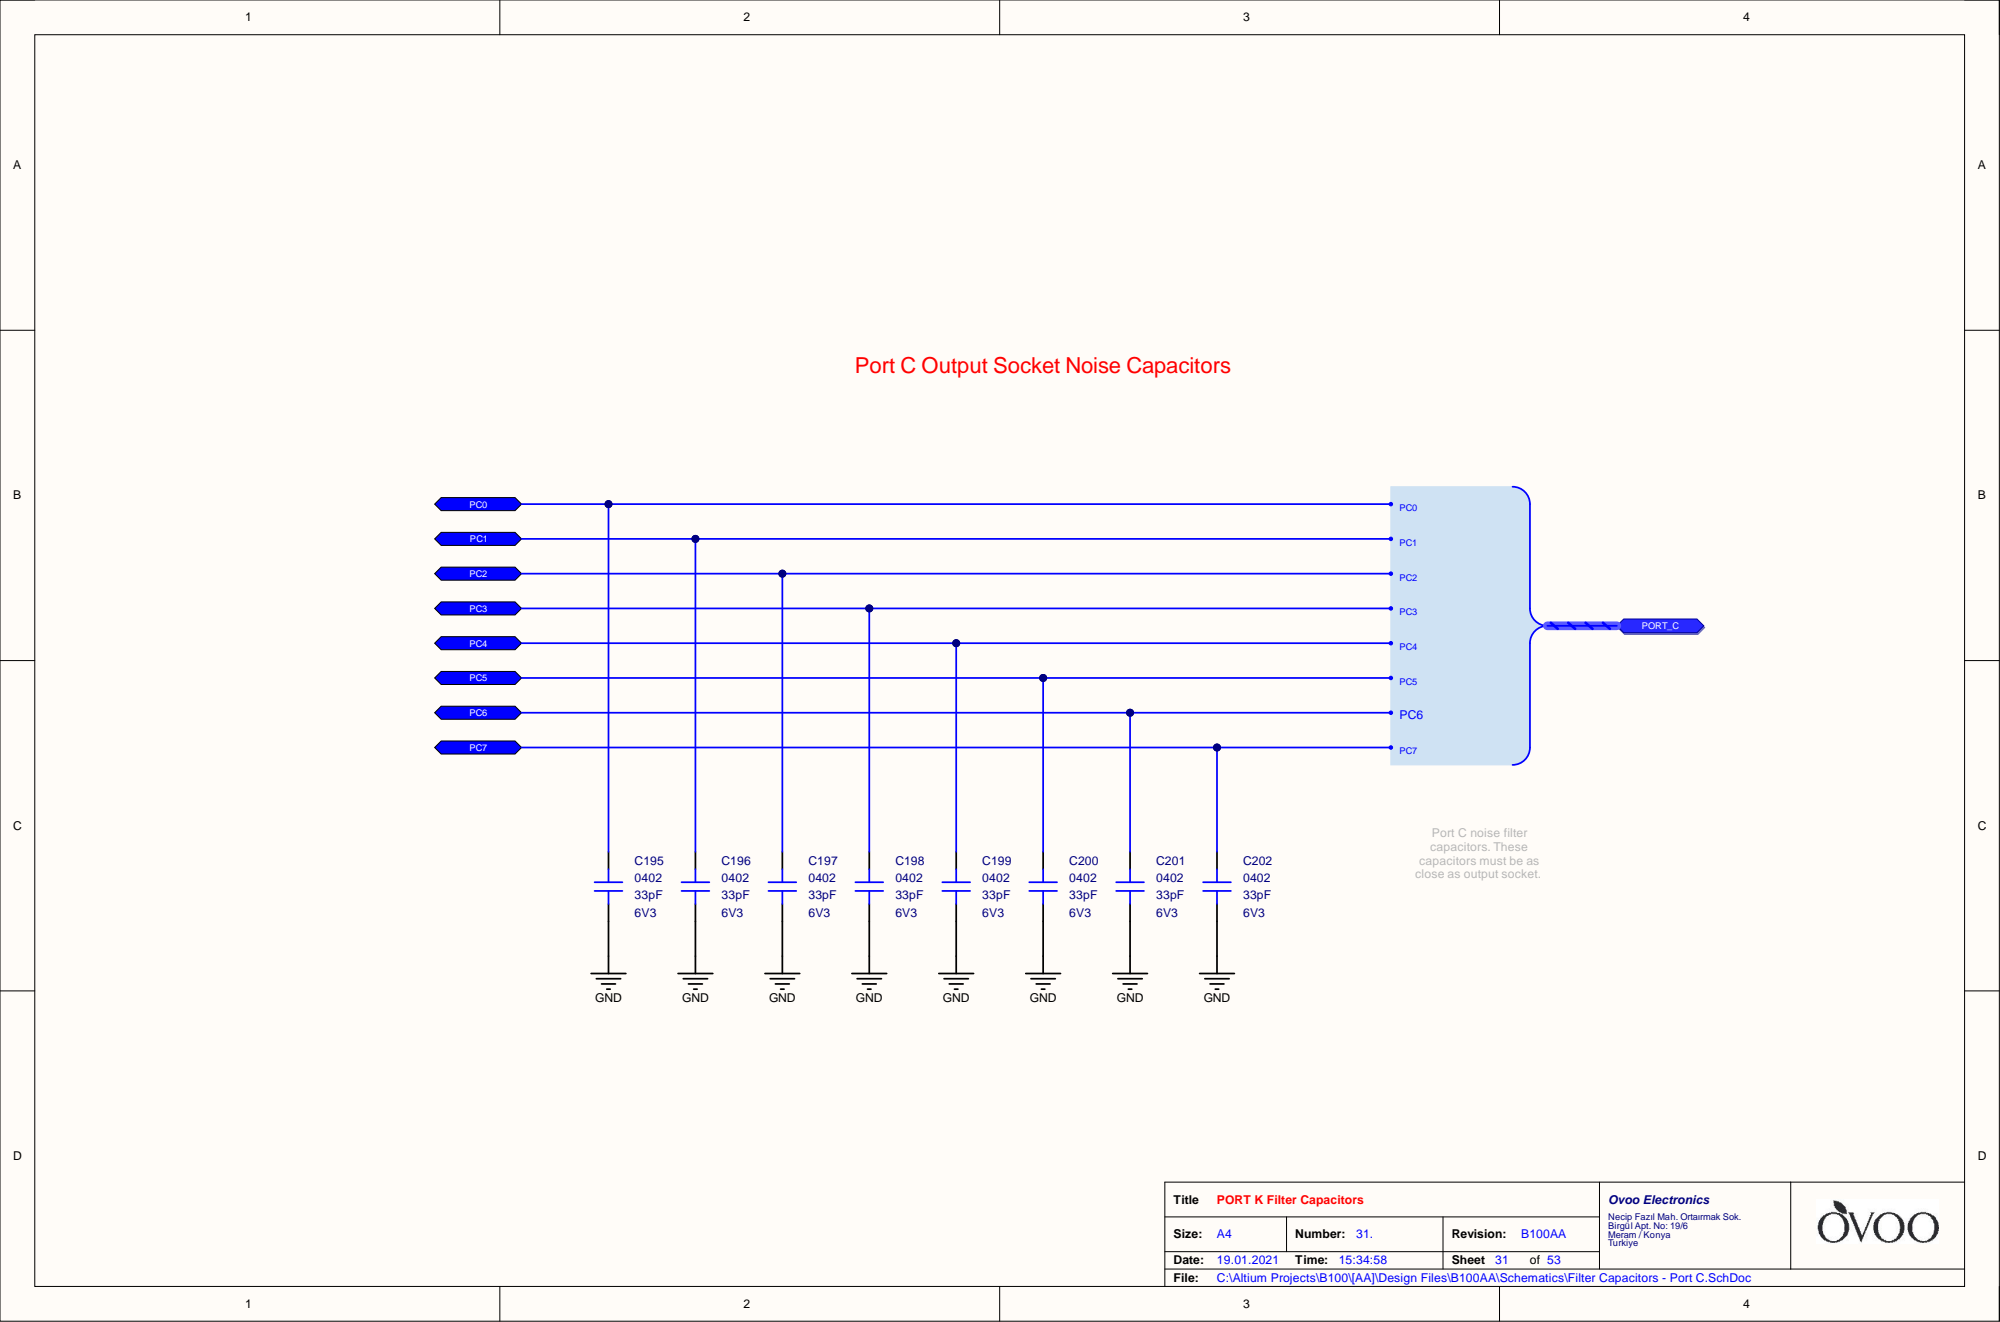
[picture p244: page 31]

Port C Output Socket Noise Capacitors

Port C noise filter
capacitors. These
capacitors must be as
close as output socket.

C:\Altium Projects\B100\[AA]\Design Files\B100AA\Schematics\Filter Capacitors - Port C.SchDoc

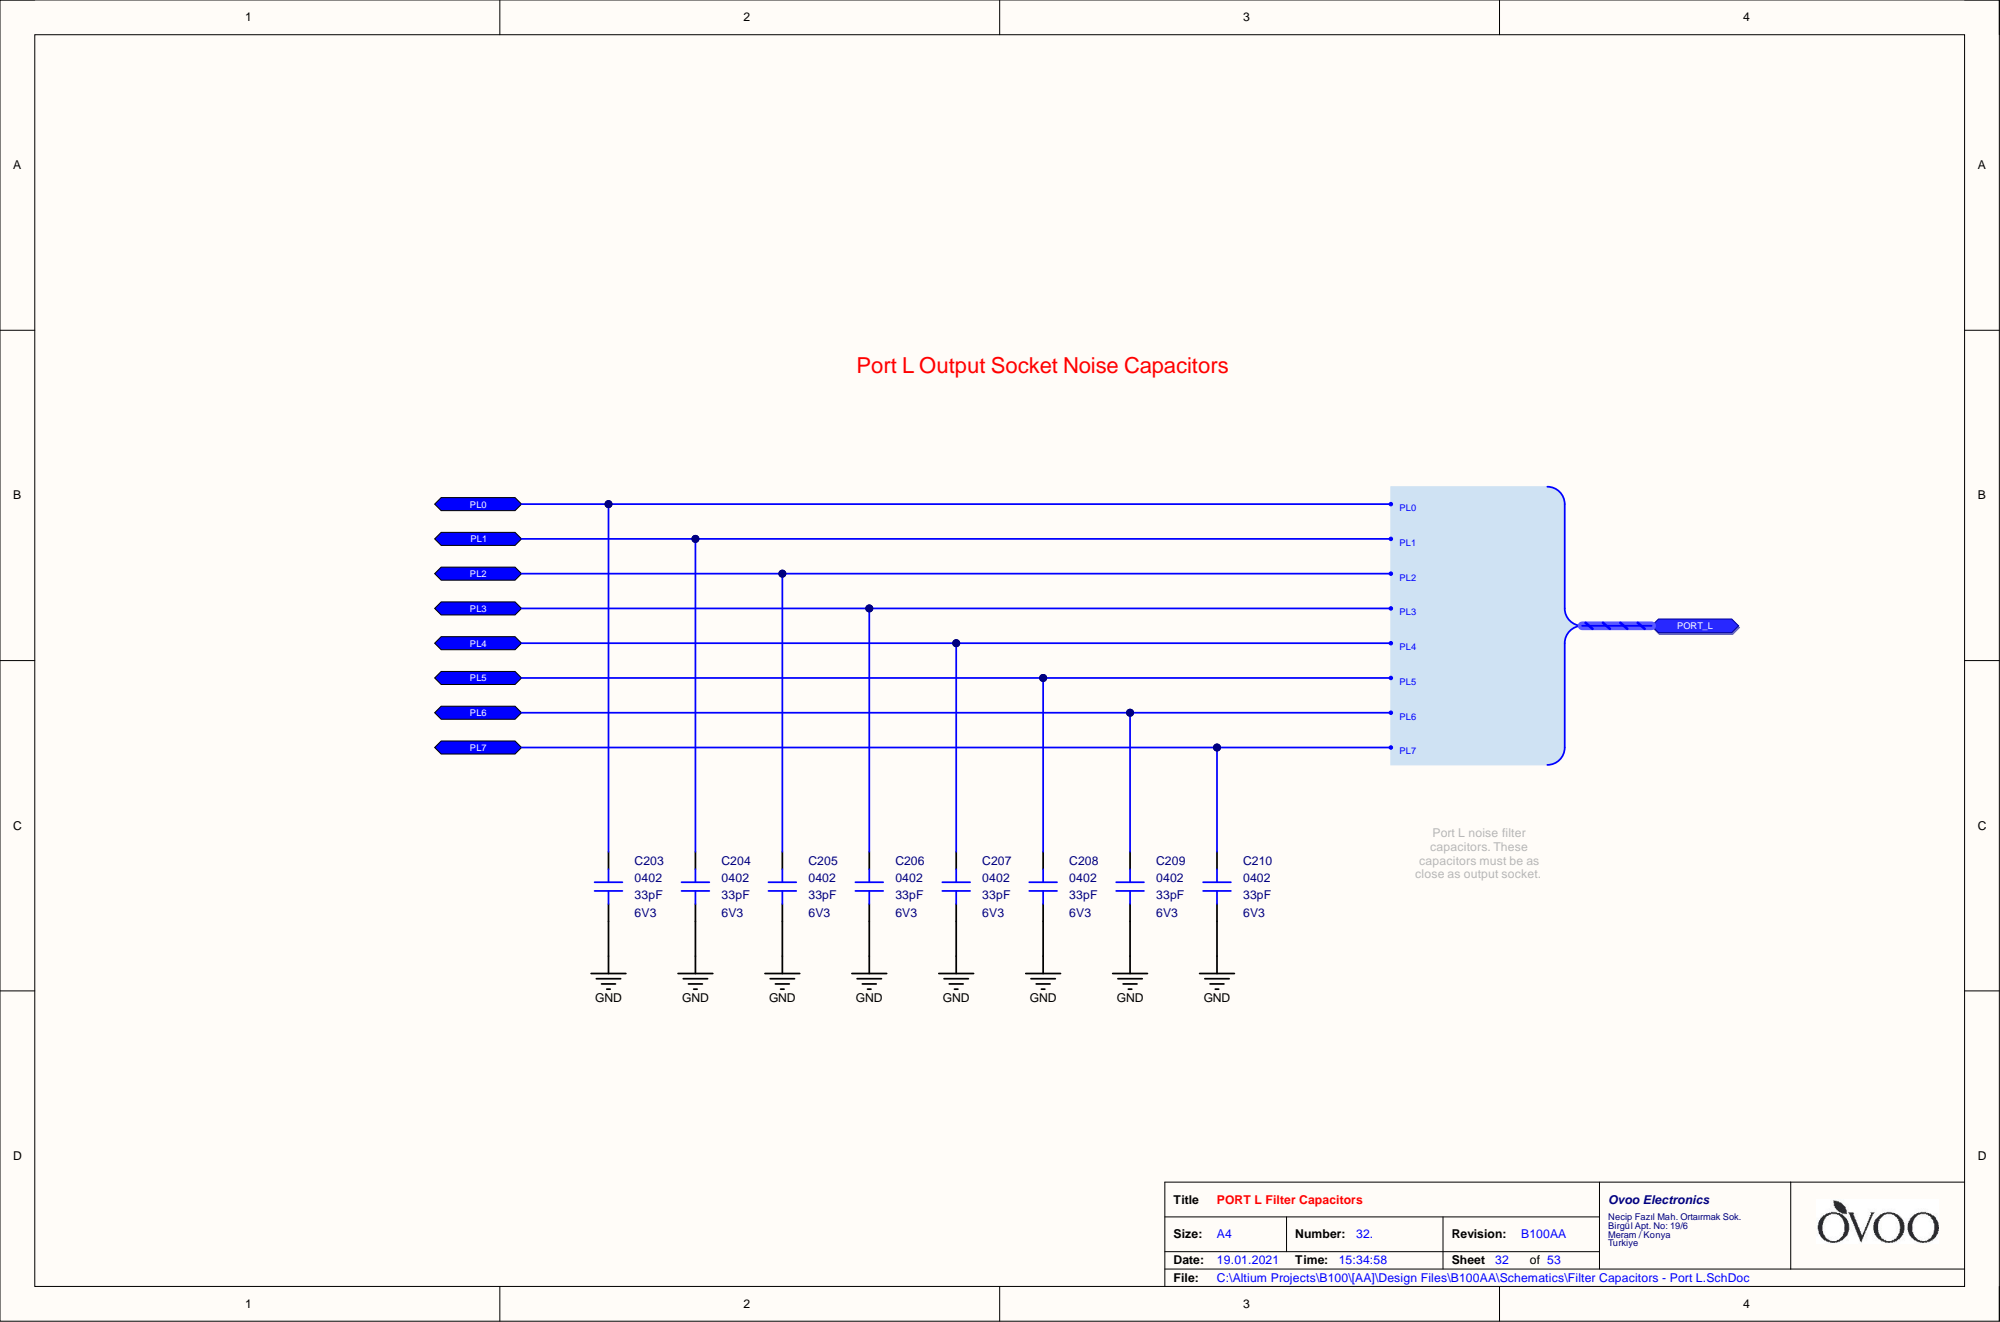
[picture p245: page 32]

Port L Output Socket Noise Capacitors

Port L noise filter
capacitors. These
capacitors must be as
close as output socket.

C:\Altium Projects\B100\[AA]\Design Files\B100AA\Schematics\Filter Capacitors - Port L.SchDoc

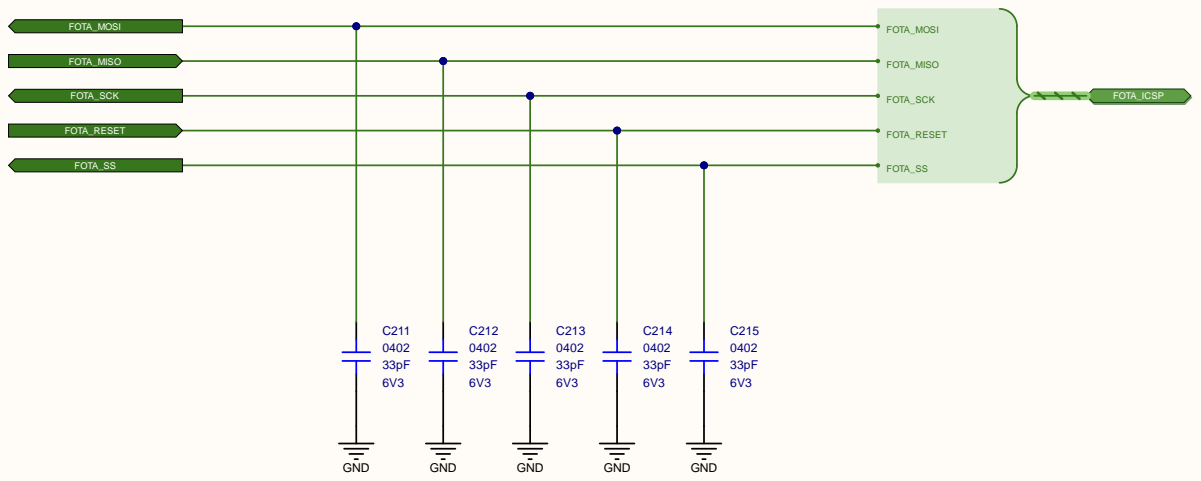
[picture p246: page 33]

FOTA ICSP Filter Capacitors

C:\Altium Projects\B100\[AA]\Design Files\B100AA\Schematics\Filter Capacitors - FOTA ICSP.SchDoc

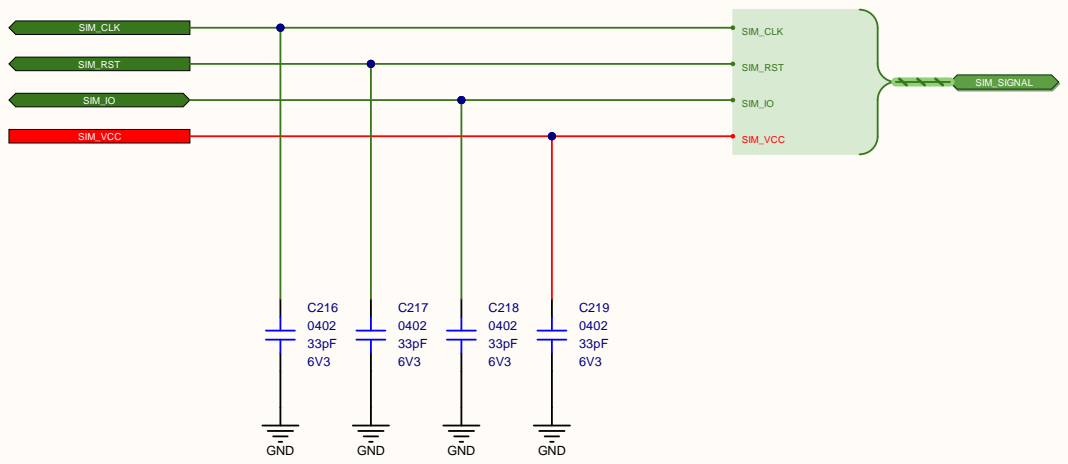
[picture p247: page 34]

FOTA ICSP Filter Capacitors

C:\Altium Projects\B100\[AA]\Design Files\B100AA\Schematics\Filter Capacitors - External SIM.SchDoc

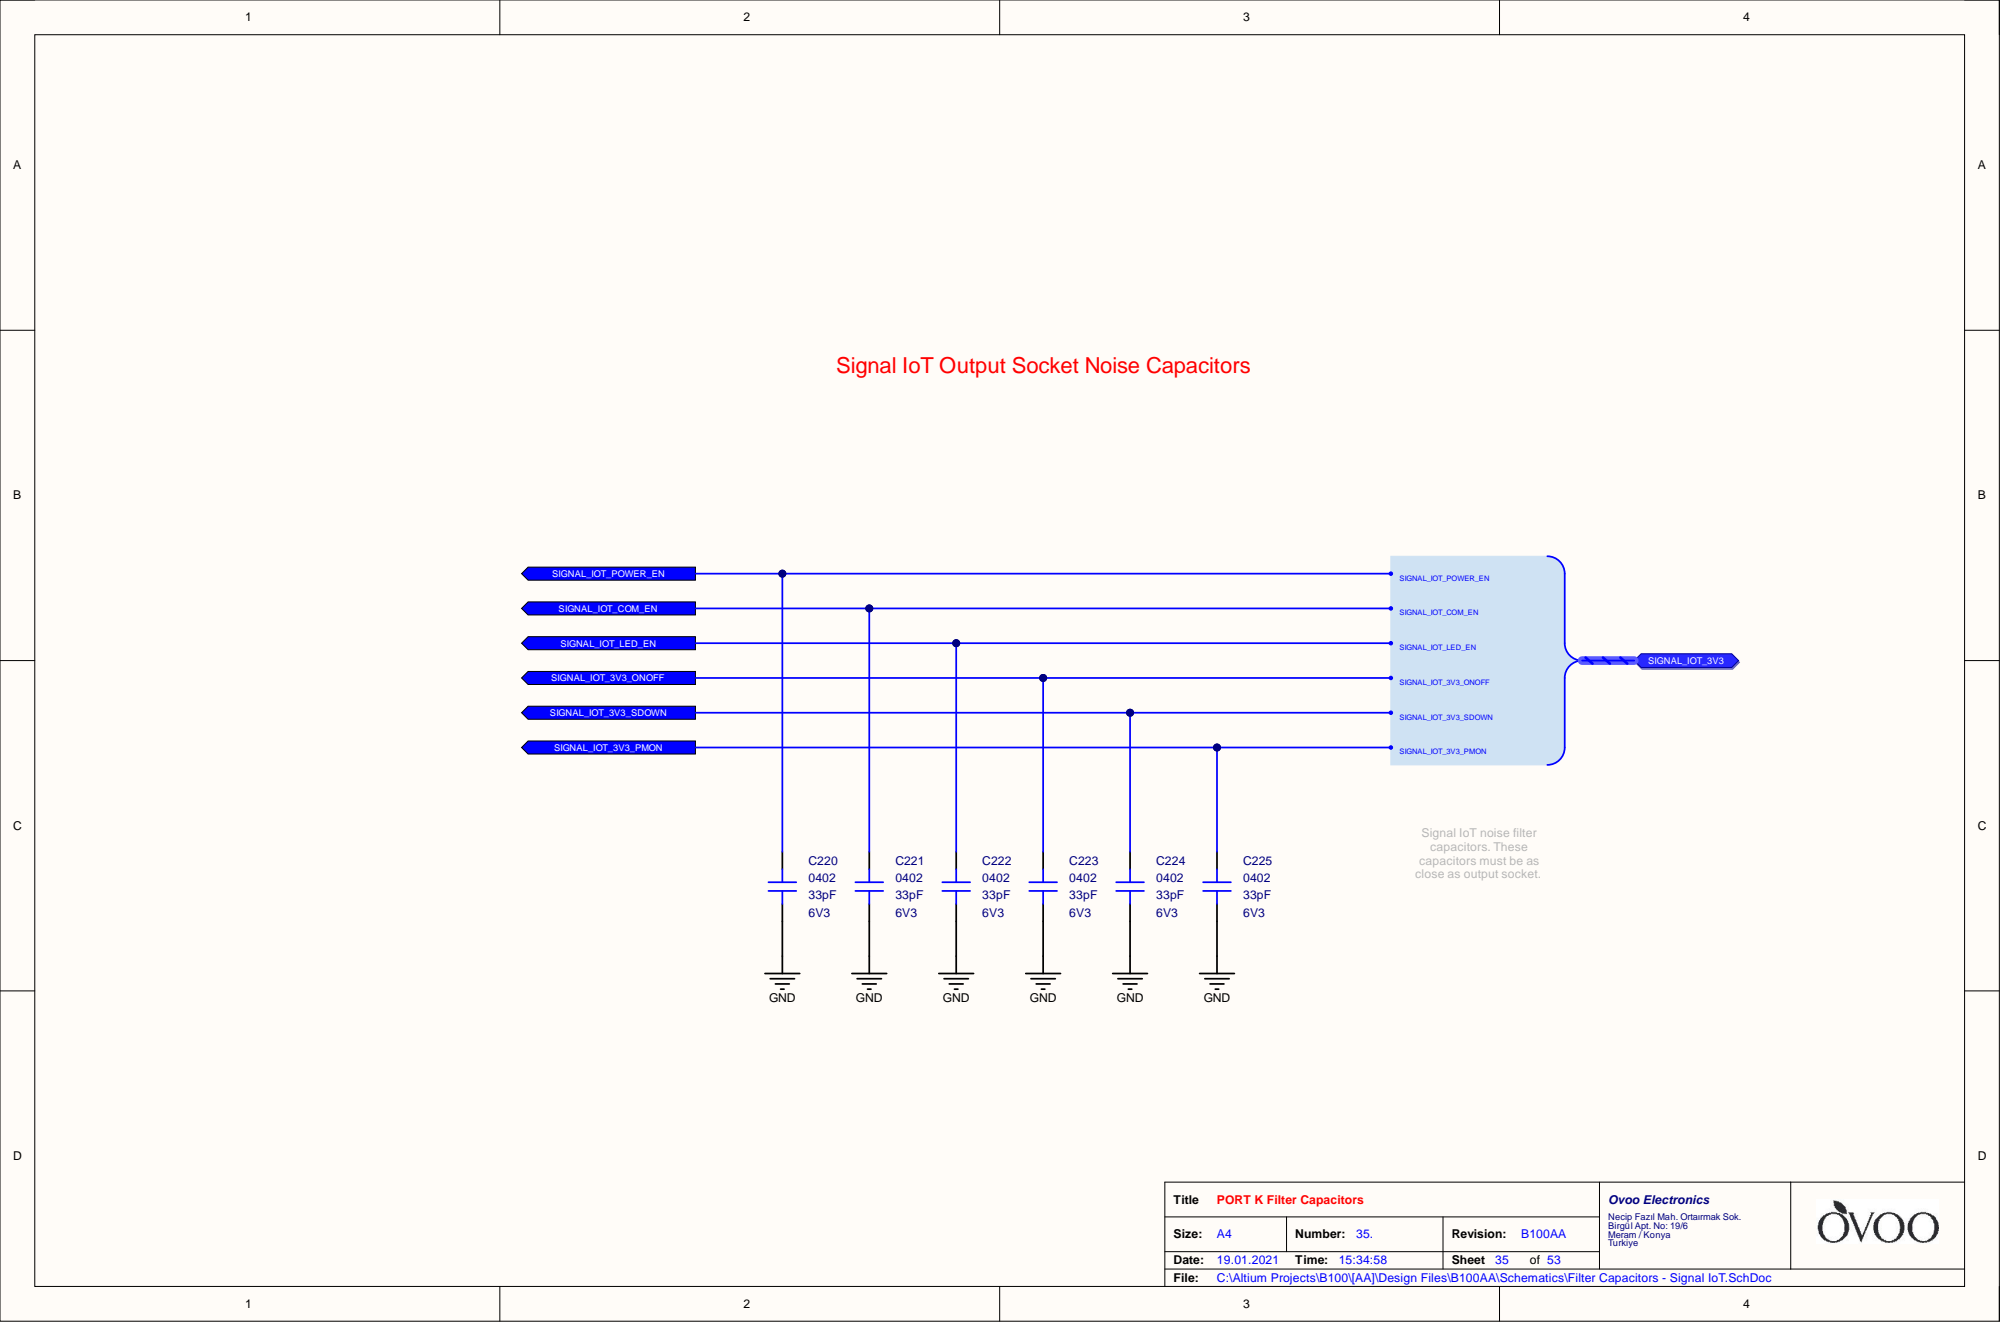
[picture p248: page 35]

Signal IoT Output Socket Noise Capacitors

Signal IoT noise filter
capacitors. These
capacitors must be as
close as output socket.

C:\Altium Projects\B100\[AA]\Design Files\B100AA\Schematics\Filter Capacitors - Signal IoT.SchDoc

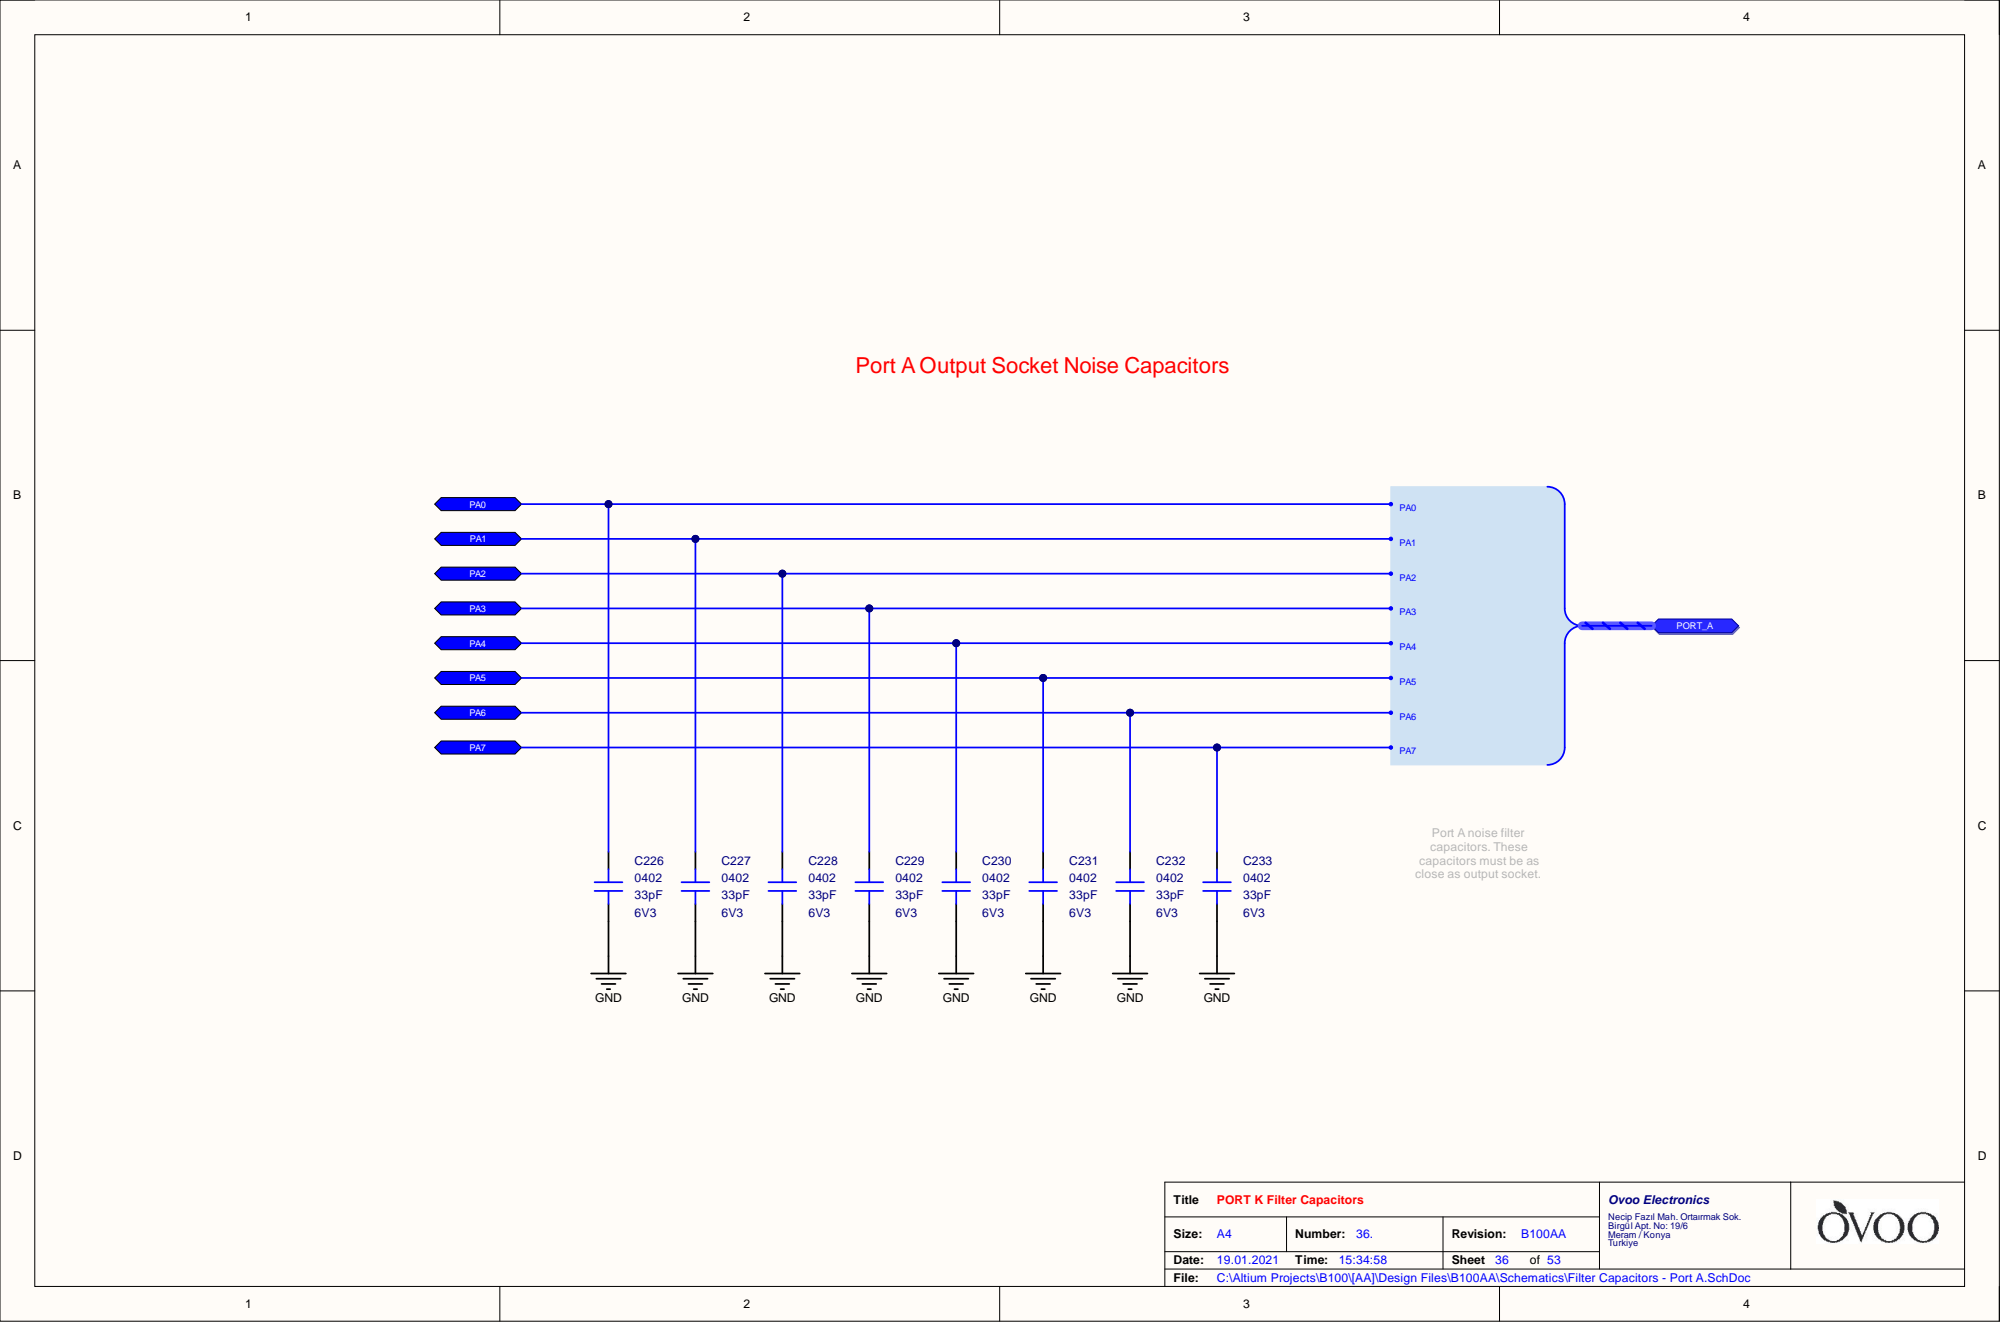
[picture p249: page 36]

Port A Output Socket Noise Capacitors

Port A noise filter
capacitors. These
capacitors must be as
close as output socket.

C:\Altium Projects\B100\[AA]\Design Files\B100AA\Schematics\Filter Capacitors - Port A.SchDoc

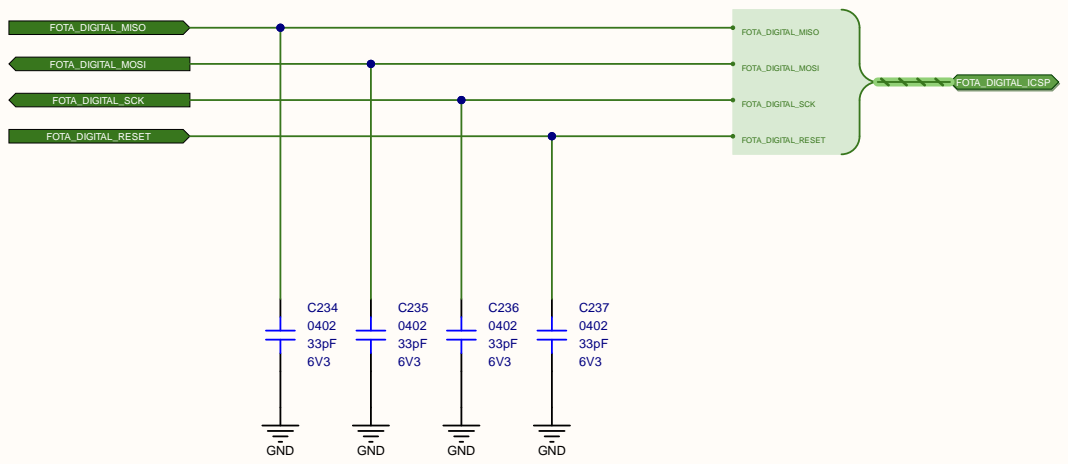
[picture p250: page 37]

FOTA Digital ICSP Filter Capacitors

C:\Altium Projects\B100\[AA]\Design Files\B100AA\Schematics\Filter Capacitors - FOTA Digital ICSP.SchDoc

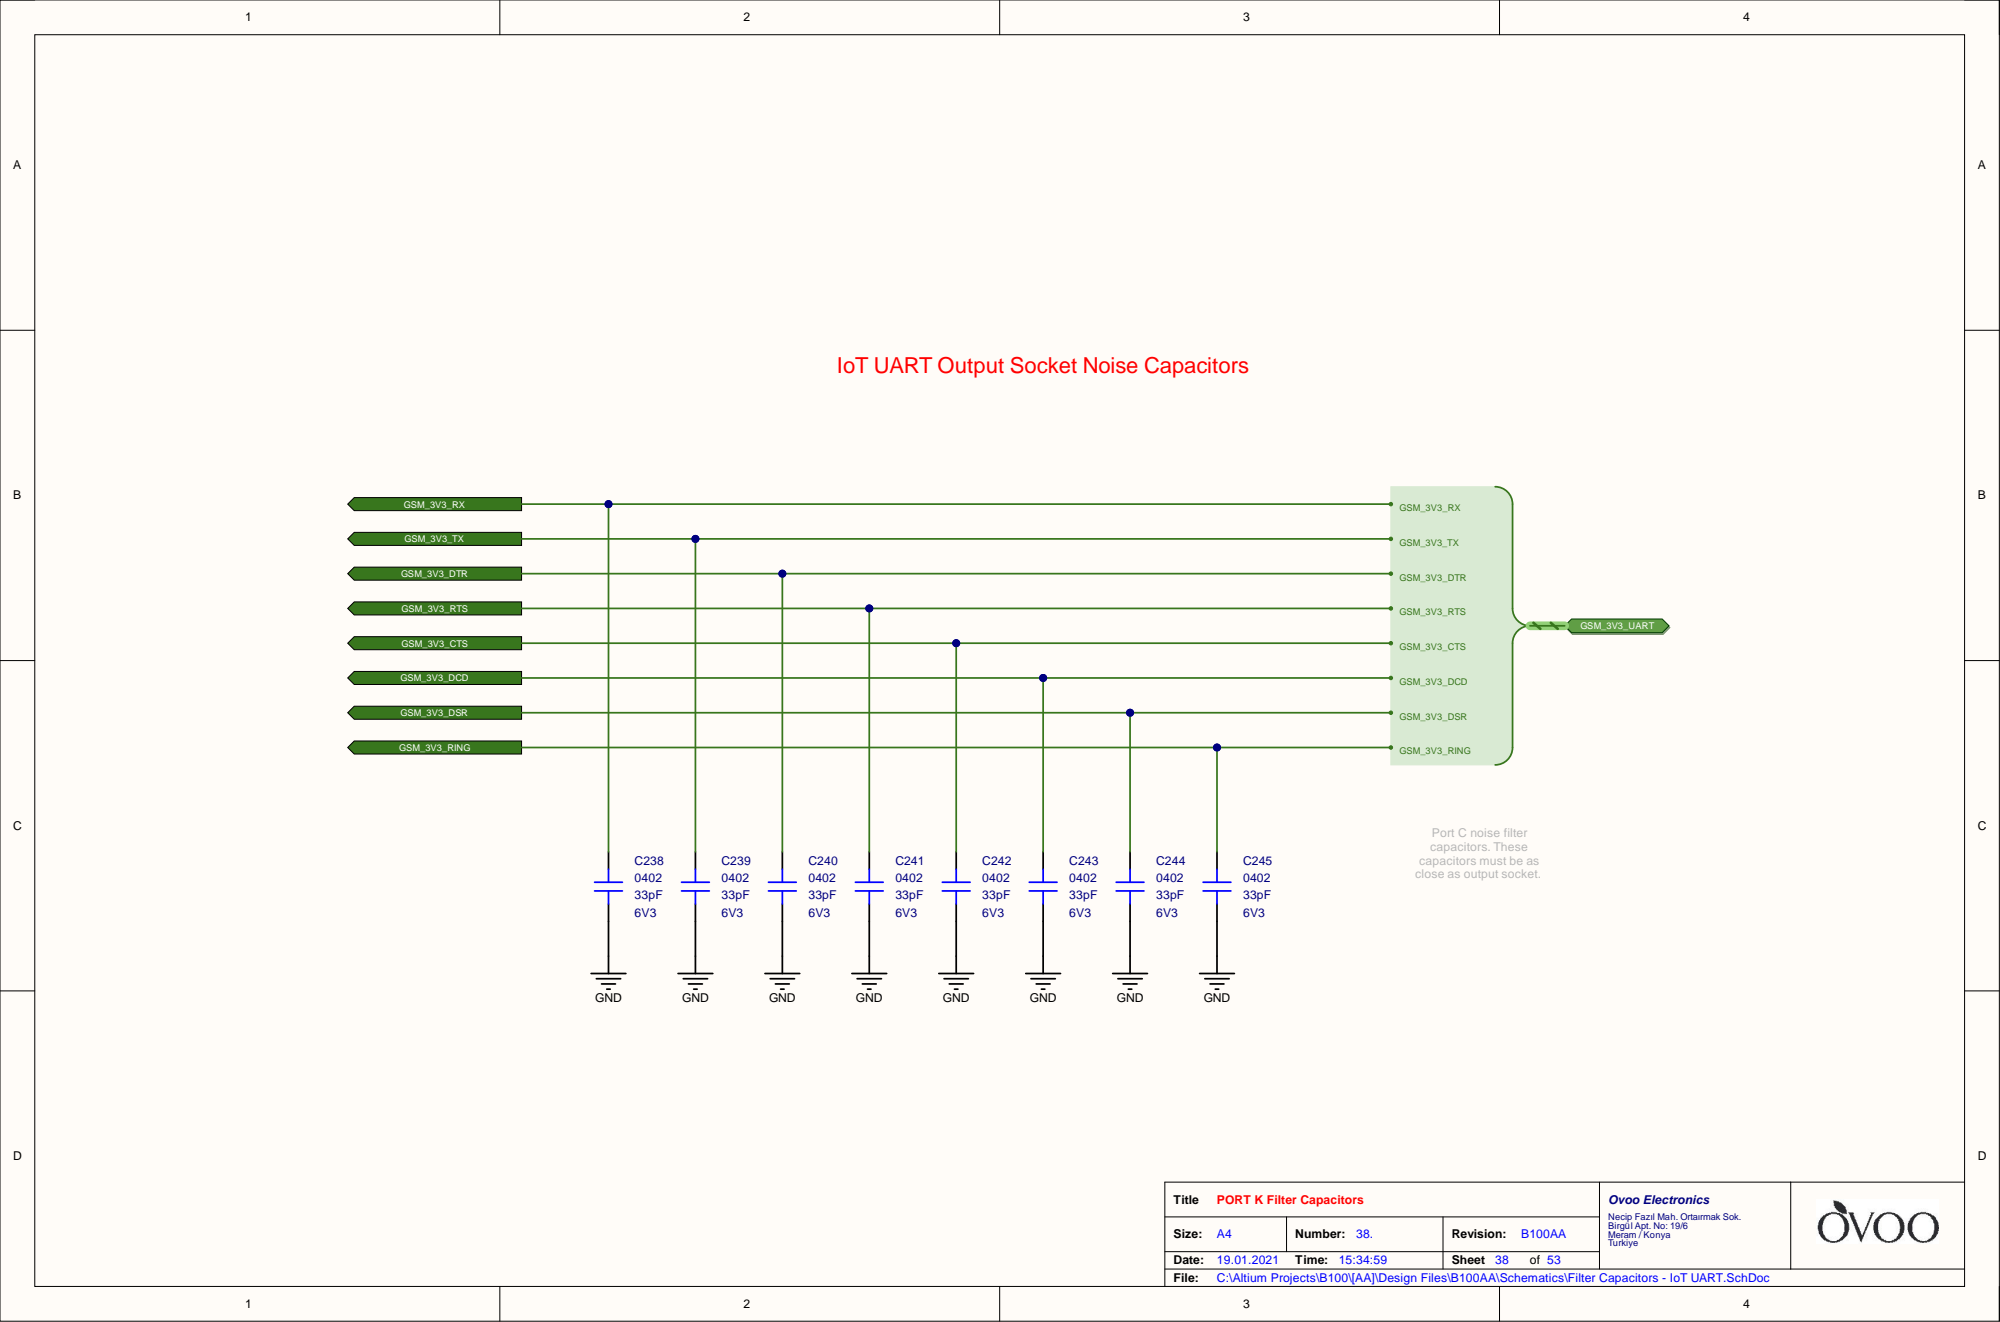
[picture p251: page 38]

IoT UART Output Socket Noise Capacitors

Port C noise filter
capacitors. These
capacitors must be as
close as output socket.

C:\Altium Projects\B100\[AA]\Design Files\B100AA\Schematics\Filter Capacitors - IoT UART.SchDoc

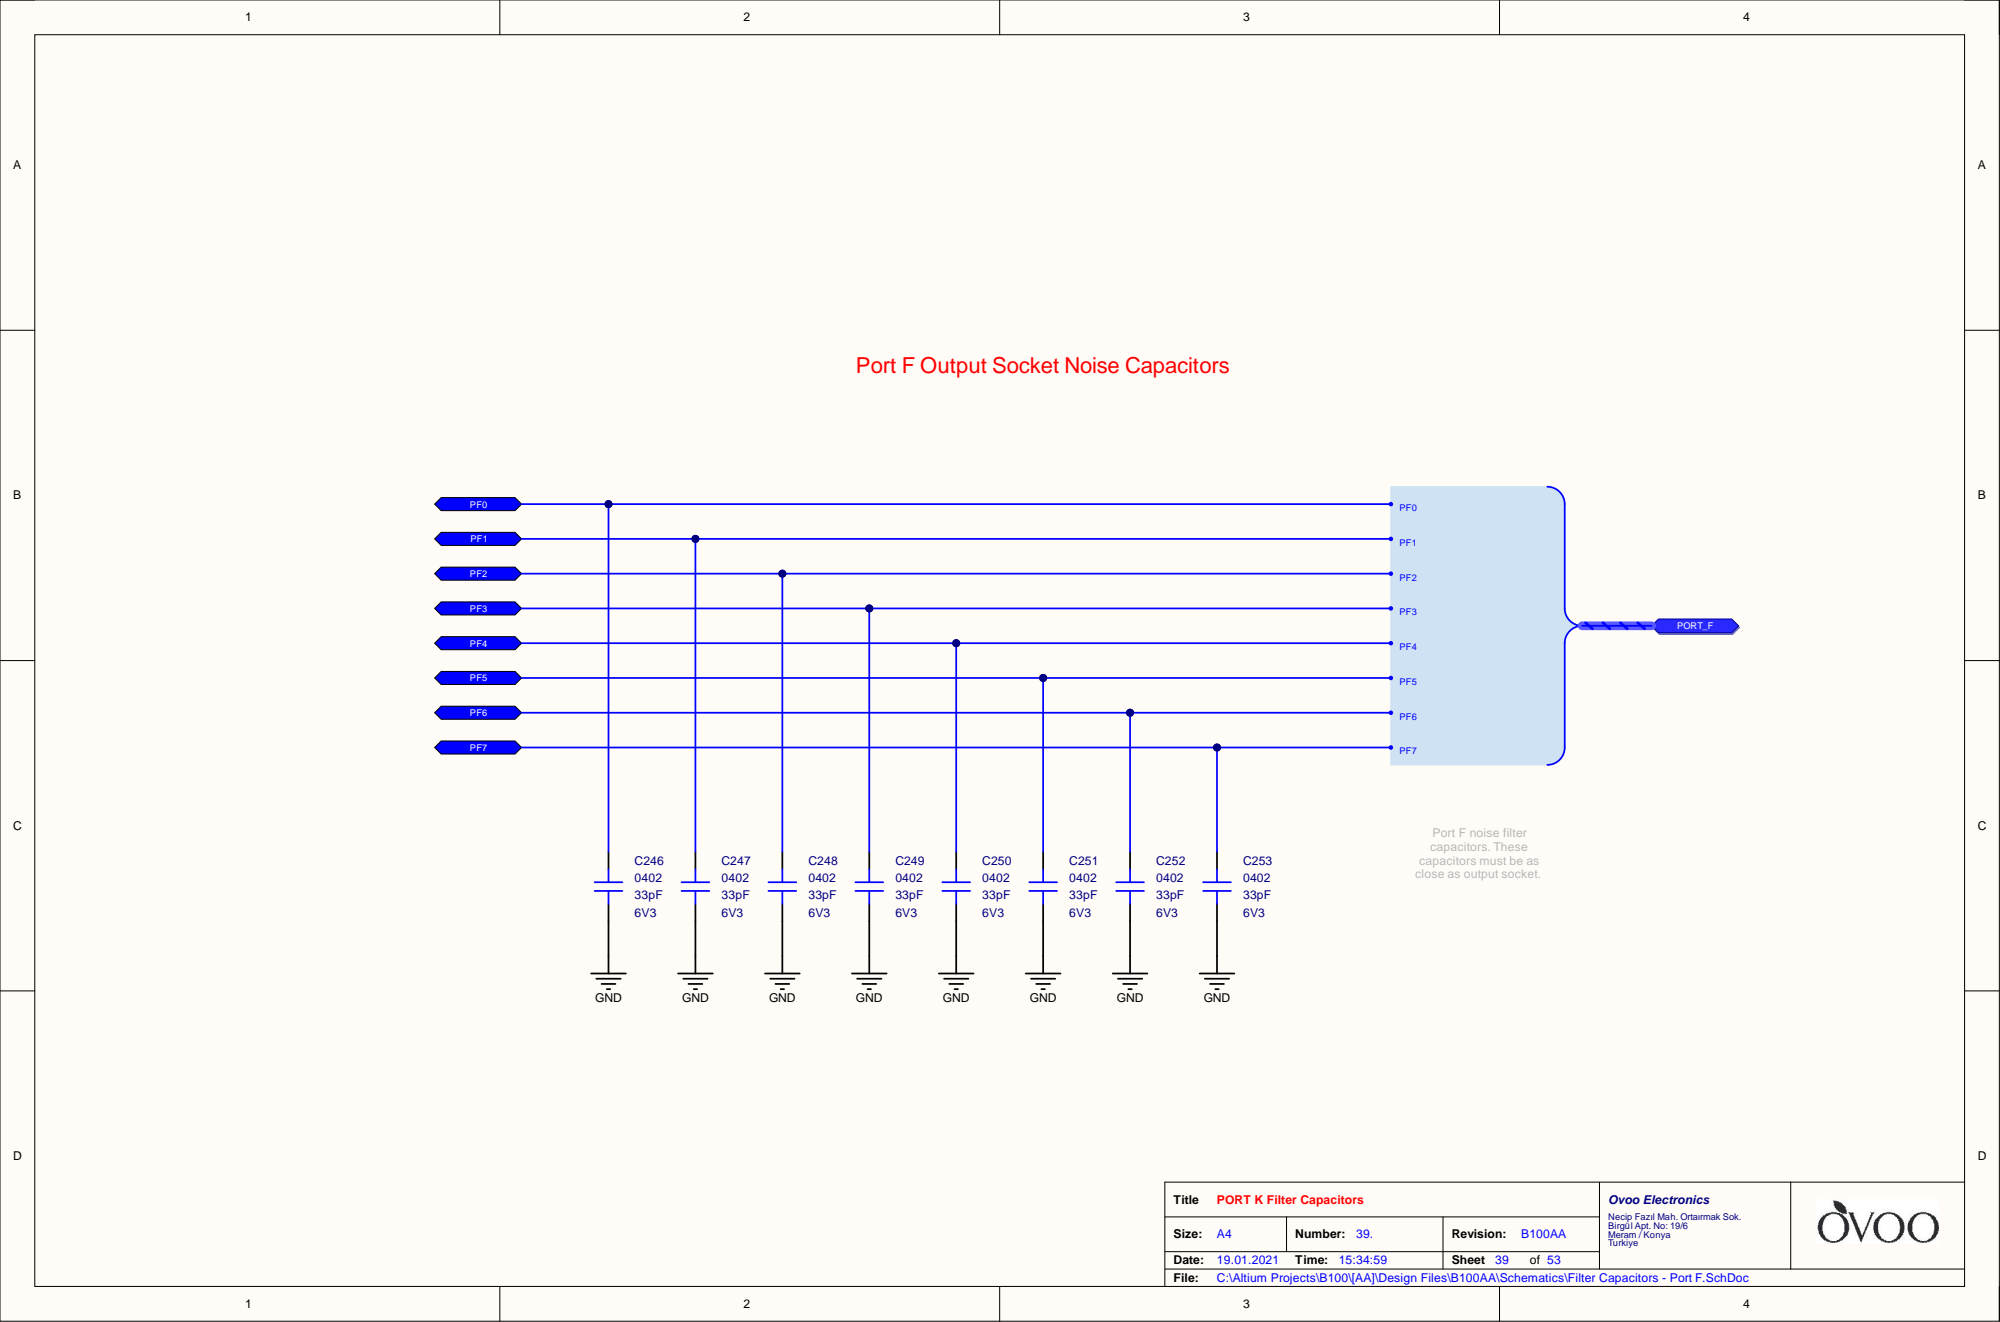
[picture p252: page 39]

Port F Output Socket Noise Capacitors

Port F noise filter
capacitors. These
capacitors must be as
close as output socket.

C:\Altium Projects\B100\[AA]\Design Files\B100AA\Schematics\Filter Capacitors - Port F.SchDoc

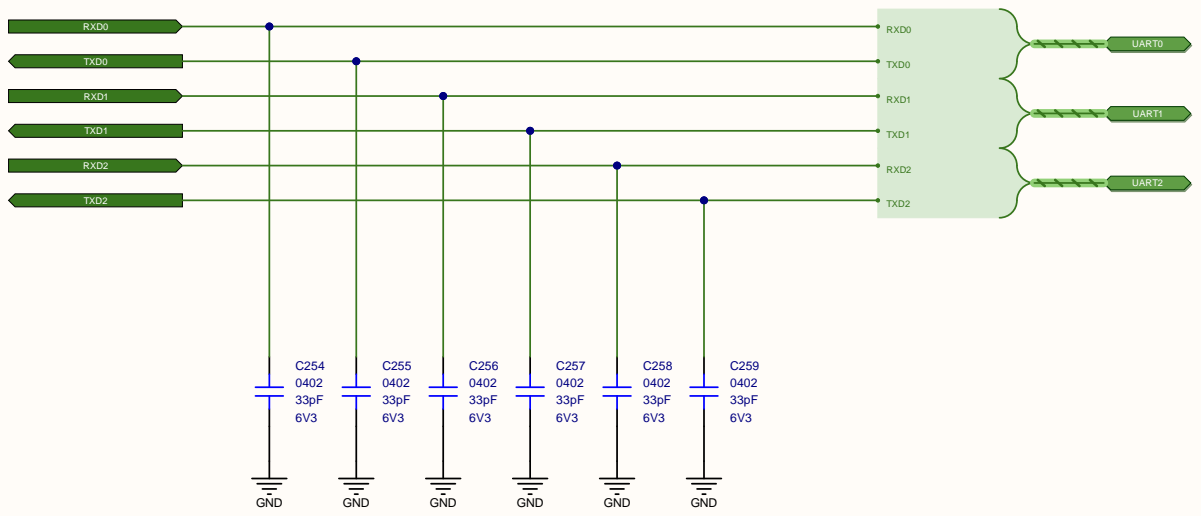
[picture p253: page 40]

Serial Communication Filter Capacitors

C:\Altium Projects\B100\[AA]\Design Files\B100AA\Schematics\Filter Capacitors - Serial Communication.SchDoc

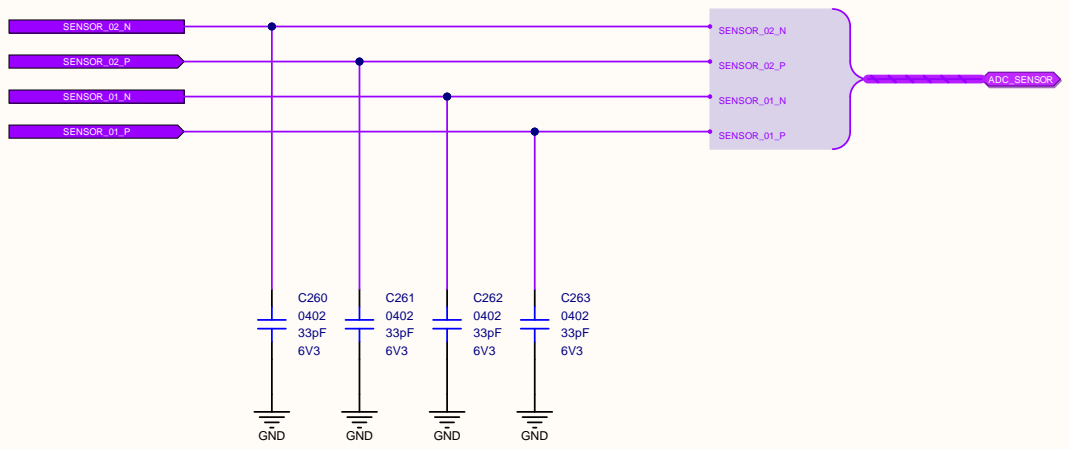
[picture p254: page 41]

ADC Sensor Filter Capacitors

C:\Altium Projects\B100\[AA]\Design Files\B100AA\Schematics\Filter Capacitors - ADC Sensor.SchDoc

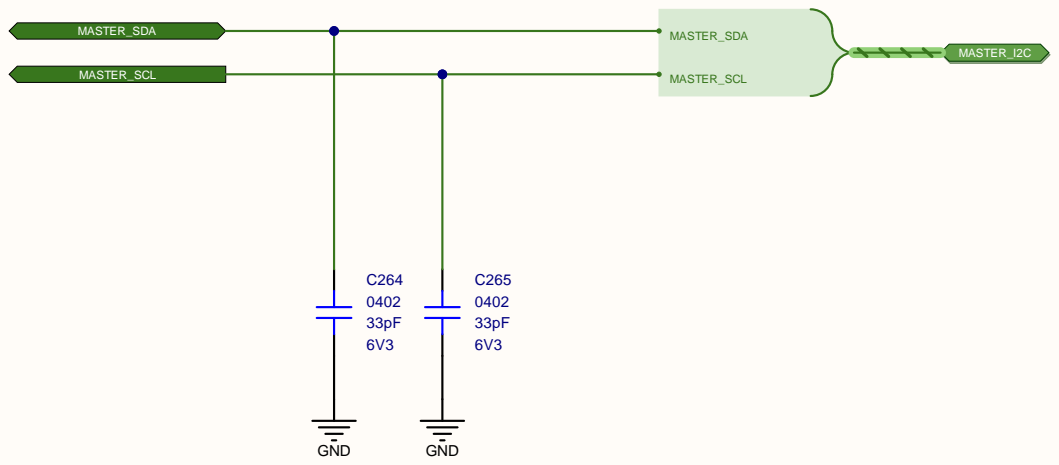
[picture p255: page 42]

C:\Altium Projects\B100\[AA]\Design Files\B100AA\Schematics\Filter Capacitors - I2C.SchDoc

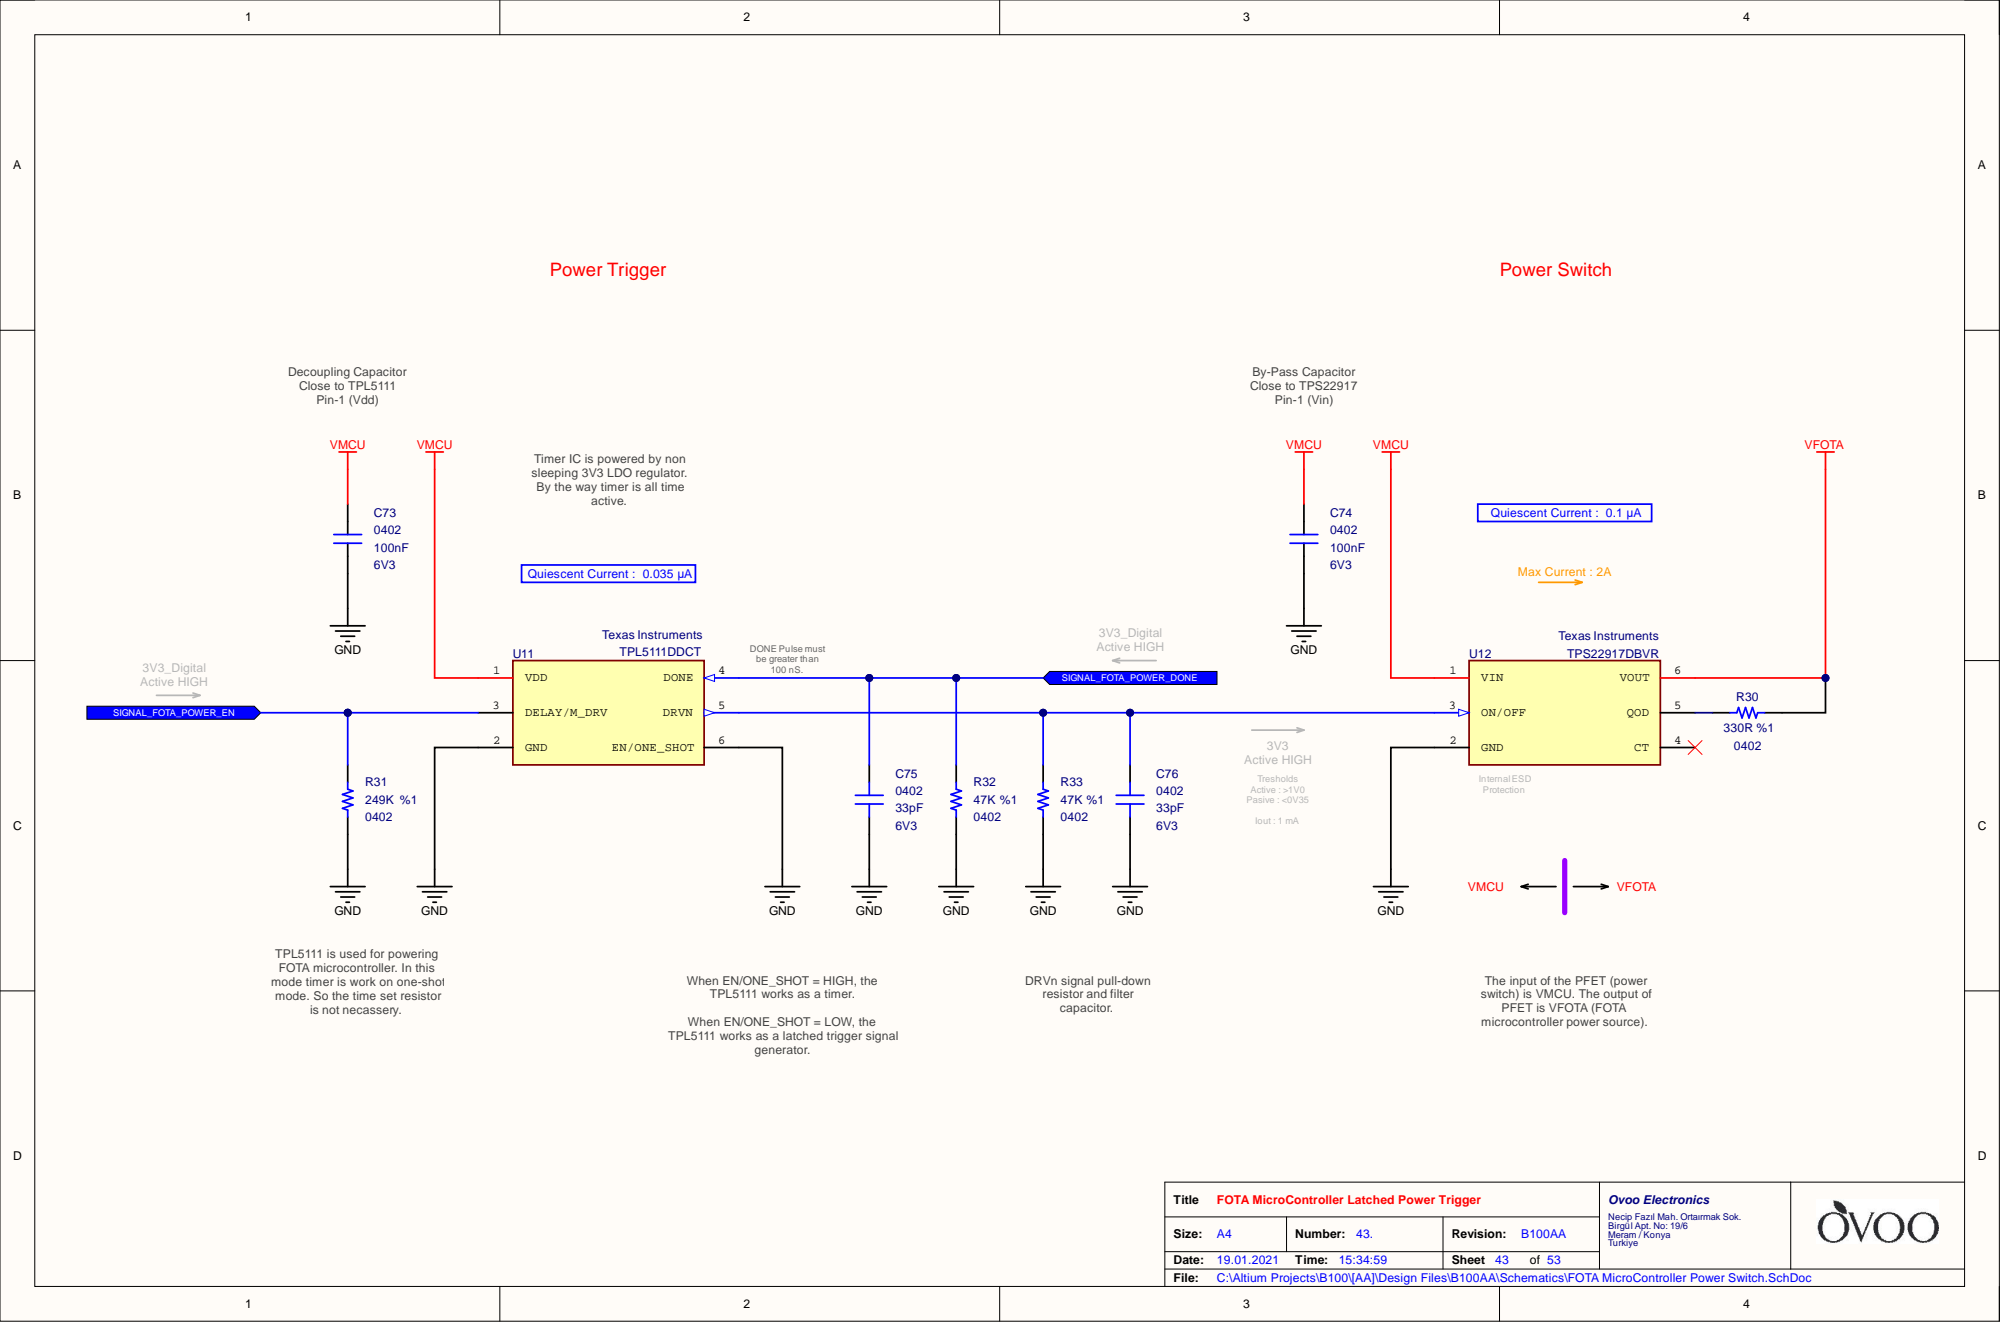
[picture p256: page 43]

Timer IC is powered by non
sleeping 3V3 LDO regulator.
By the way timer is all time

TPL5111 is used for powering
FOTA microcontroller. In this
mode timer is work on one-shot
mode. So the time set resistor

When EN/ONE_SHOT = HIGH, the
TPL5111 works as a timer.

DRVn signal pull-down
resistor and filter
capacitor.

The input of the PFET (power
switch) is VMCU. The output of
PFET is VFOTA (FOTA
microcontroller power source).

When EN/ONE_SHOT = LOW, the
TPL5111 works as a latched trigger signal

FOTA MicroController Latched Power Trigger

C:\Altium Projects\B100\[AA]\Design Files\B100AA\Schematics\FOTA MicroController Power Switch.SchDoc

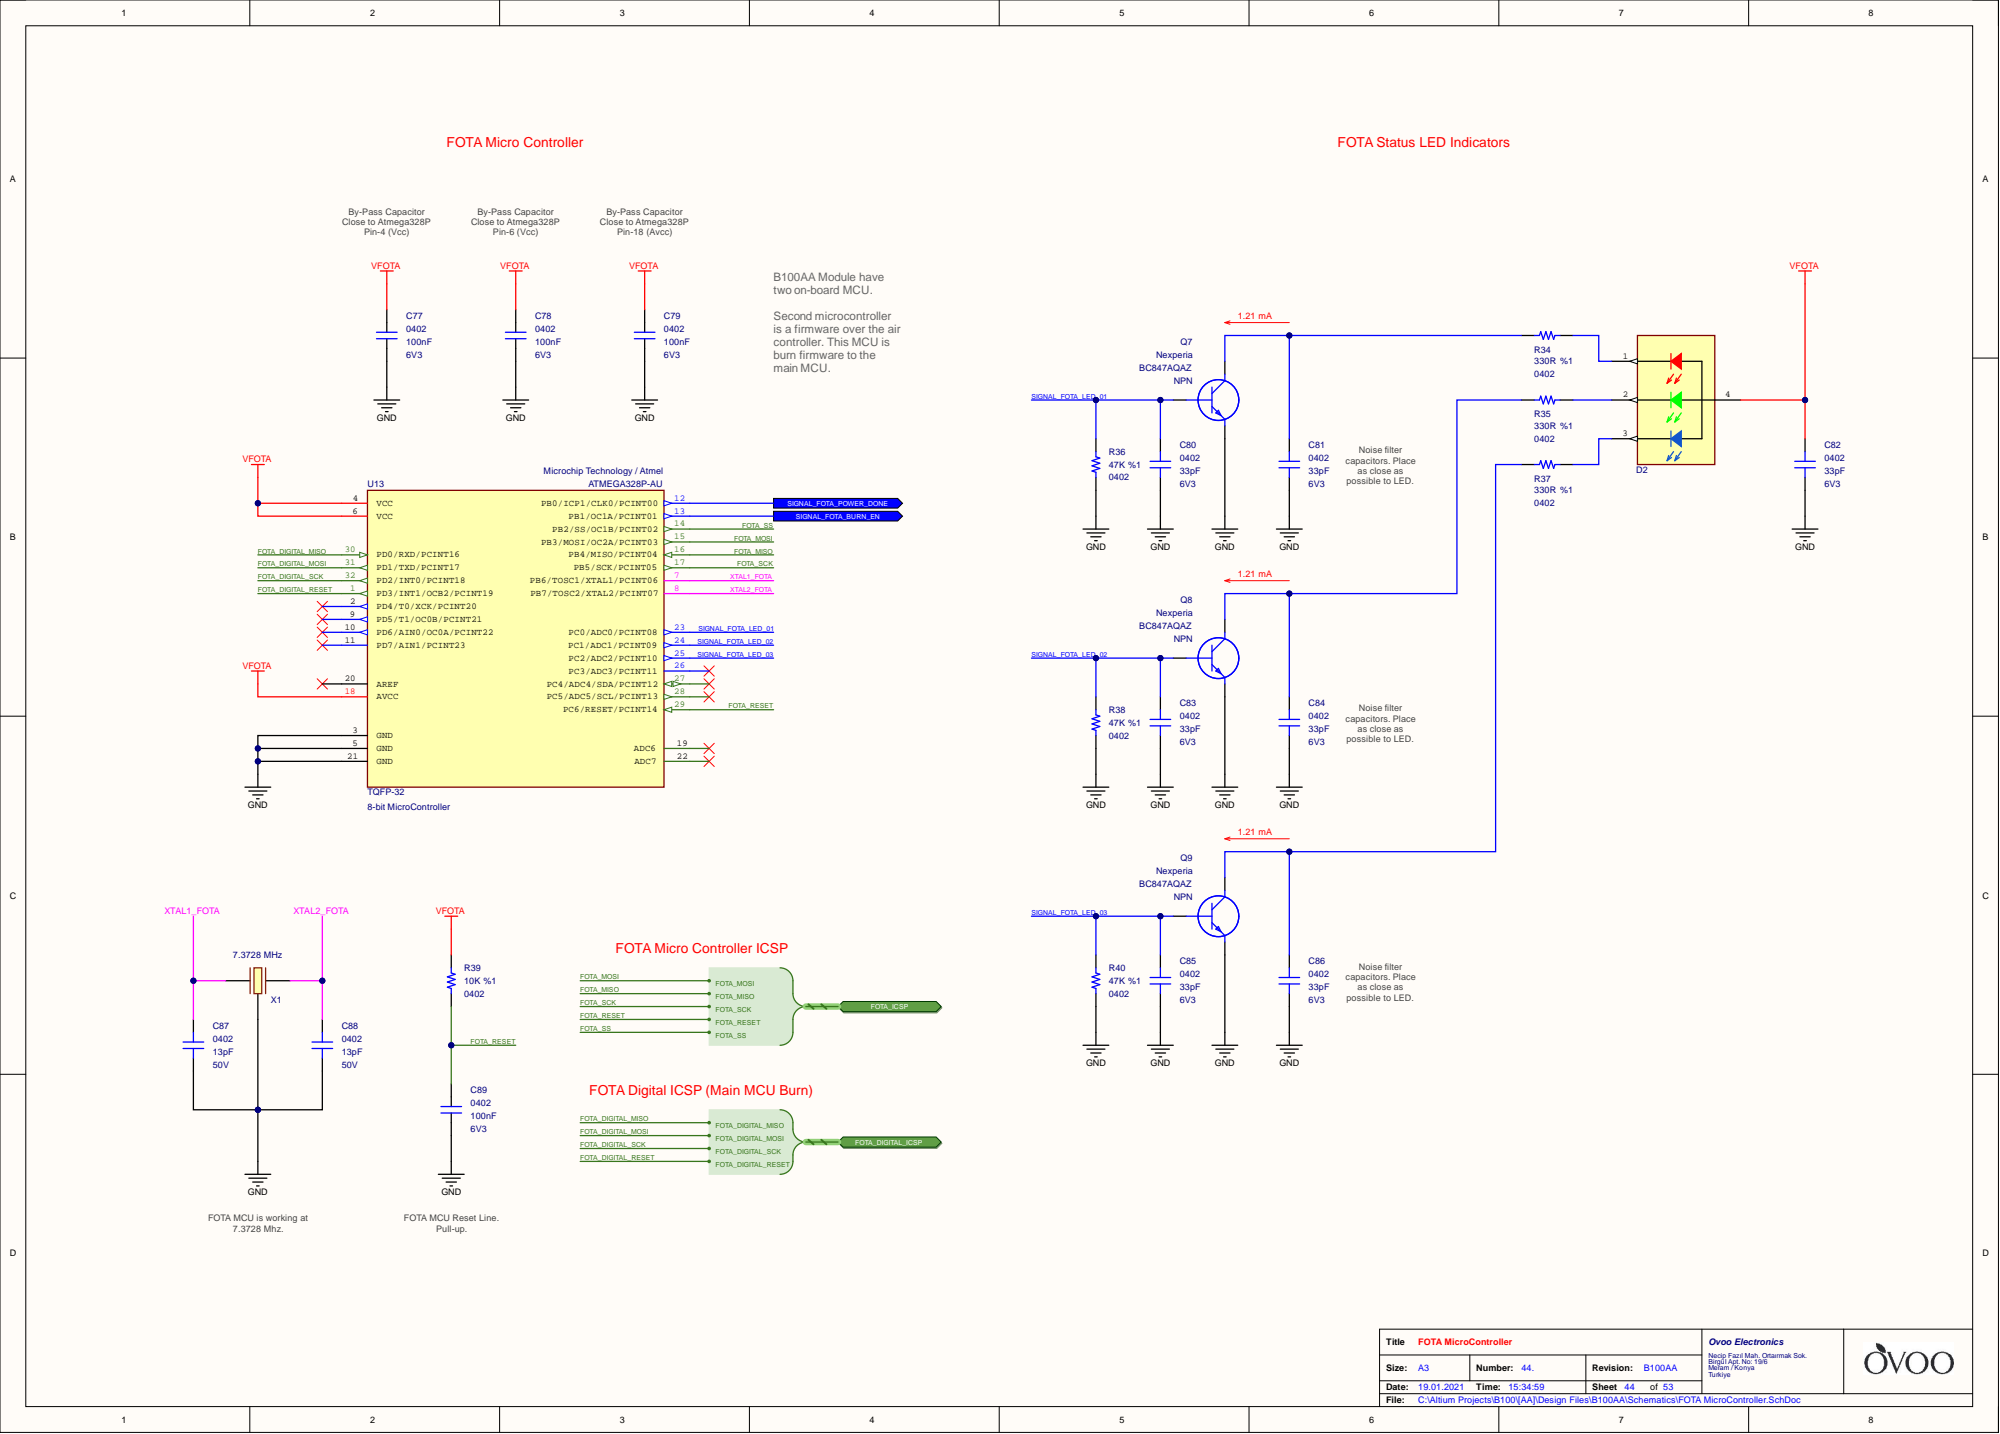
[picture p257: page 44]

B100AA Module have
two on-board MCU.

Second microcontroller
is a firmware over the air
controller. This MCU is
burn firmware to the
main MCU.

FOTA Micro Controller ICSP

FOTA Digital ICSP (Main MCU Burn)

FOTA MCU is working at

FOTA MCU Reset Line.

C:\Altium Projects\B100\[AA]\Design Files\B100AA\Schematics\FOTA MicroController.SchDoc

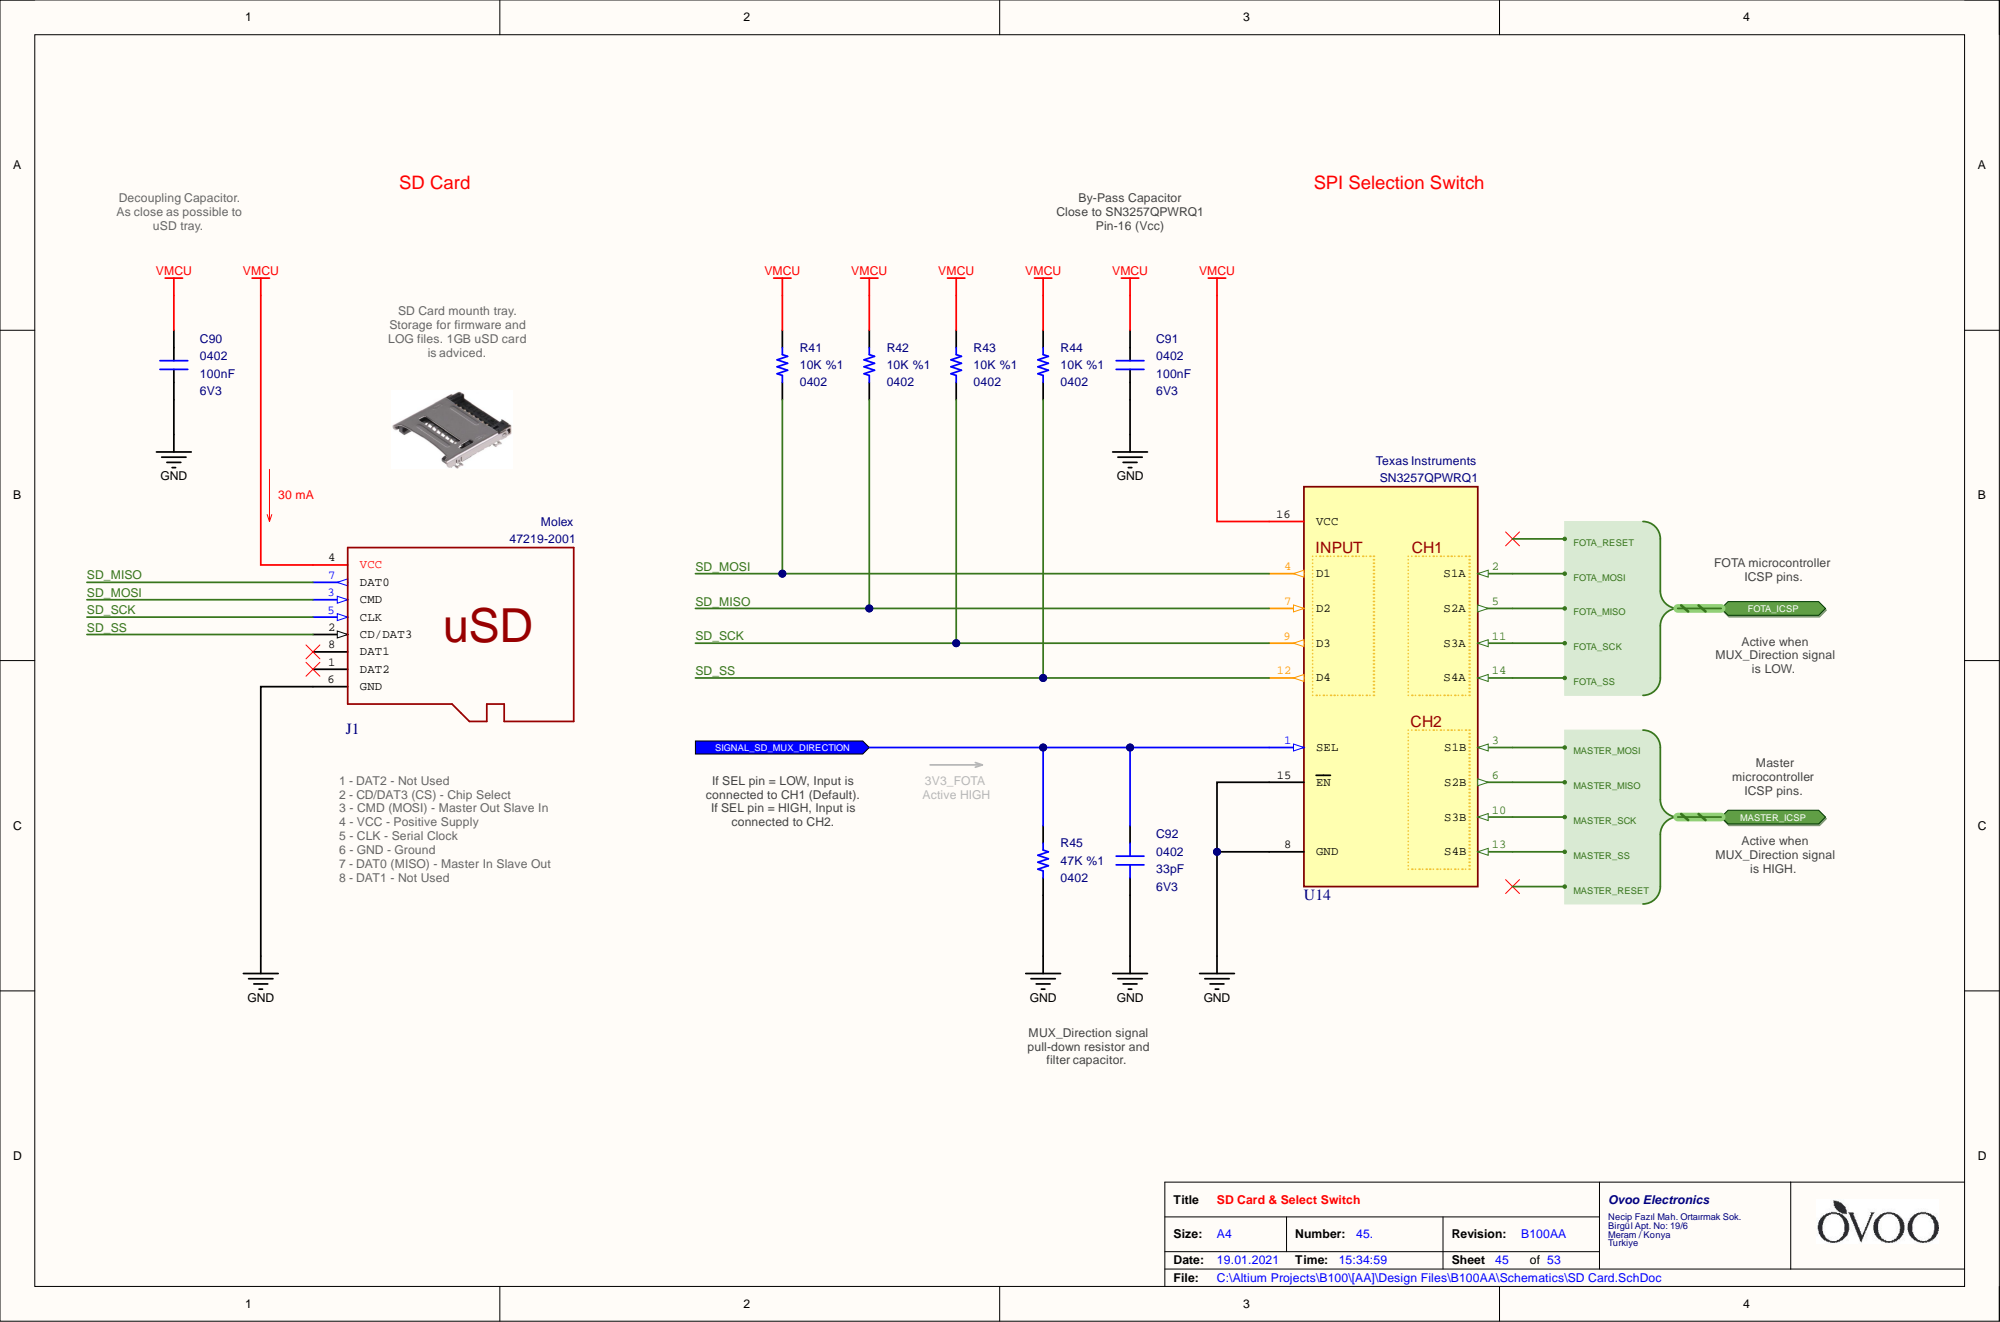
[picture p258: page 45]

Decoupling Capacitor.
As close as possible to

SD Card mounth tray.
Storage for firmware and
LOG files. 1GB uSD card

1 - DAT2 - Not Used
2 - CD/DAT3 (CS) - Chip Select
3 - CMD (MOSI) - Master Out Slave In
4 - VCC - Positive Supply
5 - CLK - Serial Clock
6 - GND - Ground
7 - DAT0 (MISO) - Master In Slave Out
8 - DAT1 - Not Used

If SEL pin = LOW, Input is
connected to CH1 (Default).
If SEL pin = HIGH, Input is
connected to CH2.

GND 8

MUX_Direction signal
pull-down resistor and
filter capacitor.

SD Card & Select Switch

C:\Altium Projects\B100\[AA]\Design Files\B100AA\Schematics\SD Card.SchDoc

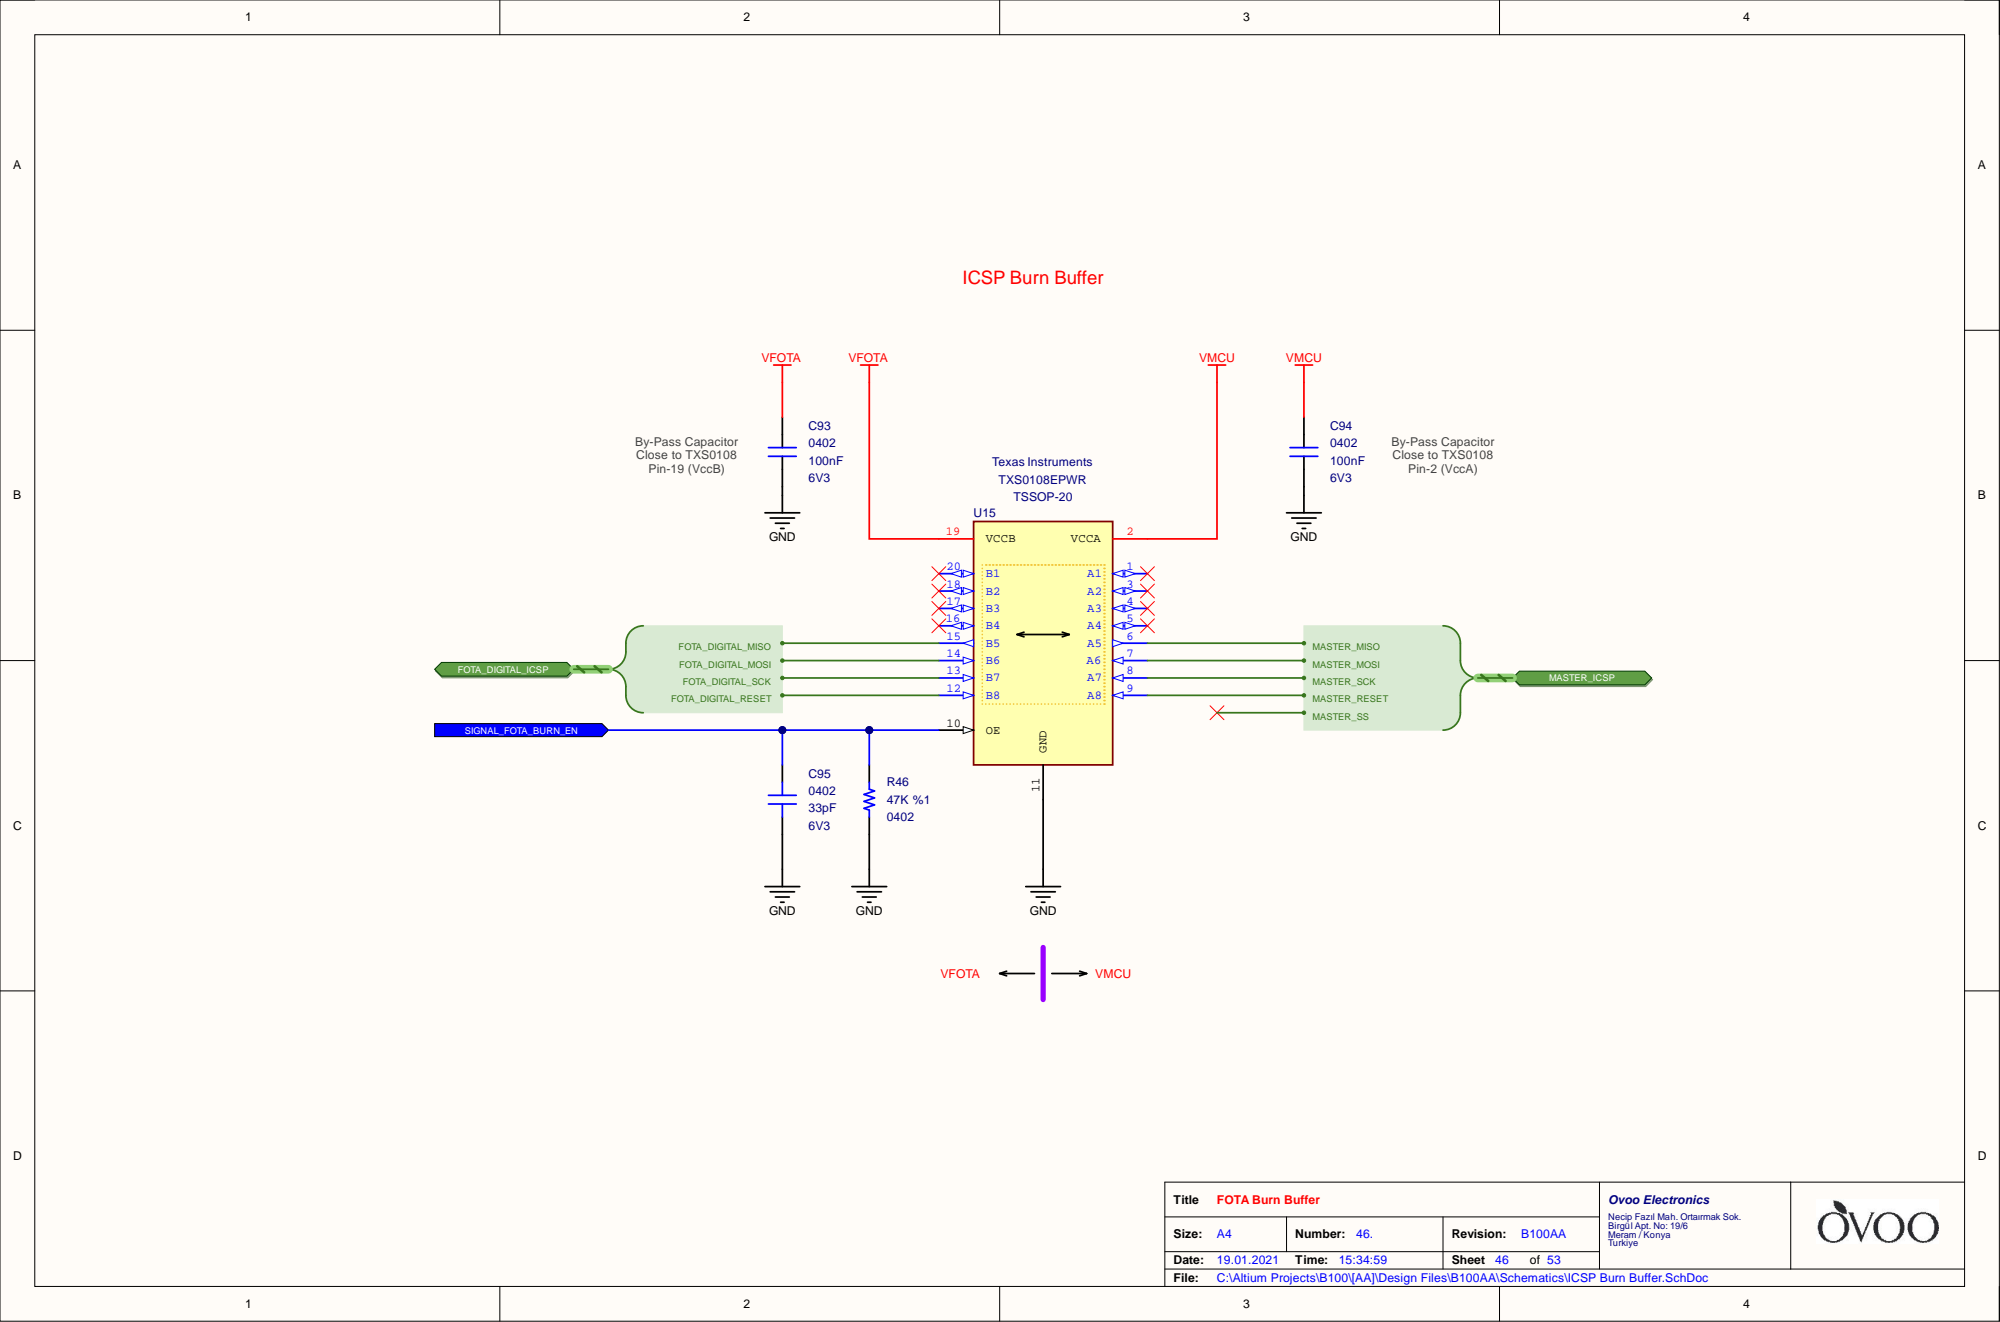
[picture p259: page 46]

C:\Altium Projects\B100\[AA]\Design Files\B100AA\Schematics\ICSP Burn Buffer.SchDoc

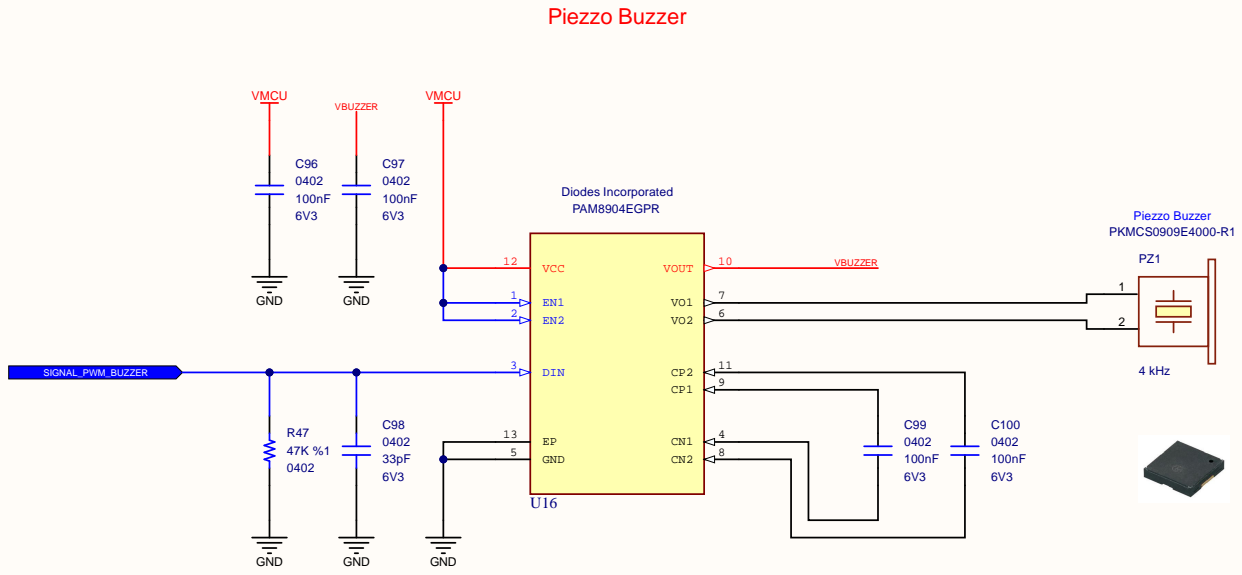
[picture p260: page 47]

EN1 1
EN2 2

C:\Altium Projects\B100\[AA]\Design Files\B100AA\Schematics\Buzzer.SchDoc


C:\Altium Projects\B100\[AA]\Design Files\B100AA\Schematics\I2C Network.SchDoc

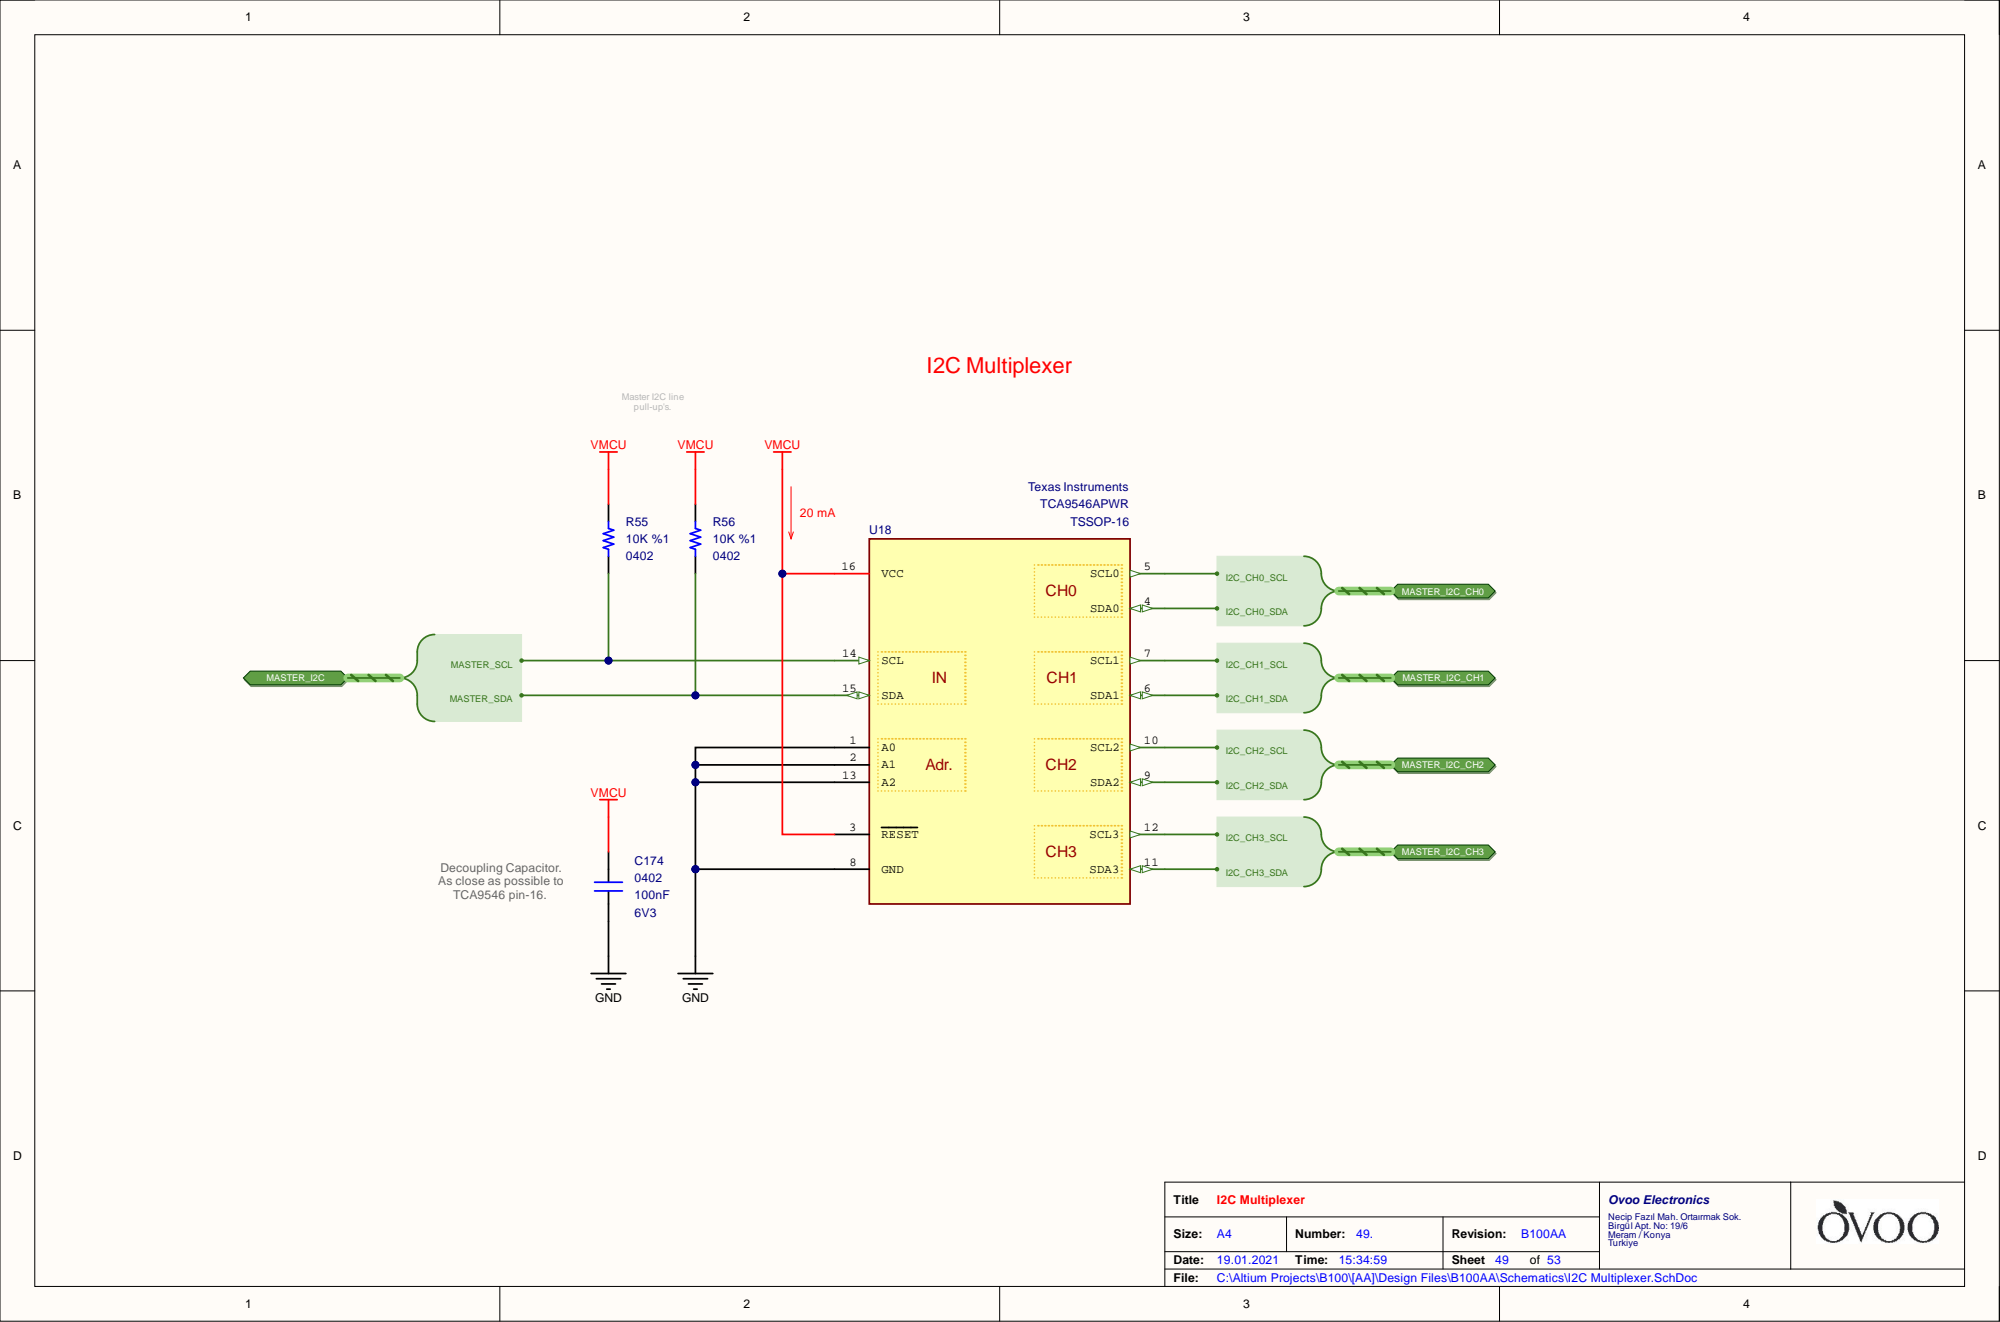
[picture p261: page 49]

SCL 14 SDA 15 A0 1

A1 2
A2 13

RESET 3

Decoupling Capacitor.
As close as possible to
TCA9546 pin-16.

C:\Altium Projects\B100\[AA]\Design Files\B100AA\Schematics\I2C Multiplexer.SchDoc

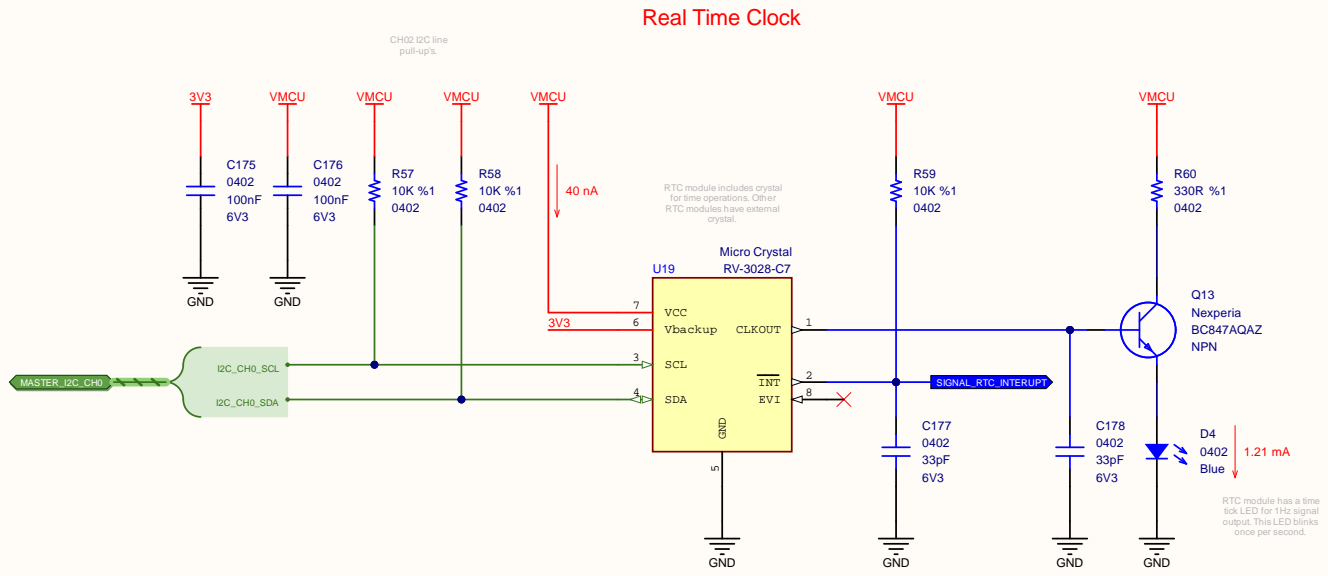
[picture p262: page 50]

RTC module includes crystal
for time operations. Other
RTC modules have external

RTC module has a time
tick LED for 1Hz signal
output. This LED blinks
once per second.

C:\Altium Projects\B100\[AA]\Design Files\B100AA\Schematics\Real Time Clock.SchDoc

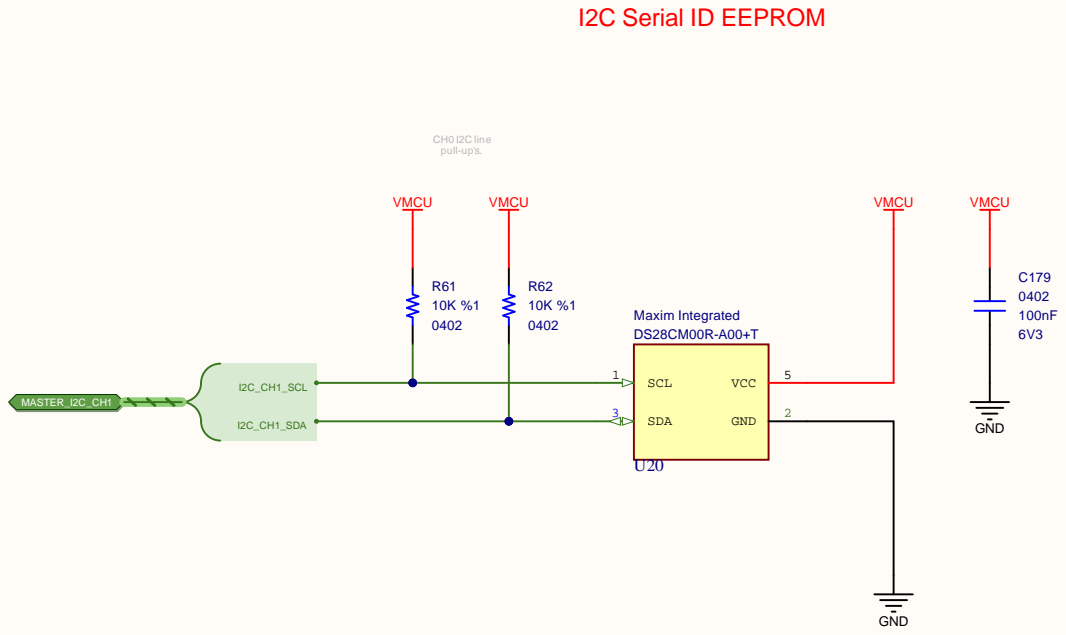
[picture p263: page 51]

C:\Altium Projects\B100\[AA]\Design Files\B100AA\Schematics\Serial ID EEPROM.SchDoc

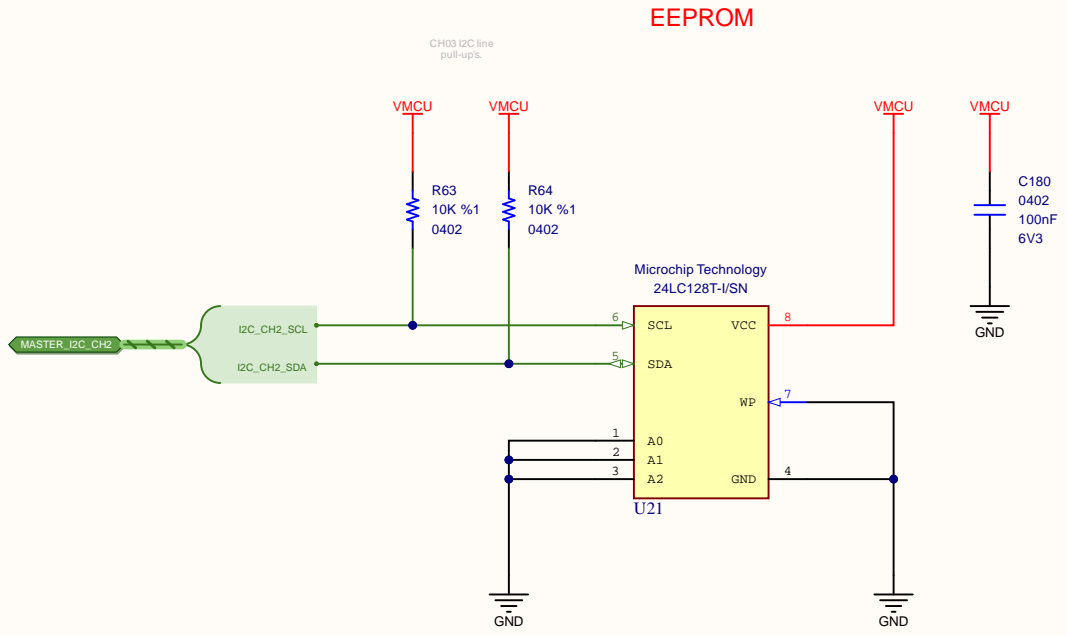
[picture p264: page 52]

C:\Altium Projects\B100\[AA]\Design Files\B100AA\Schematics\EEPROM.SchDoc

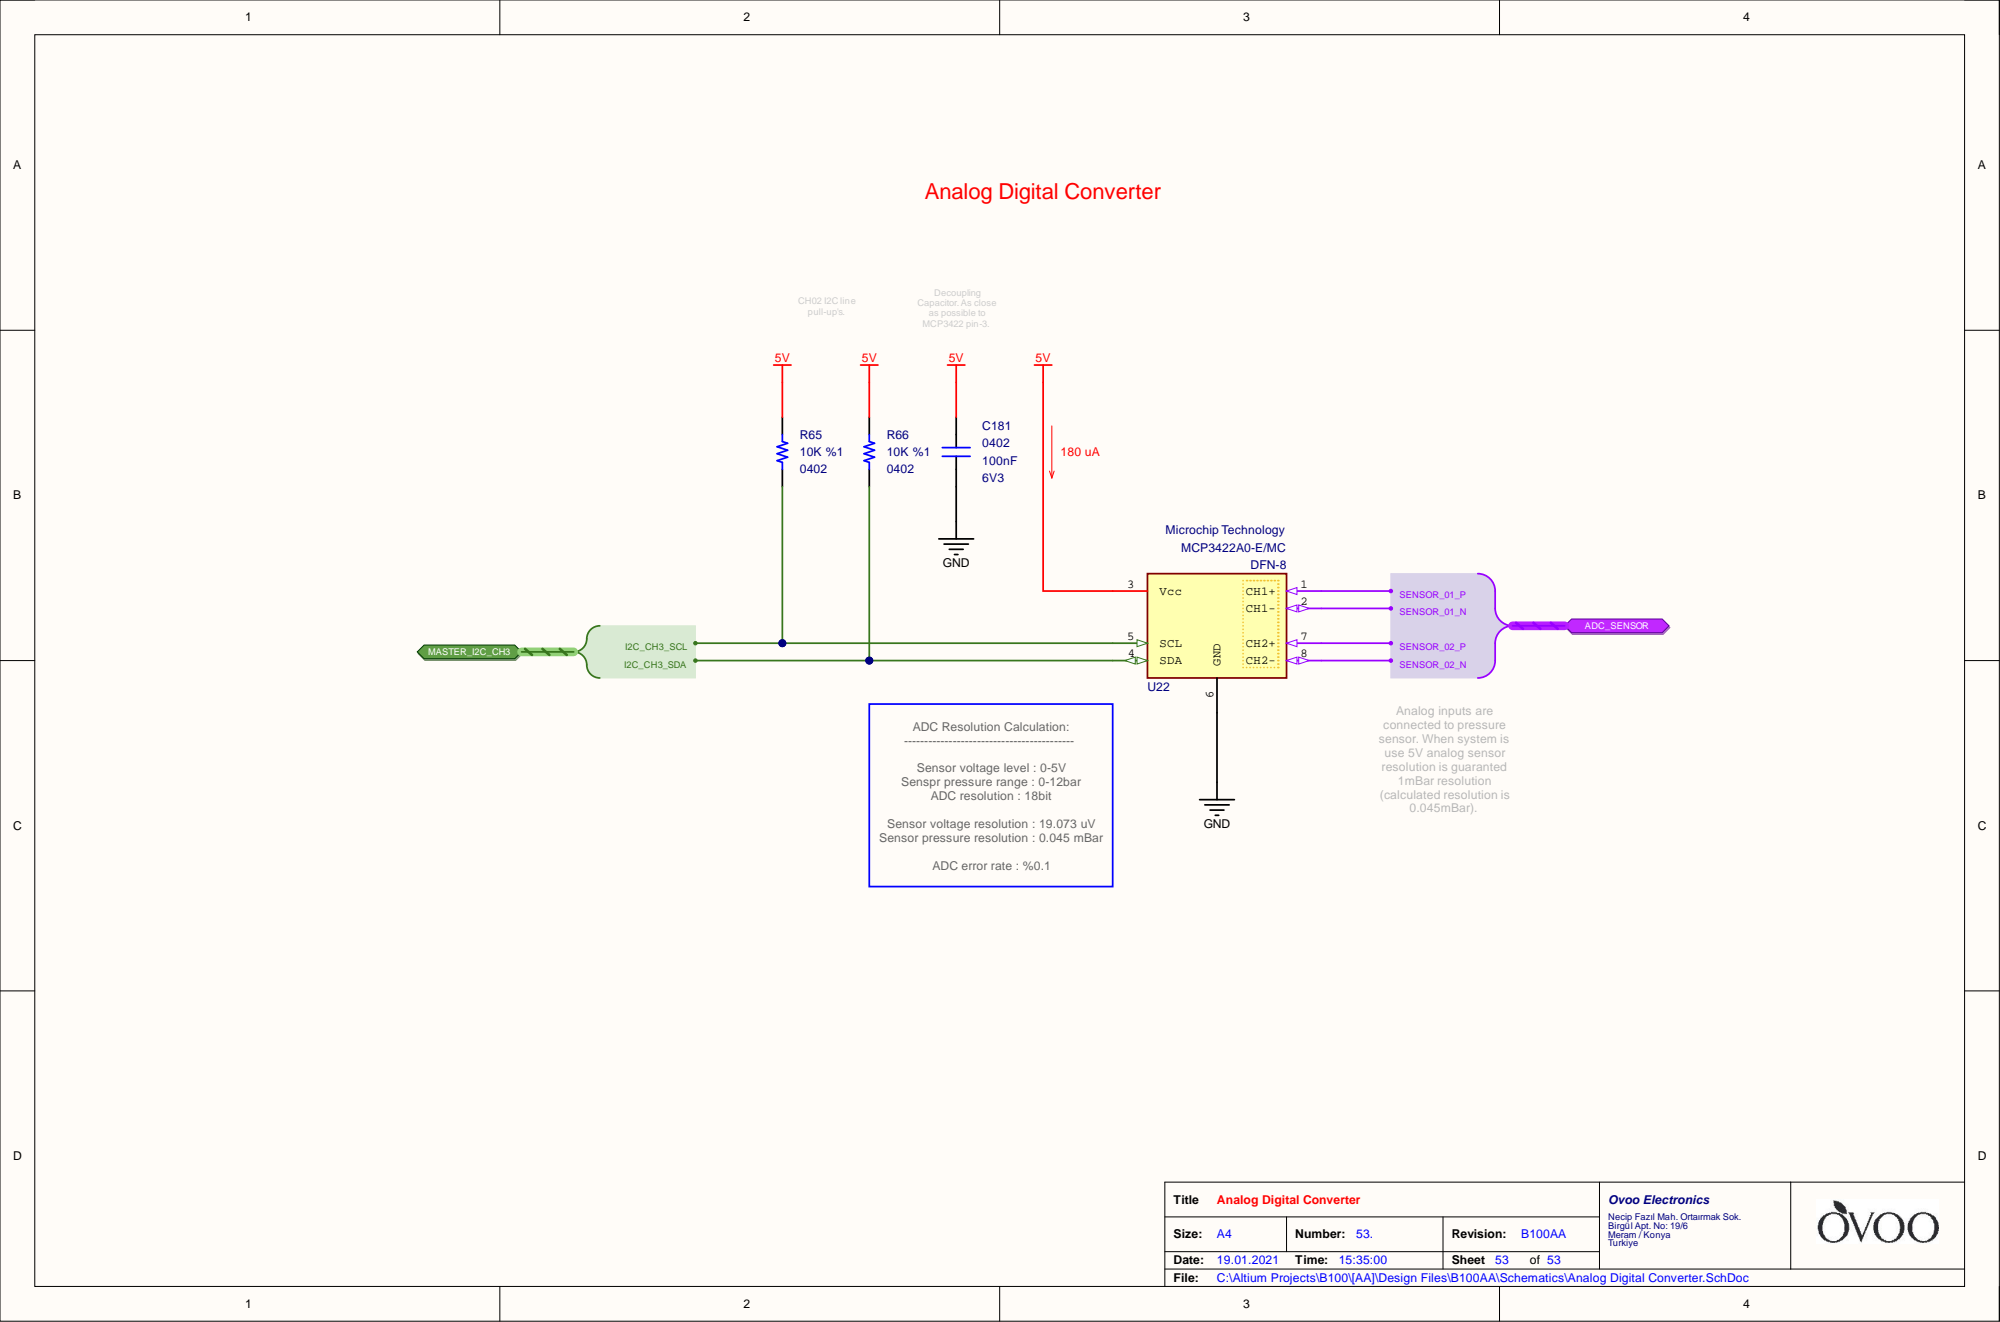
[picture p265: page 53]

Analog inputs are
connected to pressure
sensor. When system is
use 5V analog sensor
resolution is guaranted
1mBar resolution
(calculated resolution is
0.045mBar).

Sensor voltage resolution : 19.073 uV
Sensor pressure resolution : 0.045 mBar

C:\Altium Projects\B100\[AA]\Design Files\B100AA\Schematics\Analog Digital Converter.SchDoc
