akkoyun/B100/[AA]/Design Review/Telit/Review 2/Request Form/B151BA-R1.PDF

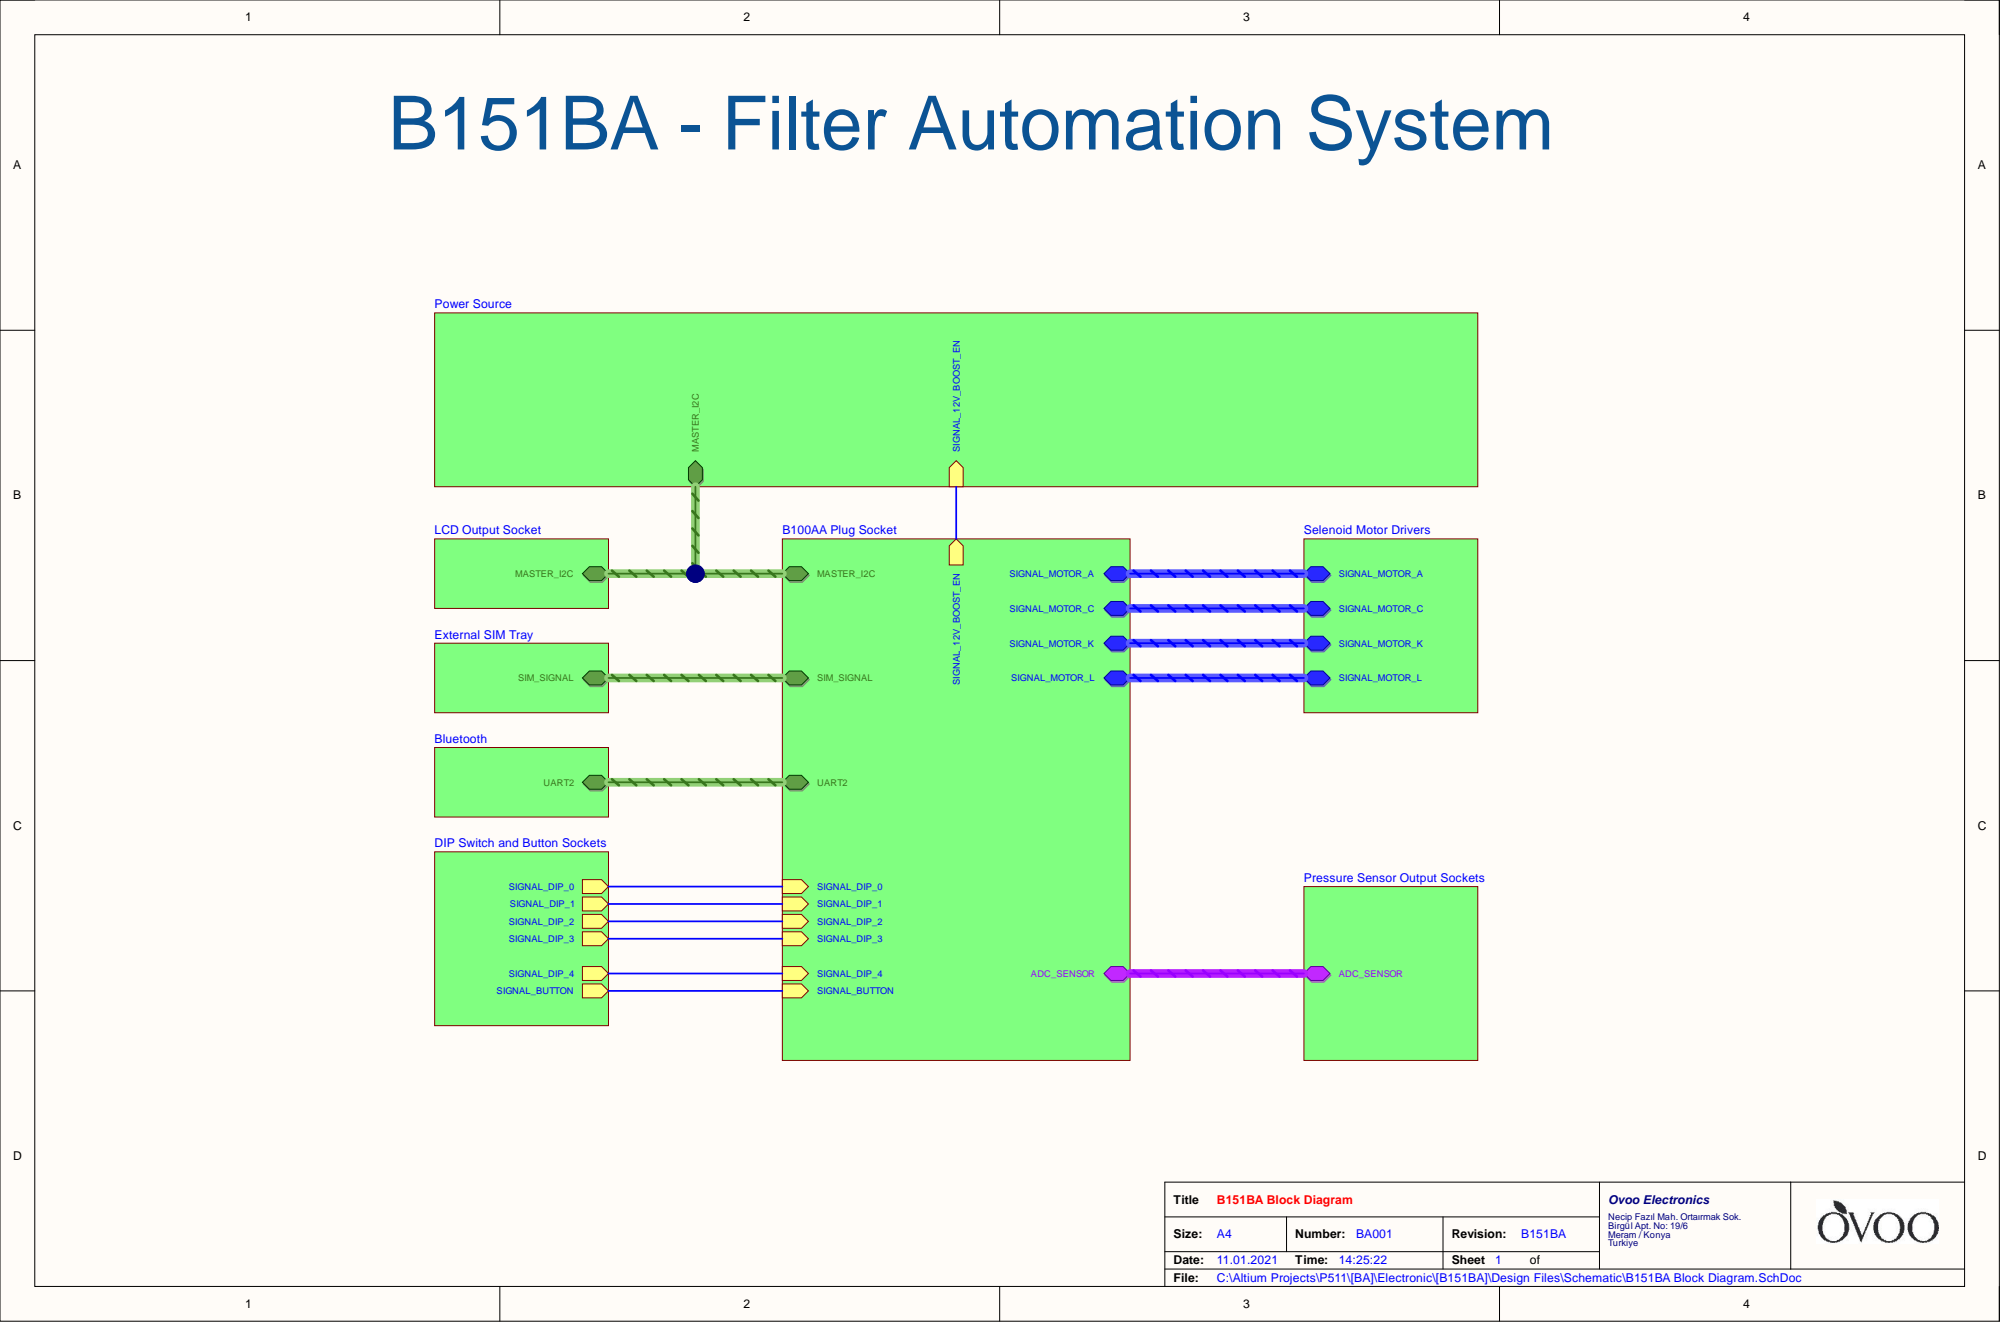
[picture p266: page 1]

DIP Switch and Button Sockets

Pressure Sensor Output Sockets

Necip Fazıl Mah. Ortaırmak Sok. Birgül Apt. No: 19/6 Meram / Konya Turkiye

C:\Altium Projects\P511\[BA]\Electronic\[B151BA]\Design Files\Schematic\B151BA Block Diagram.SchDoc

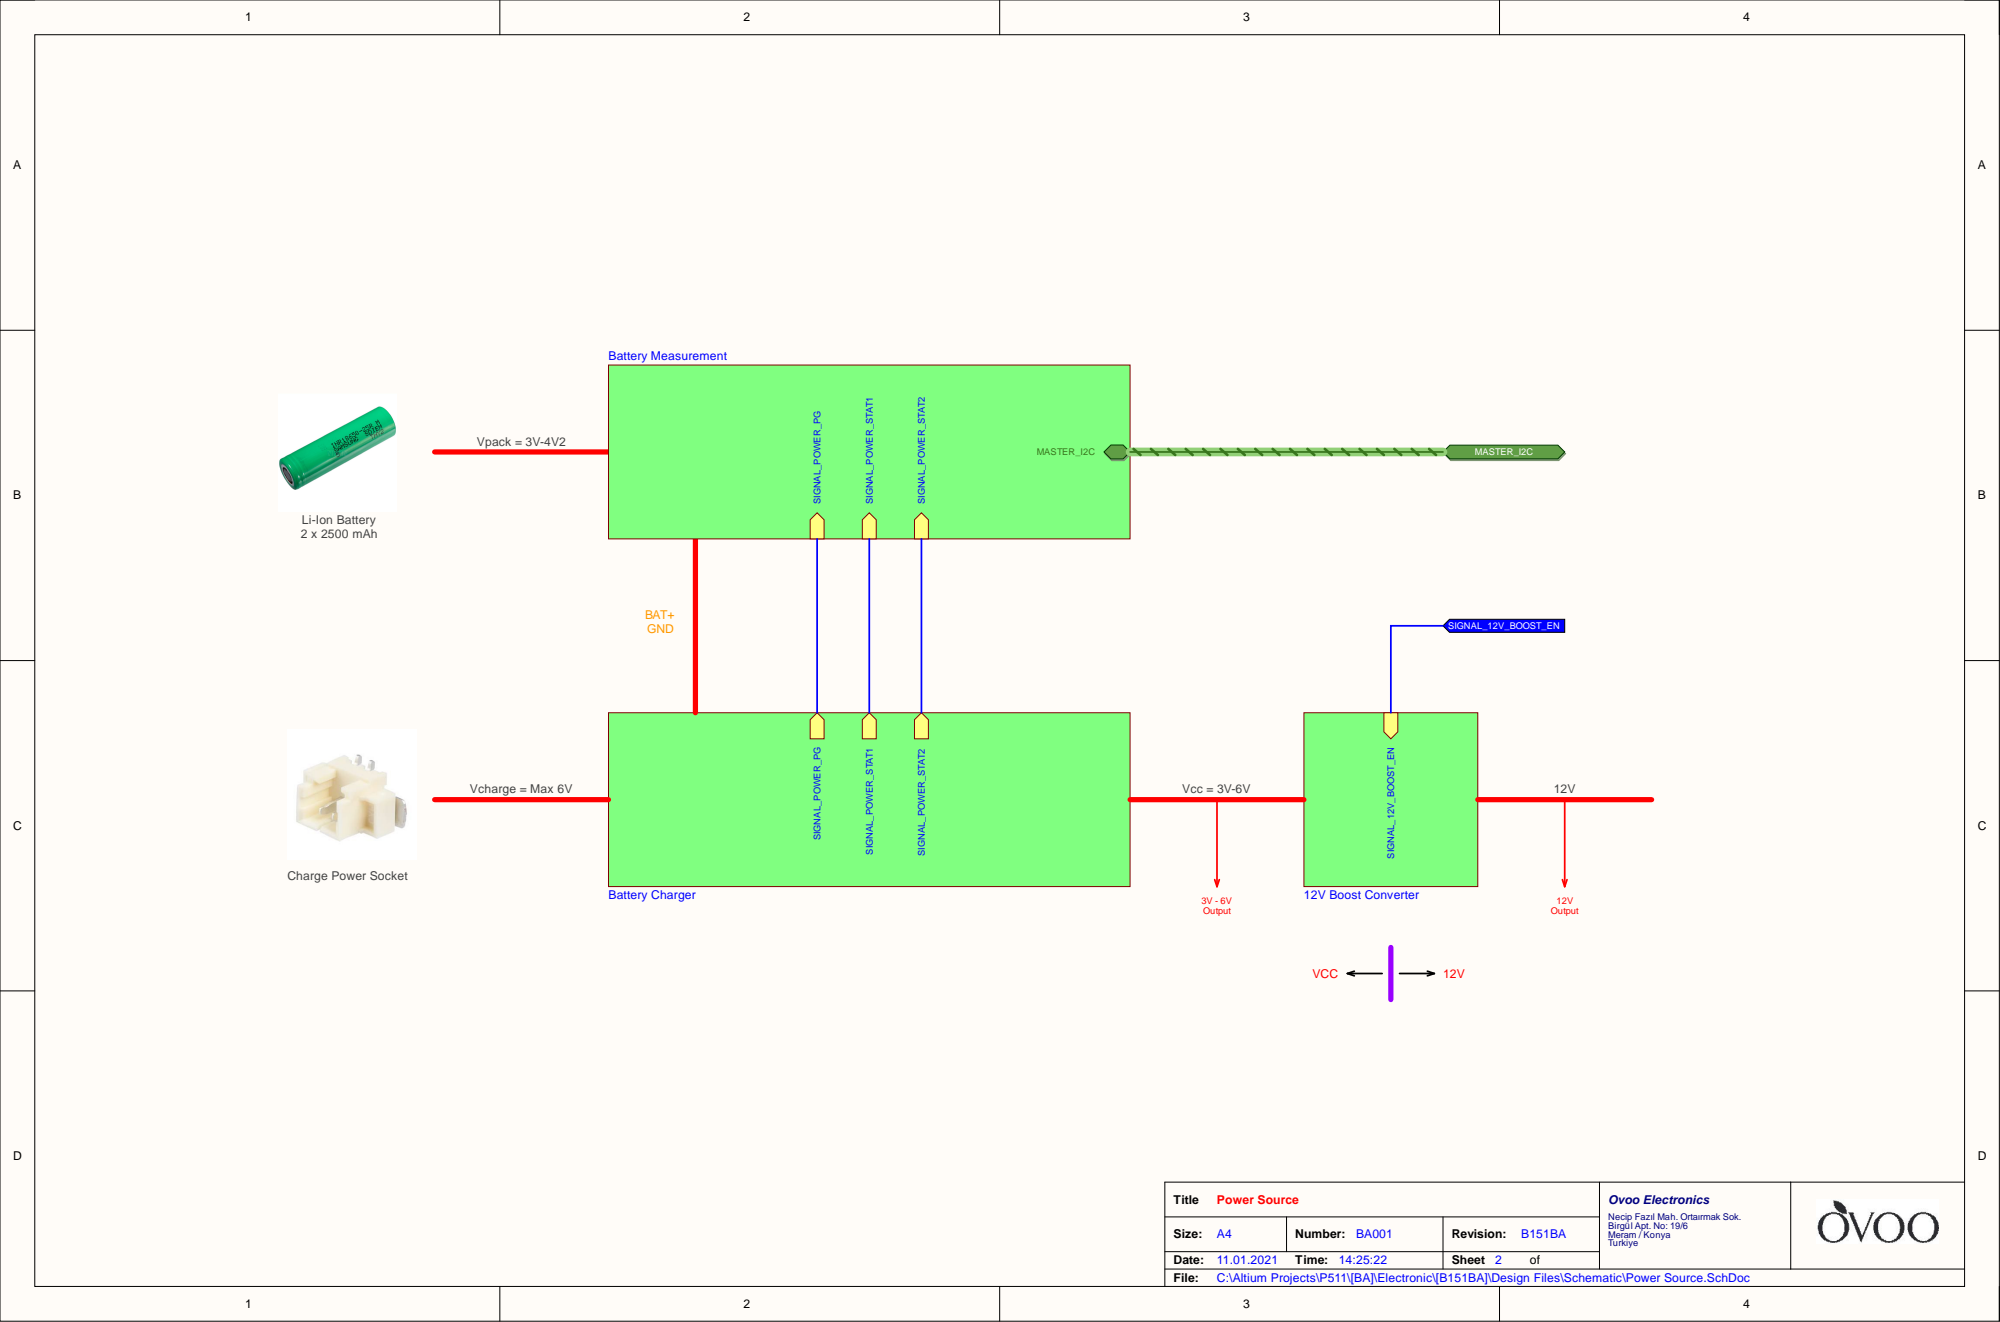
[picture p267: page 2]

Necip Fazıl Mah. Ortaırmak Sok. Birgül Apt. No: 19/6 Meram / Konya Turkiye

C:\Altium Projects\P511\[BA]\Electronic\[B151BA]\Design Files\Schematic\Power Source.SchDoc

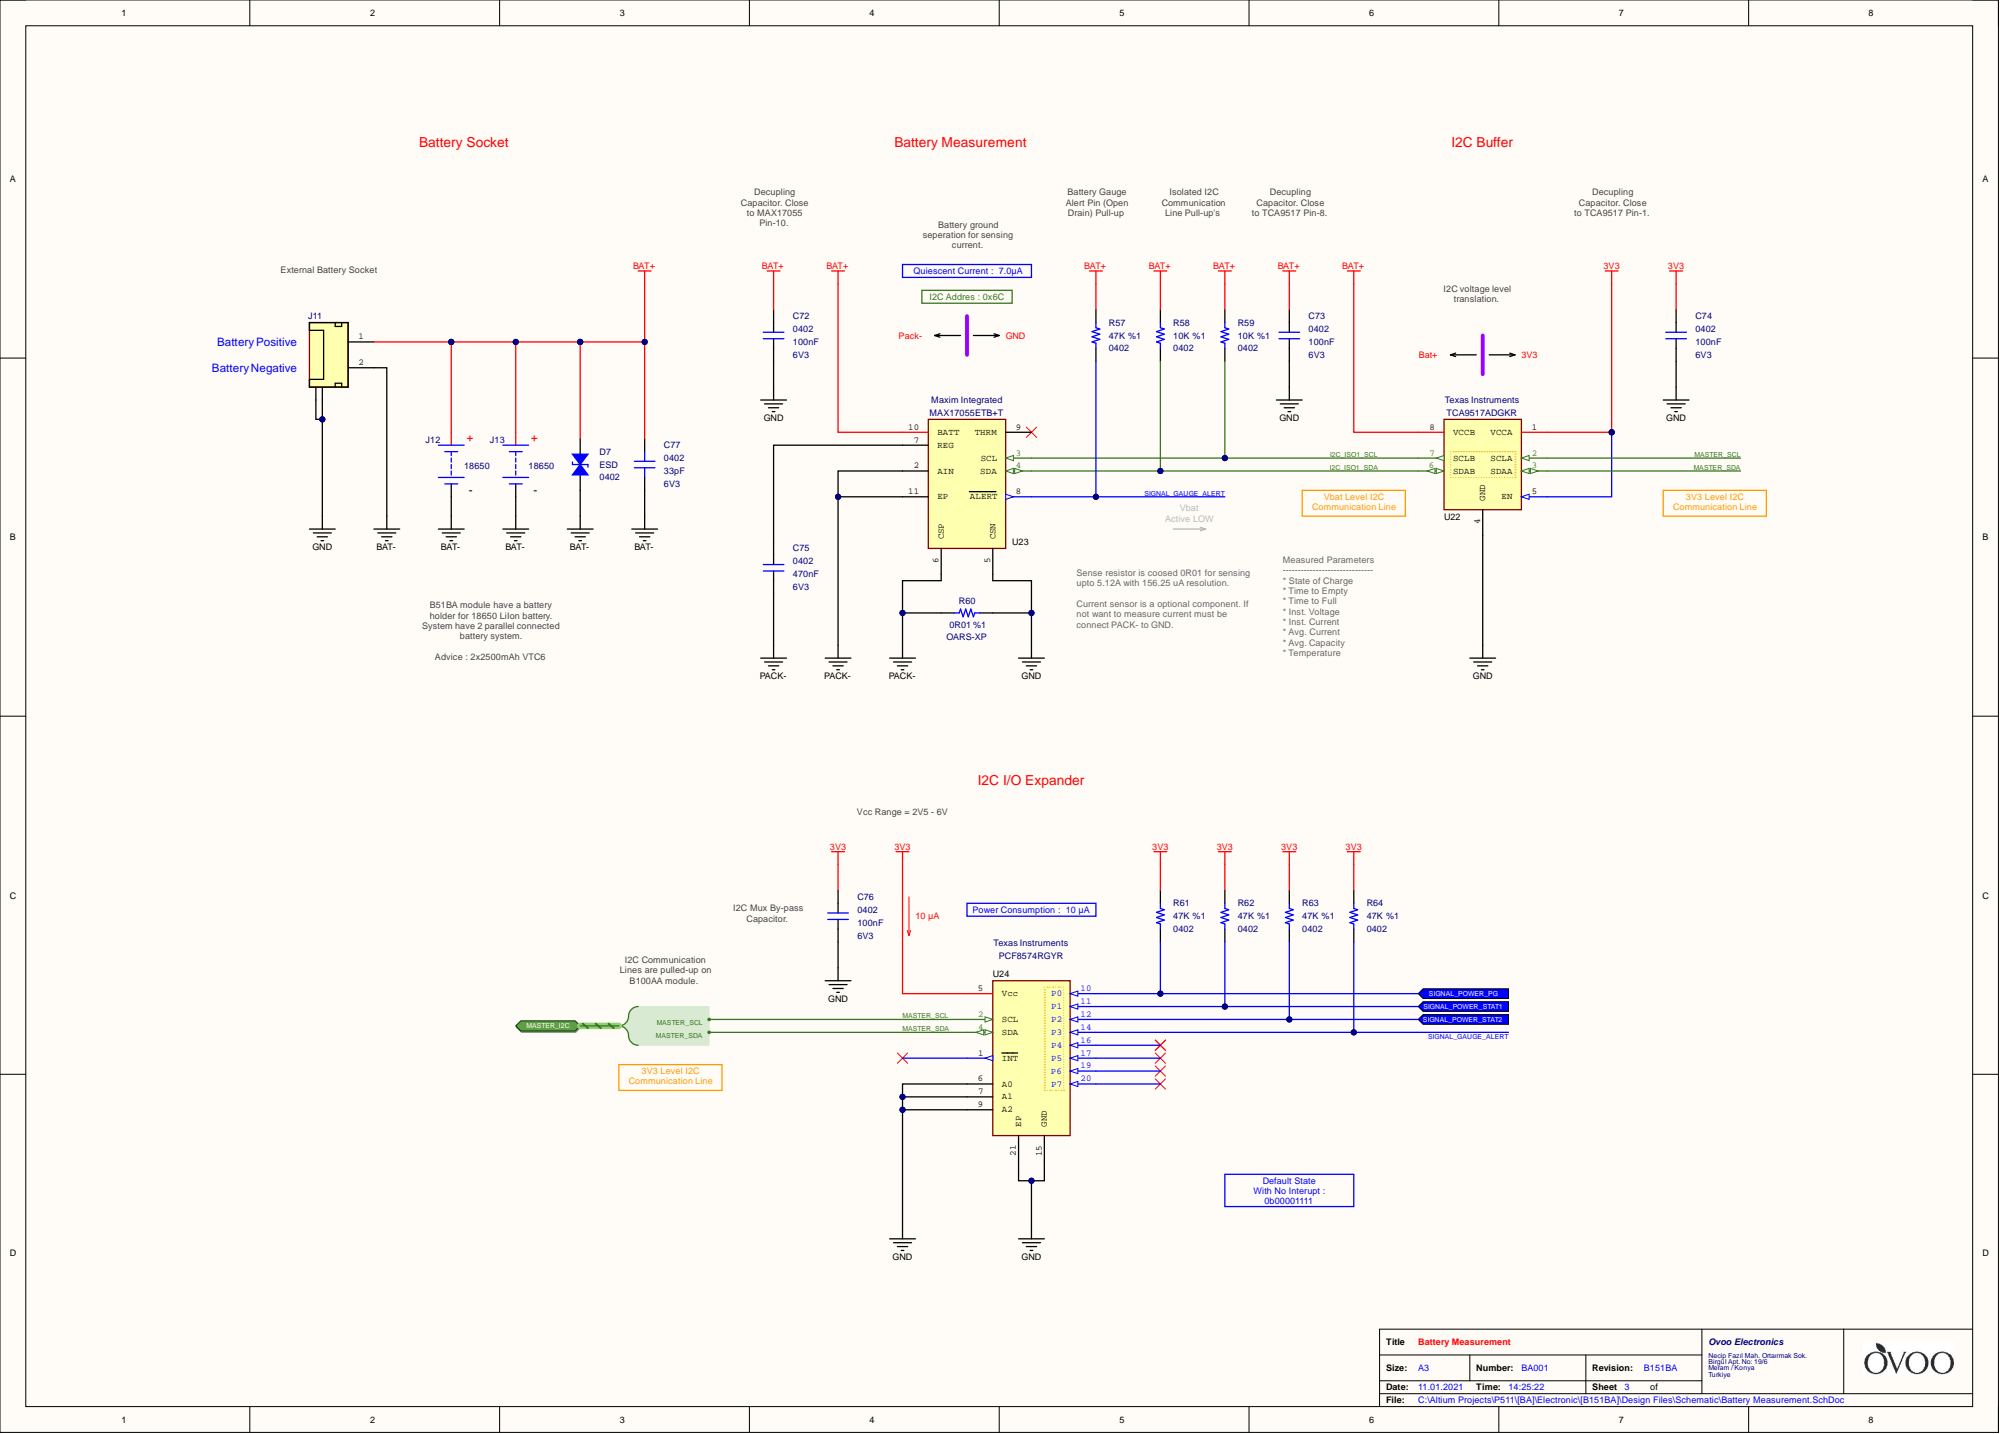
[picture p268: page 3]

Sense resistor is coosed 0R01 for sensing
upto 5.12A with 156.25 uA resolution.

B51BA module have a battery
holder for 18650 LiIon battery.
System have 2 parallel connected

Current sensor is a optional component. If
not want to measure current must be
connect PACK- to GND.

I2C Communication
Lines are pulled-up on
B100AA module.

Necip Fazıl Mah. Ortaırmak Sok. Birgül Apt. No: 19/6 Meram / Konya Turkiye

C:\Altium Projects\P511\[BA]\Electronic\[B151BA]\Design Files\Schematic\Battery Measurement.SchDoc

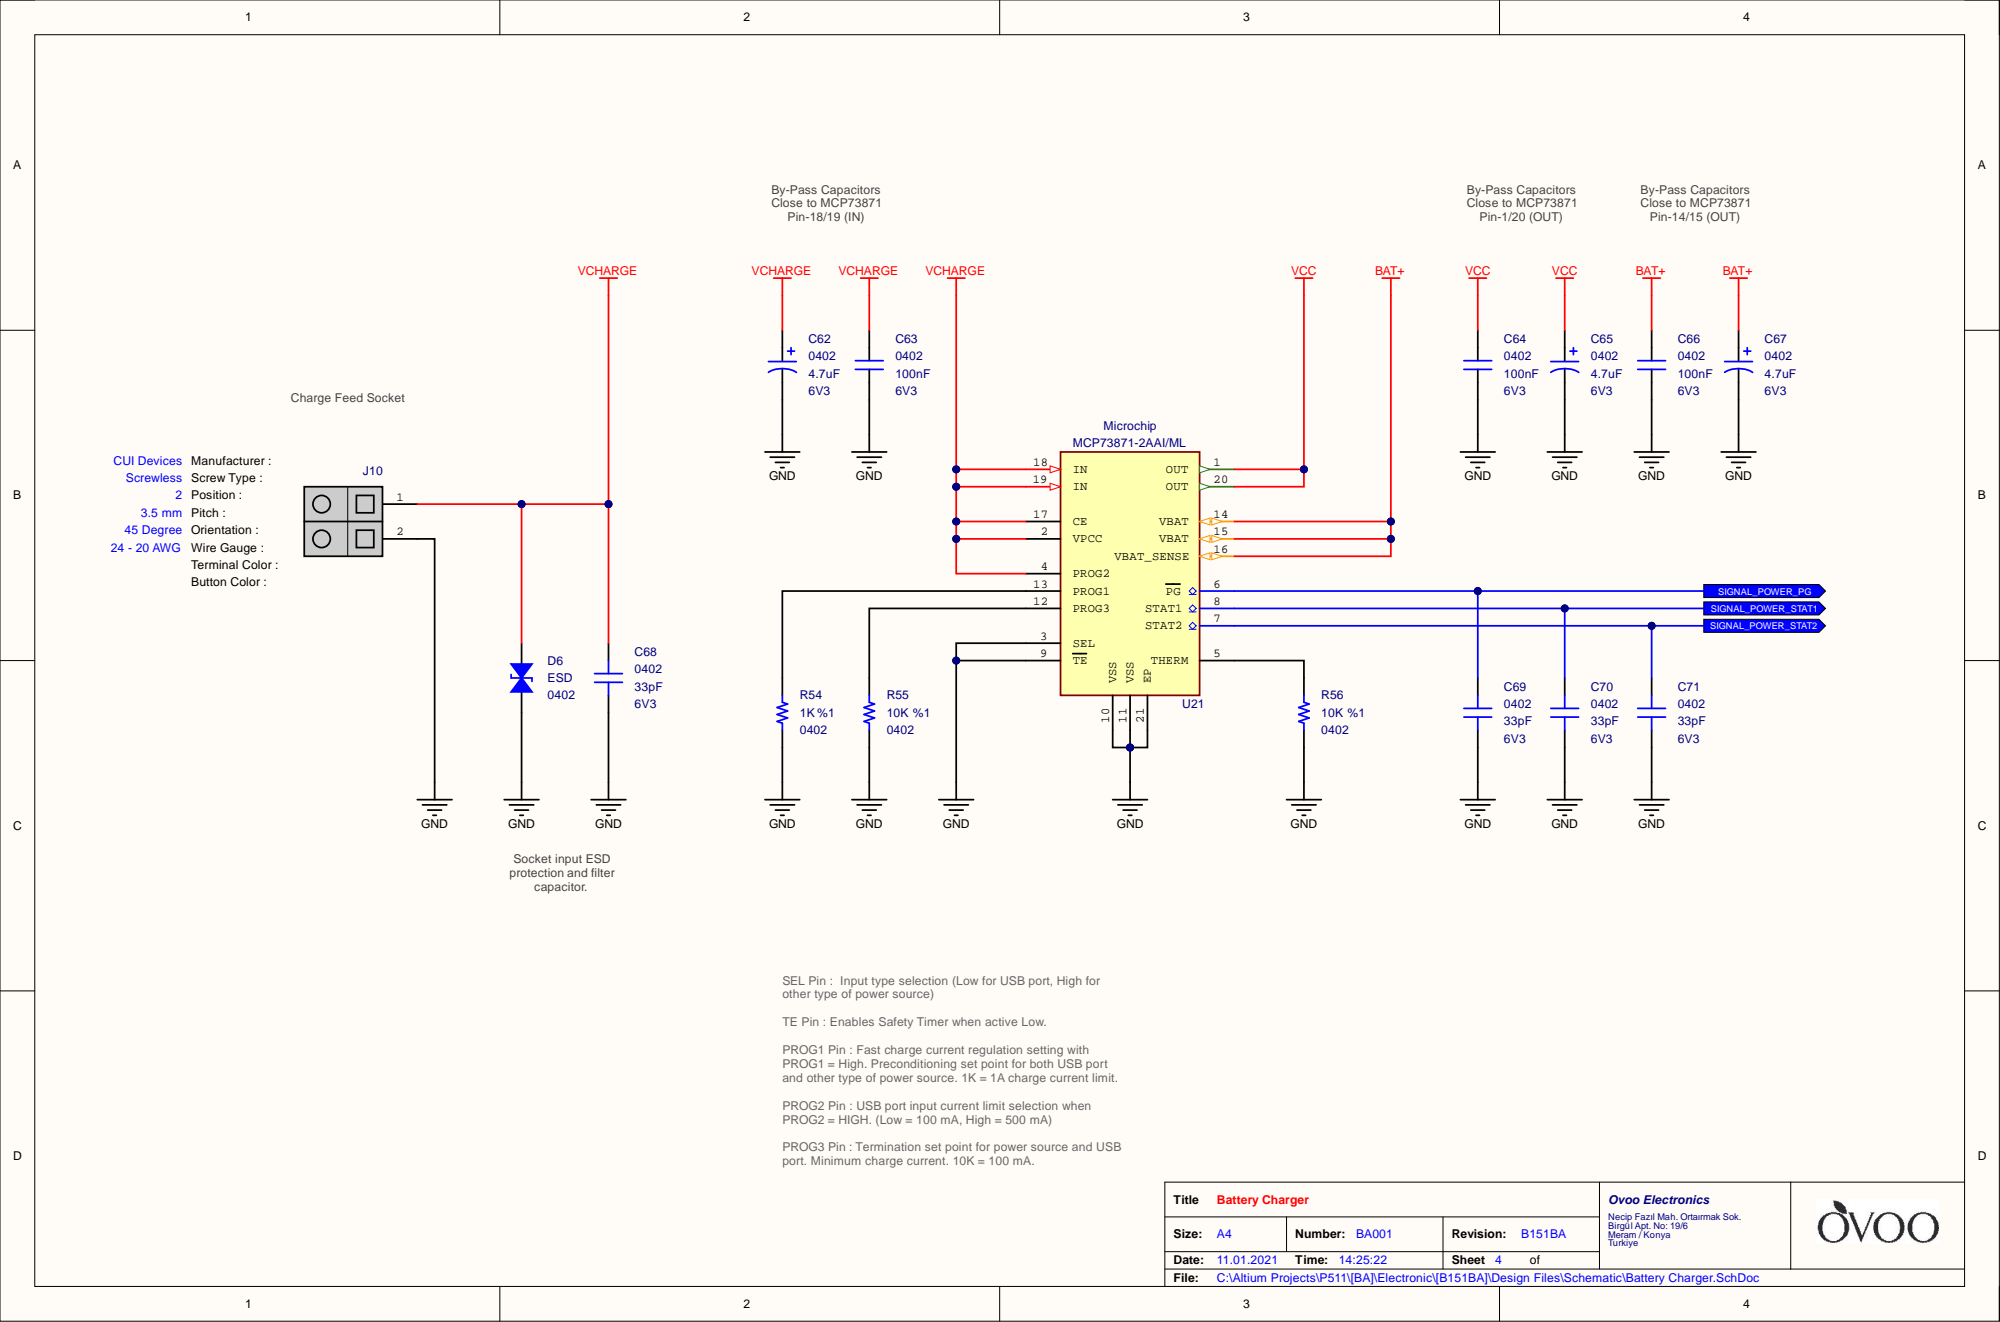
[picture p269: page 4]

1 7 | | 1 4
2 | | 1 5
4 | | 1 6

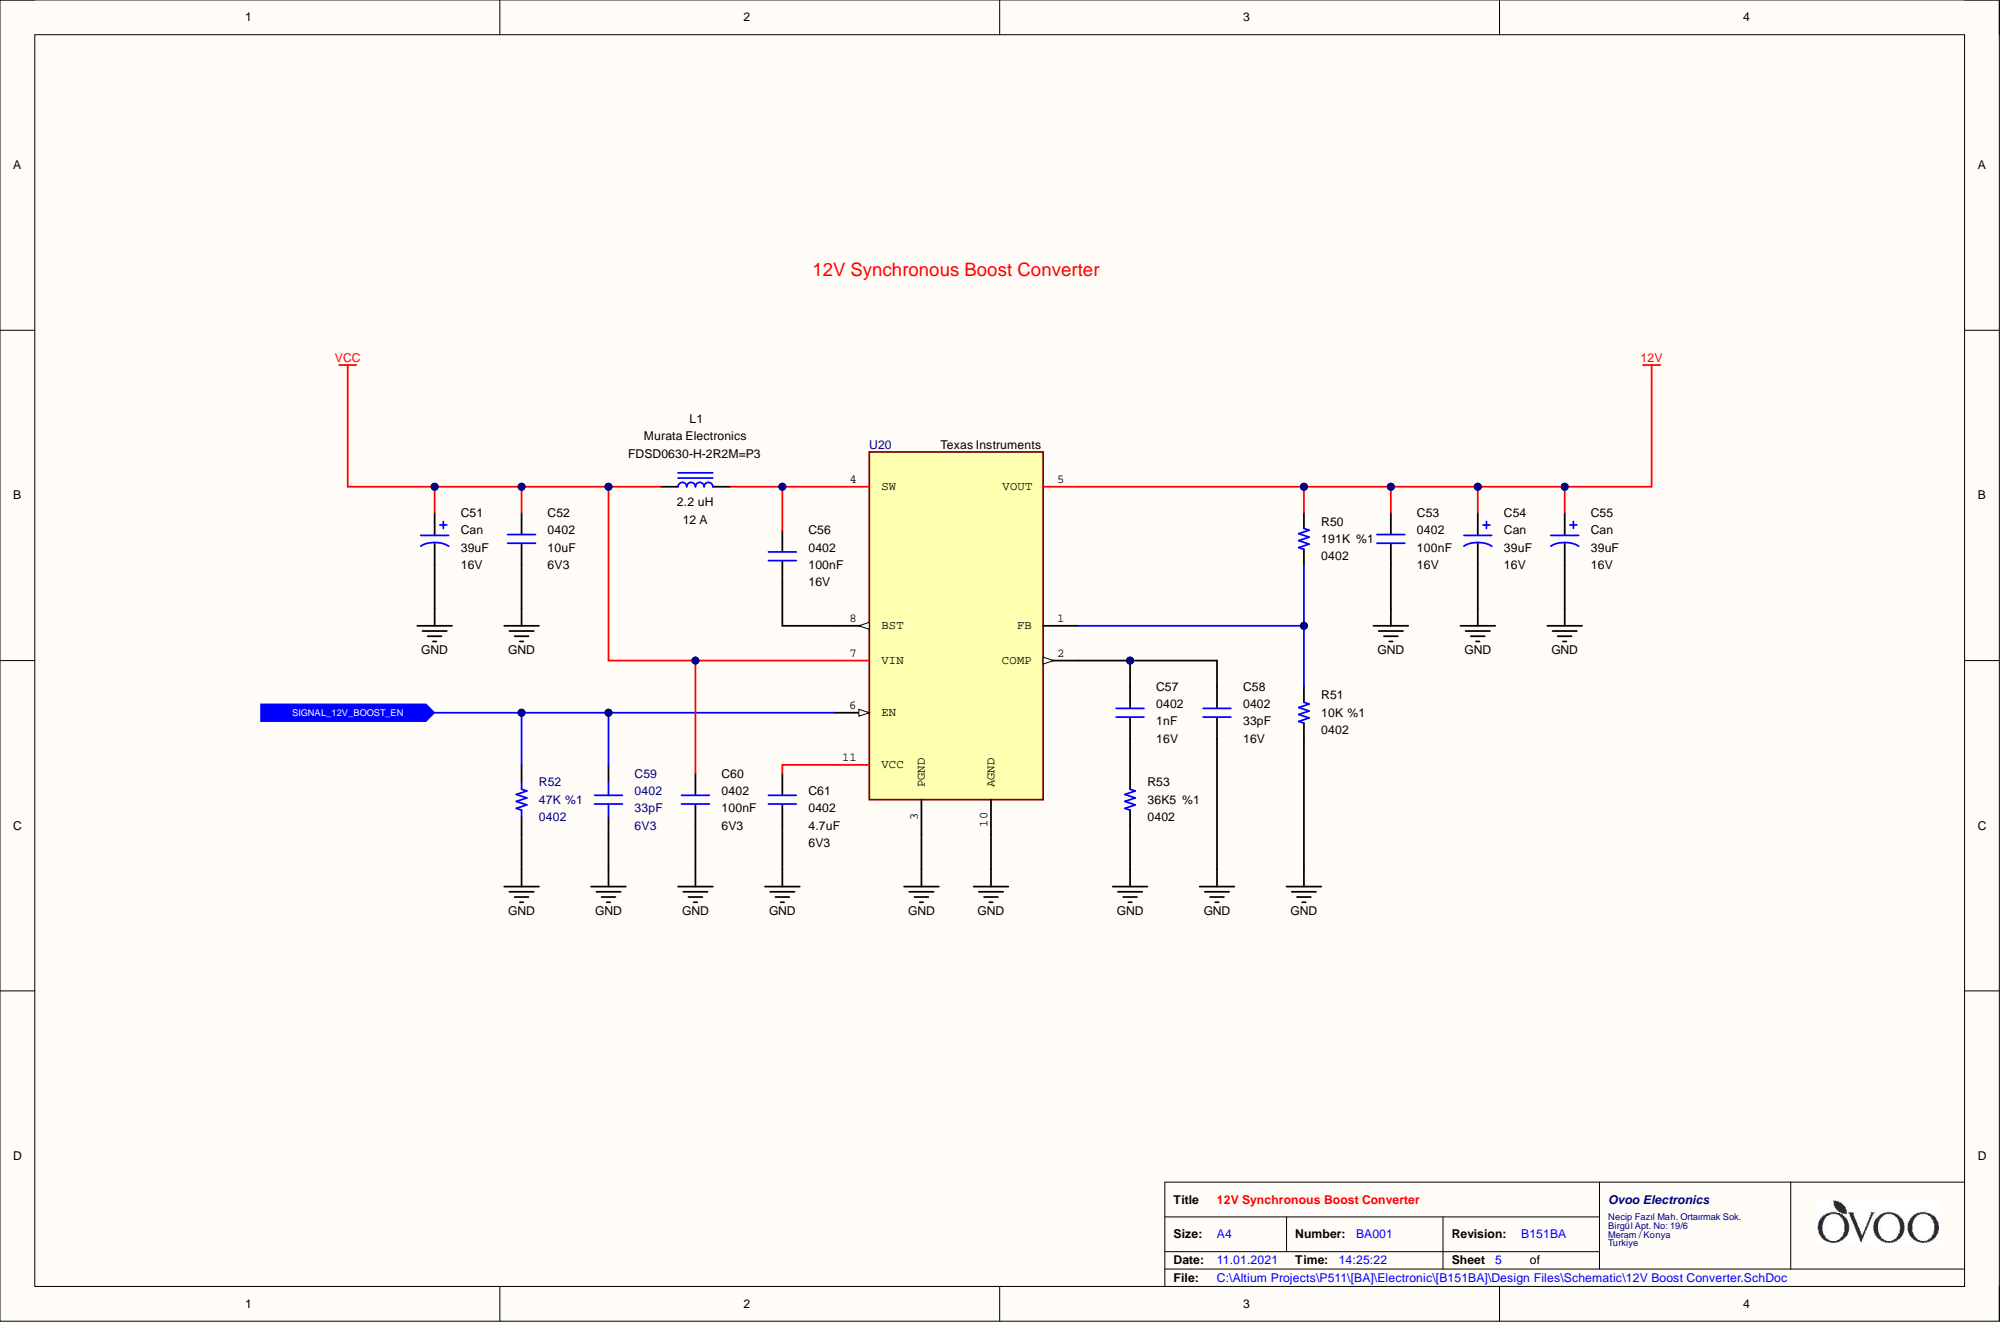
[picture p270: page 5]

Necip Fazıl Mah. Ortaırmak Sok. Birgül Apt. No: 19/6 Meram / Konya Turkiye

C:\Altium Projects\P511\[BA]\Electronic\[B151BA]\Design Files\Schematic\12V Boost Converter.SchDoc

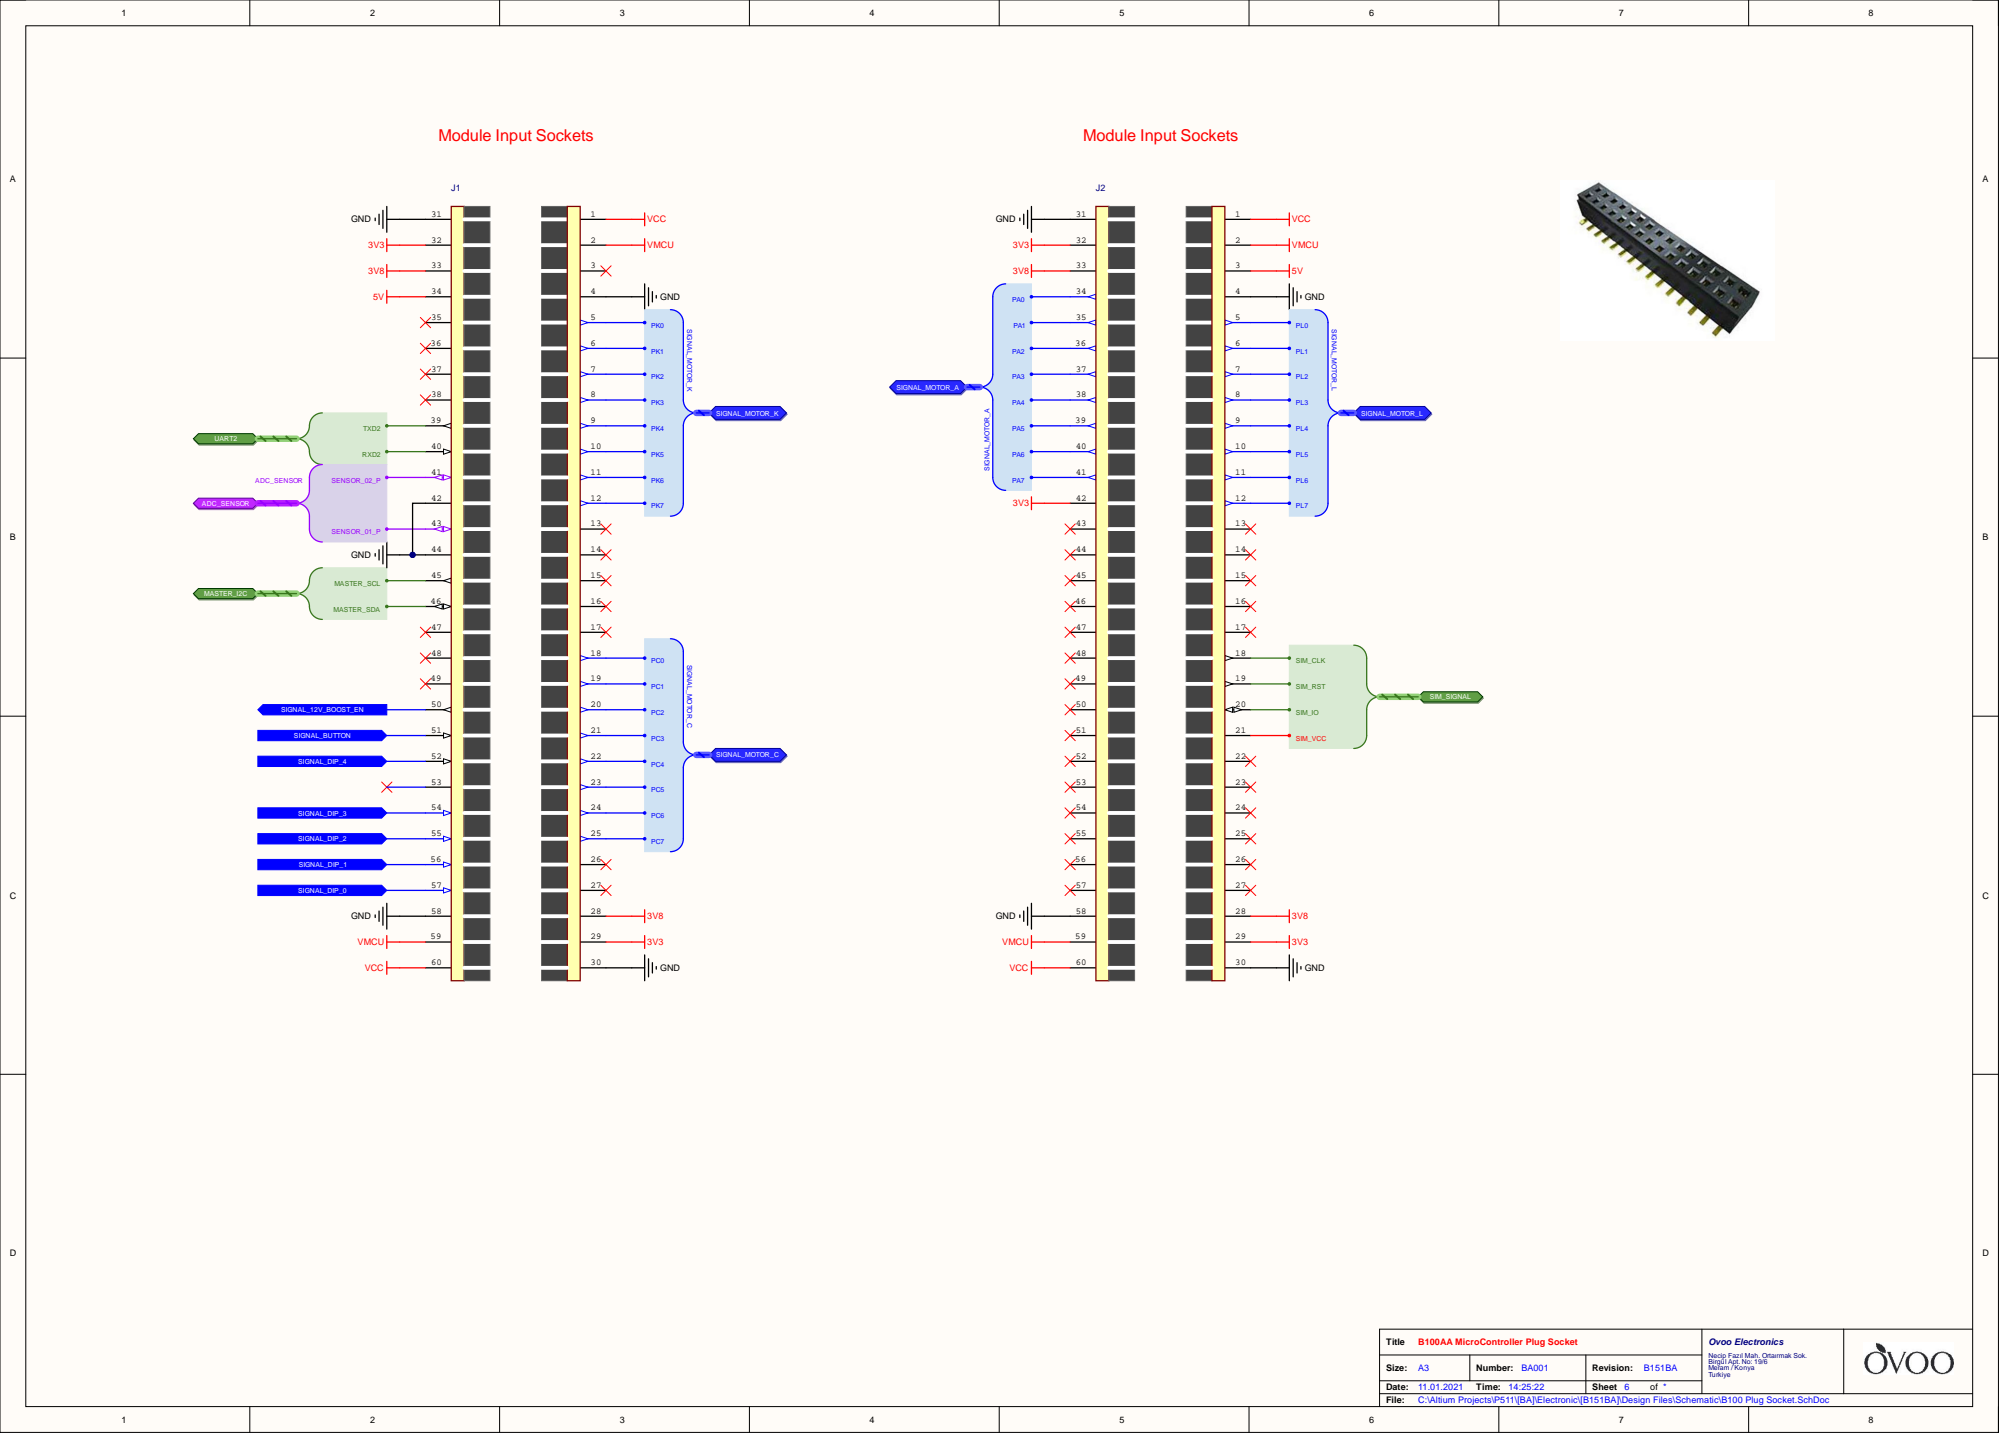
[picture p271: page 6]

Necip Fazıl Mah. Ortaırmak Sok. Birgül Apt. No: 19/6 Meram / Konya Turkiye

C:\Altium Projects\P511\[BA]\Electronic\[B151BA]\Design Files\Schematic\B100 Plug Socket.SchDoc

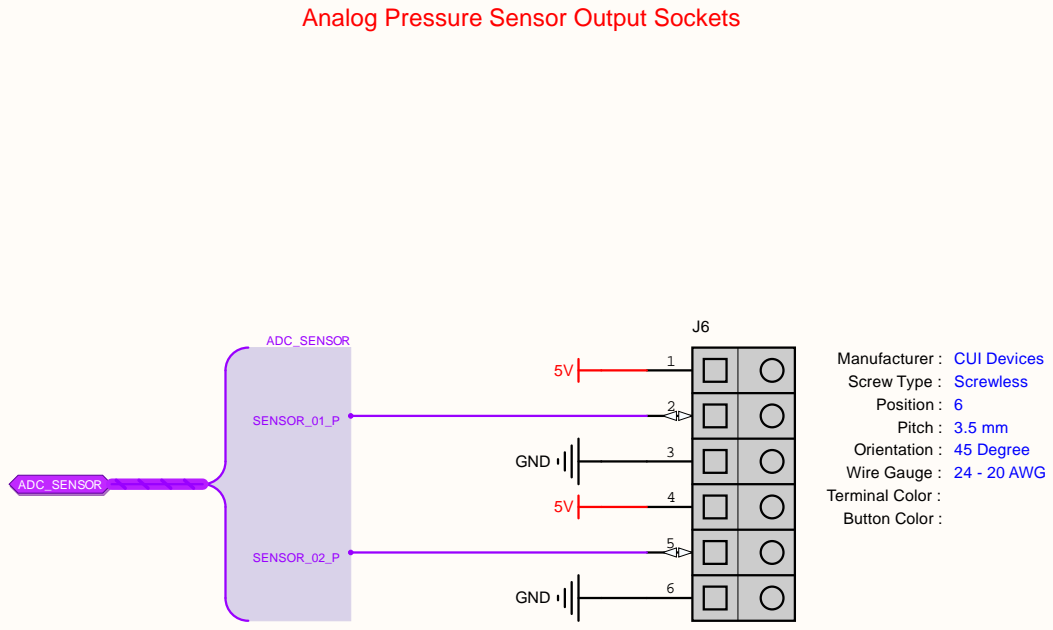
[picture p272: page 7]

Analog Pressure Sensor Output Sockets

Pressure Sensor Output Sockets

Necip Fazıl Mah. Ortaırmak Sok. Birgül Apt. No: 19/6 Meram / Konya Turkiye

C:\Altium Projects\P511\[BA]\Electronic\[B151BA]\Design Files\Schematic\Pressure Sensor Output Sockets.SchDoc

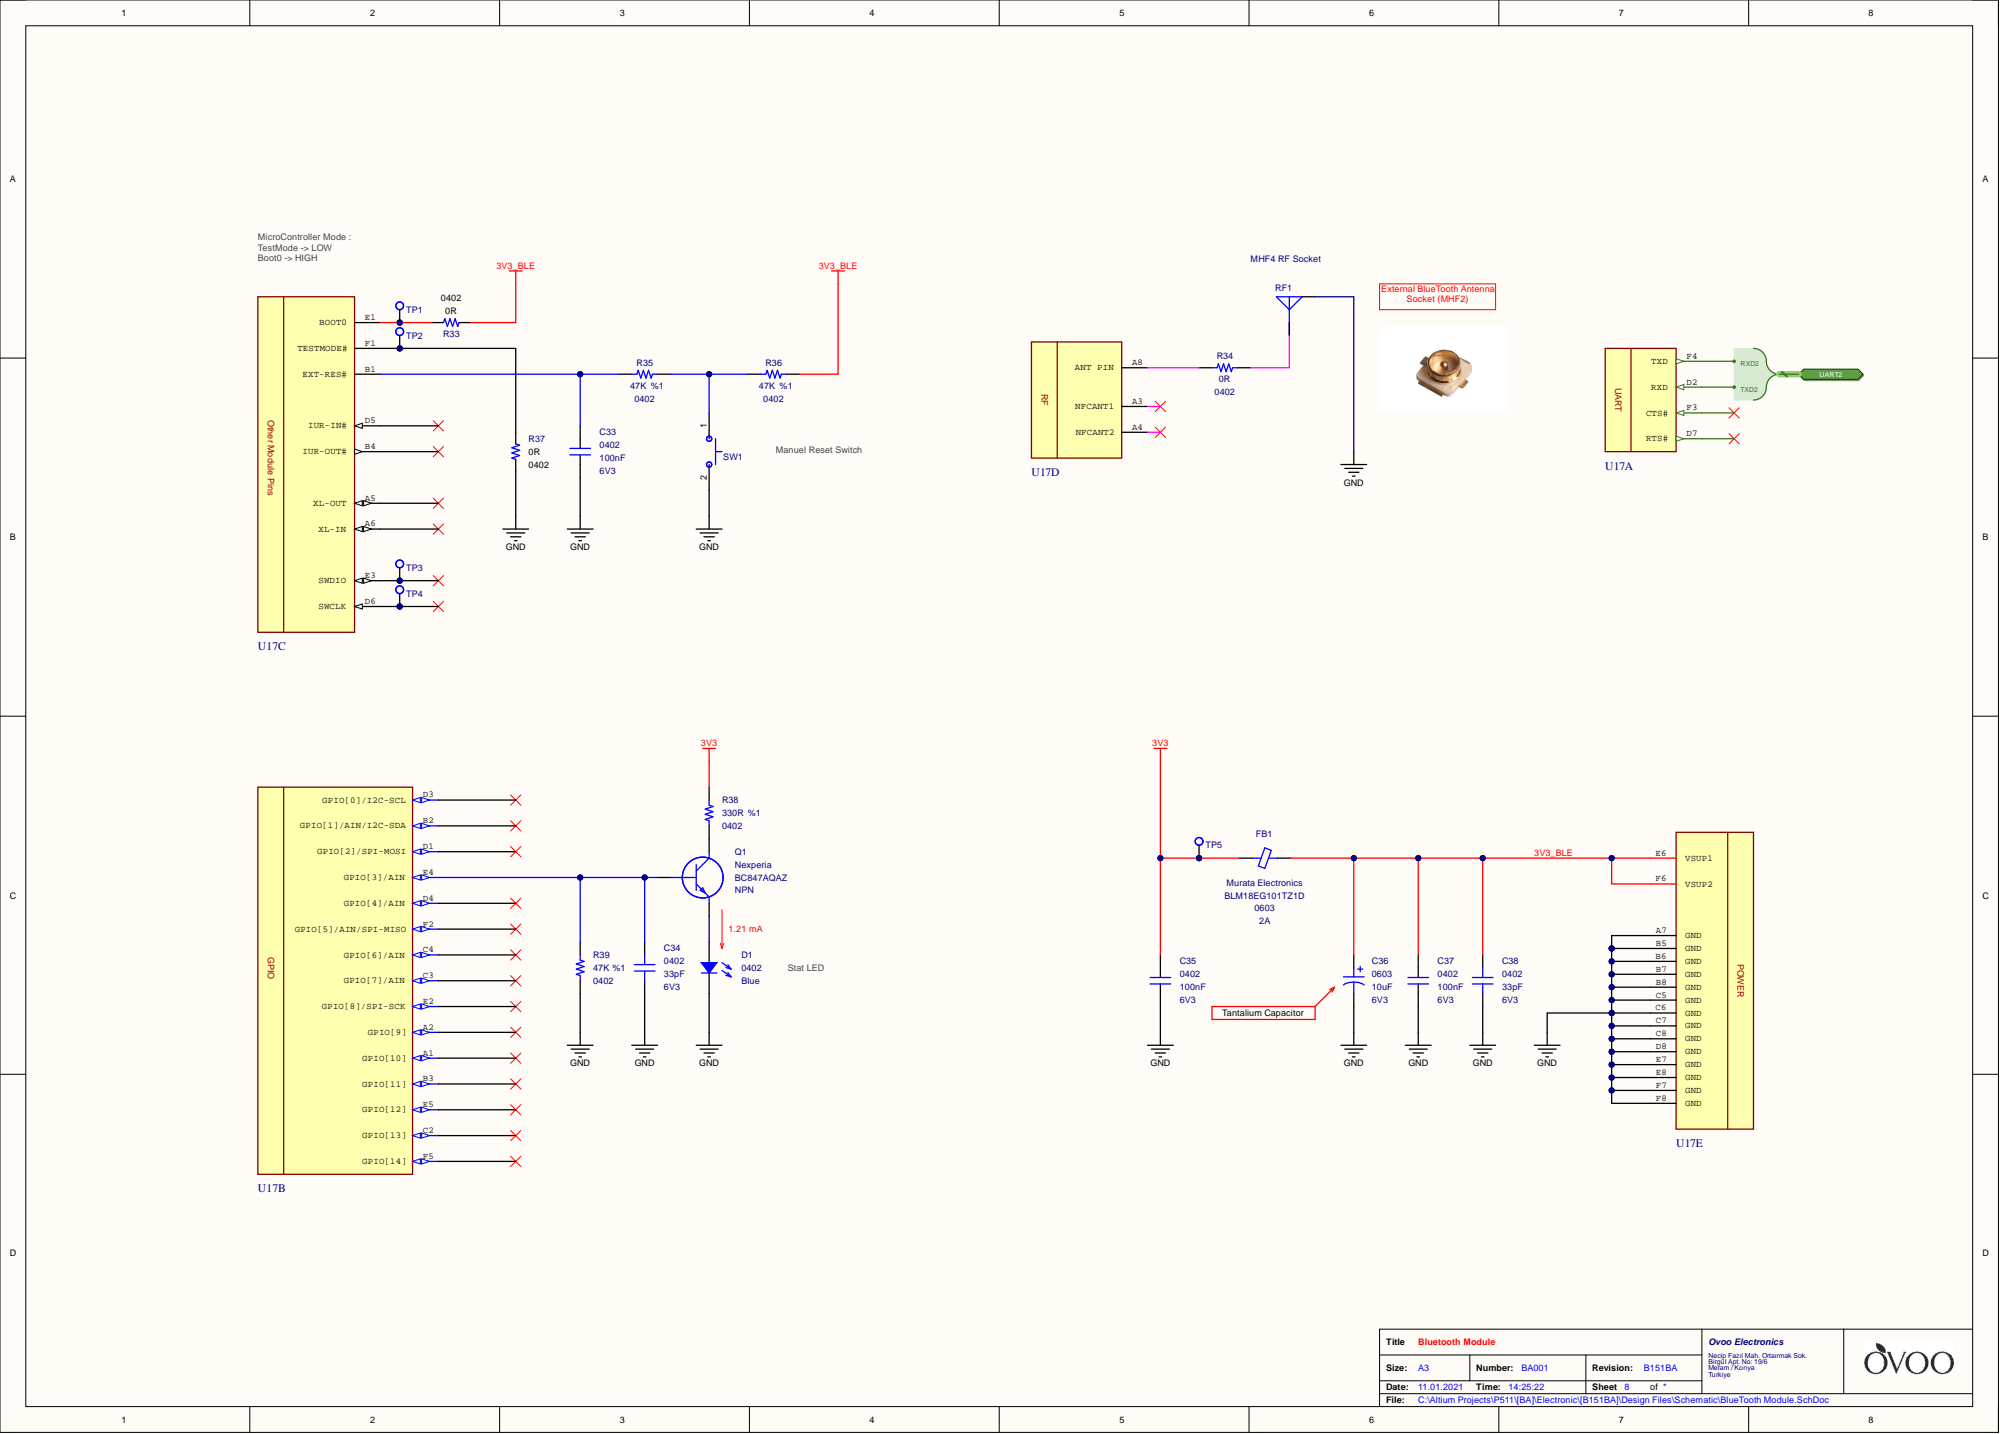
[picture p273: page 8]

Necip Fazıl Mah. Ortaırmak Sok. Birgül Apt. No: 19/6 Meram / Konya Turkiye

C:\Altium Projects\P511\[BA]\Electronic\[B151BA]\Design Files\Schematic\BlueTooth Module.SchDoc

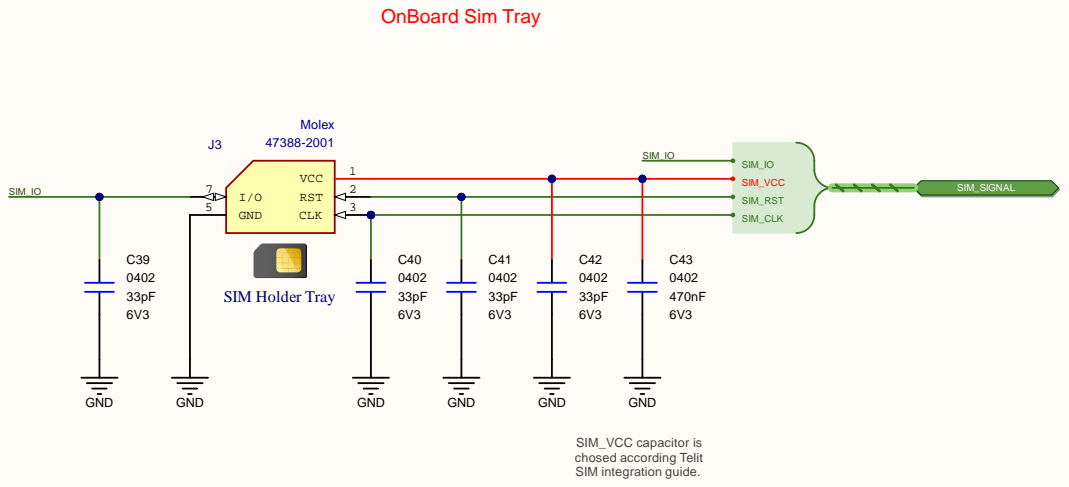
[picture p274: page 9]

Necip Fazıl Mah. Ortaırmak Sok. Birgül Apt. No: 19/6 Meram / Konya Turkiye

C:\Altium Projects\P511\[BA]\Electronic\[B151BA]\Design Files\Schematic\External SIM Tray.SchDoc

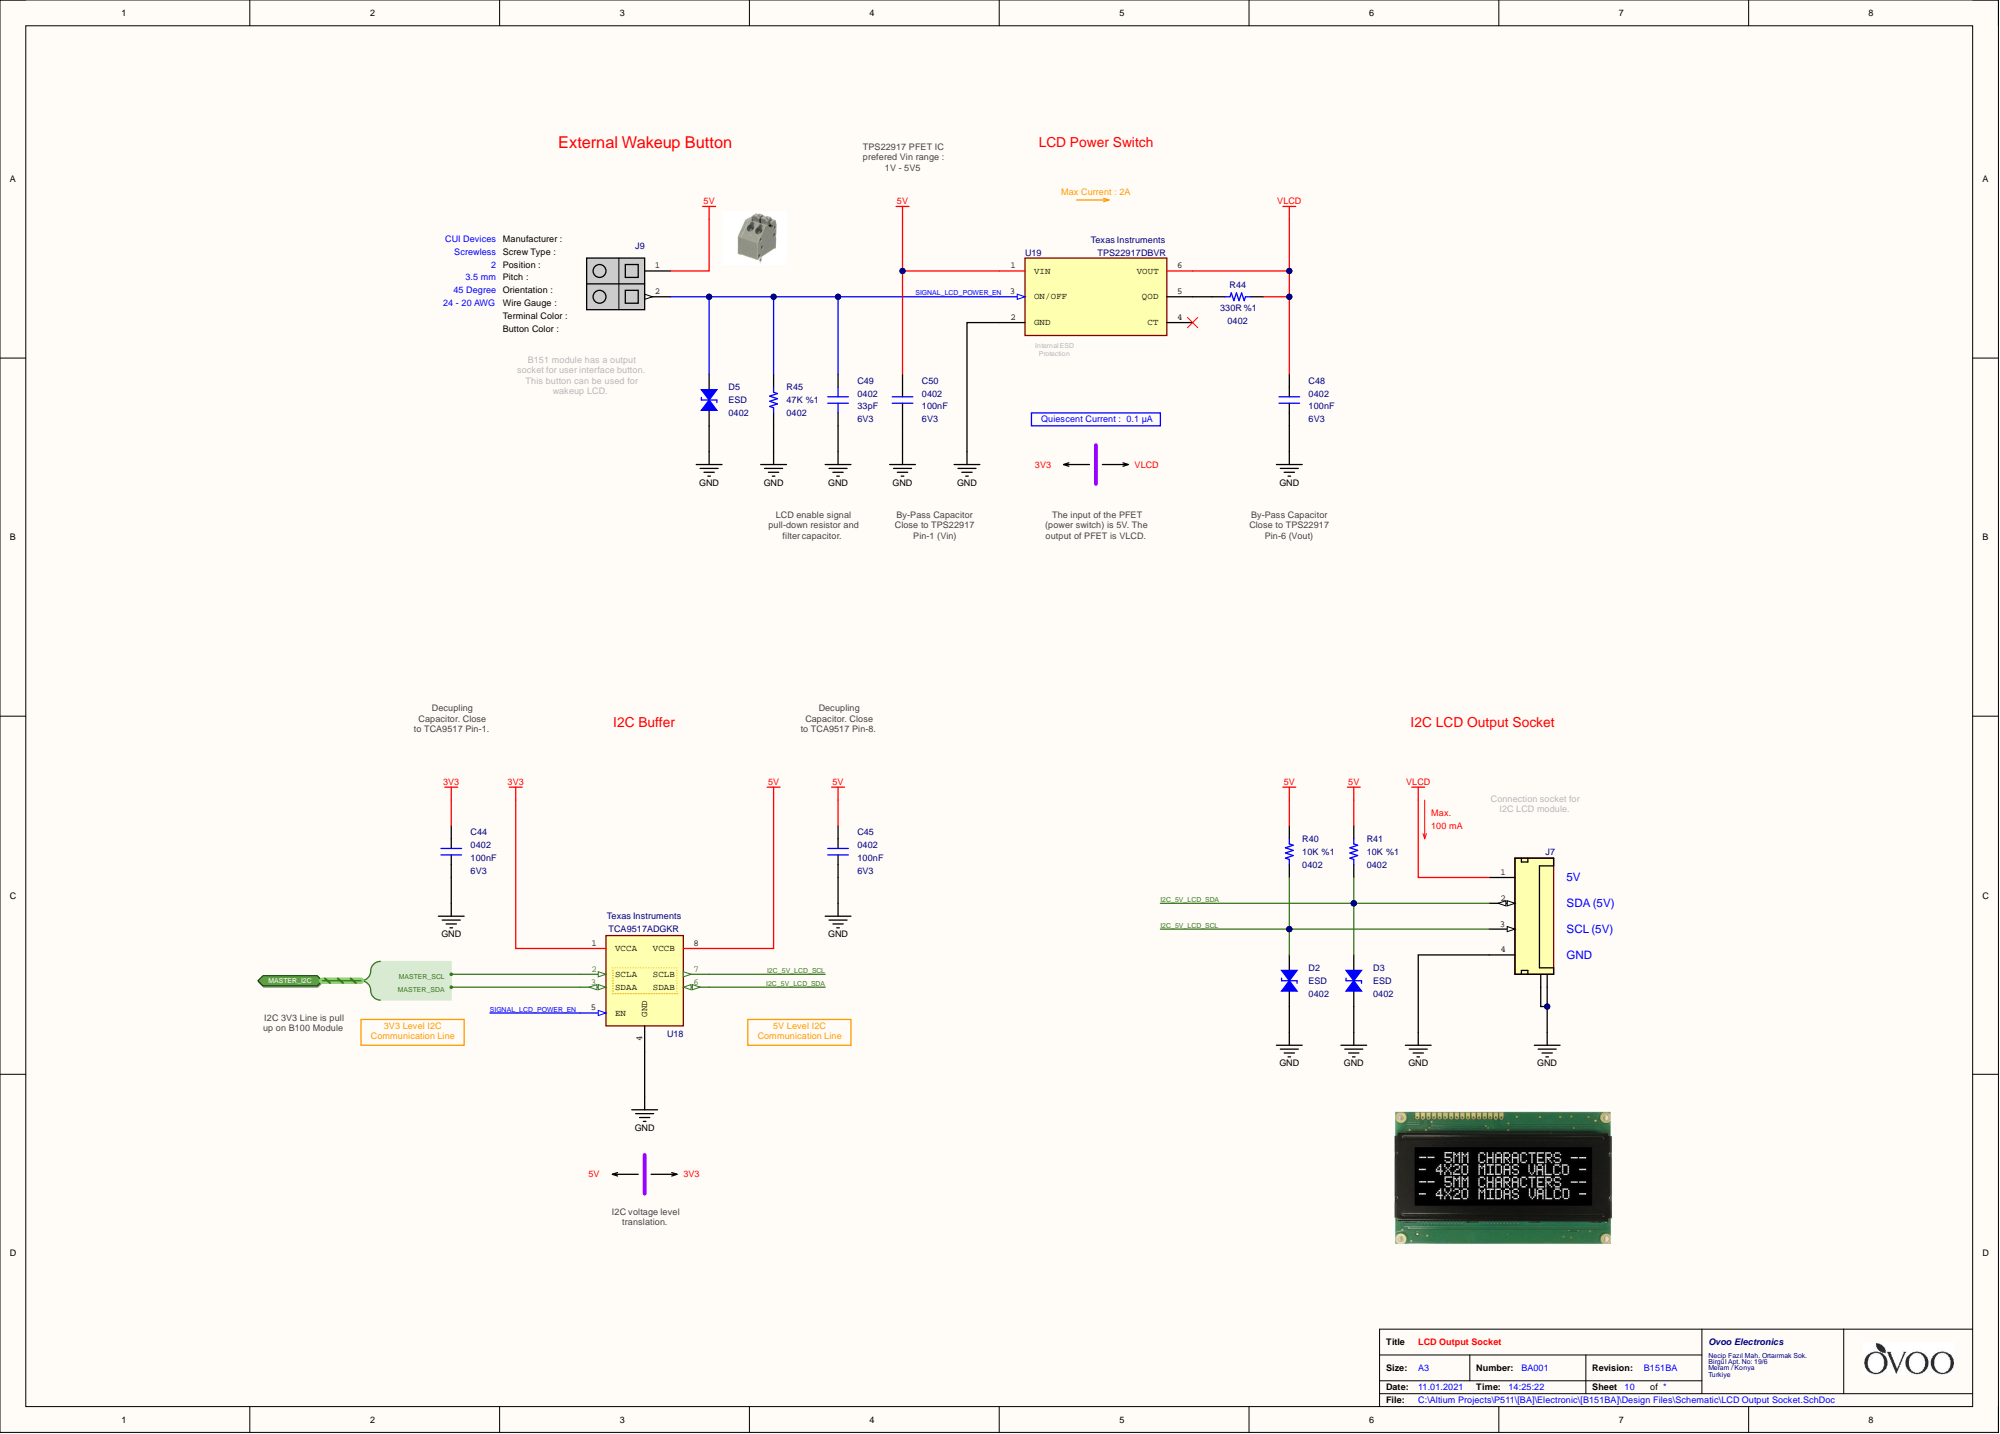
[picture p275: page 10]

B151 module has a output
socket for user interface button.
This button can be used for

LCD enable signal
pull-down resistor and
filter capacitor.

The input of the PFET
(power switch) is 5V. The
output of PFET is VLCD.

Necip Fazıl Mah. Ortaırmak Sok. Birgül Apt. No: 19/6 Meram / Konya Turkiye

C:\Altium Projects\P511\[BA]\Electronic\[B151BA]\Design Files\Schematic\LCD Output Socket.SchDoc

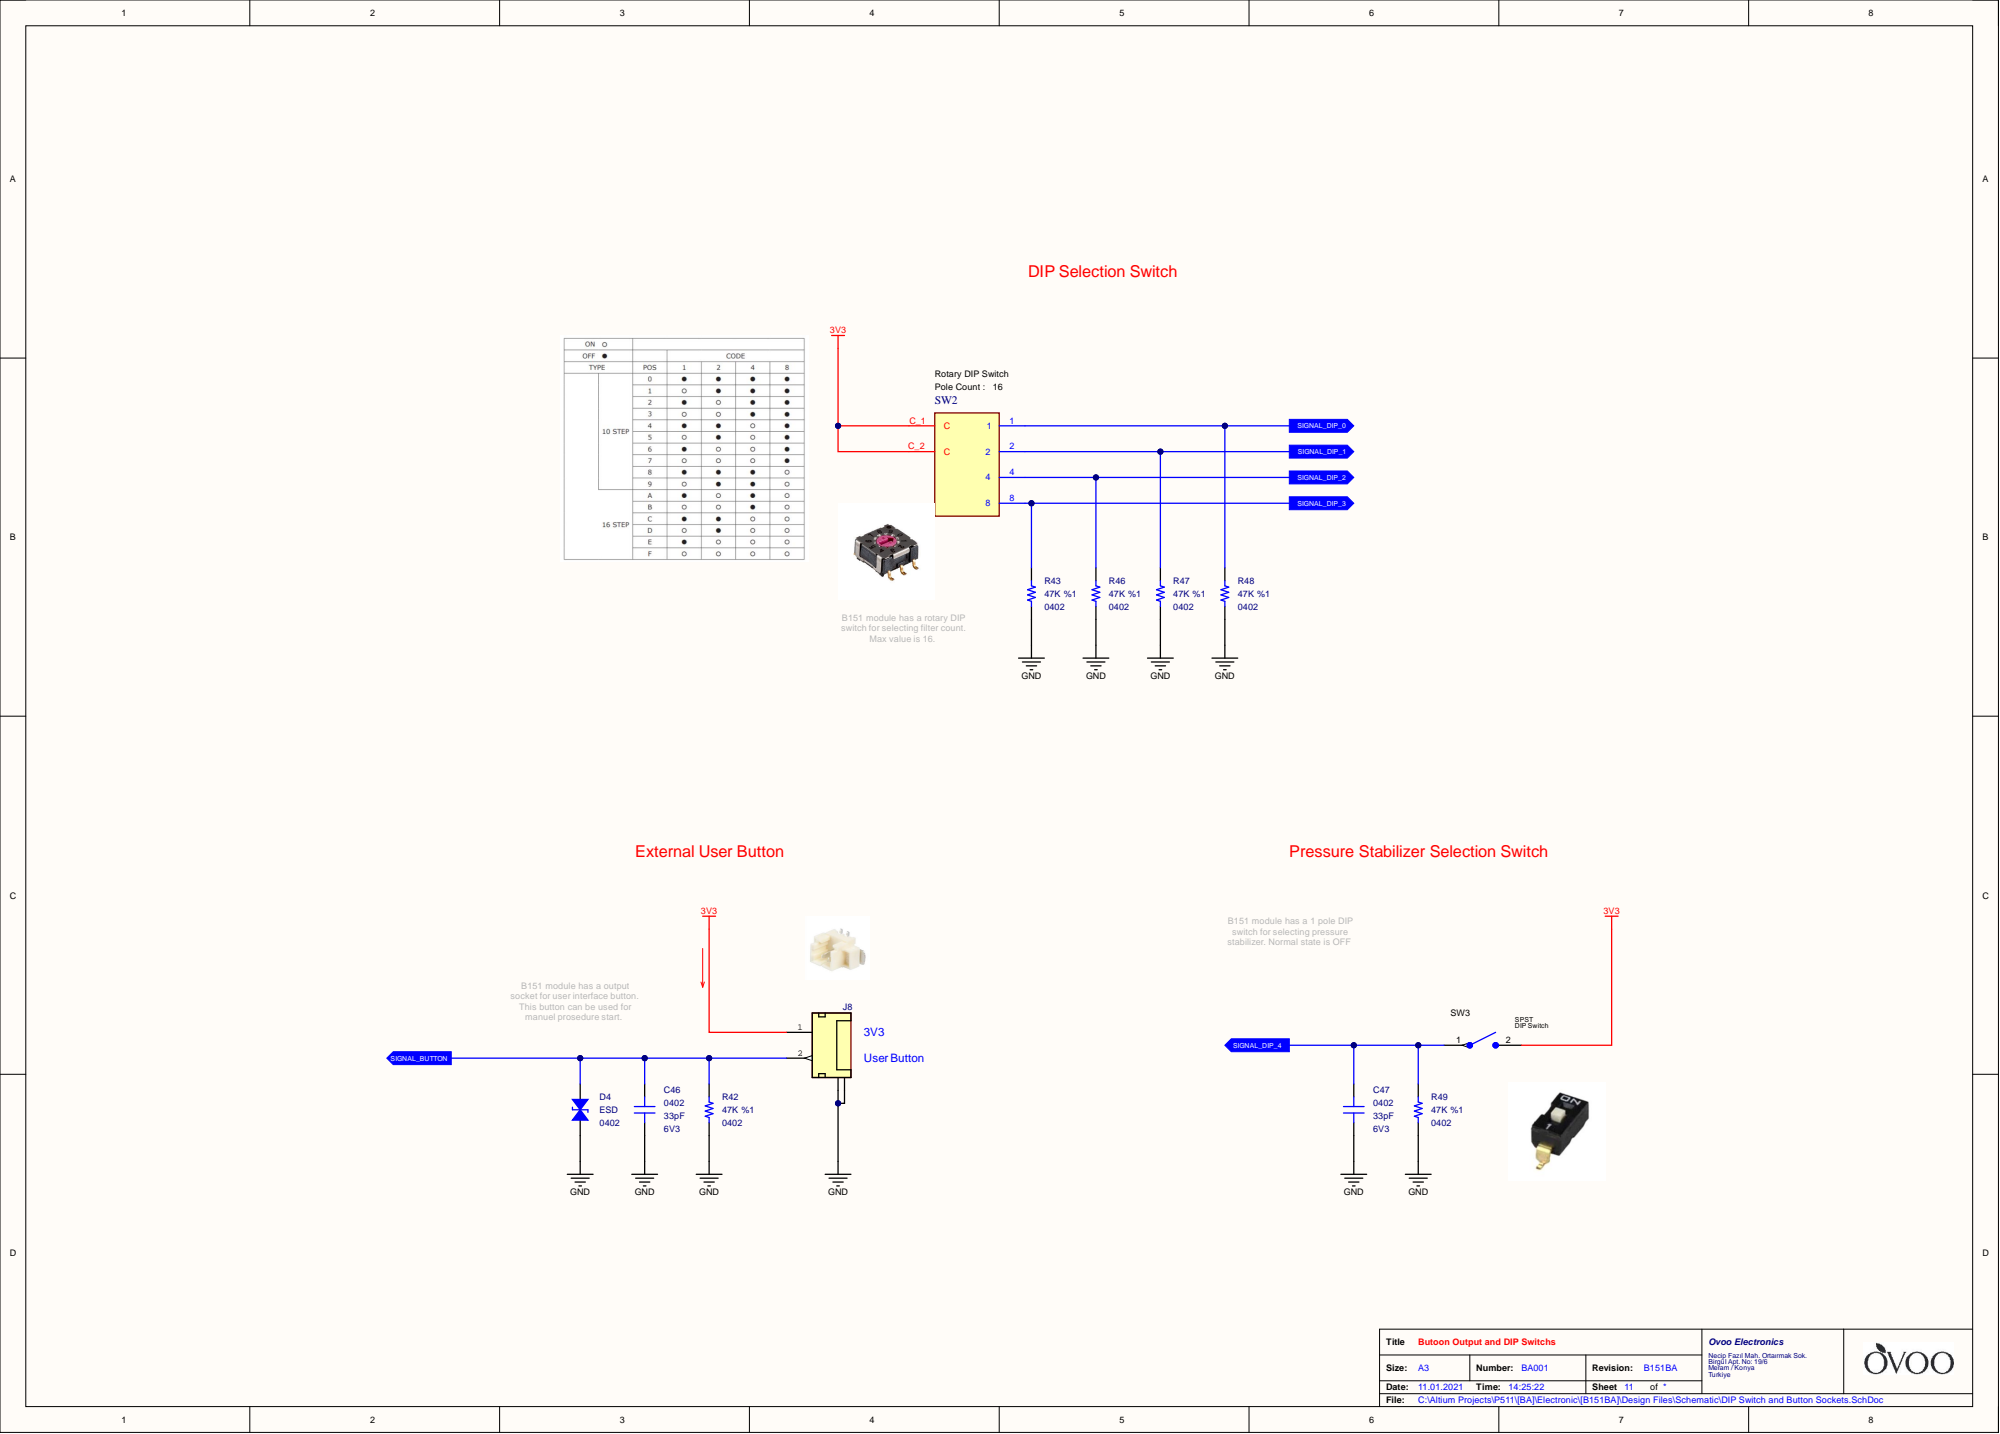
[picture p276: page 11]

B151 module has a rotary DIP
switch for selecting filter count.

Pressure Stabilizer Selection Switch

B151 module has a 1 pole DIP
switch for selecting pressure
stabilizer. Normal state is OFF

B151 module has a output
socket for user interface button.
This button can be used for
manuel prosedure start.

Butoon Output and DIP Switchs

Necip Fazıl Mah. Ortaırmak Sok. Birgül Apt. No: 19/6 Meram / Konya Turkiye

C:\Altium Projects\P511\[BA]\Electronic\[B151BA]\Design Files\Schematic\DIP Switch and Button Sockets.SchDoc

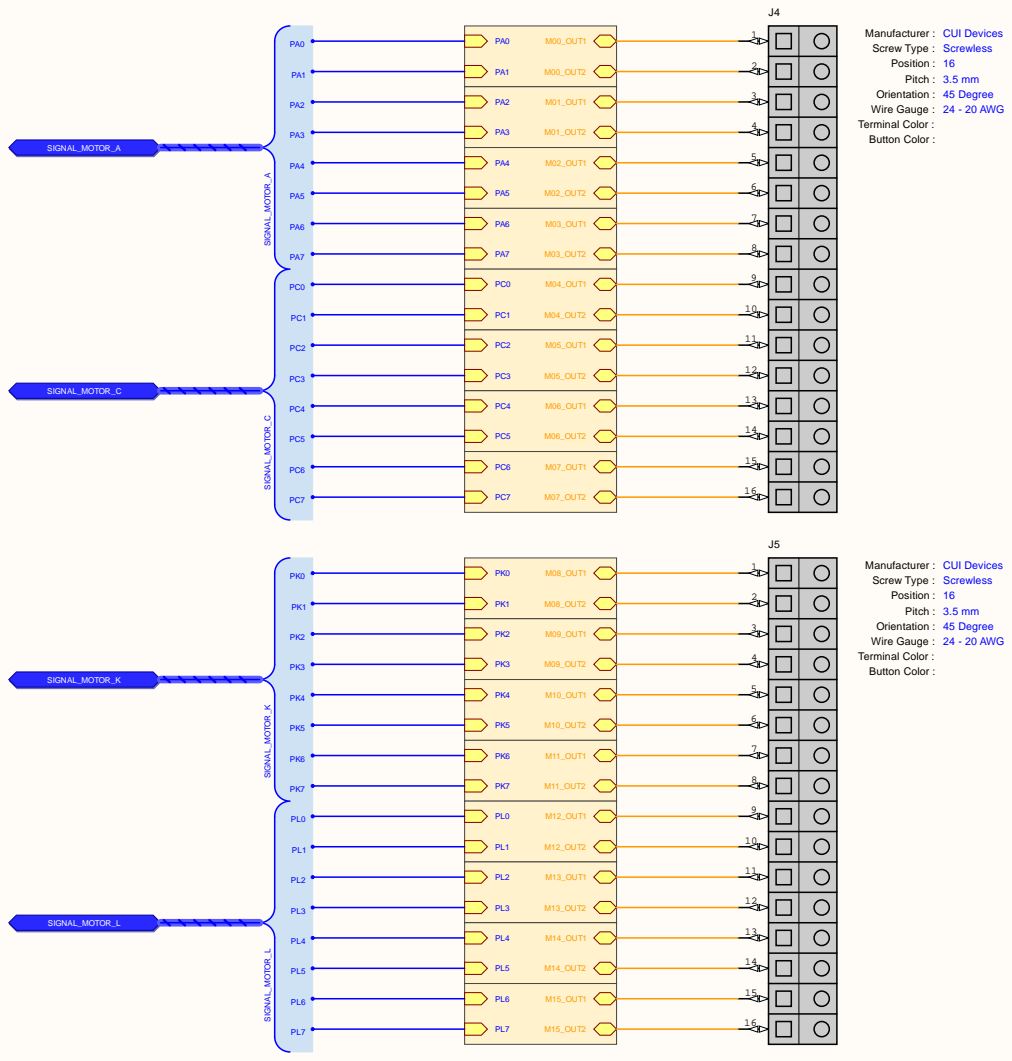
[picture p277: page 12]

Necip Fazıl Mah. Ortaırmak Sok. Birgül Apt. No: 19/6 Meram / Konya Turkiye

C:\Altium Projects\P511\[BA]\Electronic\[B151BA]\Design Files\Schematic\Motor Drivers.SchDoc

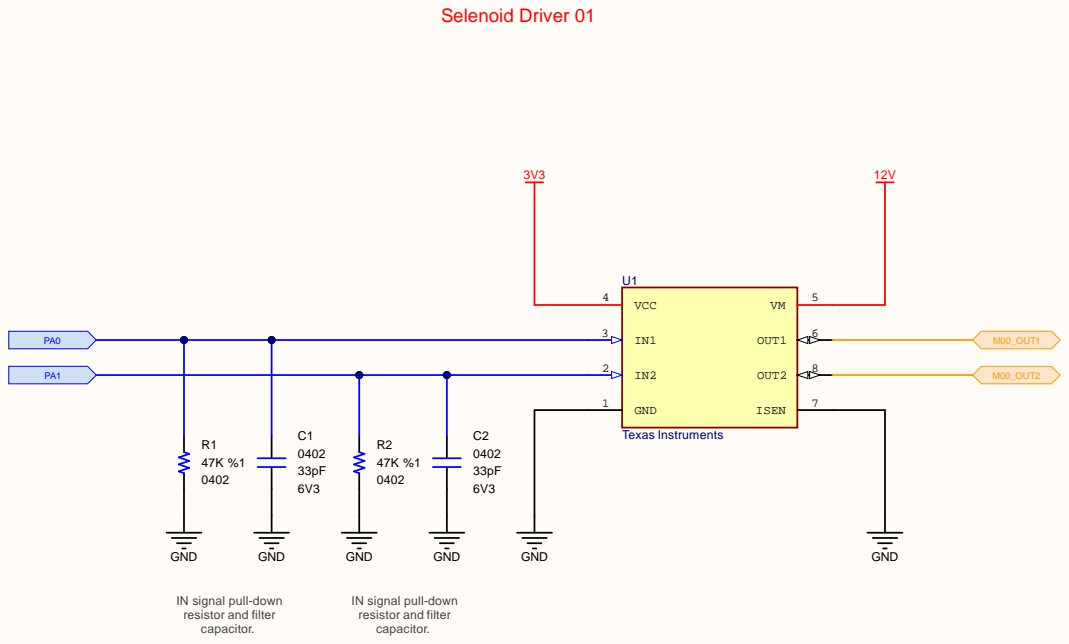
[picture p278: page 13]

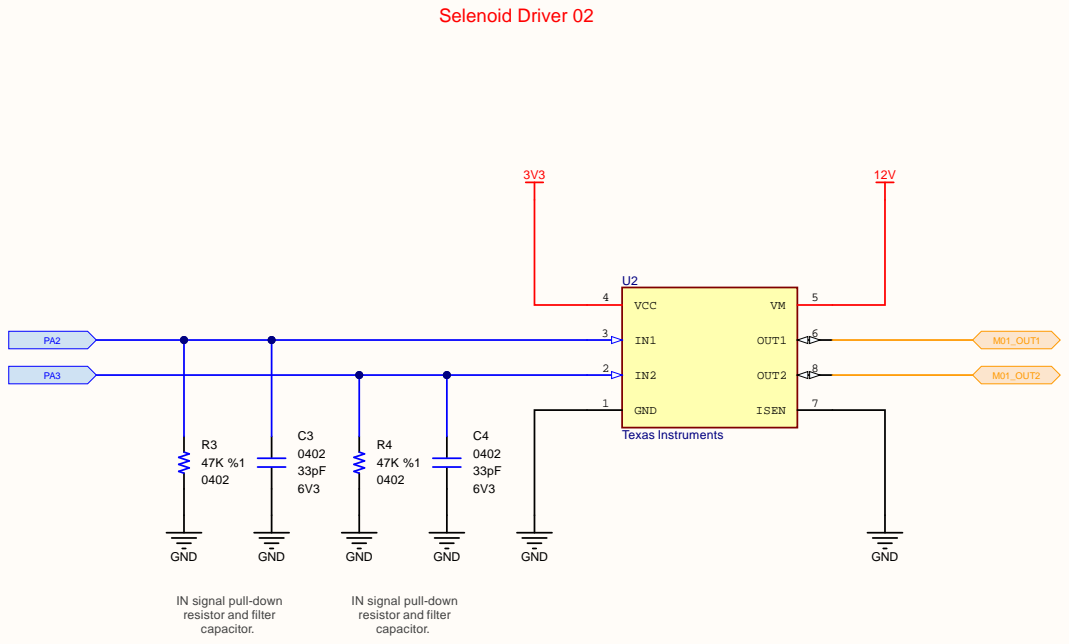
[picture p279: page 14]

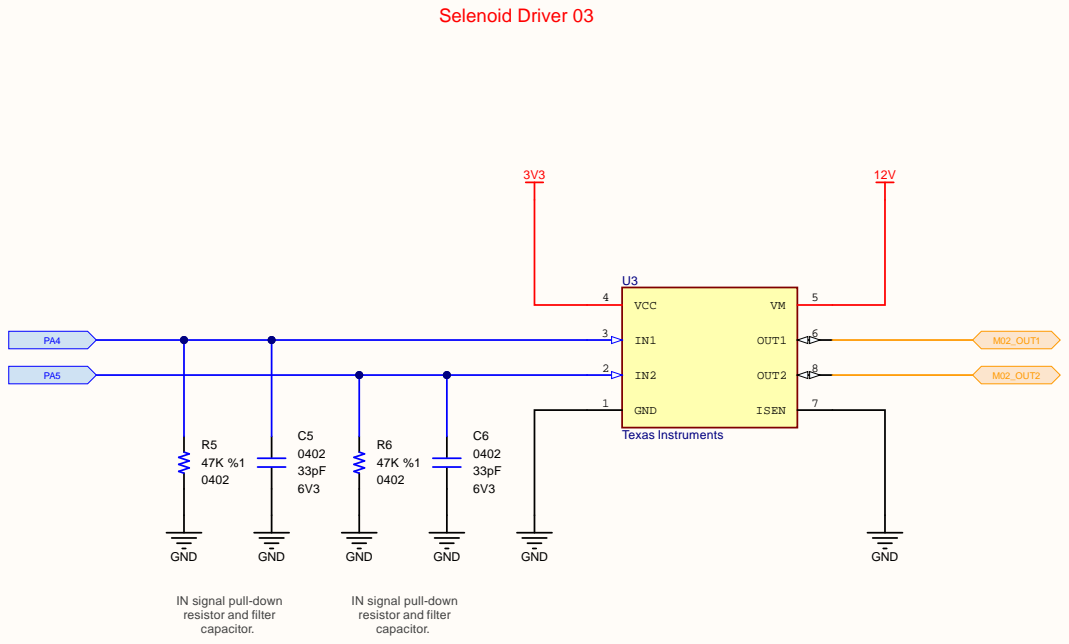
[picture p280: page 15]

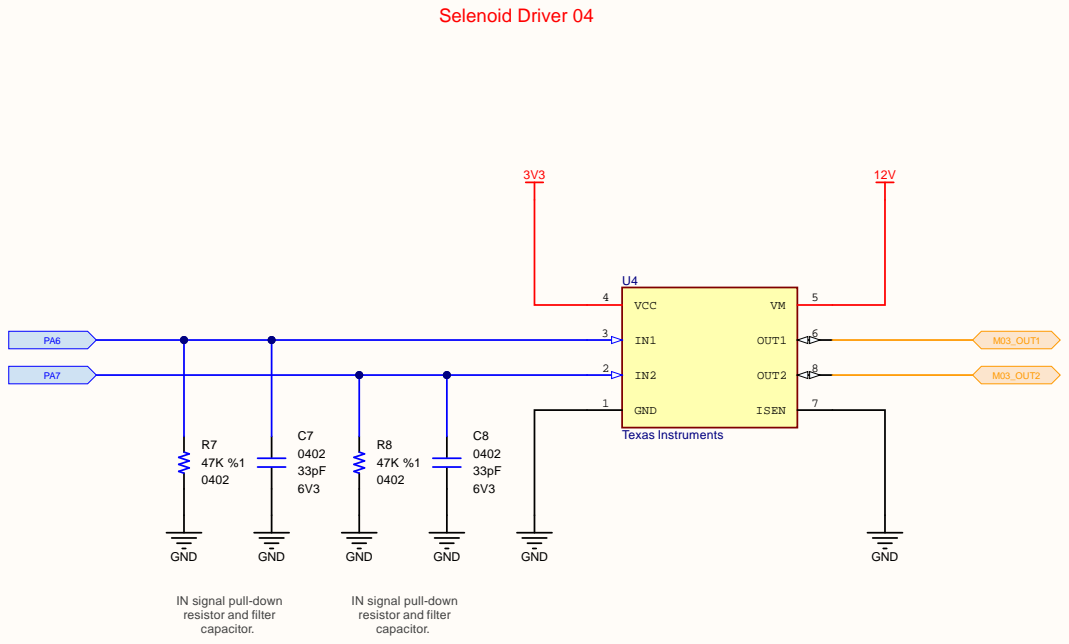
[picture p281: page 16]

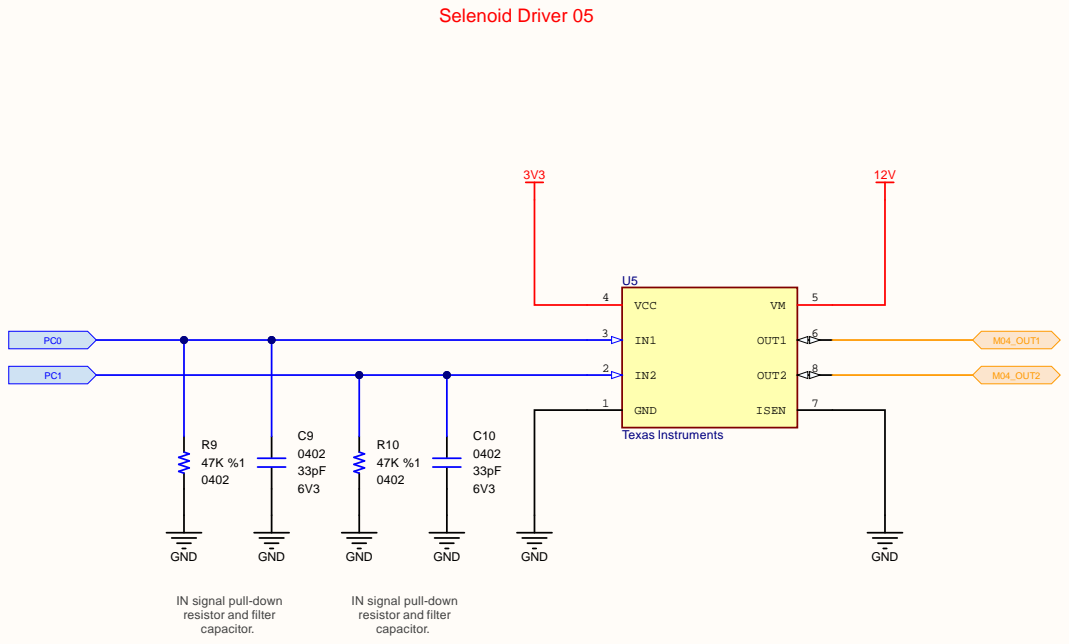
[picture p282: page 17]

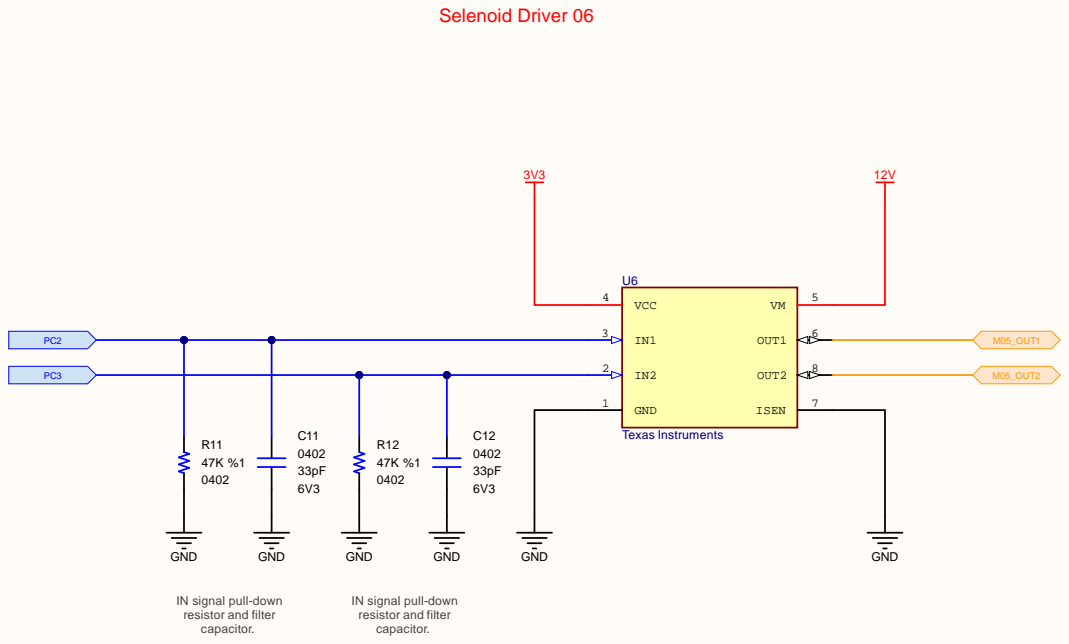
[picture p283: page 18]

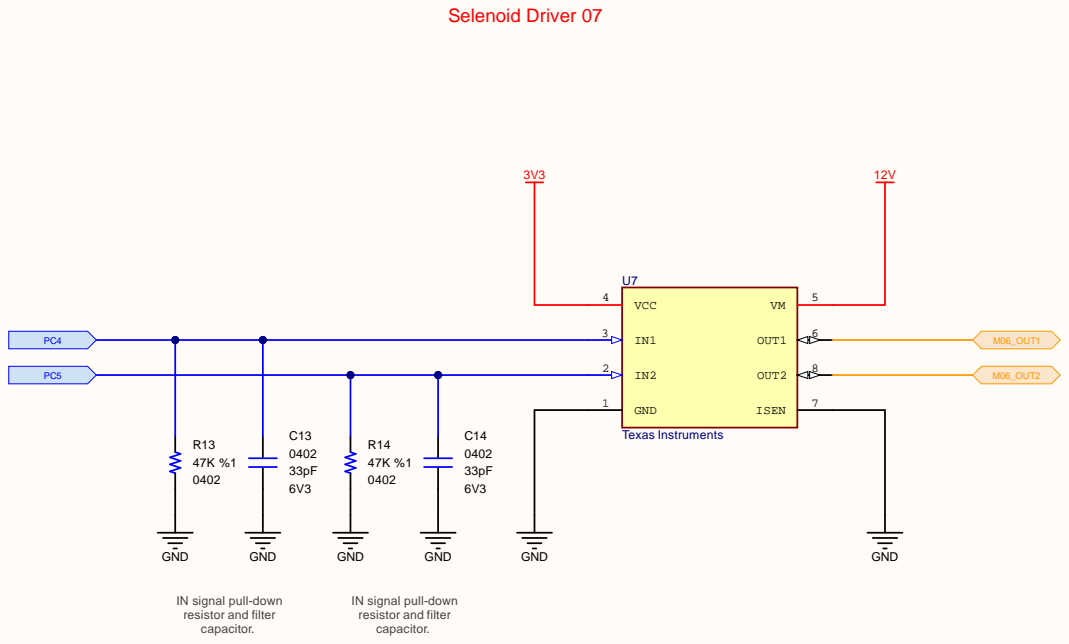
[picture p284: page 19]

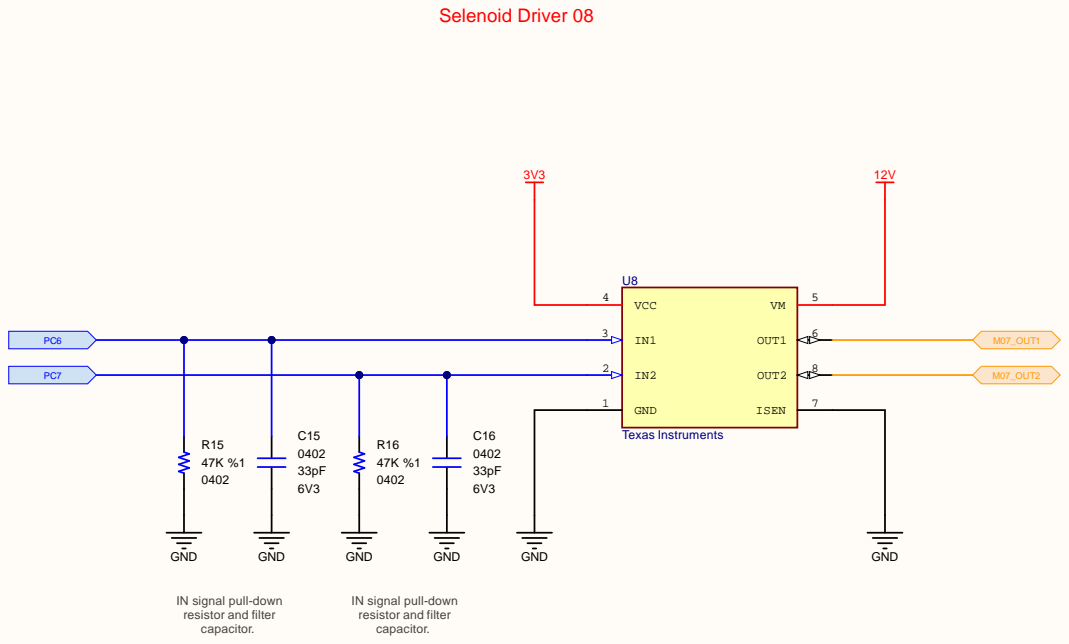
[picture p285: page 20]

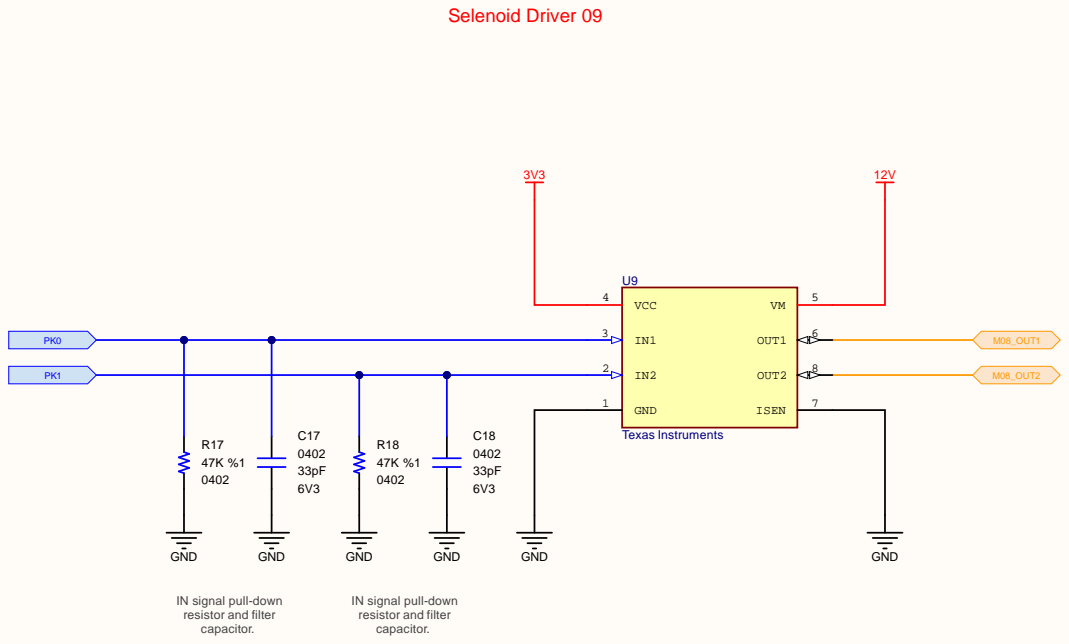
[picture p286: page 21]

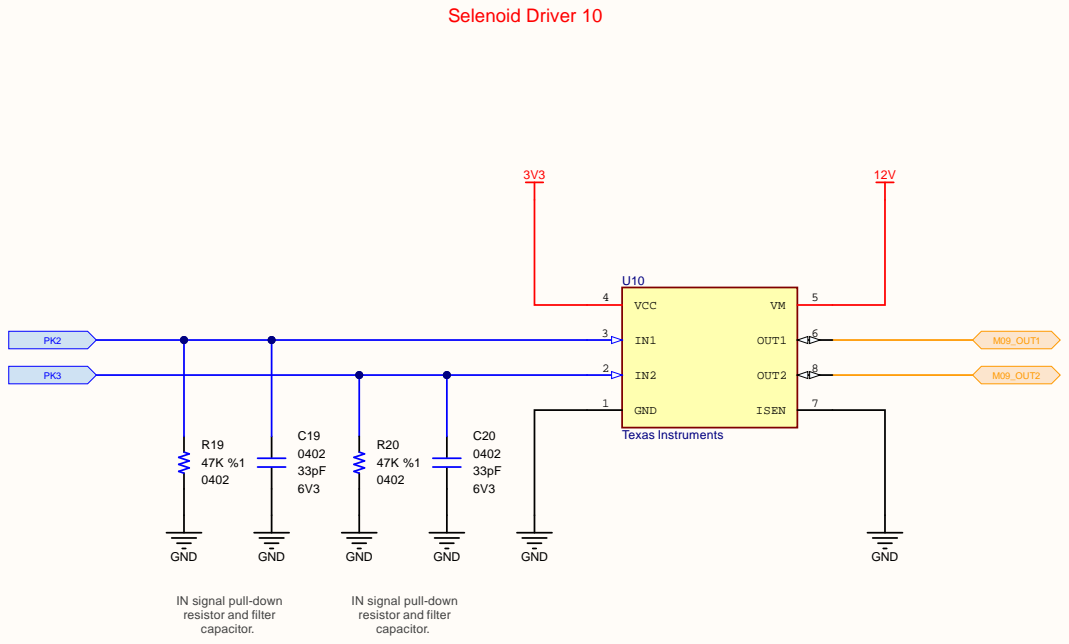
[picture p287: page 22]

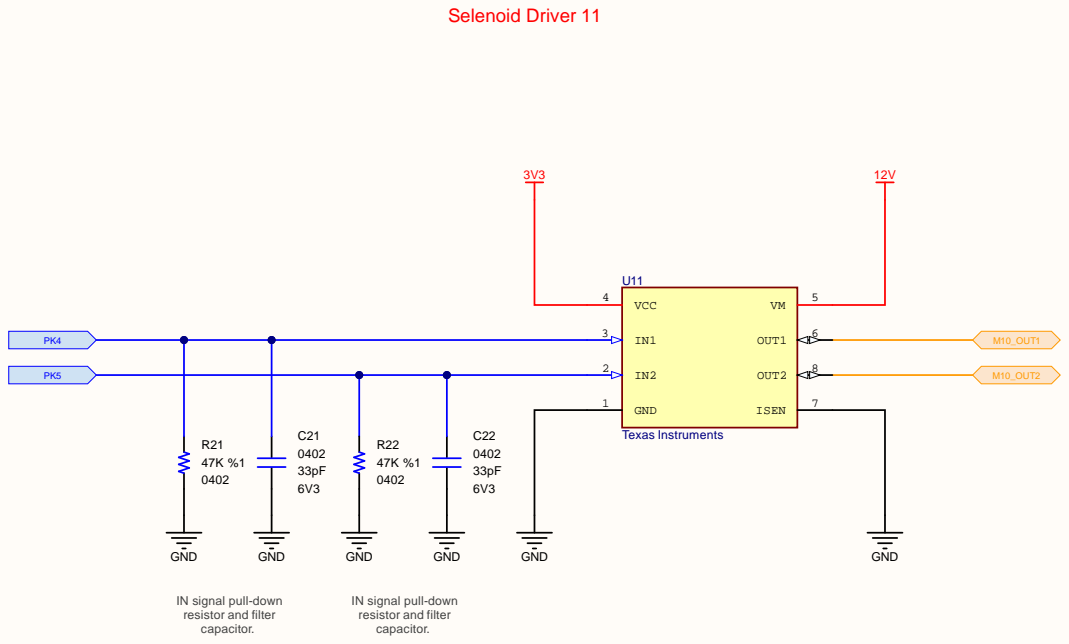
[picture p288: page 23]

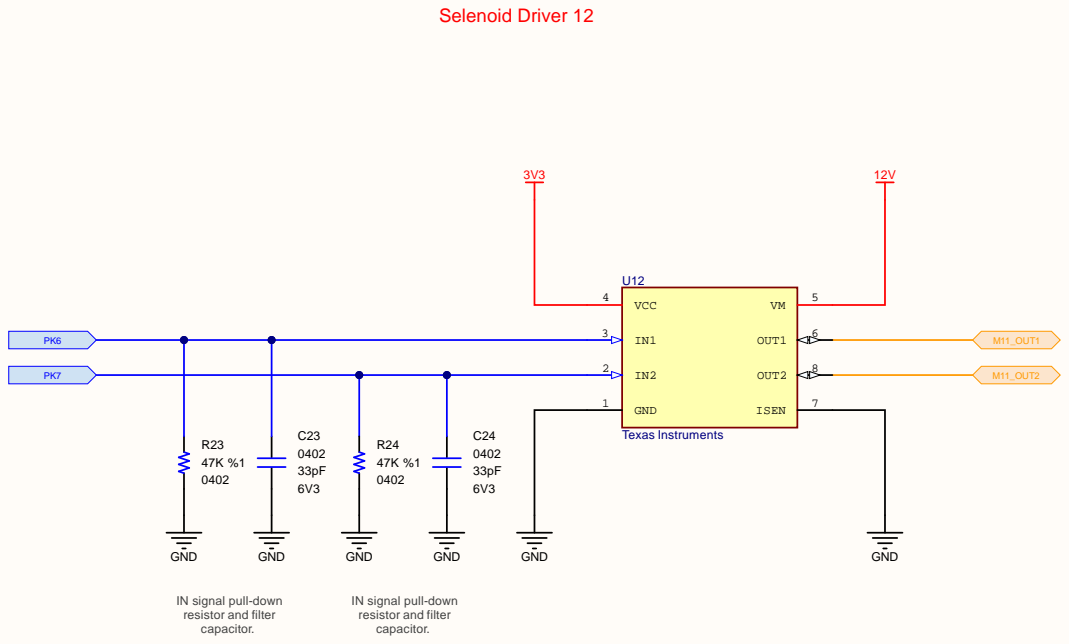
[picture p289: page 24]

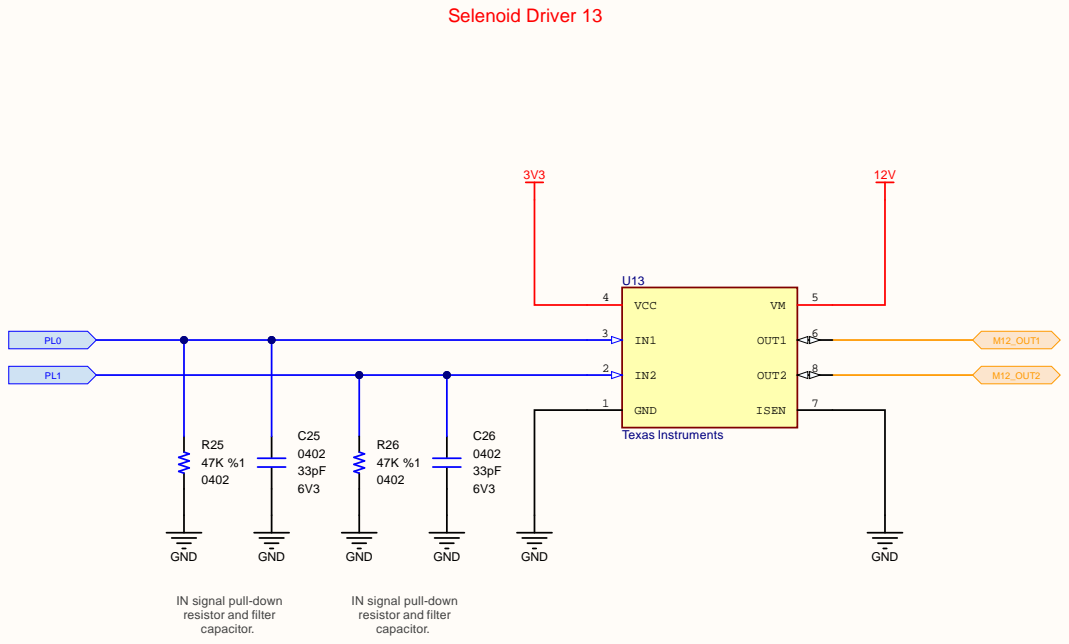
[picture p290: page 25]

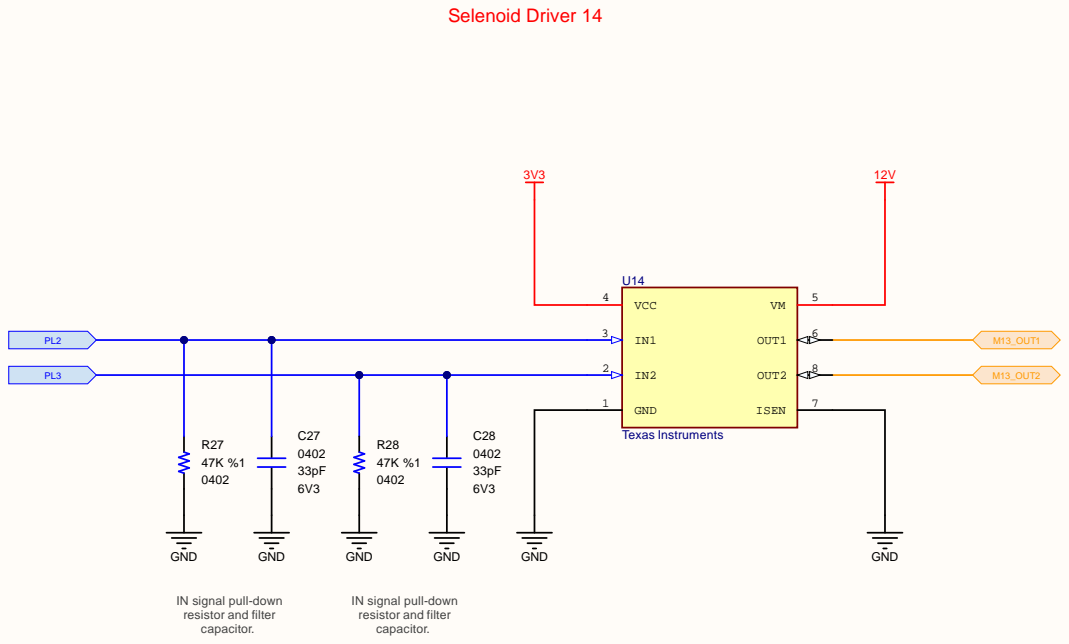
[picture p291: page 26]

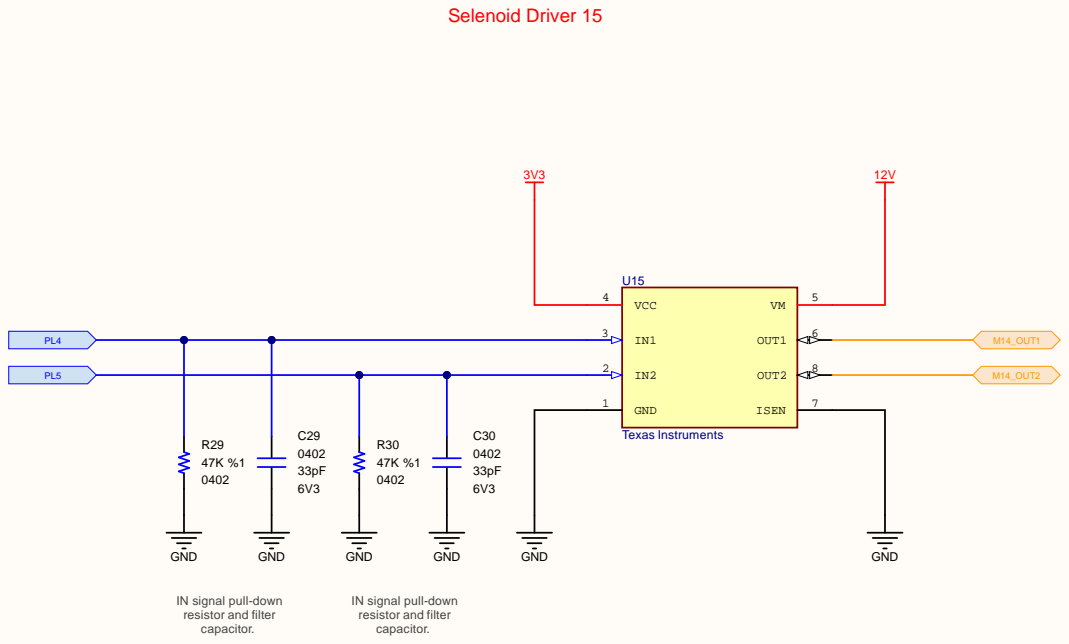
[picture p292: page 27]

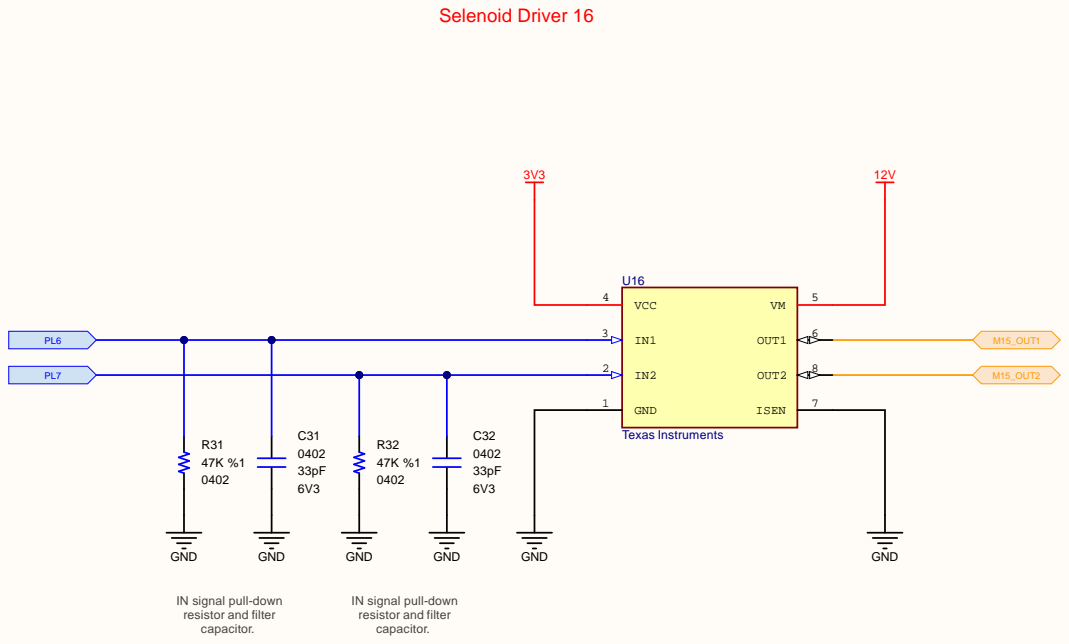
[picture p293: page 28]
