akkoyun/B100/[AA]/Design Review/Telit/Review 6/Request Form/B151BA/B151BA Schematic/B151BA Schematic.PDF

* Add Bluetooth RTS and CTS pins to MCU.
* Add Bluetooth Boot0 and TestMode pins
selectible with 0R resistor.
* Add Bluetooth HangUp pin to MCU.
* Add Bluetooth Test points.

DIP Switch and Button Sockets

Pressure Sensor Output Sockets

Necip Fazıl Mah. Ortaırmak Sok. Birgül Apt. No: 19/6 Meram / Konya Turkiye

C:\Altium Projects\P511\[BA]\Electronic\[B151BA]\Design Files\Schematic\B151BA Block Diagram.SchDoc


C:\Altium Projects\P511\[BA]\Electronic\[B151BA]\Design Files\Schematic\Power Source.SchDoc


Sense resistor is coosed 0R01 for sensing
upto 5.12A with 156.25 uA resolution.

B151BA module have a battery
socket for 18650 LiIon battery pack.

Current sensor is a optional component. If
not want to measure current must be
connect PACK- to GND.

I2C Communication
Lines are pulled-up on
B100AA module.

Interrupt is not used.

C:\Altium Projects\P511\[BA]\Electronic\[B151BA]\Design Files\Schematic\Battery Measurement.SchDoc


PROG2 4

SEL Pin : Input type selection (Low for USB port, High for
other type of power source)

TE Pin : Enables Safety Timer when active Low.

PROG1 Pin : Fast charge current regulation setting with
PROG1 = High. Preconditioning set point for both USB port
and other type of power source. 1K = 1A charge current limit.

PROG2 Pin : USB port input current limit selection when
PROG2 = HIGH. (Low = 100 mA, High = 500 mA)

PROG3 Pin : Termination set point for power source and USB
port. Minimum charge current. 10K = 100 mA.

C:\Altium Projects\P511\[BA]\Electronic\[B151BA]\Design Files\Schematic\Battery Charger.SchDoc


BST 8

C:\Altium Projects\P511\[BA]\Electronic\[B151BA]\Design Files\Schematic\12V Boost Converter.SchDoc


B100 TX0 and TX1
pins also use for
GPIO pin (PE0, PE1
and PD3)

A R T | RXD1

C:\Altium Projects\P511\[BA]\Electronic\[B151BA]\Design Files\Schematic\B100 Plug Socket.SchDoc


Analog Pressure Sensor Output Sockets

Pressure Sensor Output Sockets

C:\Altium Projects\P511\[BA]\Electronic\[B151BA]\Design Files\Schematic\Pressure Sensor Output Sockets.SchDoc


C:\Altium Projects\P511\[BA]\Electronic\[B151BA]\Design Files\Schematic\BlueTooth Module.SchDoc


C:\Altium Projects\P511\[BA]\Electronic\[B151BA]\Design Files\Schematic\External SIM Tray.SchDoc


B151 module has a output
socket for user interface button.
This button can be used for

2 | ON/OFF 3

GND 2

LCD enable signal
pull-down resistor and
filter capacitor.

The input of the PFET
(power switch) is 5V. The
output of PFET is VLCD.

TCA9517 is enabled
via LCD En signal.

C:\Altium Projects\P511\[BA]\Electronic\[B151BA]\Design Files\Schematic\LCD Output Socket.SchDoc


B151 module has a rotary DIP
switch for selecting filter count.

B151 module has a 1 pole DIP
switch for selecting pressure
stabilizer. Normal state is OFF

B151 module has a output
socket for user interface button.
This button can be used for
manuel prosedure start.

Butoon Output and DIP Switchs

C:\Altium Projects\P511\[BA]\Electronic\[B151BA]\Design Files\Schematic\DIP Switch and Button Sockets.SchDoc


C:\Altium Projects\P511\[BA]\Electronic\[B151BA]\Design Files\Schematic\Motor Drivers.SchDoc


IN signal pull-down
resistor and filter
capacitor.

C:\Altium Projects\P511\[BA]\Electronic\[B151BA]\Design Files\Schematic\Selenoid 00 Driver.SchDoc


IN signal pull-down
resistor and filter
capacitor.

C:\Altium Projects\P511\[BA]\Electronic\[B151BA]\Design Files\Schematic\Selenoid 01 Driver.SchDoc


IN signal pull-down
resistor and filter
capacitor.

C:\Altium Projects\P511\[BA]\Electronic\[B151BA]\Design Files\Schematic\Selenoid 02 Driver.SchDoc


IN signal pull-down
resistor and filter
capacitor.

C:\Altium Projects\P511\[BA]\Electronic\[B151BA]\Design Files\Schematic\Selenoid 03 Driver.SchDoc


IN signal pull-down
resistor and filter
capacitor.

C:\Altium Projects\P511\[BA]\Electronic\[B151BA]\Design Files\Schematic\Selenoid 04 Driver.SchDoc


IN signal pull-down
resistor and filter
capacitor.

C:\Altium Projects\P511\[BA]\Electronic\[B151BA]\Design Files\Schematic\Selenoid 05 Driver.SchDoc


IN signal pull-down
resistor and filter
capacitor.

C:\Altium Projects\P511\[BA]\Electronic\[B151BA]\Design Files\Schematic\Selenoid 06 Driver.SchDoc


IN signal pull-down
resistor and filter
capacitor.

C:\Altium Projects\P511\[BA]\Electronic\[B151BA]\Design Files\Schematic\Selenoid 07 Driver.SchDoc


IN signal pull-down
resistor and filter
capacitor.

C:\Altium Projects\P511\[BA]\Electronic\[B151BA]\Design Files\Schematic\Selenoid 08 Driver.SchDoc


IN signal pull-down
resistor and filter
capacitor.

C:\Altium Projects\P511\[BA]\Electronic\[B151BA]\Design Files\Schematic\Selenoid 09 Driver.SchDoc


IN signal pull-down
resistor and filter
capacitor.

C:\Altium Projects\P511\[BA]\Electronic\[B151BA]\Design Files\Schematic\Selenoid 10 Driver.SchDoc


IN signal pull-down
resistor and filter
capacitor.

C:\Altium Projects\P511\[BA]\Electronic\[B151BA]\Design Files\Schematic\Selenoid 11 Driver.SchDoc


IN signal pull-down
resistor and filter
capacitor.

C:\Altium Projects\P511\[BA]\Electronic\[B151BA]\Design Files\Schematic\Selenoid 12 Driver.SchDoc


IN signal pull-down
resistor and filter
capacitor.

C:\Altium Projects\P511\[BA]\Electronic\[B151BA]\Design Files\Schematic\Selenoid 13 Driver.SchDoc


IN signal pull-down
resistor and filter
capacitor.

C:\Altium Projects\P511\[BA]\Electronic\[B151BA]\Design Files\Schematic\Selenoid 14 Driver.SchDoc


IN signal pull-down
resistor and filter
capacitor.

C:\Altium Projects\P511\[BA]\Electronic\[B151BA]\Design Files\Schematic\Selenoid 15 Driver.SchDoc


C:\Altium Projects\P511\[BA]\Electronic\[B151BA]\Design Files\Schematic\BlueMod+S50 Antenna.SchDoc


C:\Altium Projects\P511\[BA]\Electronic\[B151BA]\Design Files\Schematic\BlueMod+S50 Communicatiın.SchDoc


C:\Altium Projects\P511\[BA]\Electronic\[B151BA]\Design Files\Schematic\BlueMod+S50 GPIO.SchDoc


BlueMod+S50 Module Power Supply

C:\Altium Projects\P511\[BA]\Electronic\[B151BA]\Design Files\Schematic\BlueMod+S50 Power Supply.SchDoc


Test Mode - Boot0
LOW / LOW : Test Mode
LOW / HIGH : DTM (19200, 8N1)
HIGH / LOW : Firmware (115200, 8N1)
HIGH / HIGH : Bootloader

C:\Altium Projects\P511\[BA]\Electronic\[B151BA]\Design Files\Schematic\BlueMod+S50.SchDoc
