akkoyun/B100/[AA]/Documentation/Analyse/5V BuckBoost Startup Analyse.pdf

## WEBENCH ® Design Report

Copyright © 2021, Texas Instruments Incorporated; ti.com/webench; WEBENCH®; Design : 32 TPS63802DLAR TPS63802DLAR 2.2V-5.5V to 5.00V @ 0.5A; VinMin = 2.2V VinMax = 5.5V Vout = 5.0V Iout = 0.5A; Device = TPS63802DLAR Topology = Buck_Boost Created = 2021-01-05 01:02:19.036 BOM Cost = $1.28 BOM Count = 8 Total Pd = 0.25W; Vout = 5.0V Iout = 0.5A; Cin 22.0 µF 1.0 mOhm; Rpg 100.0 kOhm 63.0 mW; TPS63802DLA; MODE; AGND; VOUT; GND; VIN; Rfbb 91.0 kOhm 100.0 mW; Rfbt 806.0 kOhm 63.0 mW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

Design Report TPS63802DLAR : TPS63802DLAR 2.2V-5.5V to 5.00V @ 0.5A January 5, 2021 01:13:37 GMT-08:00

Design; Copyright © 2021, Texas Instruments Incorporated; ti.com/webench; L Ipp; 0.50 Output Current (A); L Ipp(A); Ipp percentage; Ipp percentage(%); Vout p- p(V); Duty Cycle(%); Efficiency(%)

Vin= 2.2V Vin= 3.85V Vin= 5.5V
Vout p- p

Duty Cycle

Efficiency

IC Tj(degC)

Copyright © 2021, Texas Instruments Incorporated; ti.com/webench; Cin Pd; 0.50 Output Current (A); Cin Pd(W); Cin IRMS; Cin IRMS(A); Iin Avg(A); Pout; Pout(W); IC Ipk; IC Ipk(A); Cout IRMS(A)

Vin= 2.2V Vin= 3.85V Vin= 5.5V
Iin Avg

Cout IRMS

Copyright © 2021, Texas Instruments Incorporated; ti.com/webench; Cout Pd; 0.50 Output Current (A); Cout Pd(W); Total Pd; Total Pd(W); 3.16E- 1 Output Current (A); Efficiency(%); Operating Values; Name; Value; Category; Description; 1. Cin IRMS; Capacitor; Input capacitor RMS ripple current; 2. Cin Pd; Input capacitor power dissipation; 3. Cout IRMS; Output capacitor RMS ripple current; 4. Cout Pd; Output capacitor power dissipation; 5. IC Ipk; Peak switch current in IC; IC power dissipation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

Vin= 2.2V Vin= 3.85V Vin= 5.5V

Efficiency (Log- Scale)

Copyright © 2021, Texas Instruments Incorporated | 5 | ti.com/webench
# | Name | Value | Category | Description

11. Ipp percentage | 842.155 % | Inductor | Inductor ripple current percentage (with respect to average inductor
| | | | current)
12. L Pd | 59.822 mW | Inductor | Inductor power dissipation
13. Cin Pd | 4.32 mW | Power | Input capacitor power dissipation
14. Cout Pd | 3.72 mW | Power | Output capacitor power dissipation
15. IC Pd | 182.76 mW | Power | IC power dissipation
16. L Pd | 59.822 mW | Power | Inductor power dissipation
17. Total Pd | 250.64 mW | Power | Total Power Dissipation
18. BOM Count | 8 | System
| | | Information | Total Design BOM count
19. Duty Cycle | 12.329 % | System
| | | Information | Duty cycle
20. Efficiency | 90.888 % | System
| | | Information | Steady state efficiency
21. FootPrint | 50.0 mm² | System
| | | Information | Total Foot Print Area of BOM components
22. Frequency | 110.102 kHz | System
| | | Information | Switching frequency
23. Iout | 500.0 mA | System
| | | Information | Iout operating point
24. L Ipp | 1.06 A | System
| | | Information | Peak-to-peak inductor ripple current
25. Mode | PFM | System
| | | Information | Conduction Mode
26. Pout | 2.5 W | System
| | | Information | Total output power
27. Total BOM | $1.28 | System
| | | Information | Total BOM Cost
28. Vin | 2.2 V | System
| | | Information | Vin operating point
29. Vout | 5.0 V | System
| | | Information | Operational Output Voltage
30. Vout Actual | 4.929 V | System
| | | Information | Vout Actual calculated based on selected voltage divider resistors
31. Vout Tolerance | 2.833 % | System
| | | Information | Vout Tolerance based on IC Tolerance (no load) and voltage divider resistors if applicable
32. Vout p-p | 458.788 mV | System
| | | Information | Peak-to-peak output ripple voltage

## Design Inputs

Name | Value | Description
| Iout | | 500.0 m | Maximum Output Current
VinMax | 5.5 | Maximum input voltage
VinMin | 2.2 | Minimum input voltage
Vout | 5.0 | Output Voltage
| base_pn | | TPS63802 | Base Product Number
source | DC | Input Source Type
Ta | 30.0 | Ambient temperature


Copyright © 2021, Texas Instruments Incorporated | 6 | ti.com/webench

## Assembly

## Component Testing

Some published data on components in datasheets such as Capacitor ESR and Inductor DC resistance is based on conservative values that will guarantee that the components always exceed the specification. For design purposes it is usually better to work with typical values. Since this data is not always available it is a good practice to measure the Capacitance and ESR values of Cin and Cout, and the inductance and DC resistance of L1 before assembly of the board. Any large discrepancies in values should be electrically simulated in WEBENCH to check for instabilities and thermally simulated in WebTHERM to make sure critical temperatures are not exceeded.

## Soldering Component to Board

If board assembly is done in house it is best to tack down one terminal of a component on the board then solder the other terminal. For surface mount parts with large tabs, such as the DPAK, the tab on the back of the package should be pre-tinned with solder, then tacked into place by one of the pins. To solder the tab town to the board place the iron down on the board while resting against the tab, heating both surfaces simultaneously. Apply light pressure to the top of the plastic case until the solder flows around the part and the part is flush with the PCB. If the solder is not flowing around the board you may need a higher wattage iron (generally 25W to 30W is enough).

## Initial Startup of Circuit

It is best to initially power up the board by setting the input supply voltage to the lowest operating input voltage 2.2V and set the input supply's current limit to zero. With the input supply off connect up the input supply to Vin and GND. Connect a digital volt meter and a load if needed to set the minimum Iout of the design from Vout and GND. Turn on the input supply and slowly turn up the current limit on the input supply. If the voltage starts to rise on the input supply continue increasing the input supply current limit while watching the output voltage. If the current increases on the input supply, but the voltage remains near zero, then there may be a short or a component misplaced on the board. Power down the board and visually inspect for solder bridges and recheck the diode and capacitor polarities. Once the power supply circuit is operational then more extensive testing may include full load testing, transient load and line tests to compare with simulation results.

## Load Testing

The setup is the same as the initial startup, except that an additional digital voltmeter is connected between Vin and GND, a load is connected between Vout and GND and a current meter is connected in series between Vout and the load. The load must be able to handle at least rated output power + 50% ( 7.5 watts for this design). Ideally the load is supplied in the form of a variable load test unit. It can also be done in the form of suitably large power resistors. When using an oscilloscope to measure waveforms on the prototype board, the ground leads of the oscilloscope probes should be as short as possible and the area of the loop formed by the ground lead should be kept to a minimum. This will help reduce ground lead inductance and eliminate EMI noise that is not actually present in the circuit.

## WEBENCH® Electrical Simulation Report

Copyright © 2021, Texas Instruments Incorporated; ti.com/webench; Vout = 5.0V Iout = 0.5A; VOut; Iin; Cin 22.0 µF 1.0 mOhm; Vpg; IInductor; VSwitch; IOut; Rpg 100.0 kOhm 63.0 mW; VSwitch1; ICout; TPS63802DLA; MODE; AGND; VOUT; GND; VIN; Rfbb 91.0 kOhm 100.0 mW; ICin; Rfbt; 806.0 kOhm 63.0 mW; VinMin = 2.2V VinMax = 5.5V; VIn; L1 470.0 nH 38.0 mOhm; Cout 22.0 µF 3.71 mOhm Qty= 2; ILoad; Rload; Vin; Simulation Parameters; # Name Parameter Name; Description; Values; 1. Vzero1 Vmode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

Design Id = 32
sim_id = 1
Simulation Type = Startup

1. Master key : B5D4E2491D752E31[v1]
2. TPS63802 Product Folder : http://www.ti.com/product/TPS63802 : contains the data sheet and other resources.

Copyright © 2021, Texas Instruments Incorporated | 8 | ti.com/webench

Important Notice and Disclaimer

TI provides technical and reliability data (including datasheets), design resources (including reference designs), application or other design advice, web tools, safety information, and other resources AS IS and with all faults, and disclaims all warranties. These resources are intended for skilled developers designing with TI products. You are solely responsible for (1) selecting the appropriate TI products for your application, (2) designing, validating and testing your application, and (3) ensuring your application meets applicable standards, and any other safety, security, or other requirements.

These resources are subject to change without notice. TI grants you permission to use these resources only for development of an application that uses the TI products described in the resource. Other reproduction and display of these resources is prohibited. No license is granted to any other TI intellectual property right or to any third party intellectual property right. TI disclaims responsibility for, and you will fully indemnify TI and its representatives against, any claims, damages, costs, losses, and liabilities arising out of your use of these resources.

Providing these resources does not expand or otherwise alter TI's applicable Terms of Sale or other applicable terms available either on ti.com or provided in conjunction with TI products.
