akkoyun/B100/[AA]/Design Review/Telit/Review 7/Request Form/B100AA/B100AA Draftsman.PDF

View from Top side (Scale 1:1)
