akkoyun/B100/[AA]/Design Review/Telit/Review 7/Request Form/B151BA/B151BA Draftsman.PDF

View from Top side (Scale 1:1)
