akkoyun/B100/[AA]/Production/Draftsman/Draftsman.PDF

View from Top side (Scale 1:1)
